vankxr/qo-100-tools/docs/combined_stencil.png

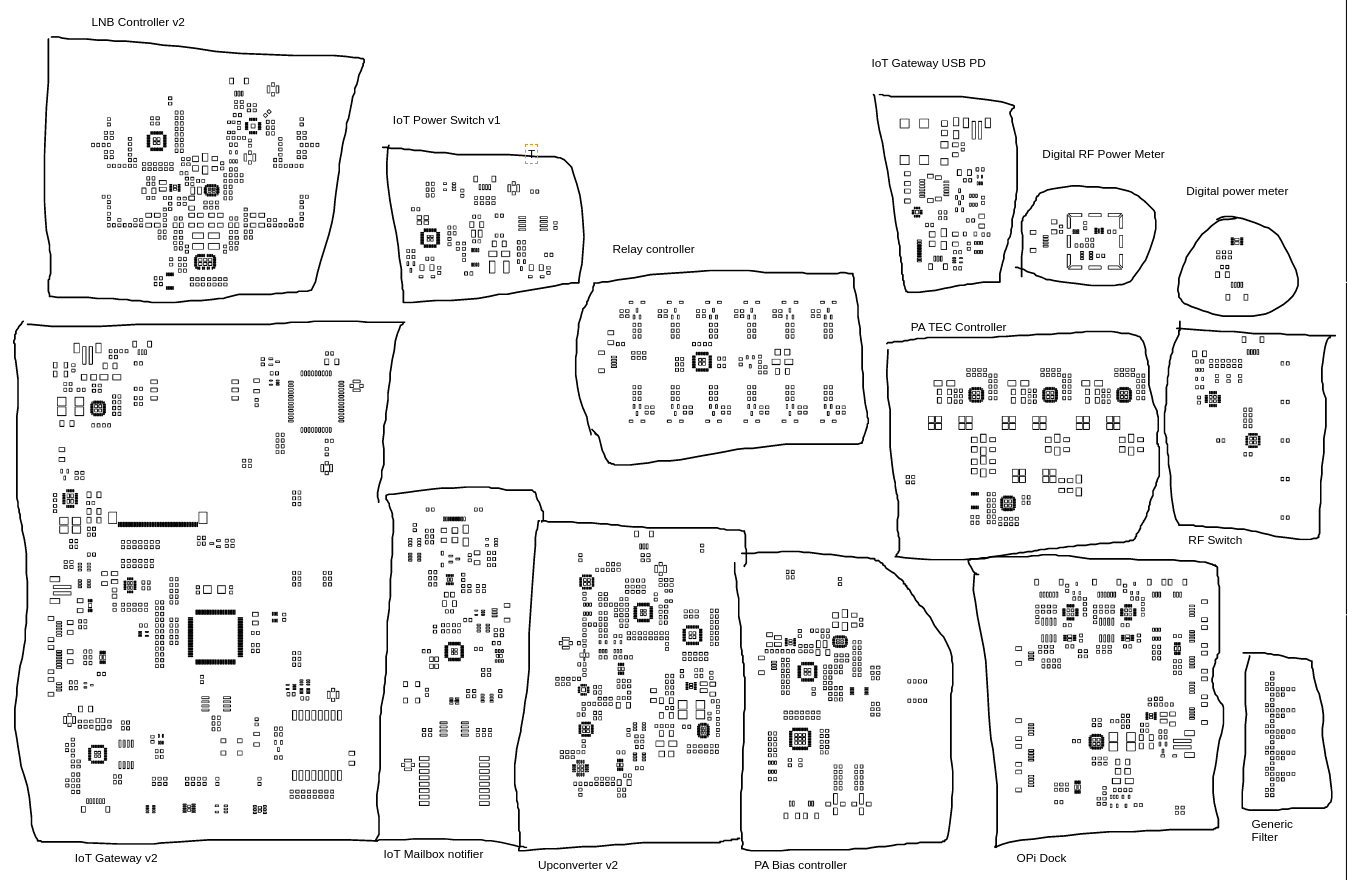
docs/combined_stencil.png
