vankxr/qo-100-tools/docs/directional-couplers/dir_cpl_2.4g_20dB_through.png

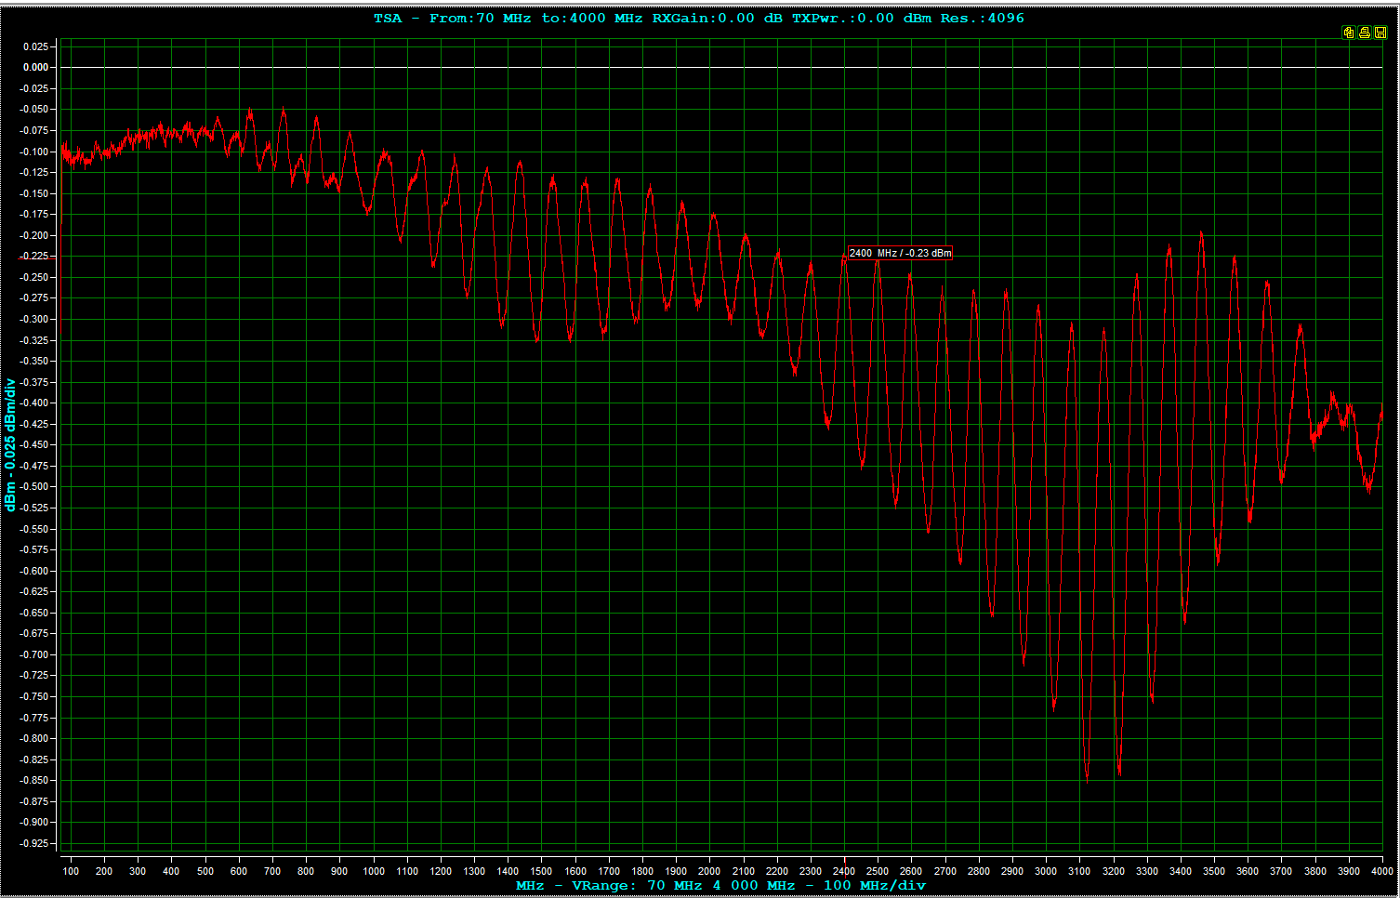
docs/directional-couplers/dir_cpl_2.4g_20dB_through.png
