vankxr/qo-100-tools/docs/directional-couplers/dir_cpl_525m_20dB_coupled.png

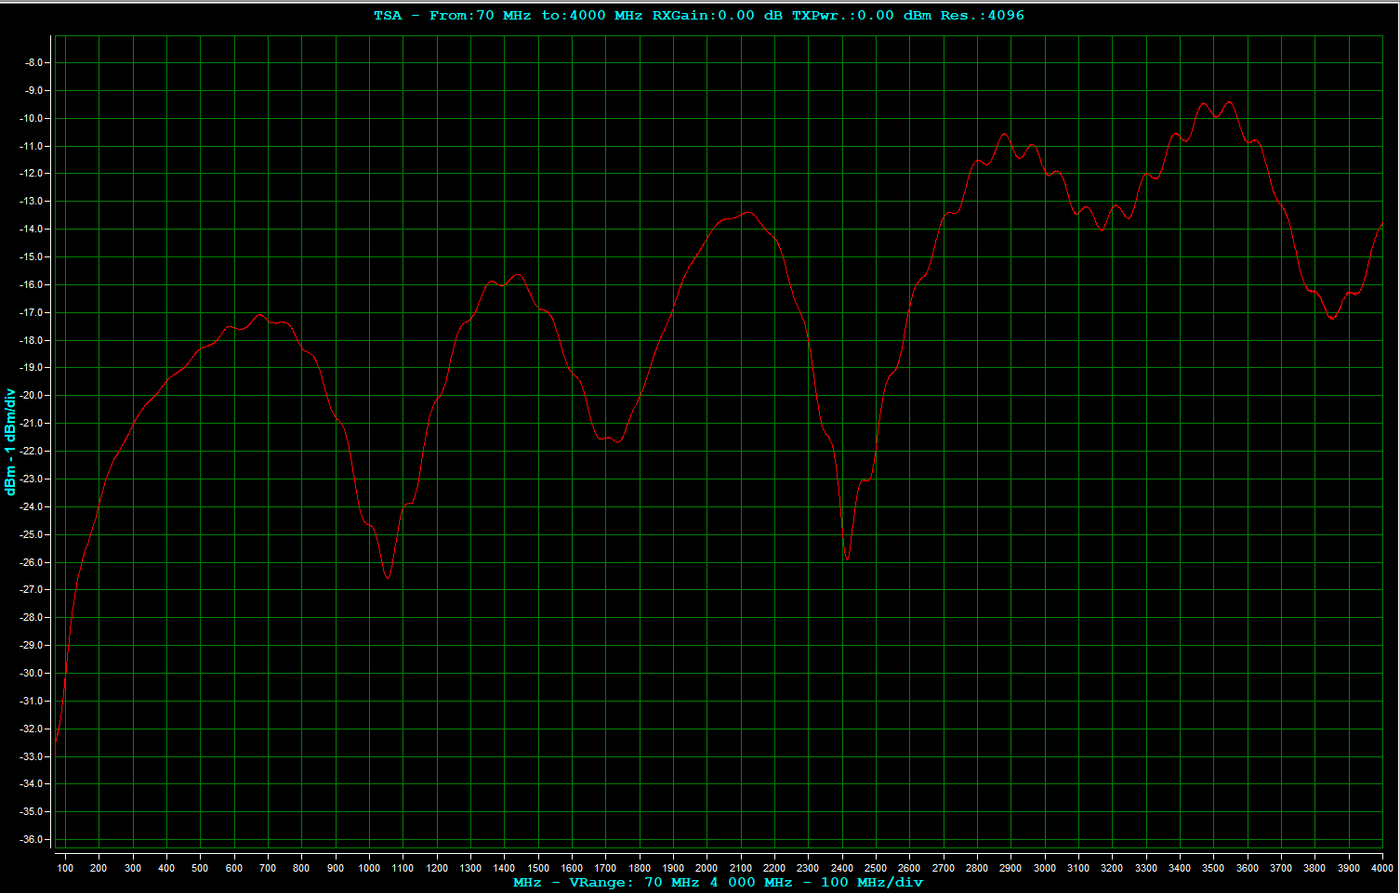
docs/directional-couplers/dir_cpl_525m_20dB_coupled.png
