vankxr/qo-100-tools/docs/f1490_devboard_deembedded.png

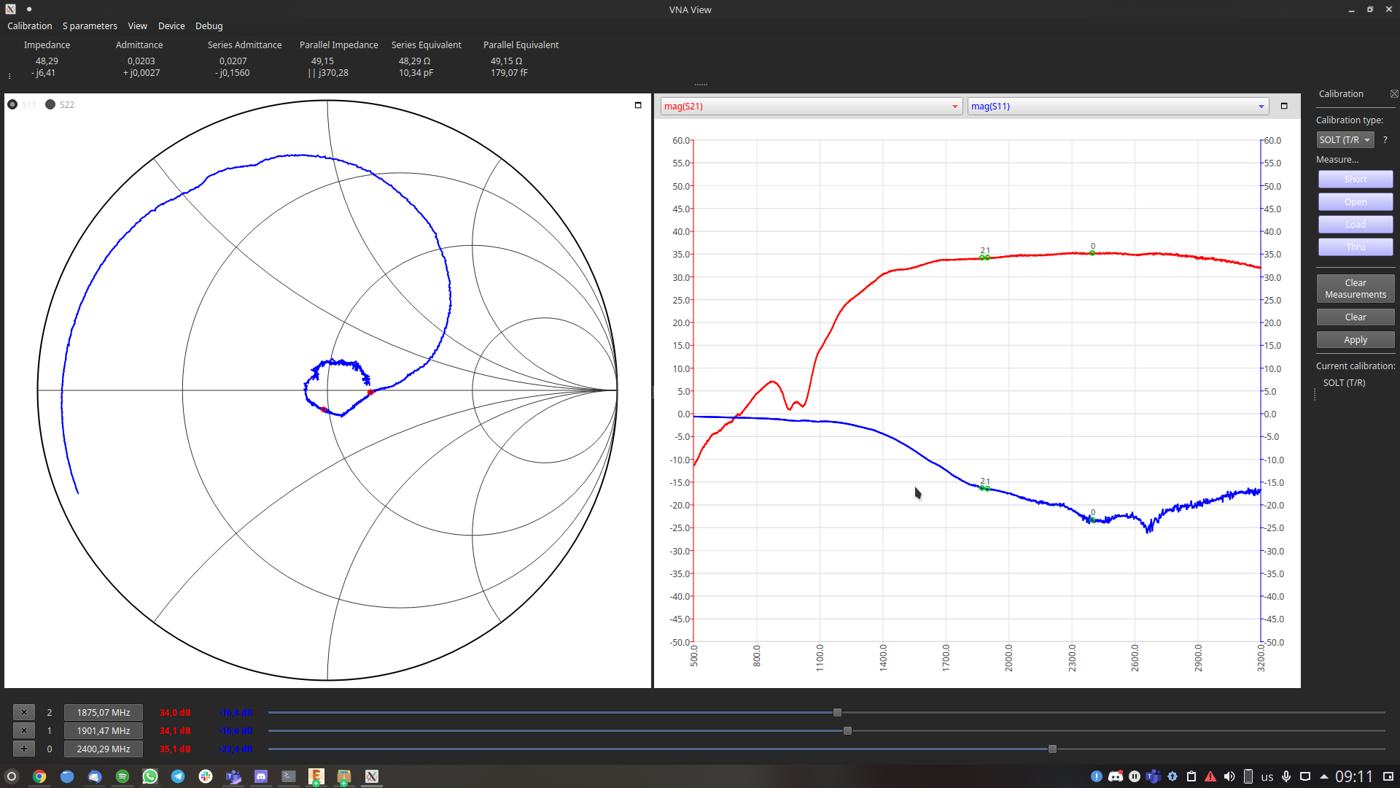
docs/f1490_devboard_deembedded.png
