vankxr/qo-100-tools/docs/ice-cone-antenna/ice_cone_no_cover.png

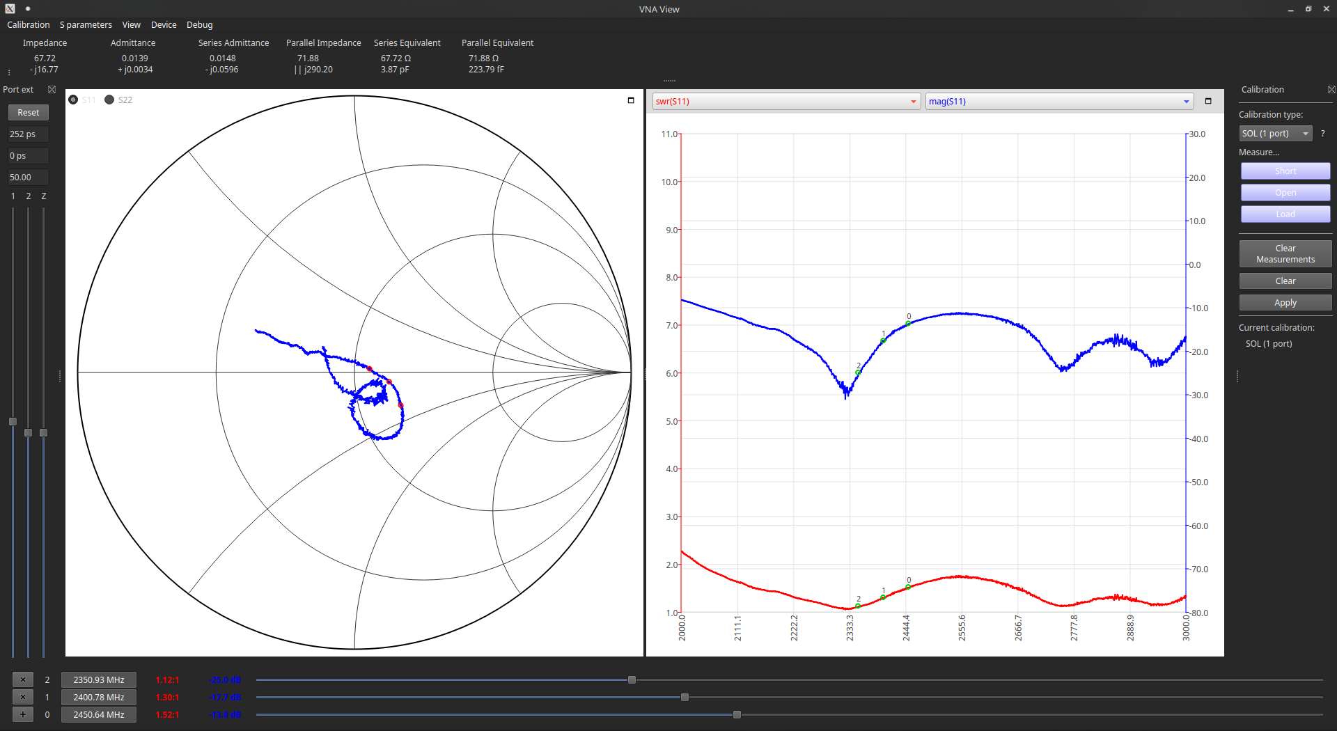
docs/ice-cone-antenna/ice_cone_no_cover.png
