vankxr/qo-100-tools/docs/lnb-controller/lnb-controller-v2-path2-IF-to-RF.png

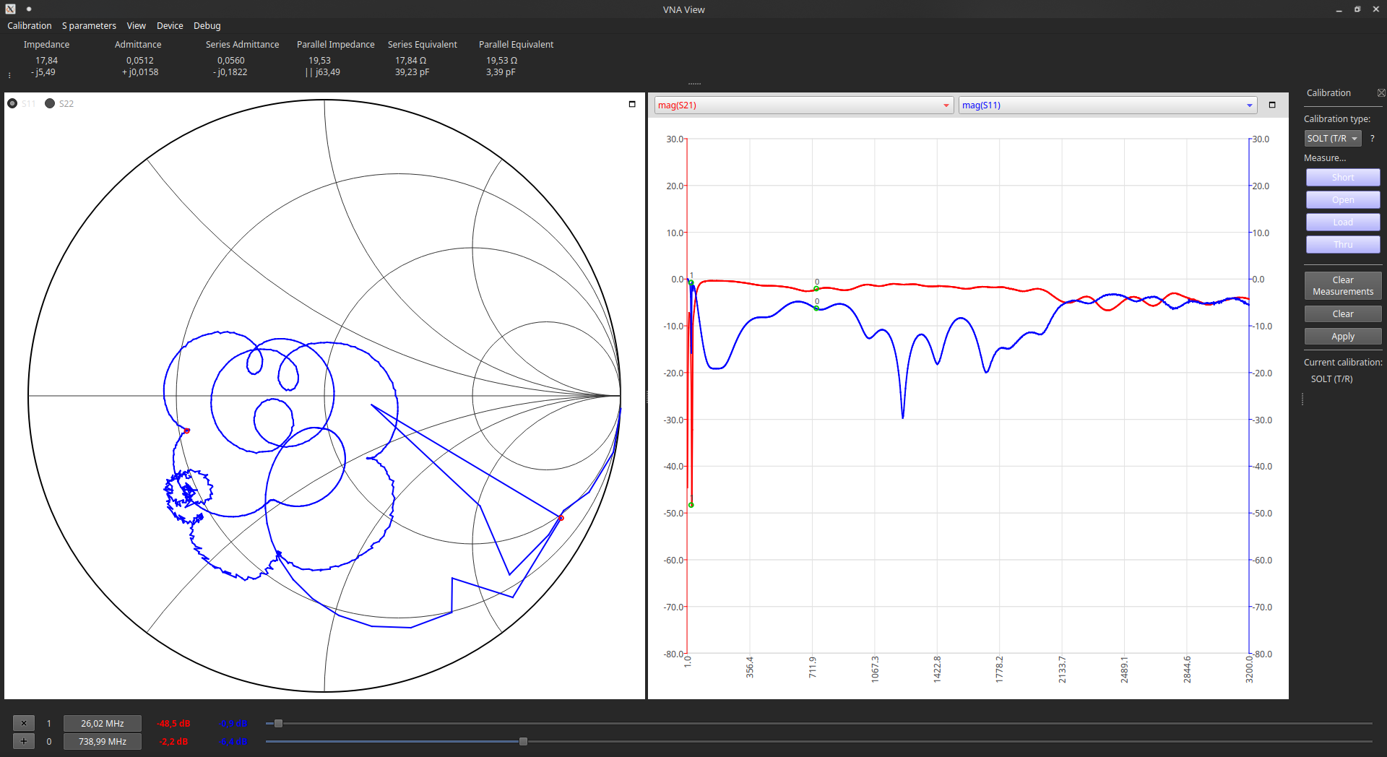
docs/lnb-controller/lnb-controller-v2-path2-IF-to-RF.png
