vankxr/qo-100-tools/docs/pa-driver/pa_20w_2_4g_gain_180mA.png

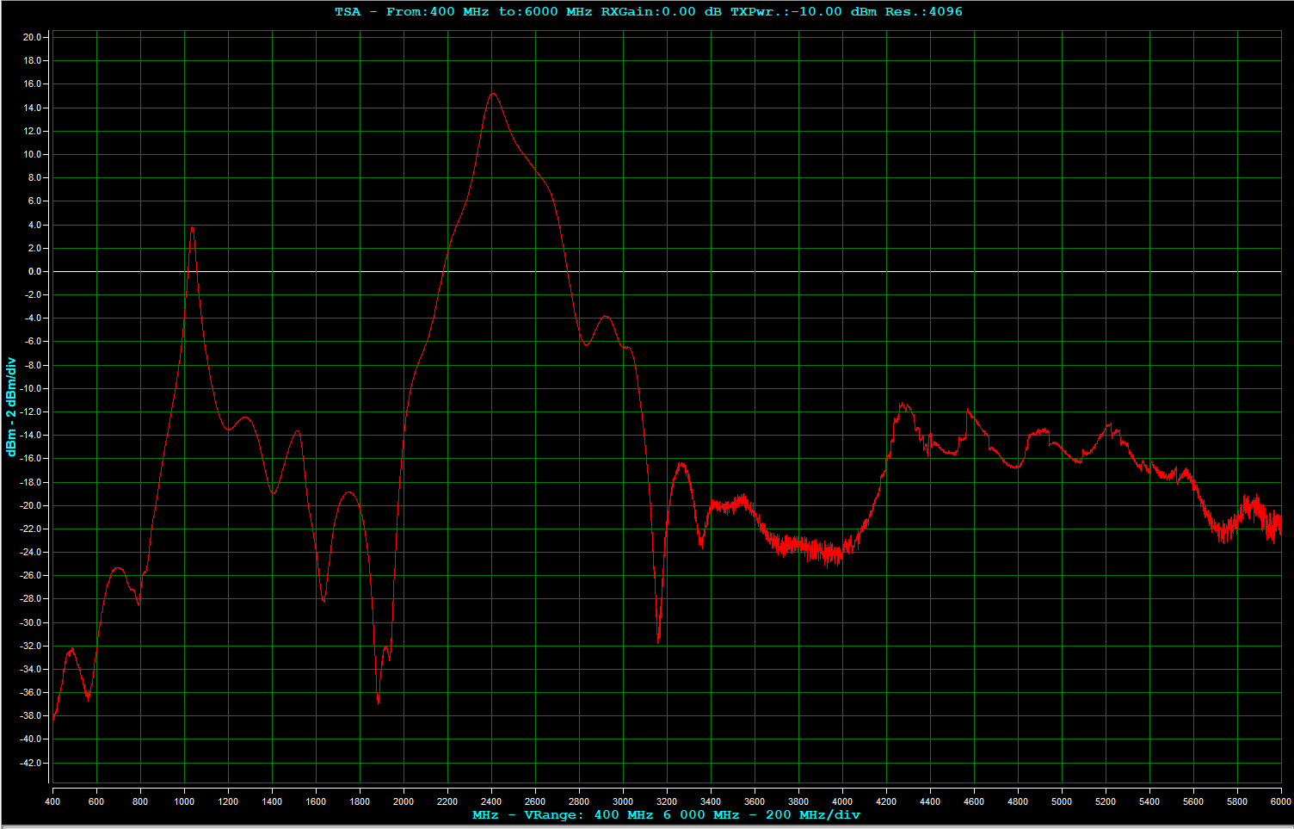
docs/pa-driver/pa_20w_2_4g_gain_180mA.png
