vankxr/qo-100-tools/docs/pa-driver/pa_20W_vdd_0V.png

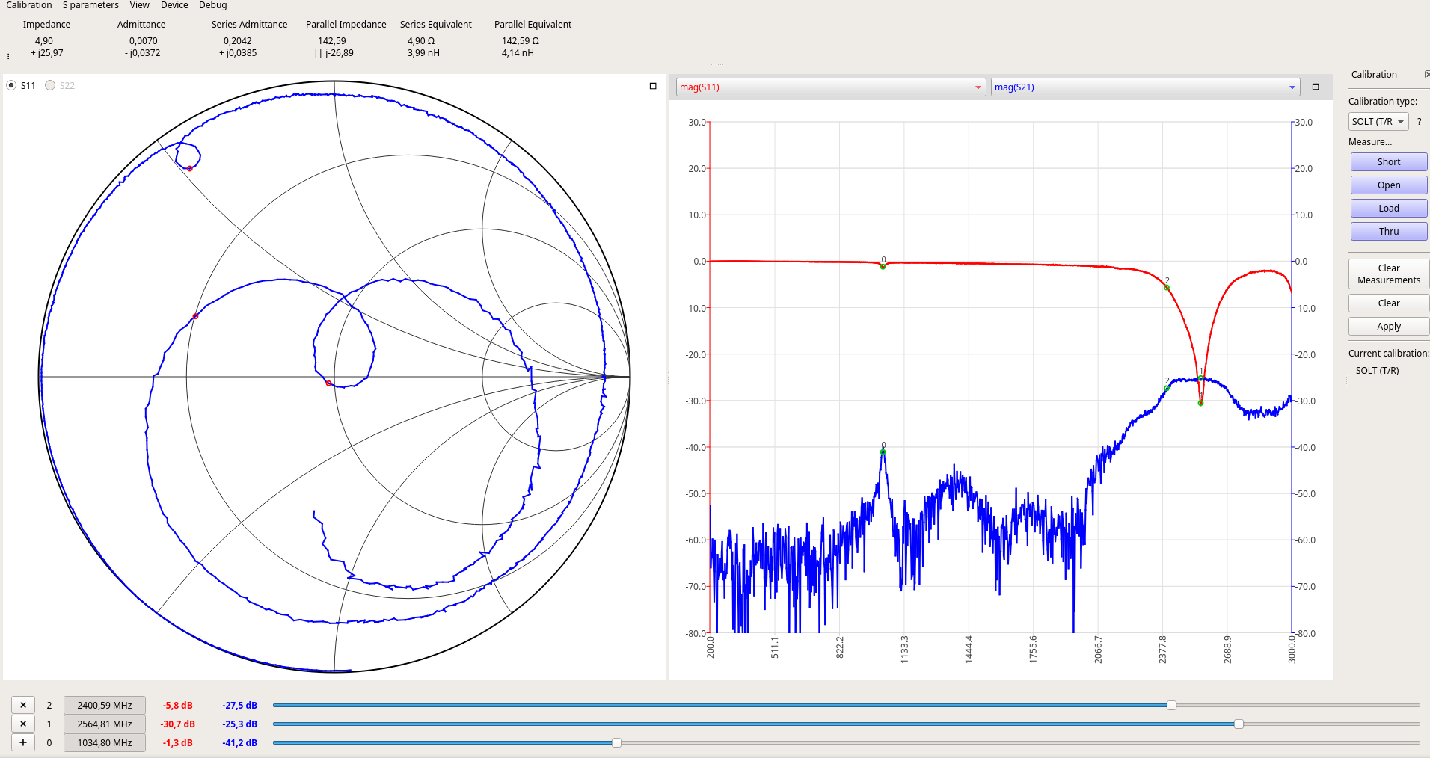
docs/pa-driver/pa_20W_vdd_0V.png
