vankxr/qo-100-tools/docs/pa-driver/pa_20W_vdd_0V_s22.png

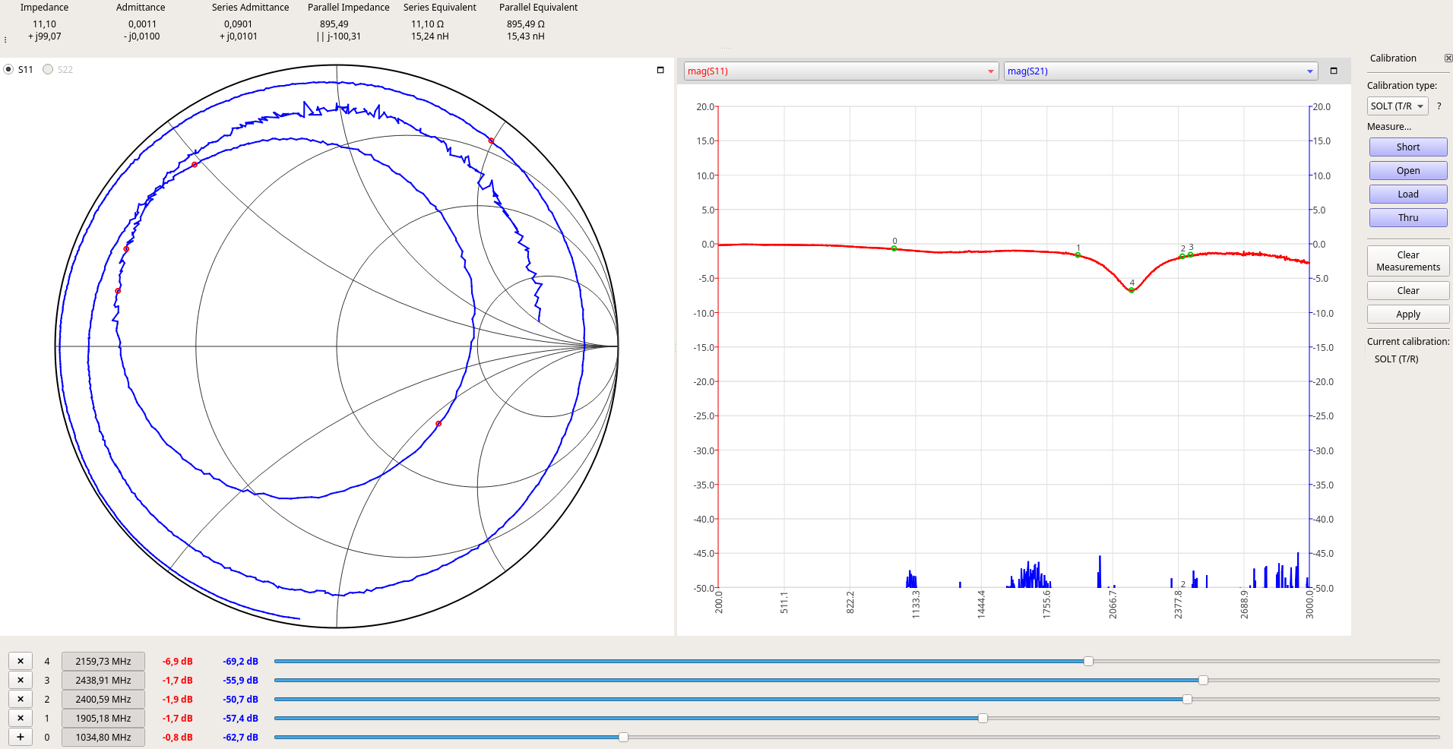
docs/pa-driver/pa_20W_vdd_0V_s22.png
