vankxr/qo-100-tools/docs/pa-driver/pa_20W_vdd_31V_idq_400mA.png

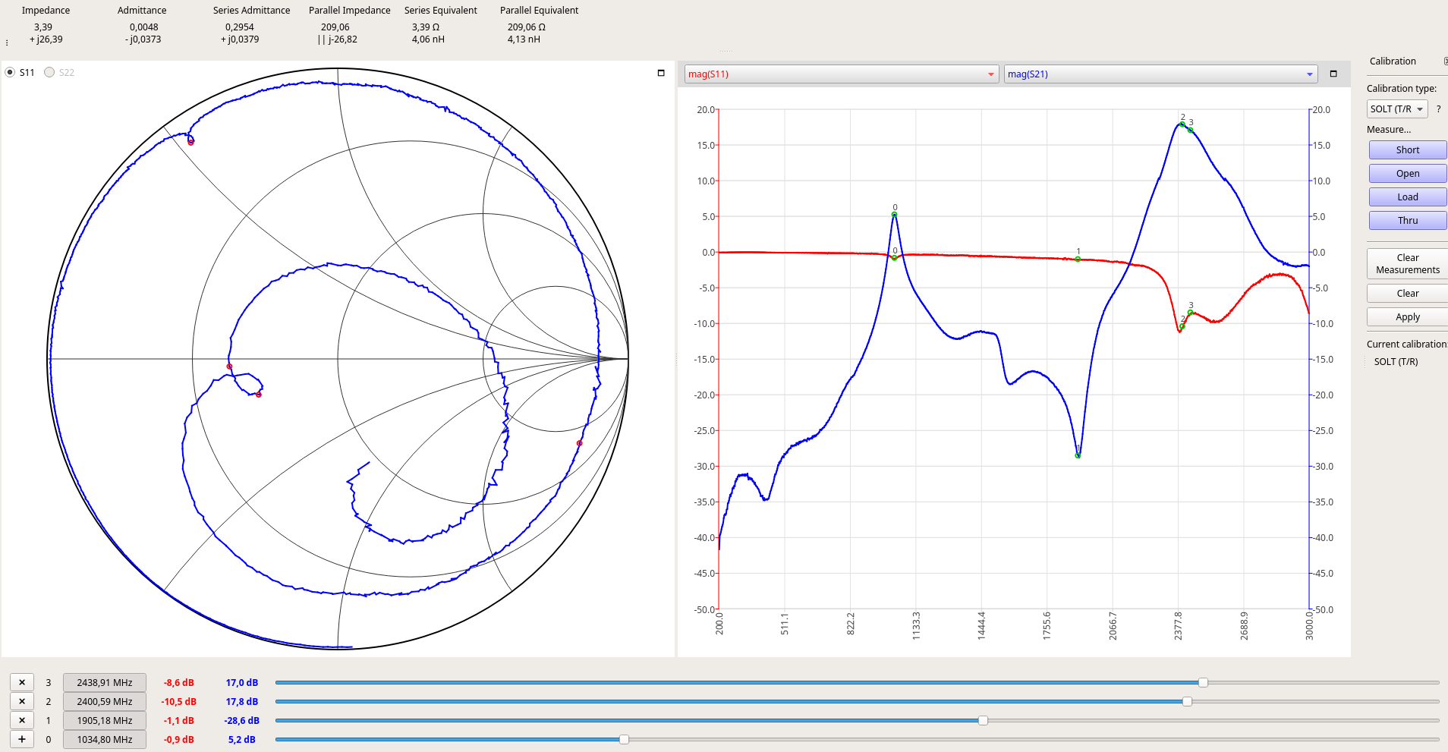
docs/pa-driver/pa_20W_vdd_31V_idq_400mA.png
