vankxr/qo-100-tools/docs/roof-cables/atten_1_3.png

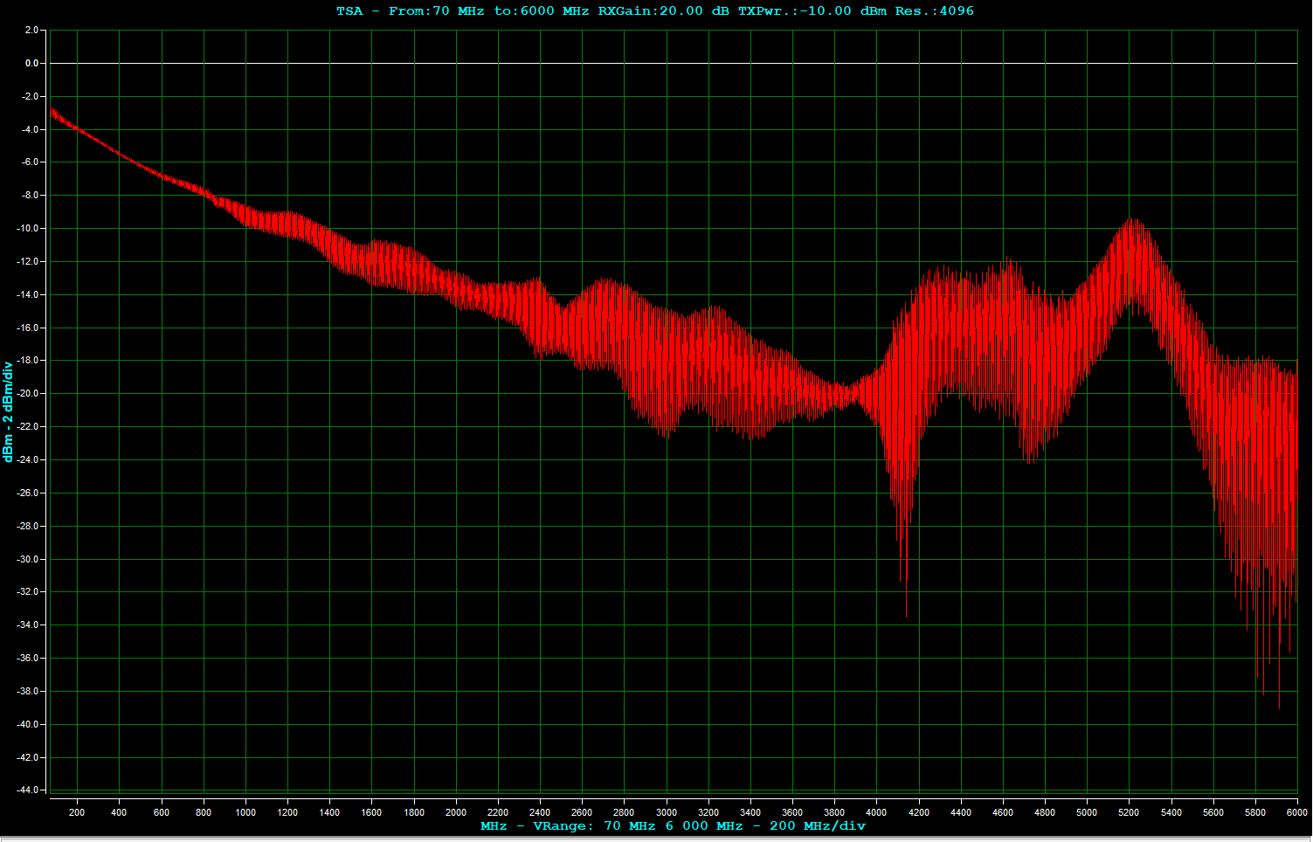
docs/roof-cables/atten_1_3.png
