vankxr/qo-100-tools/docs/roof-cables/atten_1_4.png

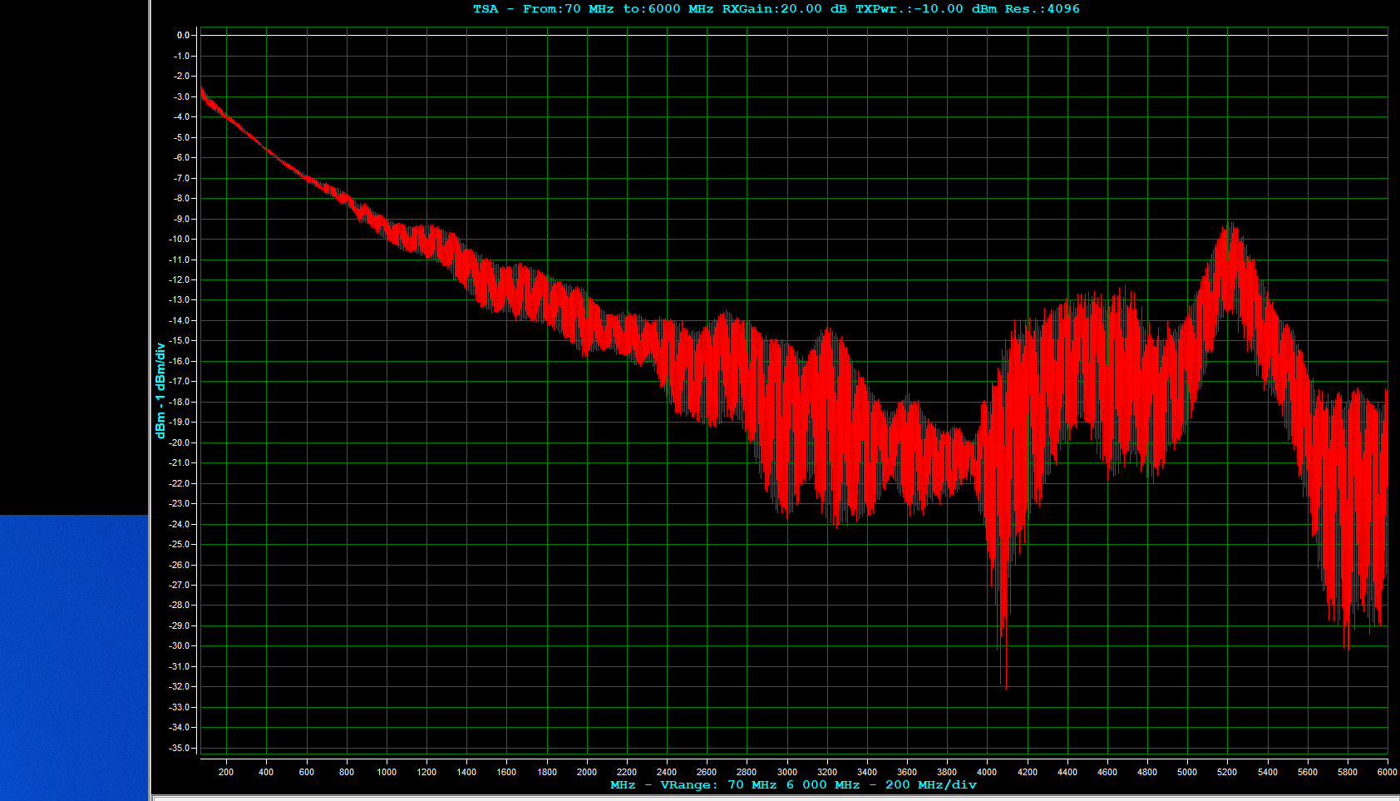
docs/roof-cables/atten_1_4.png
