vankxr/qo-100-tools/docs/upconverter/upconverter-lol-filter.png

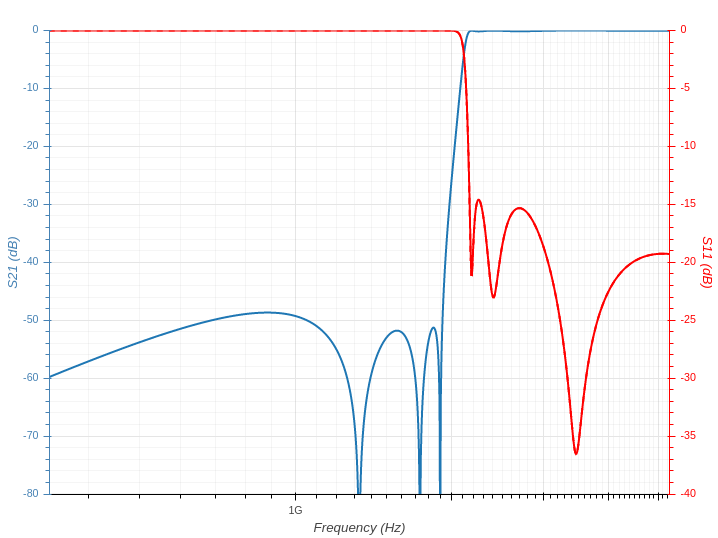
docs/upconverter/upconverter-lol-filter.png
