vankxr/qo-100-tools/docs/upconverter/upconverter_v2_amp.png

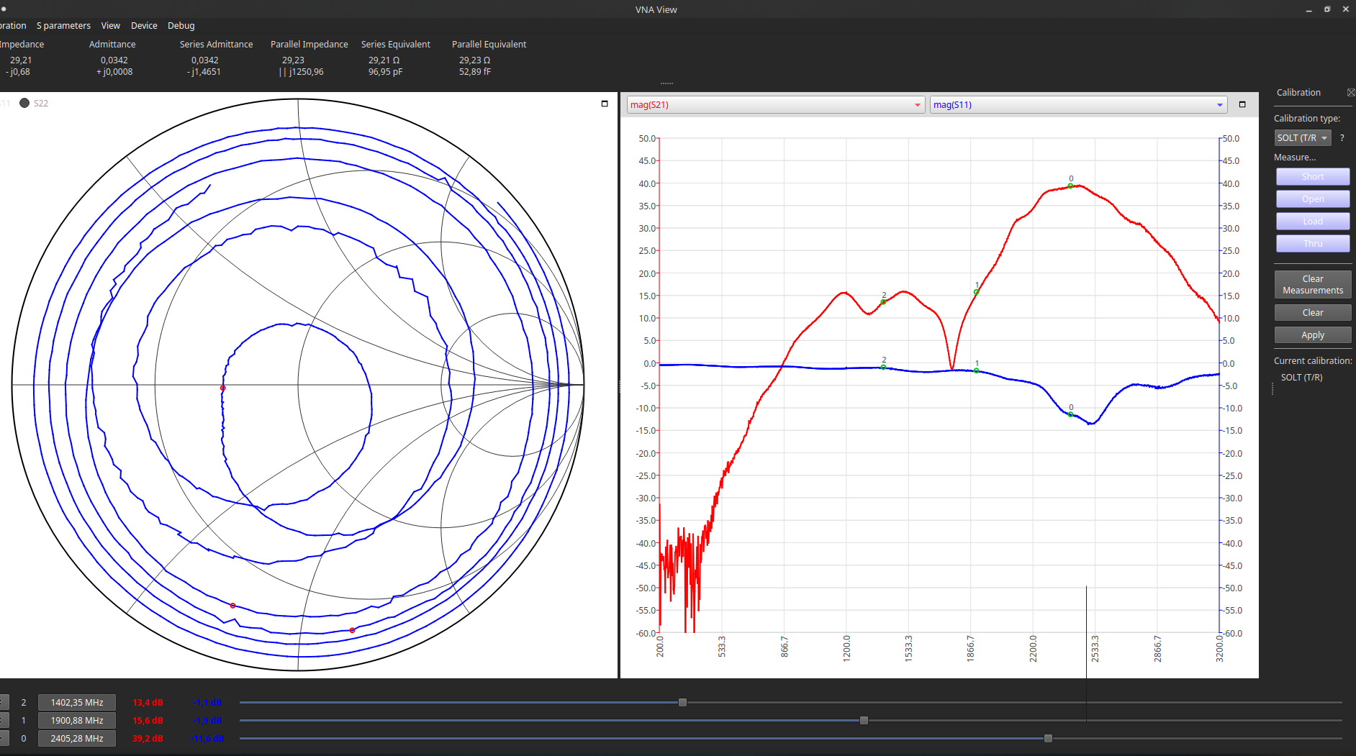
docs/upconverter/upconverter_v2_amp.png
