vankxr/qo-100-tools/docs/upconverter/upconverter_v2_input.png

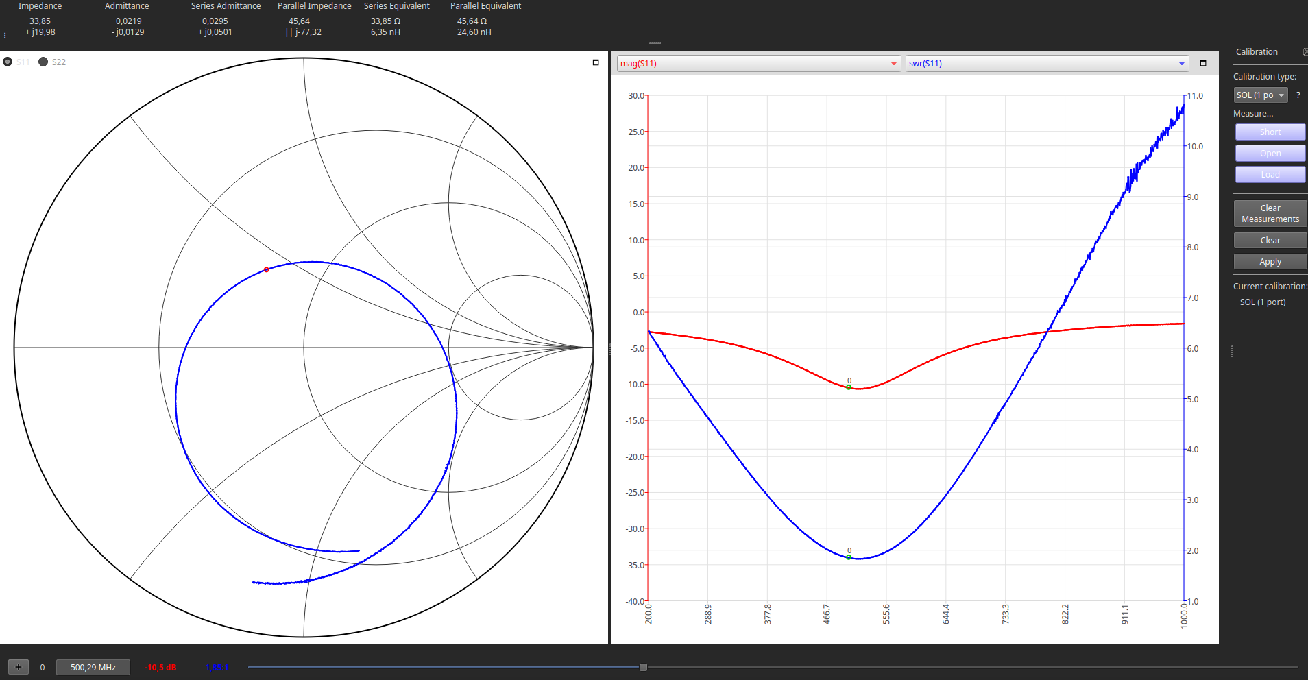
docs/upconverter/upconverter_v2_input.png
