vankxr/qo-100-tools/docs/upconverter/upconverter_v3_amp_stg2_3_32dB_att.png

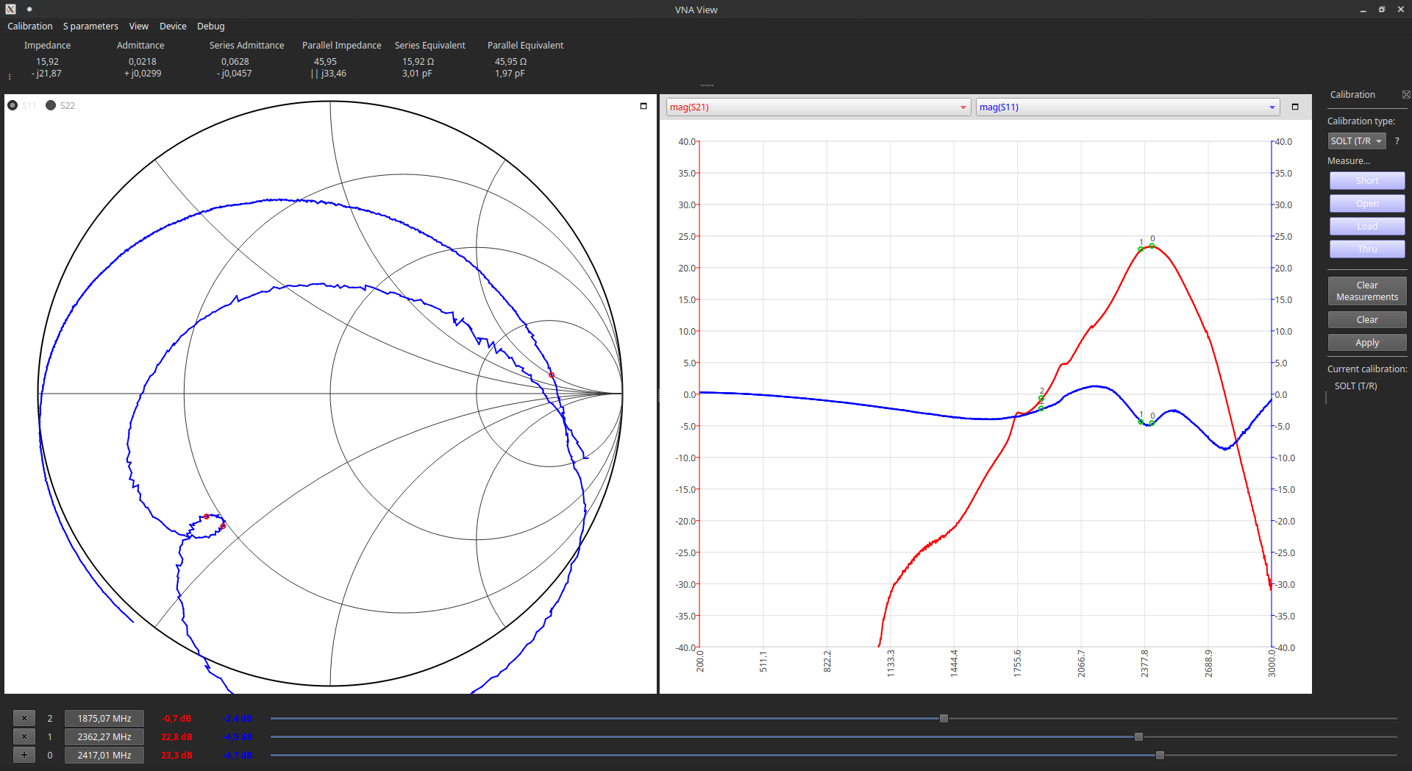
docs/upconverter/upconverter_v3_amp_stg2_3_32dB_att.png
