vankxr/qo-100-tools/docs/upconverter/upconverter_v3_if_attenuator.png

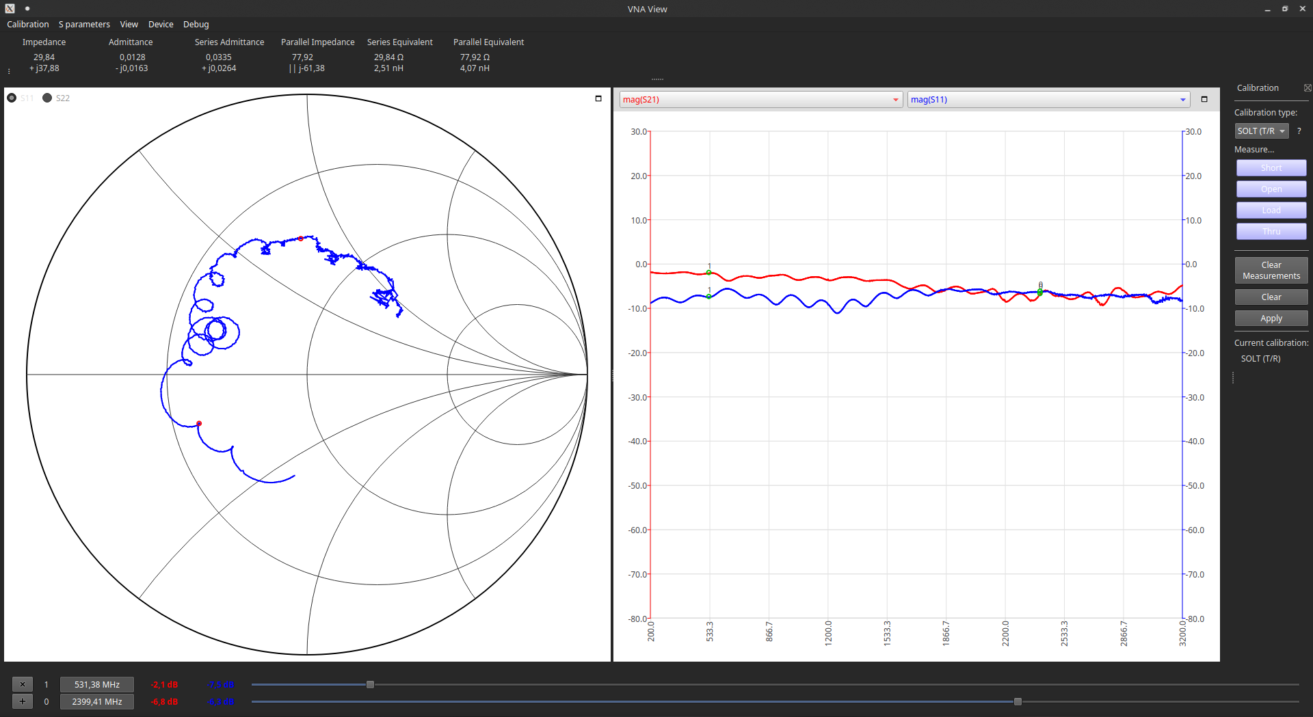
docs/upconverter/upconverter_v3_if_attenuator.png
