vankxr/qo-100-tools/docs/upconverter/upconverter_v3_input.png

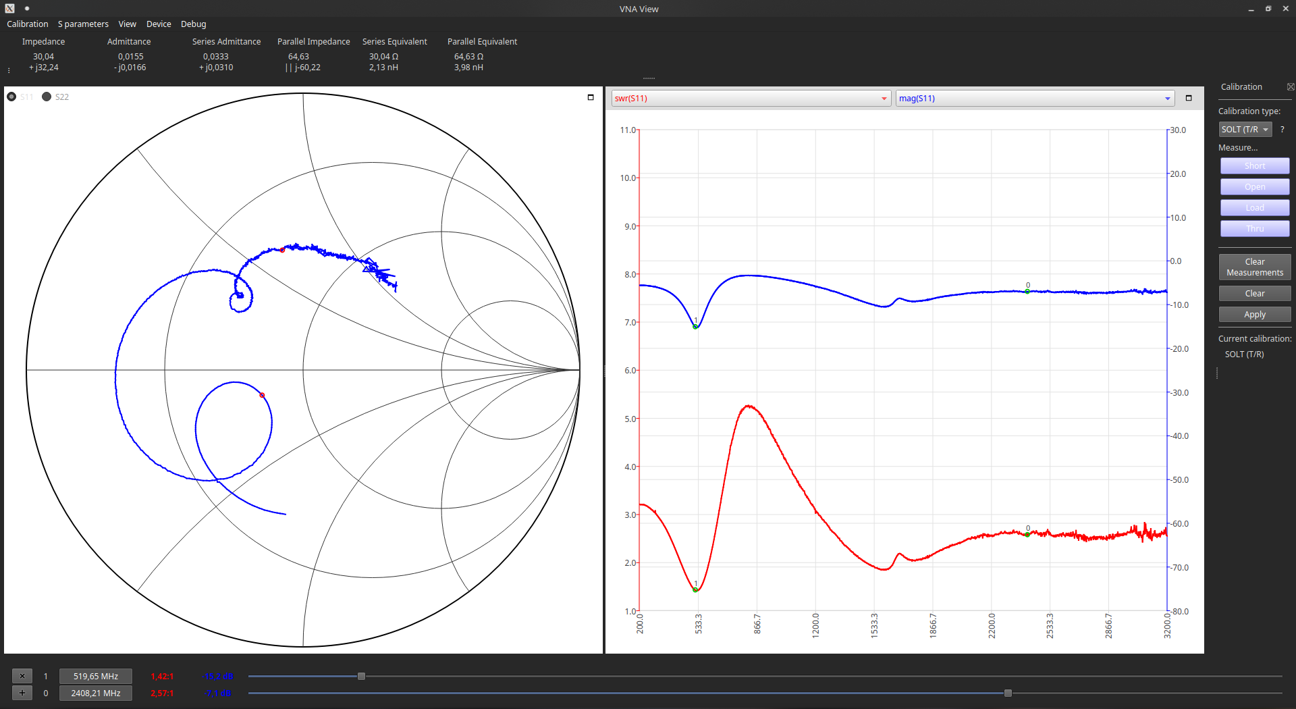
docs/upconverter/upconverter_v3_input.png
