vankxr/qo-100-tools/docs/upconverter/upconverter_v3_lol_filter_amp_stg1_2_3_42dB_att.png

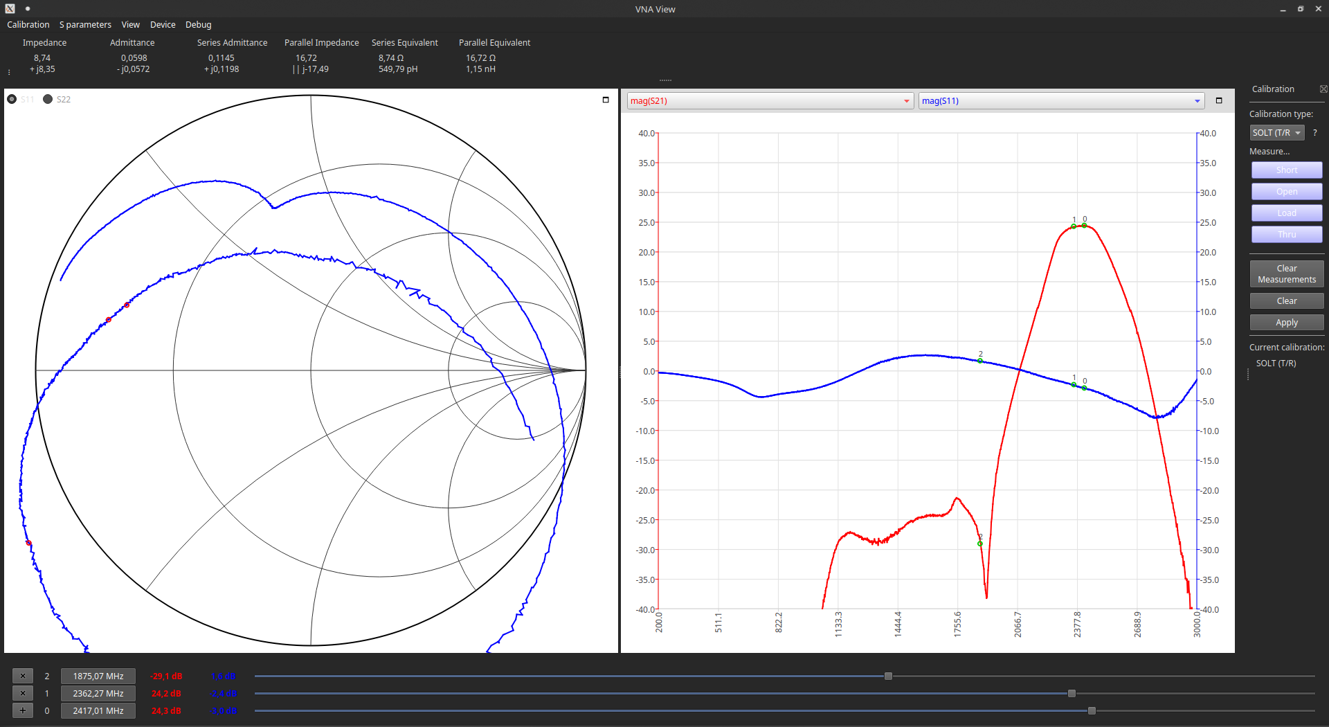
docs/upconverter/upconverter_v3_lol_filter_amp_stg1_2_3_42dB_att.png
