vankxr/qo-100-tools/models/gs/render1.png

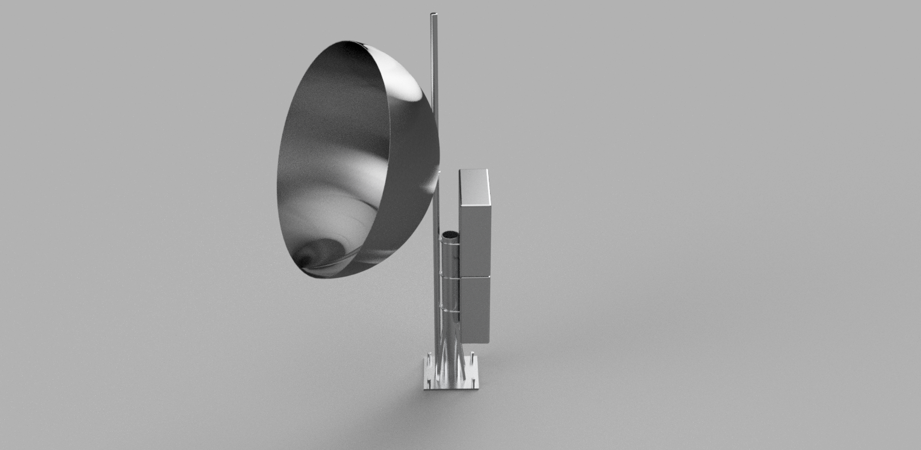
models/gs/render1.png
