vankxr/qo-100-tools/models/gs/render2.png

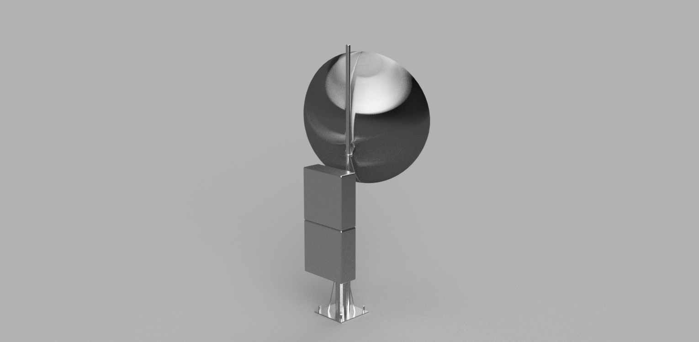
models/gs/render2.png
