vankxr/qo-100-tools/models/gs/render3.png

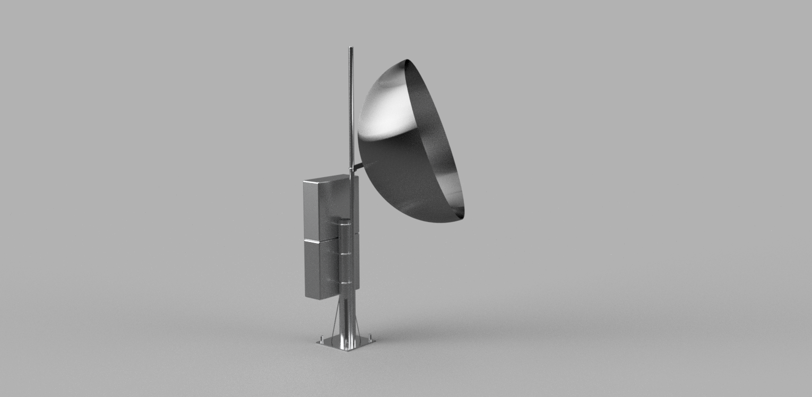
models/gs/render3.png
