vankxr/qo-100-tools/models/gs/render4.png

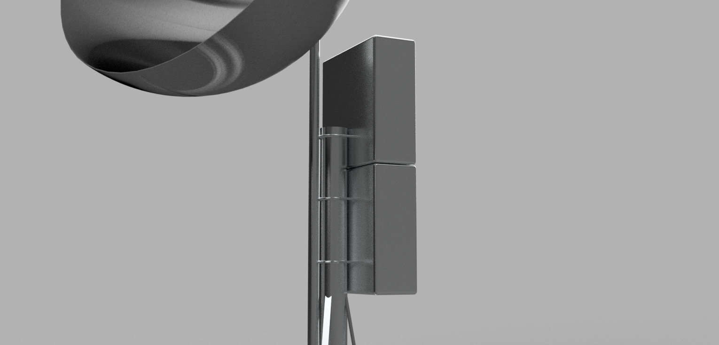
models/gs/render4.png
