vankxr/qo-100-tools/models/gs/render5.png

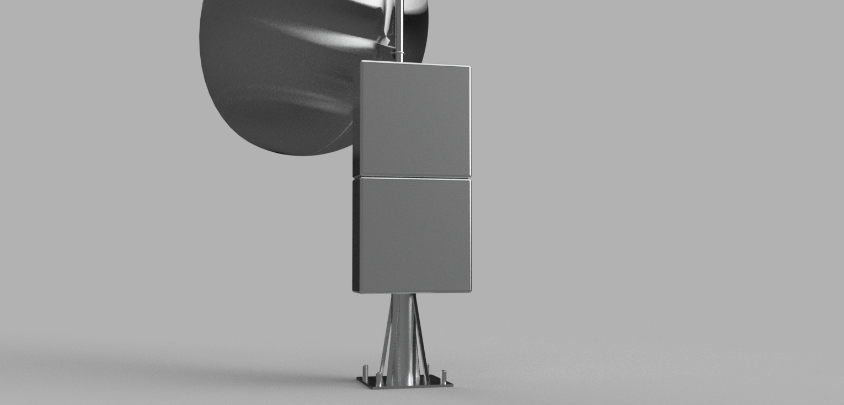
models/gs/render5.png
