vankxr/qo-100-tools/models/pa-case/render1.png

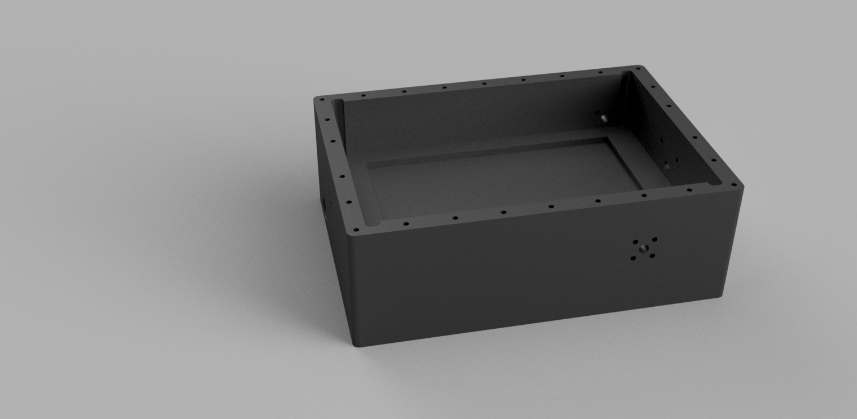
models/pa-case/render1.png
