vankxr/qo-100-tools/models/pa-case/render2.png

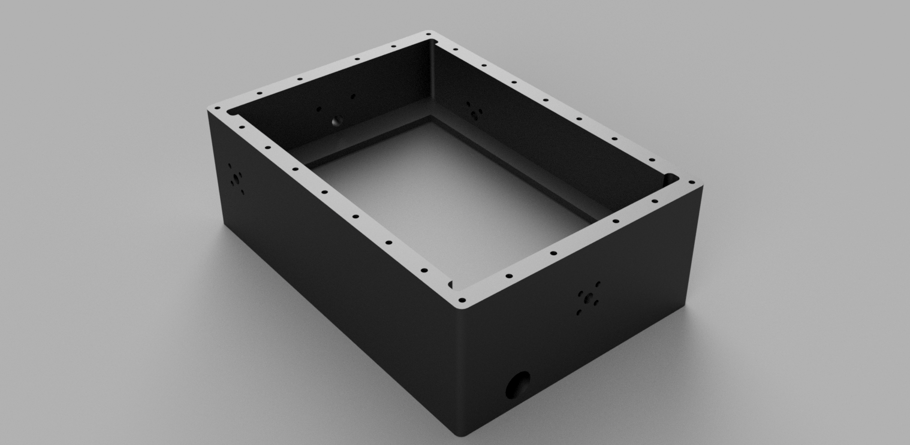
models/pa-case/render2.png
