vankxr/qo-100-tools/models/pa-case/render3.png

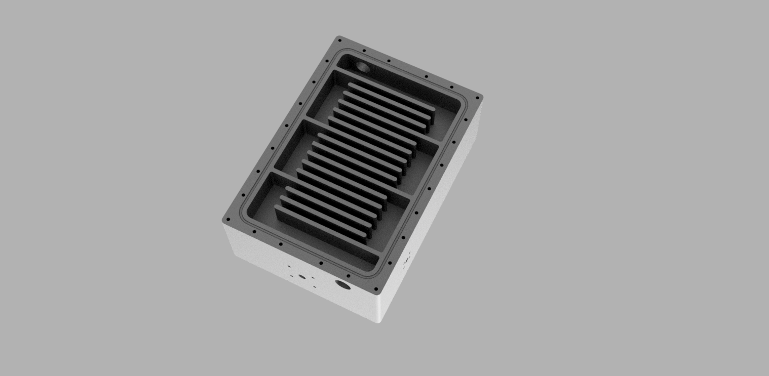
models/pa-case/render3.png
