vankxr/qo-100-tools/pcb/digital-power-meter/qo-100-digital-power-meter-top.png

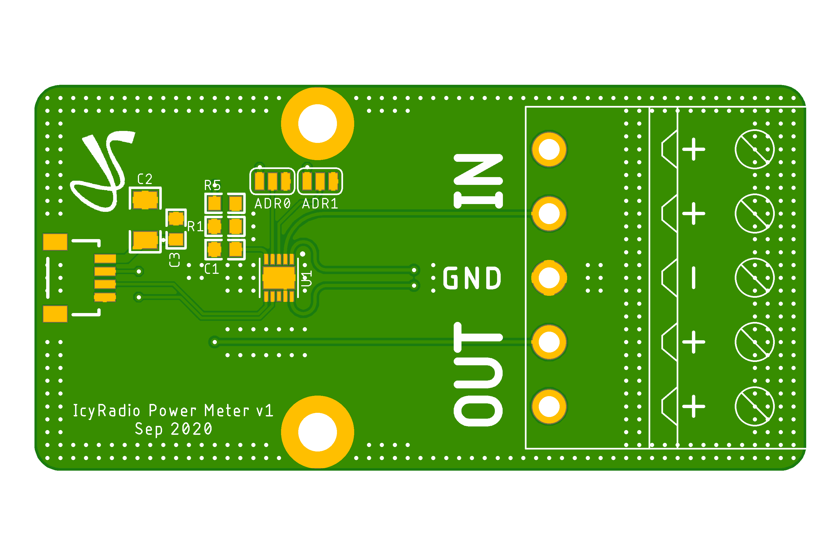
pcb/digital-power-meter/qo-100-digital-power-meter-top.png
