vankxr/qo-100-tools/pcb/env-sensors/qo-100-env-sensors-bot.png

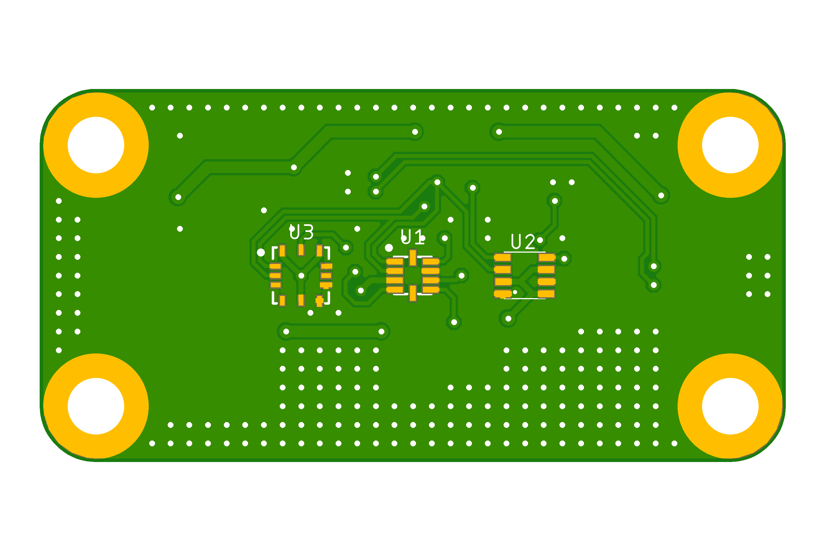
pcb/env-sensors/qo-100-env-sensors-bot.png
