vankxr/qo-100-tools/pcb/env-sensors/qo-100-env-sensors-top.png

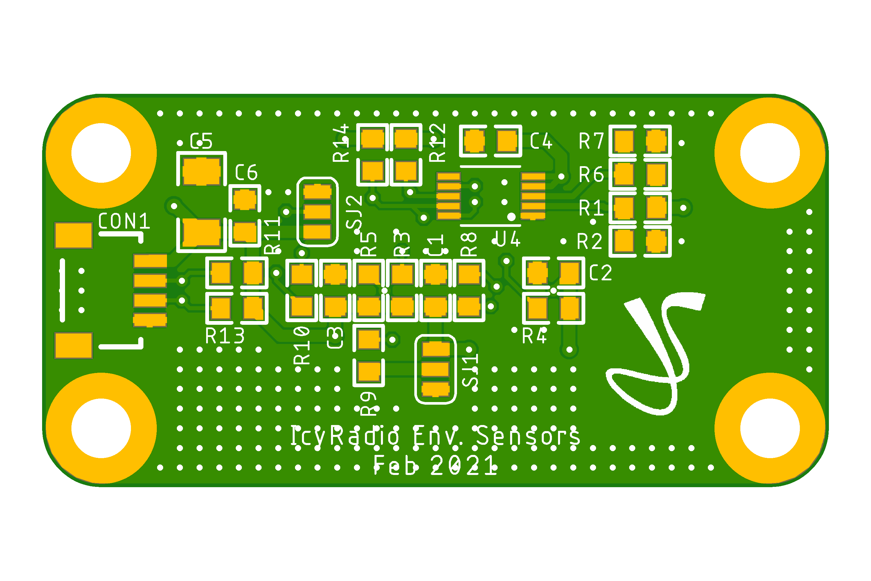
pcb/env-sensors/qo-100-env-sensors-top.png
