vankxr/qo-100-tools/pcb/generic-filter/qo-100-generic-filter-bot.png

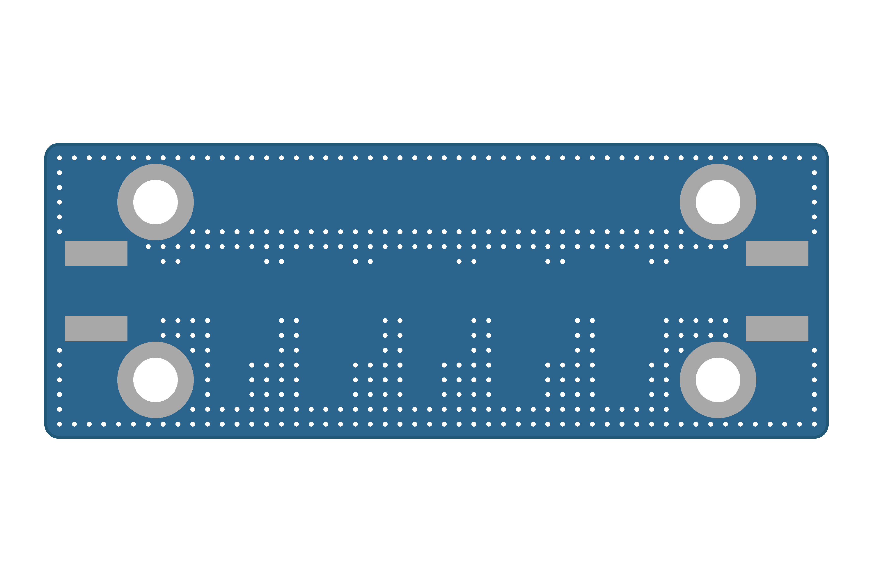
pcb/generic-filter/qo-100-generic-filter-bot.png
