vankxr/qo-100-tools/pcb/gpsdo/qo-100-gpsdo-bot.png

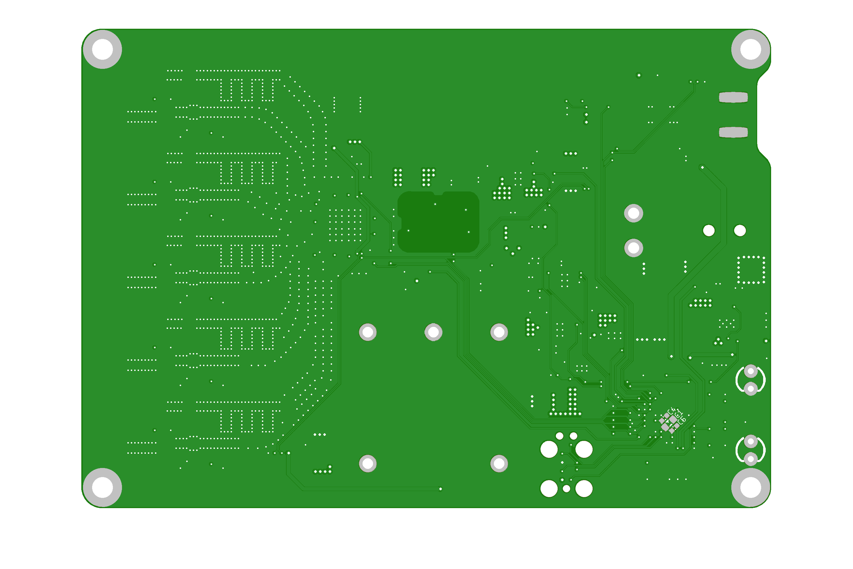
pcb/gpsdo/qo-100-gpsdo-bot.png
