vankxr/qo-100-tools/pcb/gpsdo/qo-100-gpsdo-top.png

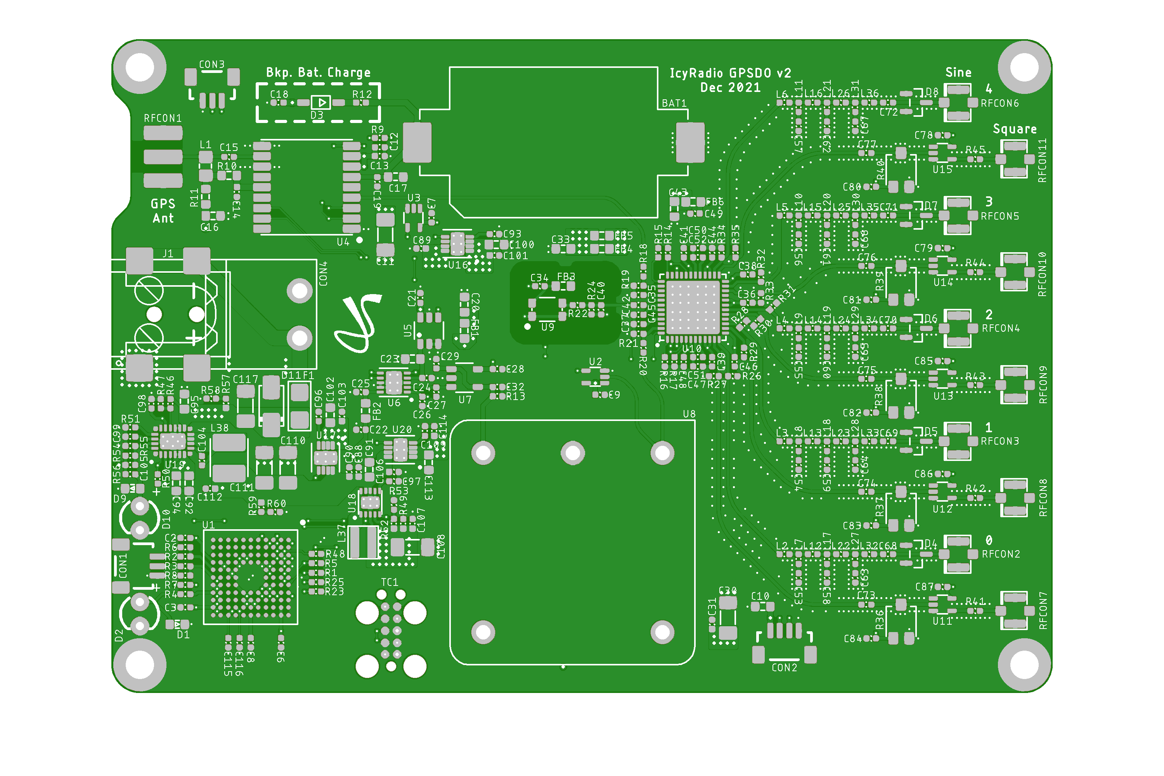
pcb/gpsdo/qo-100-gpsdo-top.png
