vankxr/qo-100-tools/pcb/i2c-buffer/qo-100-i2c-buffer-top.png

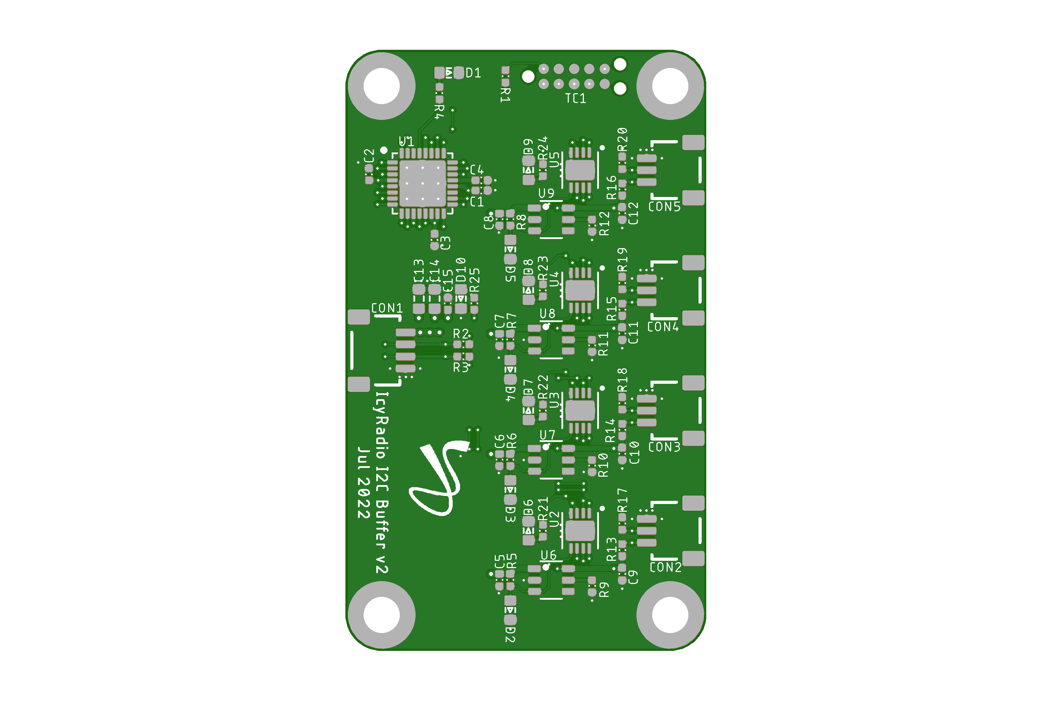
pcb/i2c-buffer/qo-100-i2c-buffer-top.png
