vankxr/qo-100-tools/pcb/lnb-controller/qo-100-lnb-controller-bot.png

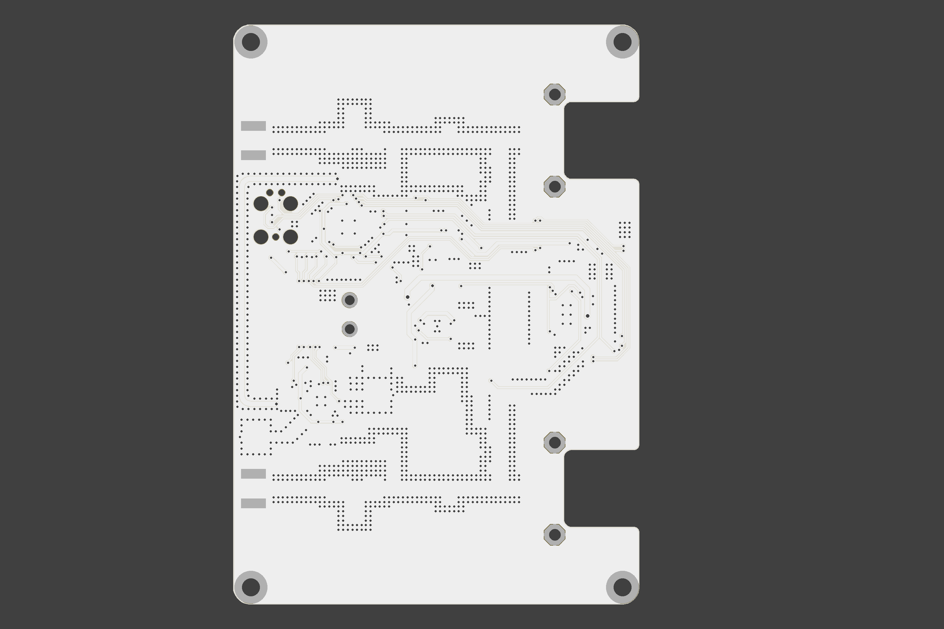
pcb/lnb-controller/qo-100-lnb-controller-bot.png
