vankxr/qo-100-tools/pcb/lora-transceiver/qo-100-lora-transceiver-bot.png

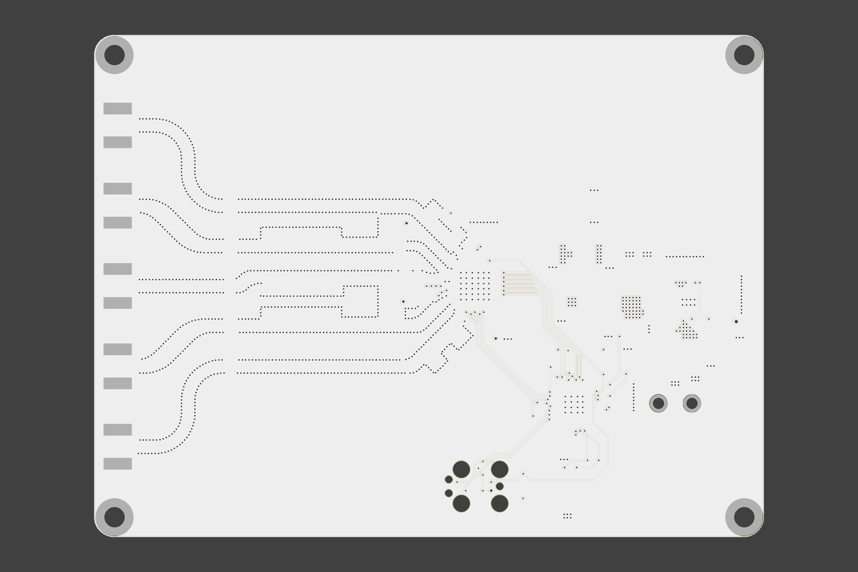
pcb/lora-transceiver/qo-100-lora-transceiver-bot.png
