vankxr/qo-100-tools/pcb/lora-transceiver/qo-100-lora-transceiver-top.png

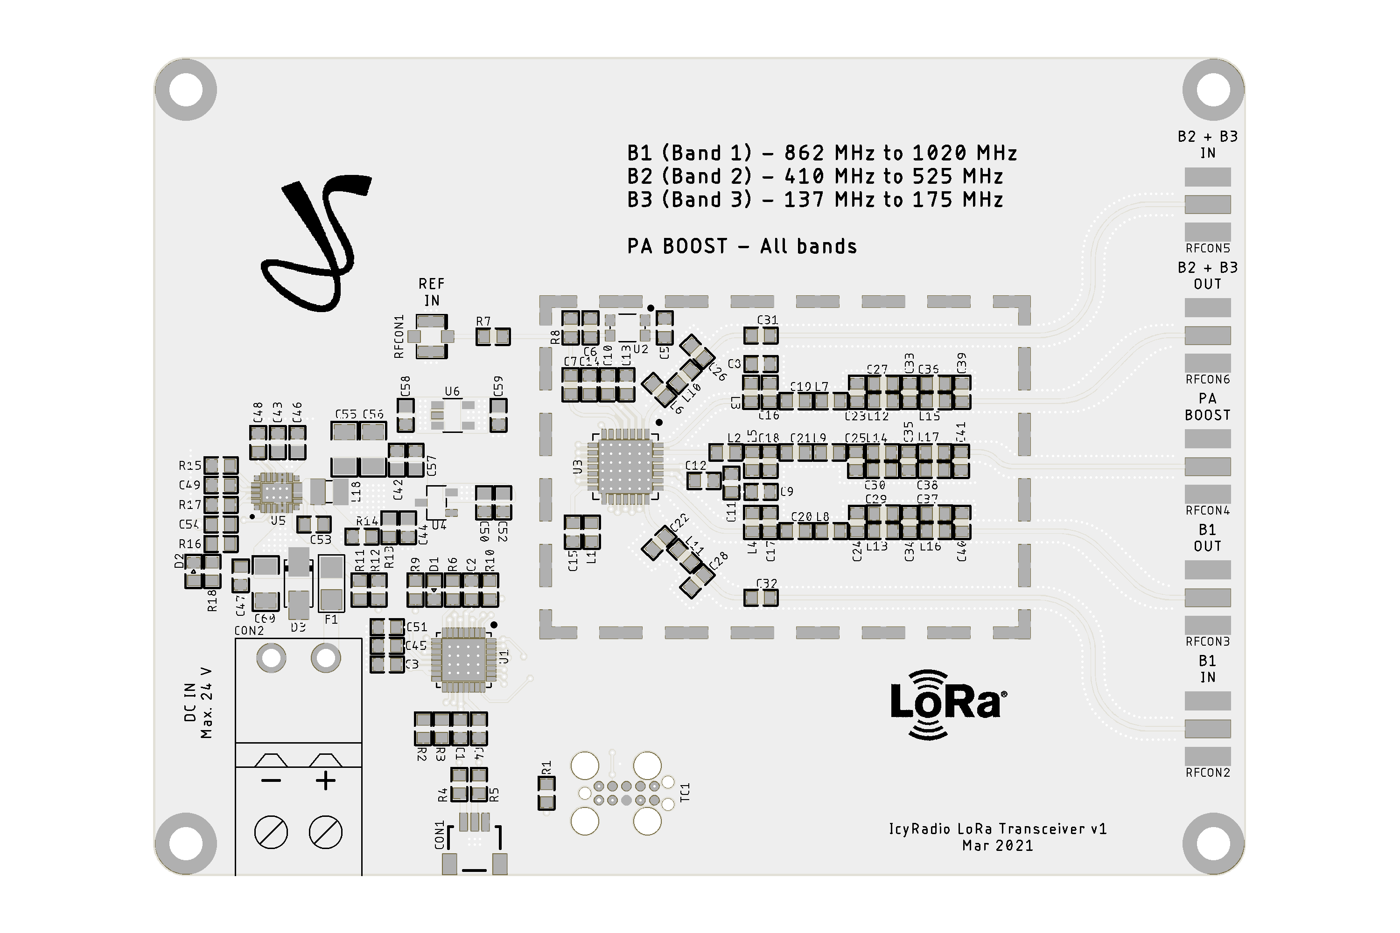
pcb/lora-transceiver/qo-100-lora-transceiver-top.png
