vankxr/qo-100-tools/pcb/opi-dock/qo-100-opi-dock-bot.png

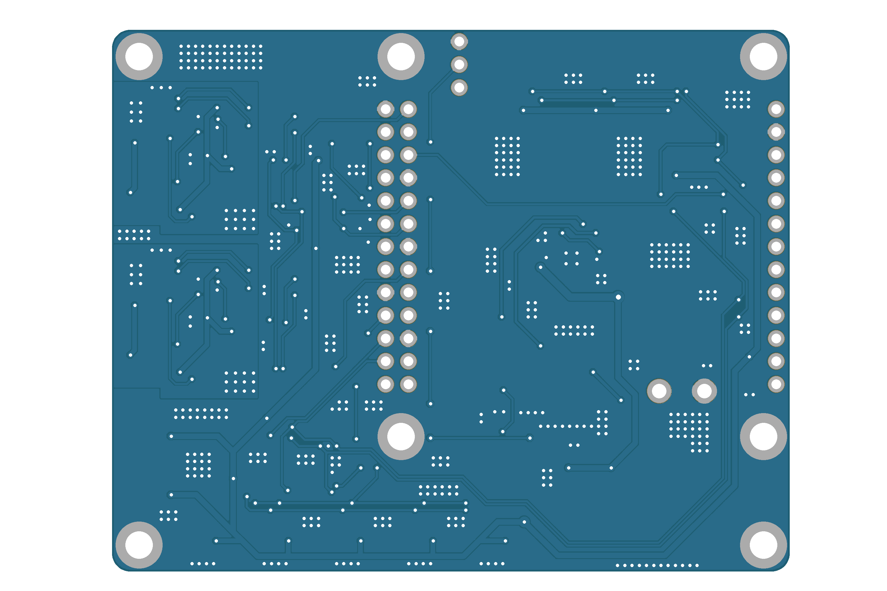
pcb/opi-dock/qo-100-opi-dock-bot.png
