vankxr/qo-100-tools/pcb/pa-bias-controller/qo-100-pa-bias-controller-bot.png

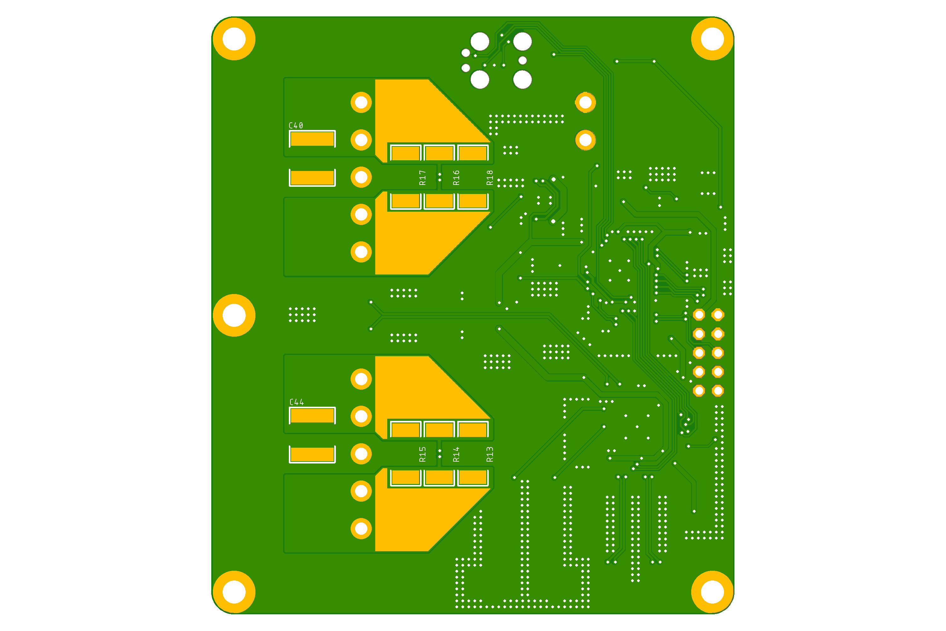
pcb/pa-bias-controller/qo-100-pa-bias-controller-bot.png
