vankxr/qo-100-tools/pcb/pa-driver/qo-100-pa-driver-bot.png

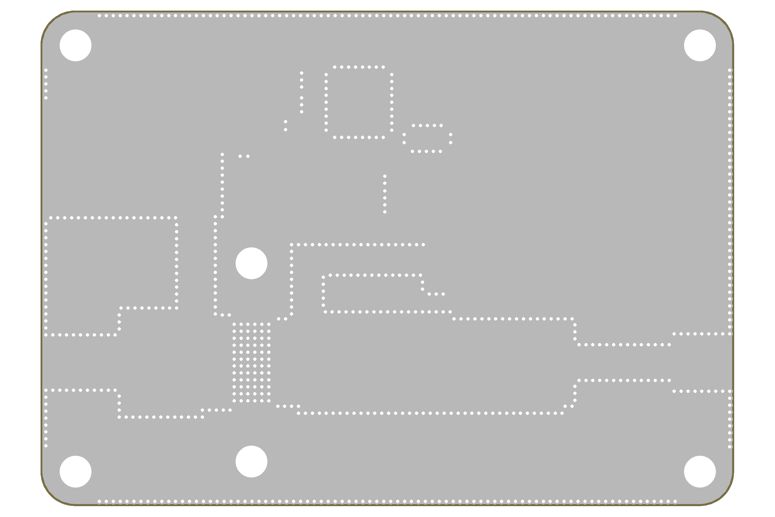
pcb/pa-driver/qo-100-pa-driver-bot.png
