vankxr/qo-100-tools/pcb/pa-driver/qo-100-pa-driver-top.png

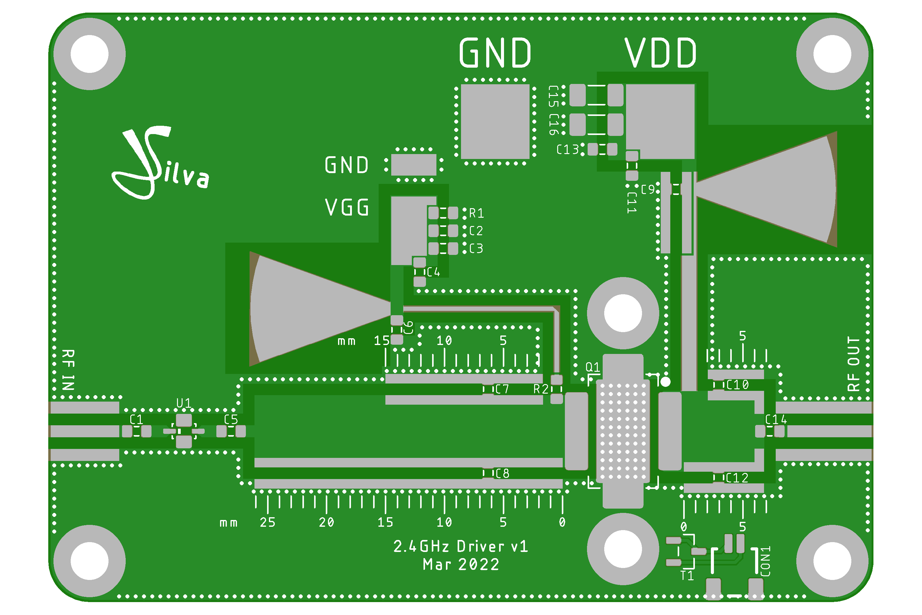
pcb/pa-driver/qo-100-pa-driver-top.png
