vankxr/qo-100-tools/pcb/pa-tec-controller/qo-100-pa-tec-controller-bot.png

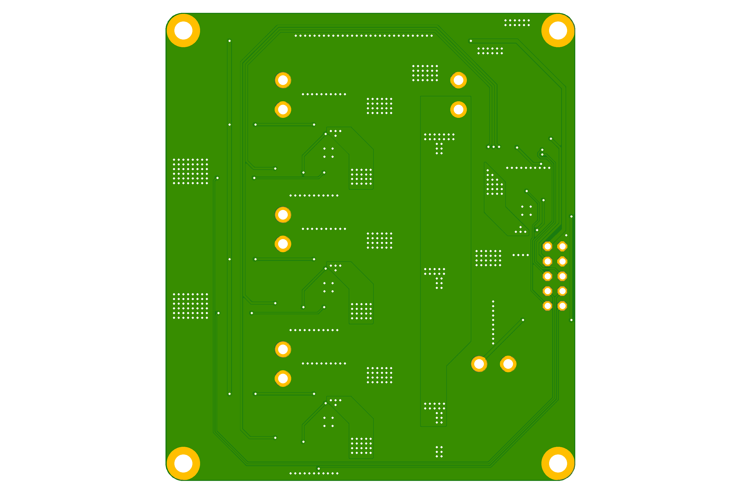
pcb/pa-tec-controller/qo-100-pa-tec-controller-bot.png
