vankxr/qo-100-tools/pcb/pa-tec-controller/qo-100-pa-tec-controller-top.png

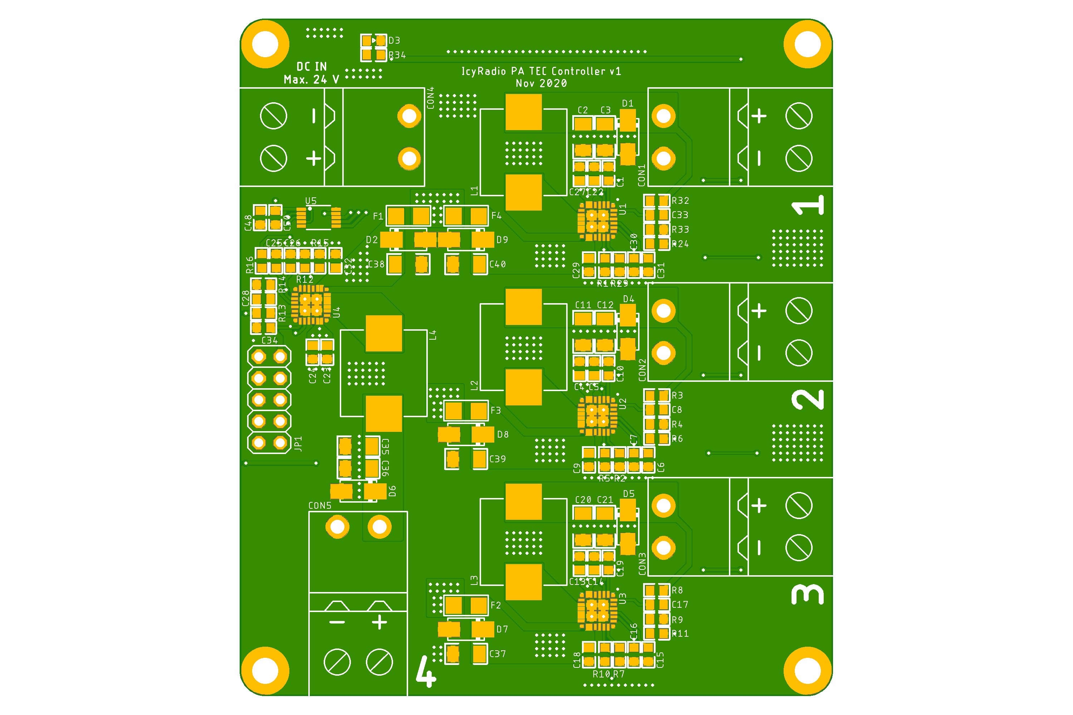
pcb/pa-tec-controller/qo-100-pa-tec-controller-top.png
