vankxr/qo-100-tools/pcb/psu-interface/qo-100-psu-interface-bot.png

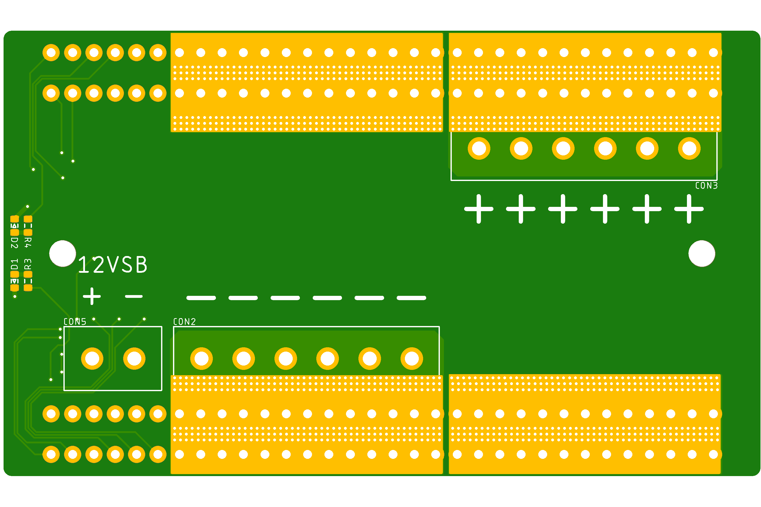
pcb/psu-interface/qo-100-psu-interface-bot.png
