vankxr/qo-100-tools/pcb/relay-controller/qo-100-relay-controller-bot.png

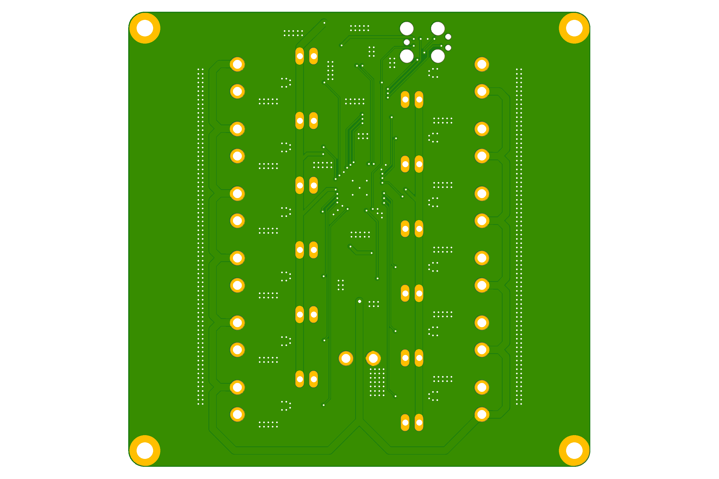
pcb/relay-controller/qo-100-relay-controller-bot.png
