vankxr/qo-100-tools/pcb/relay-controller/qo-100-relay-controller-top.png

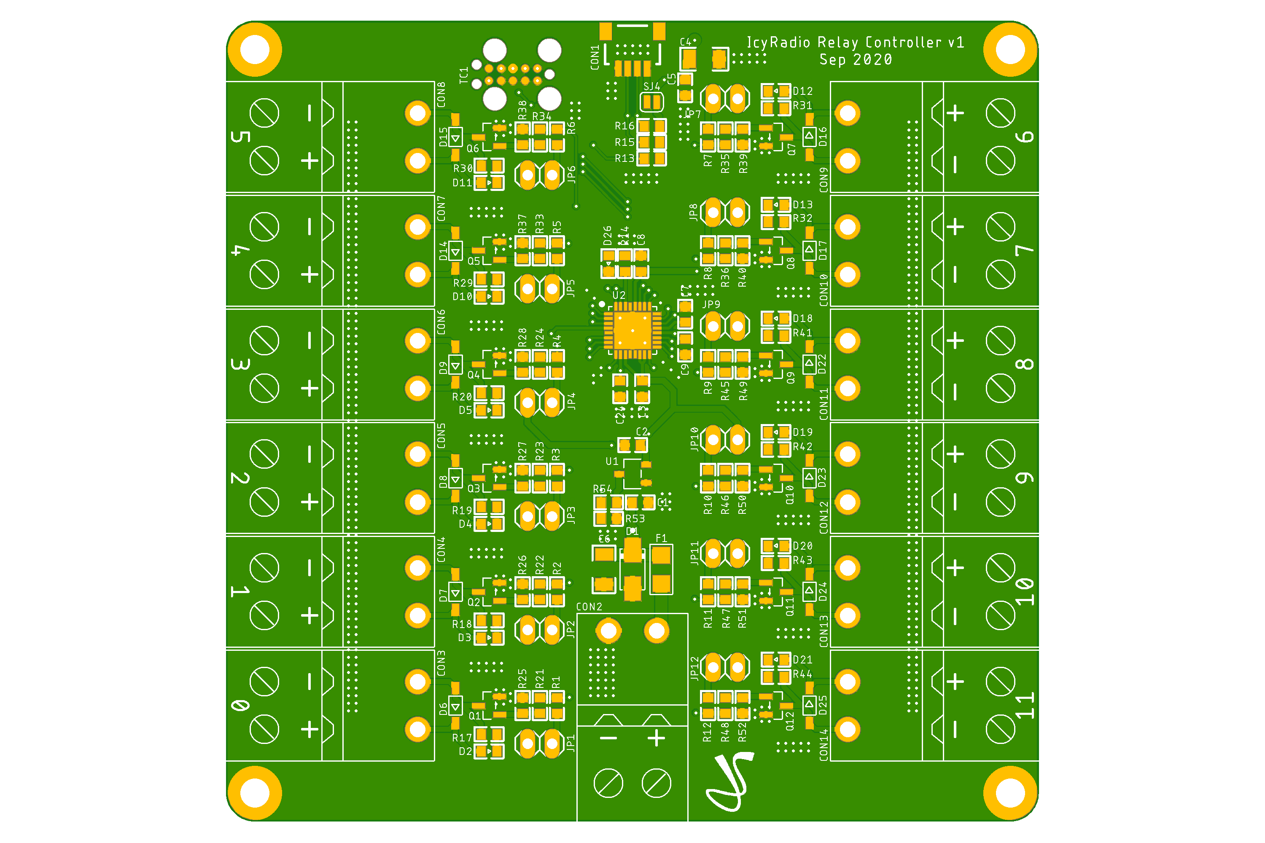
pcb/relay-controller/qo-100-relay-controller-top.png
