vankxr/qo-100-tools/pcb/rf-switch/qo-100-rf-switch-bot.png

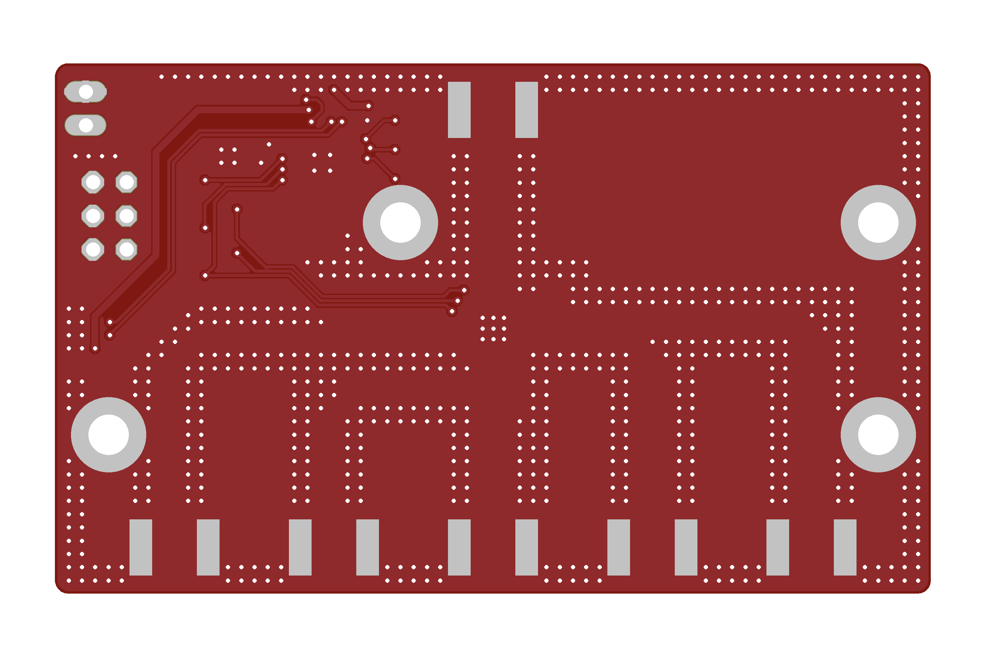
pcb/rf-switch/qo-100-rf-switch-bot.png
