vankxr/qo-100-tools/pcb/rf-switch/qo-100-rf-switch-top.png

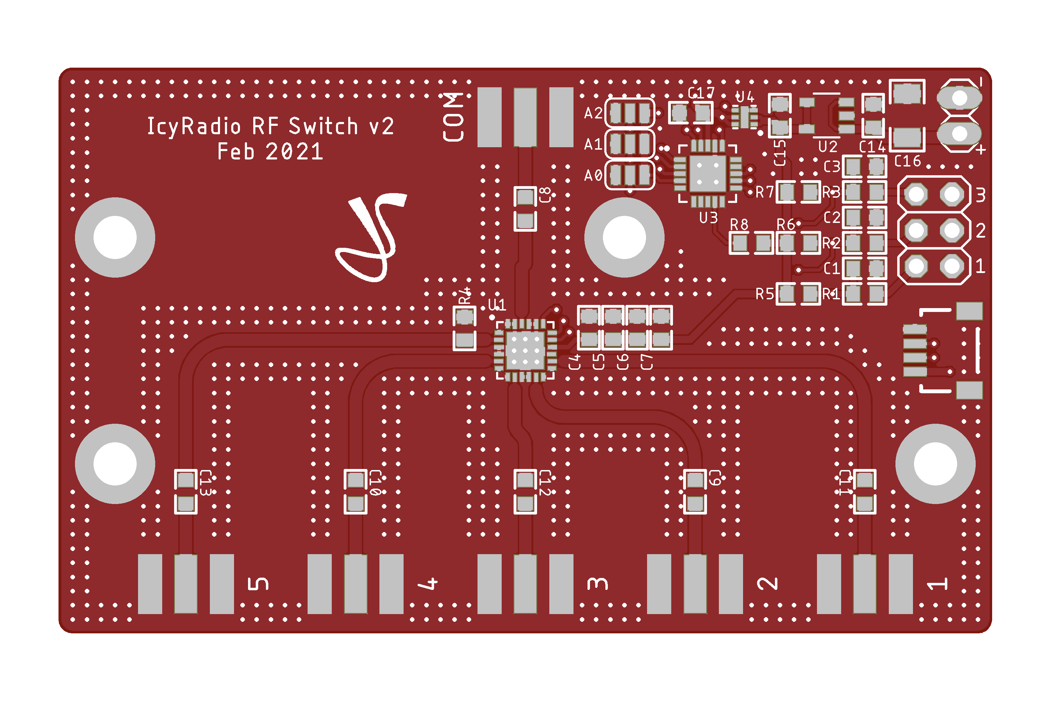
pcb/rf-switch/qo-100-rf-switch-top.png
