vankxr/qo-100-tools/pcb/upconverter/qo-100-upconverter-bot.png

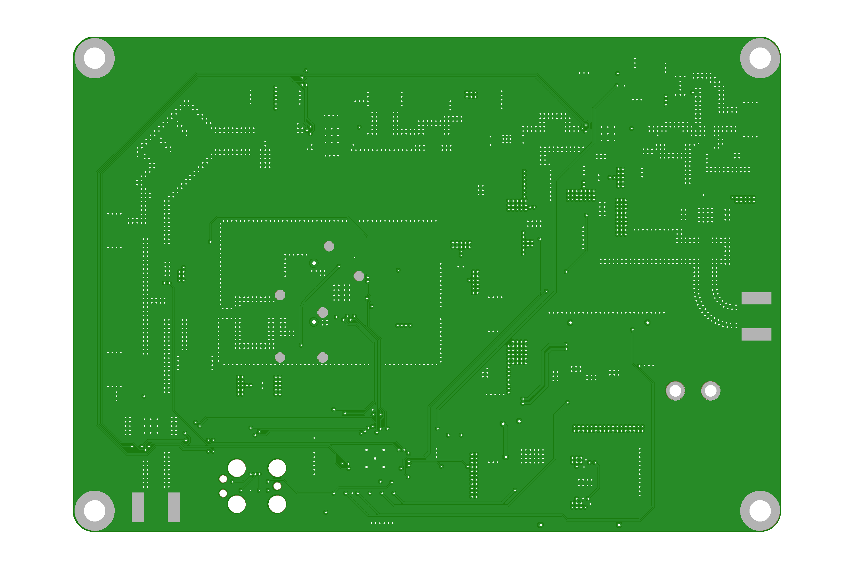
pcb/upconverter/qo-100-upconverter-bot.png
