vankxr/qo-100-tools/pcb/upconverter/qo-100-upconverter-top.png

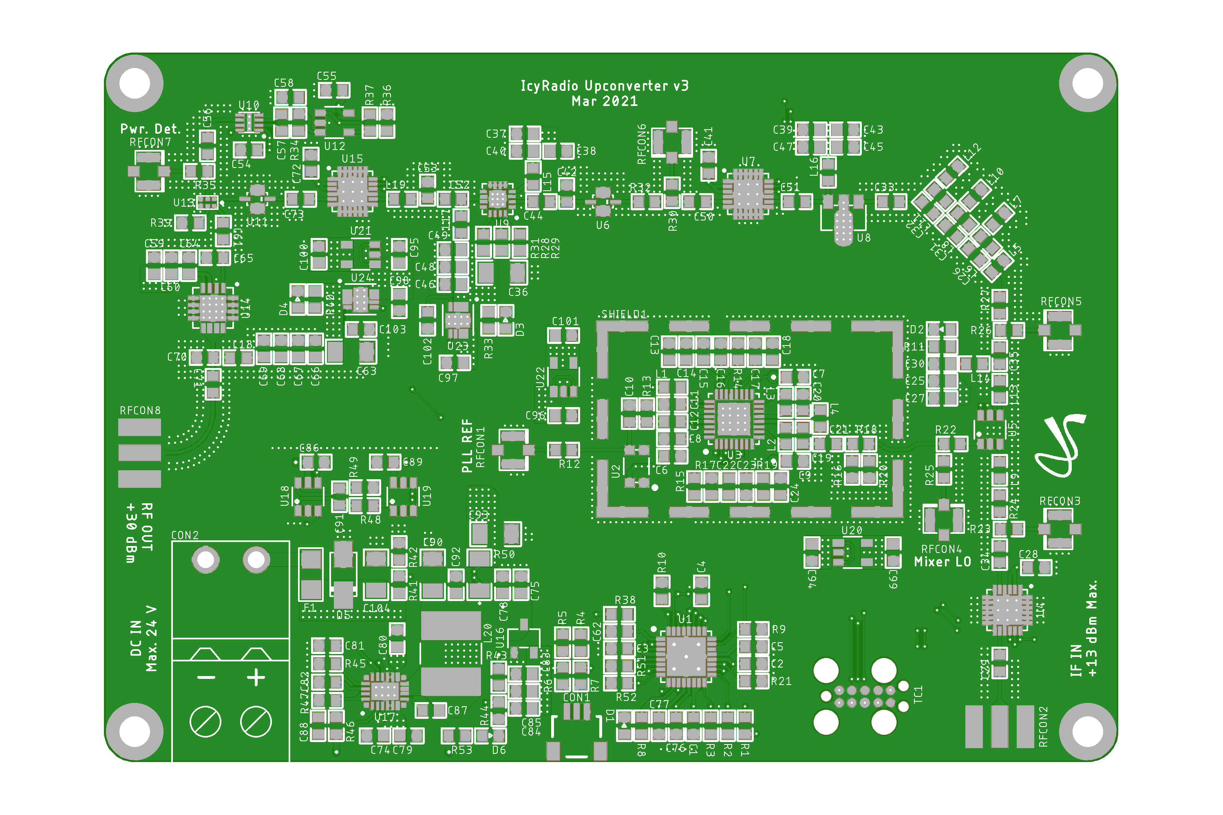
pcb/upconverter/qo-100-upconverter-top.png
