vankxr/qo-100-tools/util/gpsdo-ouput-filters/10M/bokeh_plot.png

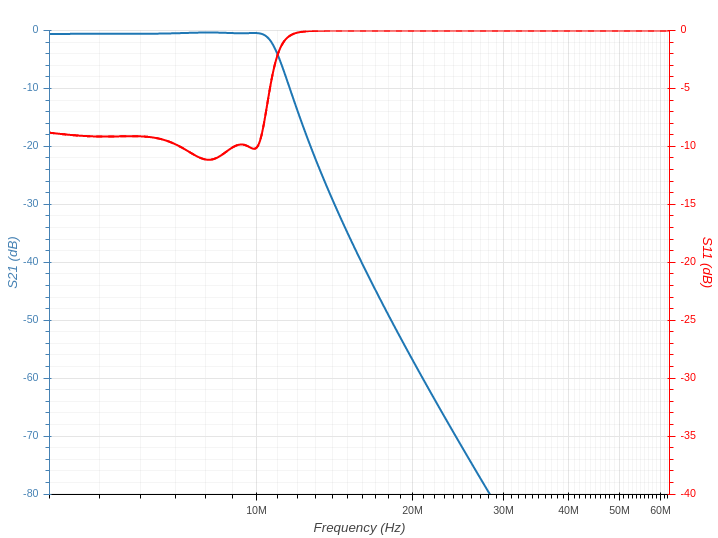
util/gpsdo-ouput-filters/10M/bokeh_plot.png
