vankxr/qo-100-tools/util/pa-bias-simulation/pa-bias-simulation.png

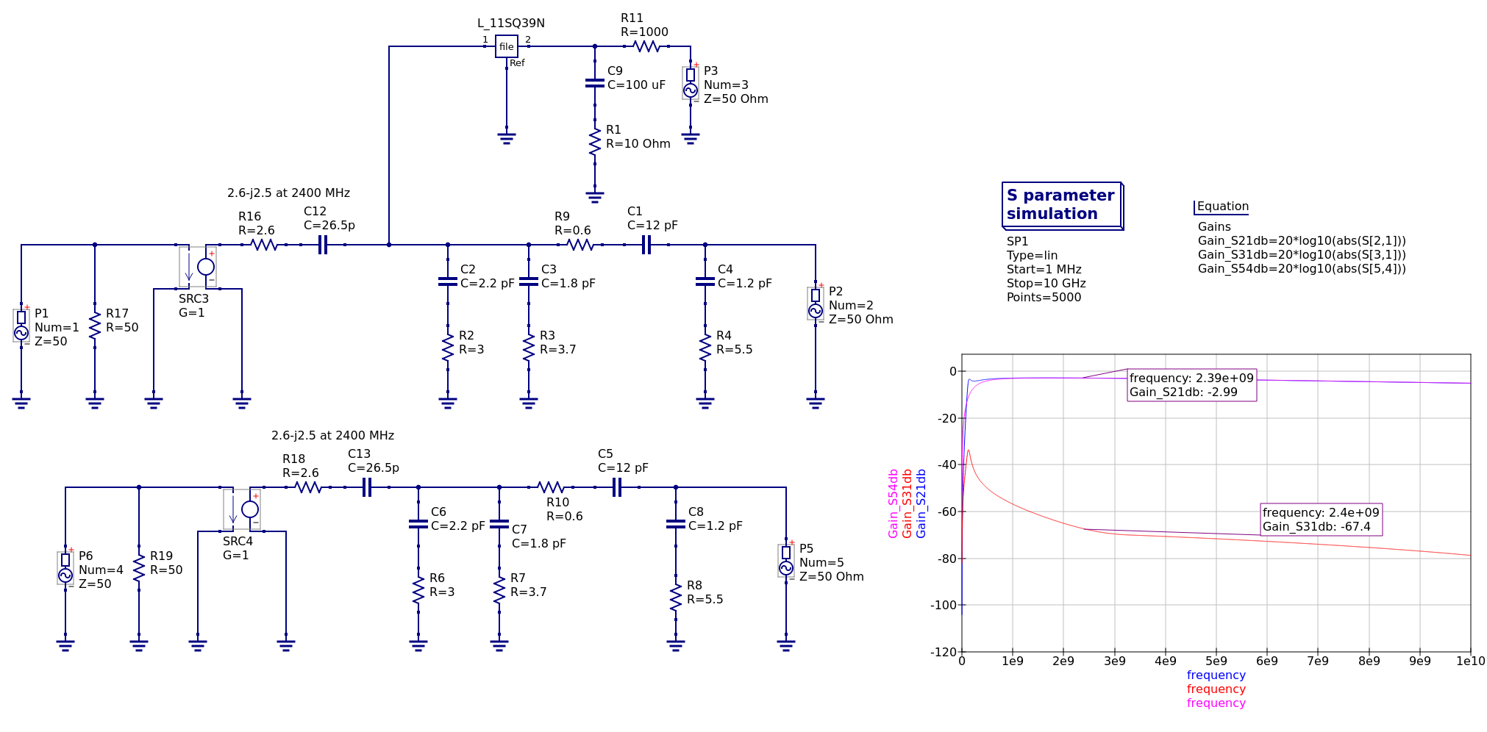
util/pa-bias-simulation/pa-bias-simulation.png
