vankxr/qo-100-tools/util/pa-lpf-simulation/s21.png

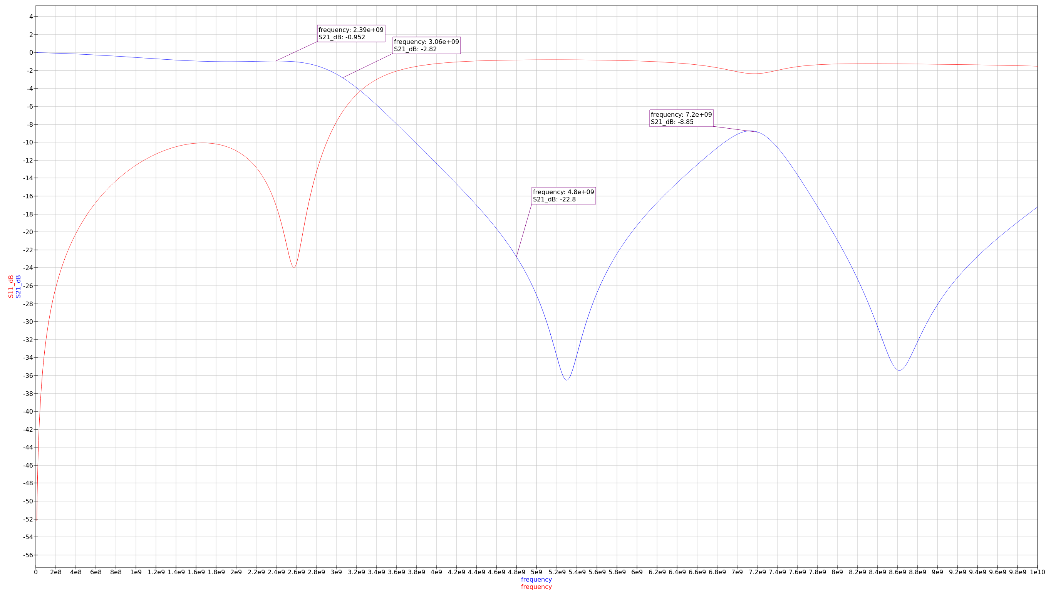
util/pa-lpf-simulation/s21.png
