vankxr/qo-100-tools/util/preamp-bias-simulation/preamp-bias-simulation.png

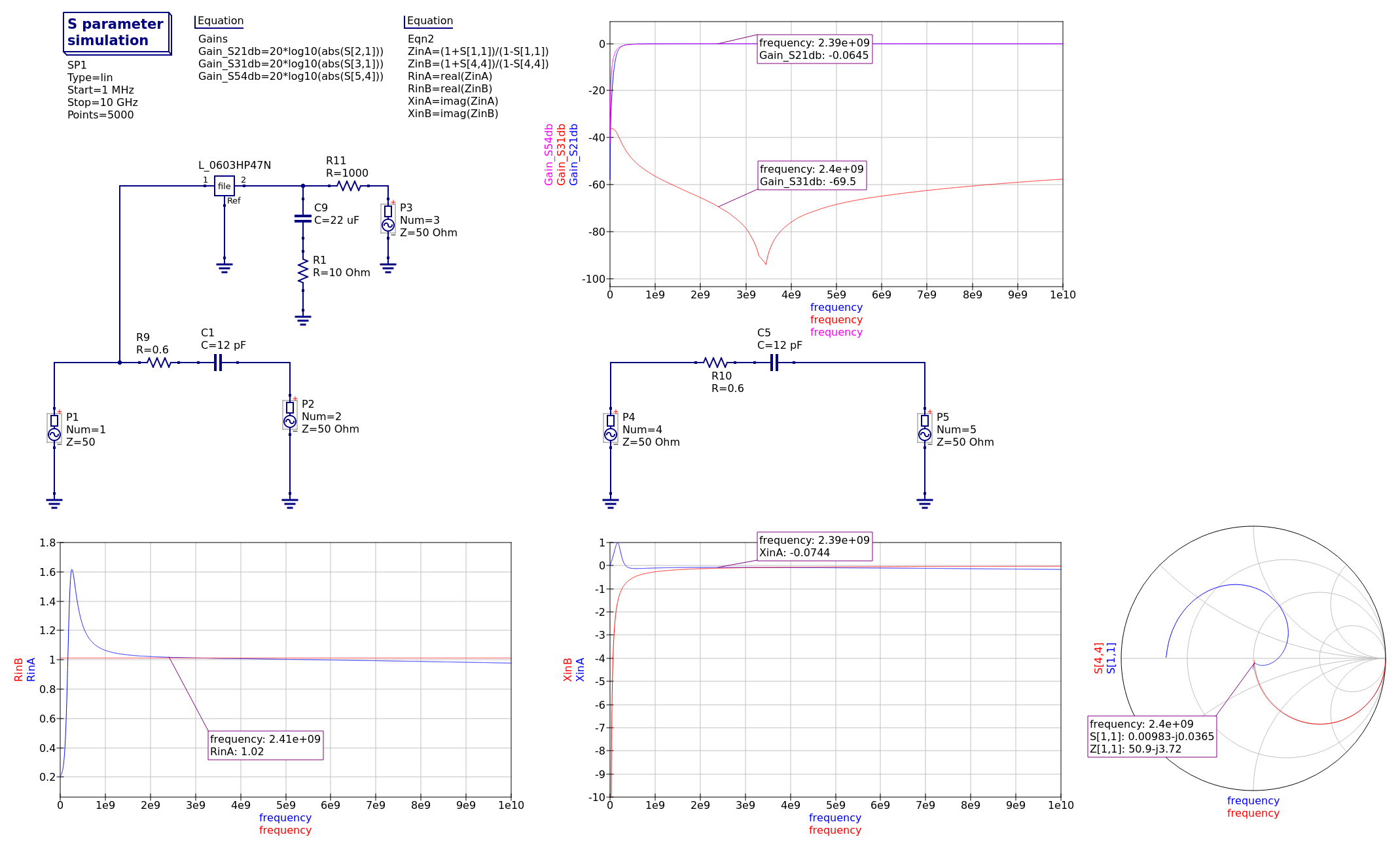
util/preamp-bias-simulation/preamp-bias-simulation.png
