vankxr/qo-100-tools/pcb/lnb-controller/qo-100-lnb-controller.pdf

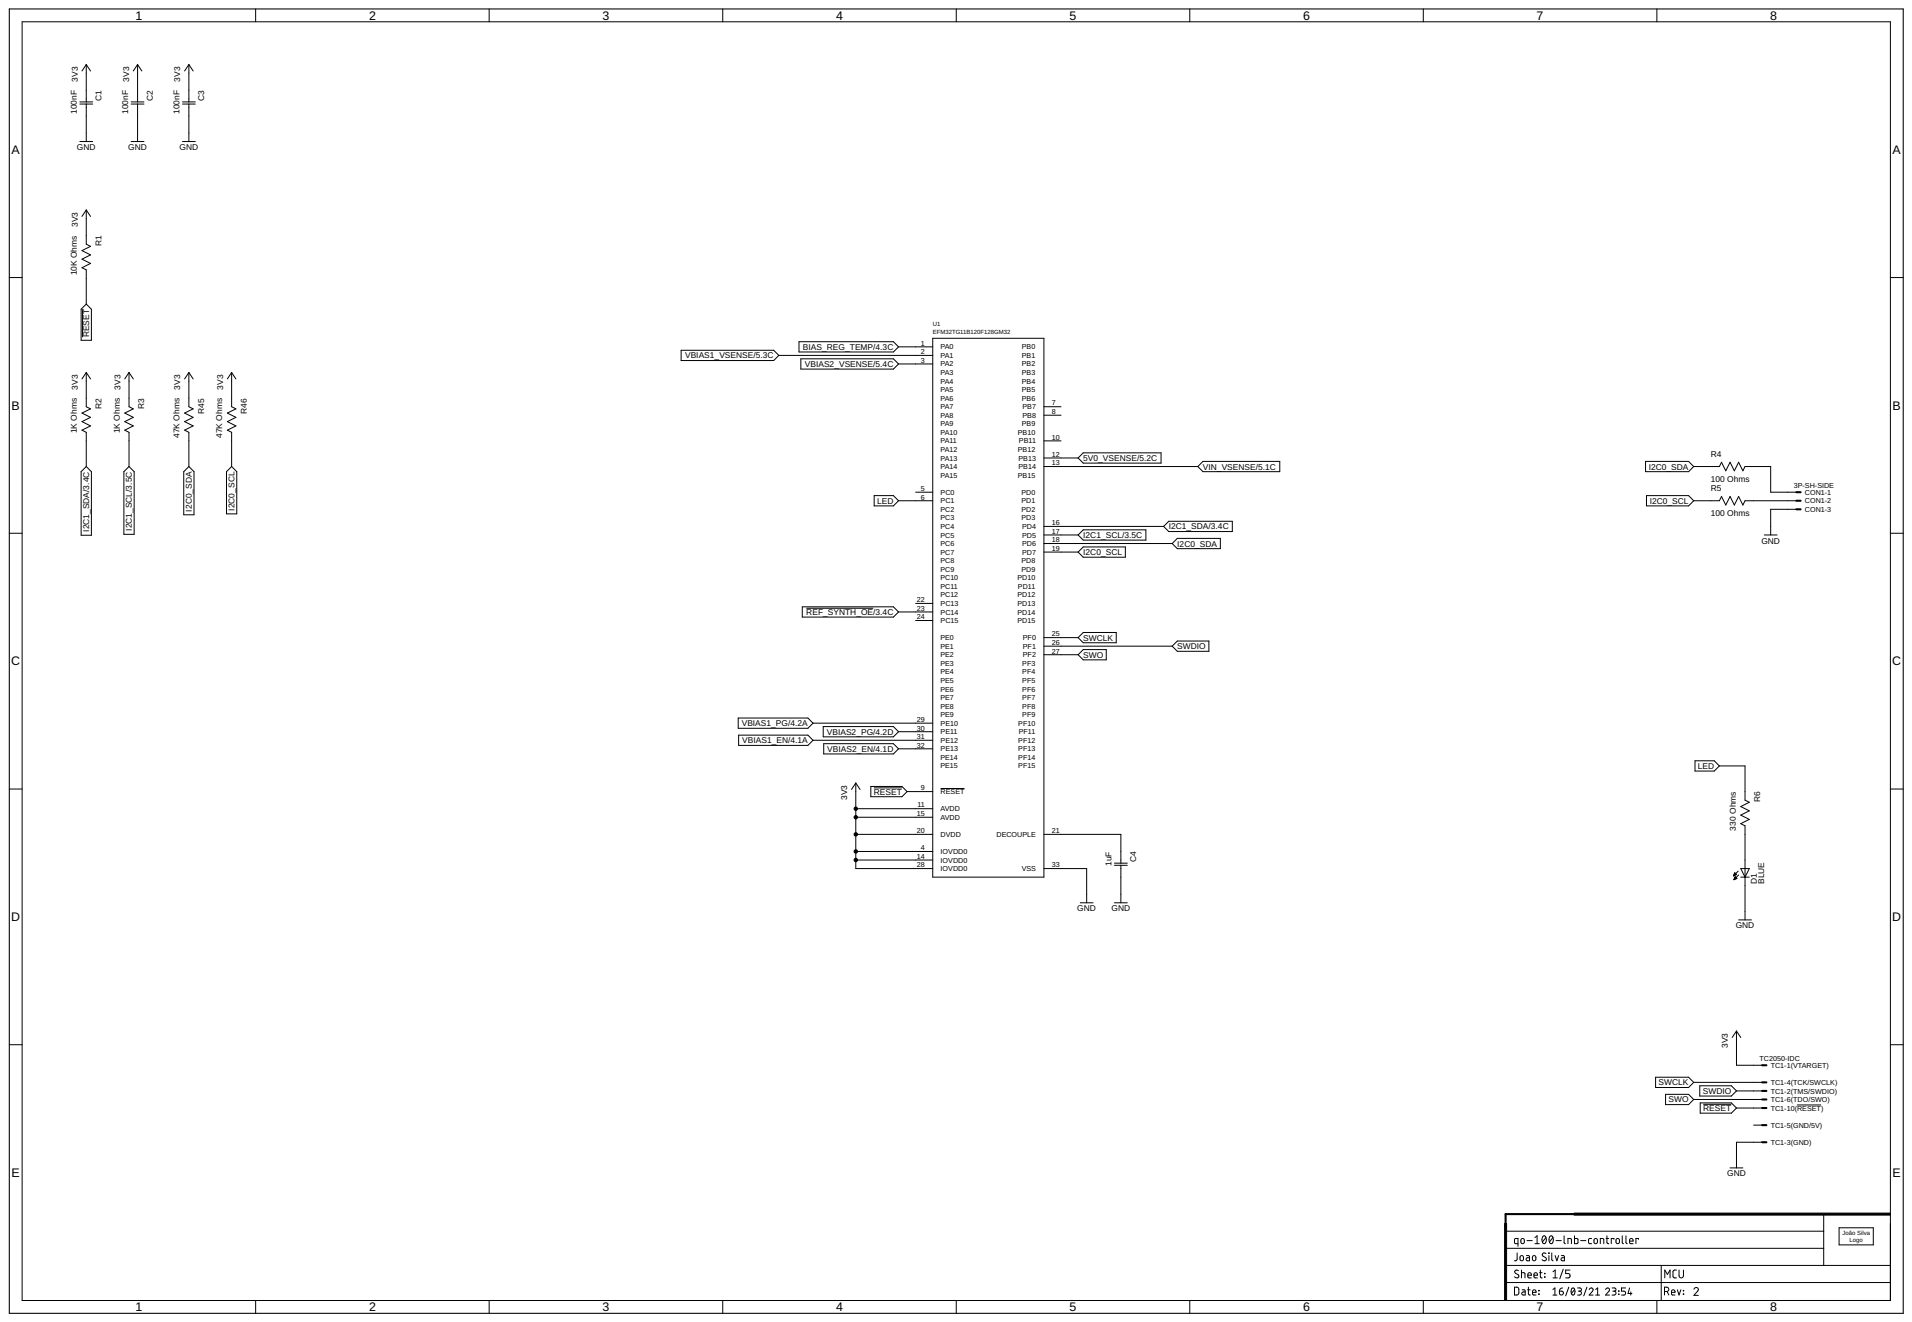
[picture p97: page 1]

10K Ohms TC2050-IDC GND 100nF GND 3V3 3V3 3V3 330 Ohms BLUE GND 100nF GND 3V3 1K Ohms 3V3 1K Ohms 3V3 3P-SH-SIDE GND 100 Ohms 100 Ohms 100nF GND 3V3 3V3 GND GND 1uF EFM32TG11B120F128GM32 47K Ohms 3V3 47K Ohms 3V3 R1 TC1-1(VTARGET) TC1-2(TMS/SWDIO) TC1-3(GND) TC1-4(TCK/SWCLK) TC1-5(GND/5V) TC1-6(TDO/SWO) TC1-10(RESET) C1 R6 D1 C2 R2 R3 CON1-1 CON1-2 CON1-3 R4 R5 C3 C4 PA0 1 PA1 2 PB11 10 PB13 12 PB14 13 PC14 23 PC15 24 PD4 16 PD5 17 PD6 18 PD7 19 PF0 25 PF1 26 PF2 27 RESET 9 IOVDD0 4 AVDD 11 DVDD 20 DECOUPLE 21 VSS 33 AVDD 15 PC0 5 PC1 6 PC13 22 PA2 3 PB7 7 PB8 8 PE12 31 PE13 32 PE11 30 PE10 29 IOVDD0 14 IOVDD0 28 U1 R45 R46 SWO SWO SWDIO SWDIO SWCLK SWCLK RESET RESET RESET LED LED I2C1_SCL/3.5C I2C1_SCL/3.5C I2C1_SDA/3.4C I2C1_SDA/3.4C VBIAS1_VSENSE/5.3C VBIAS2_VSENSE/5.4C BIAS_REG_TEMP/4.3C VBIAS1_EN/4.1A VBIAS2_EN/4.1D I2C0_SDA I2C0_SDA I2C0_SDA I2C0_SCL I2C0_SCL I2C0_SCL VBIAS2_PG/4.2D VBIAS1_PG/4.2AREF_SYNTH_OE/3.4C VIN_VSENSE/5.1C 5V0_VSENSE/5.2C João Silva Logo ABCDE 1 2 3 4 5 6 7 8 ABCDE 1 2 3 4 5 6 7 8 PC6 PC7 PC8 PC9 PC10 PE0 PA6 PA7 PA9 PA10 PA11 PA13 PA15 PC4 PC5 PC3 PC2 PC12 PC11 PE1 PE2 PE3 PF5 PF13 PF14 PF15 PB10 PB9 PB2 PB1 PB0 PF6 PF7 PF8 PF9 PF10 PF11 PF12 PE5 PE6 PE7 PE4 PE8 PE9 PE14 PE15 PD8 PD9 PD3 PD2 PD1 PD0 PB3 PB4 PB5 PB6 PA14 PA12 PA8 PA5 PA4 PA3 PB12 PB15 PD13 PD14 PD15 PD10 PD11 PD12 PF3 PF4

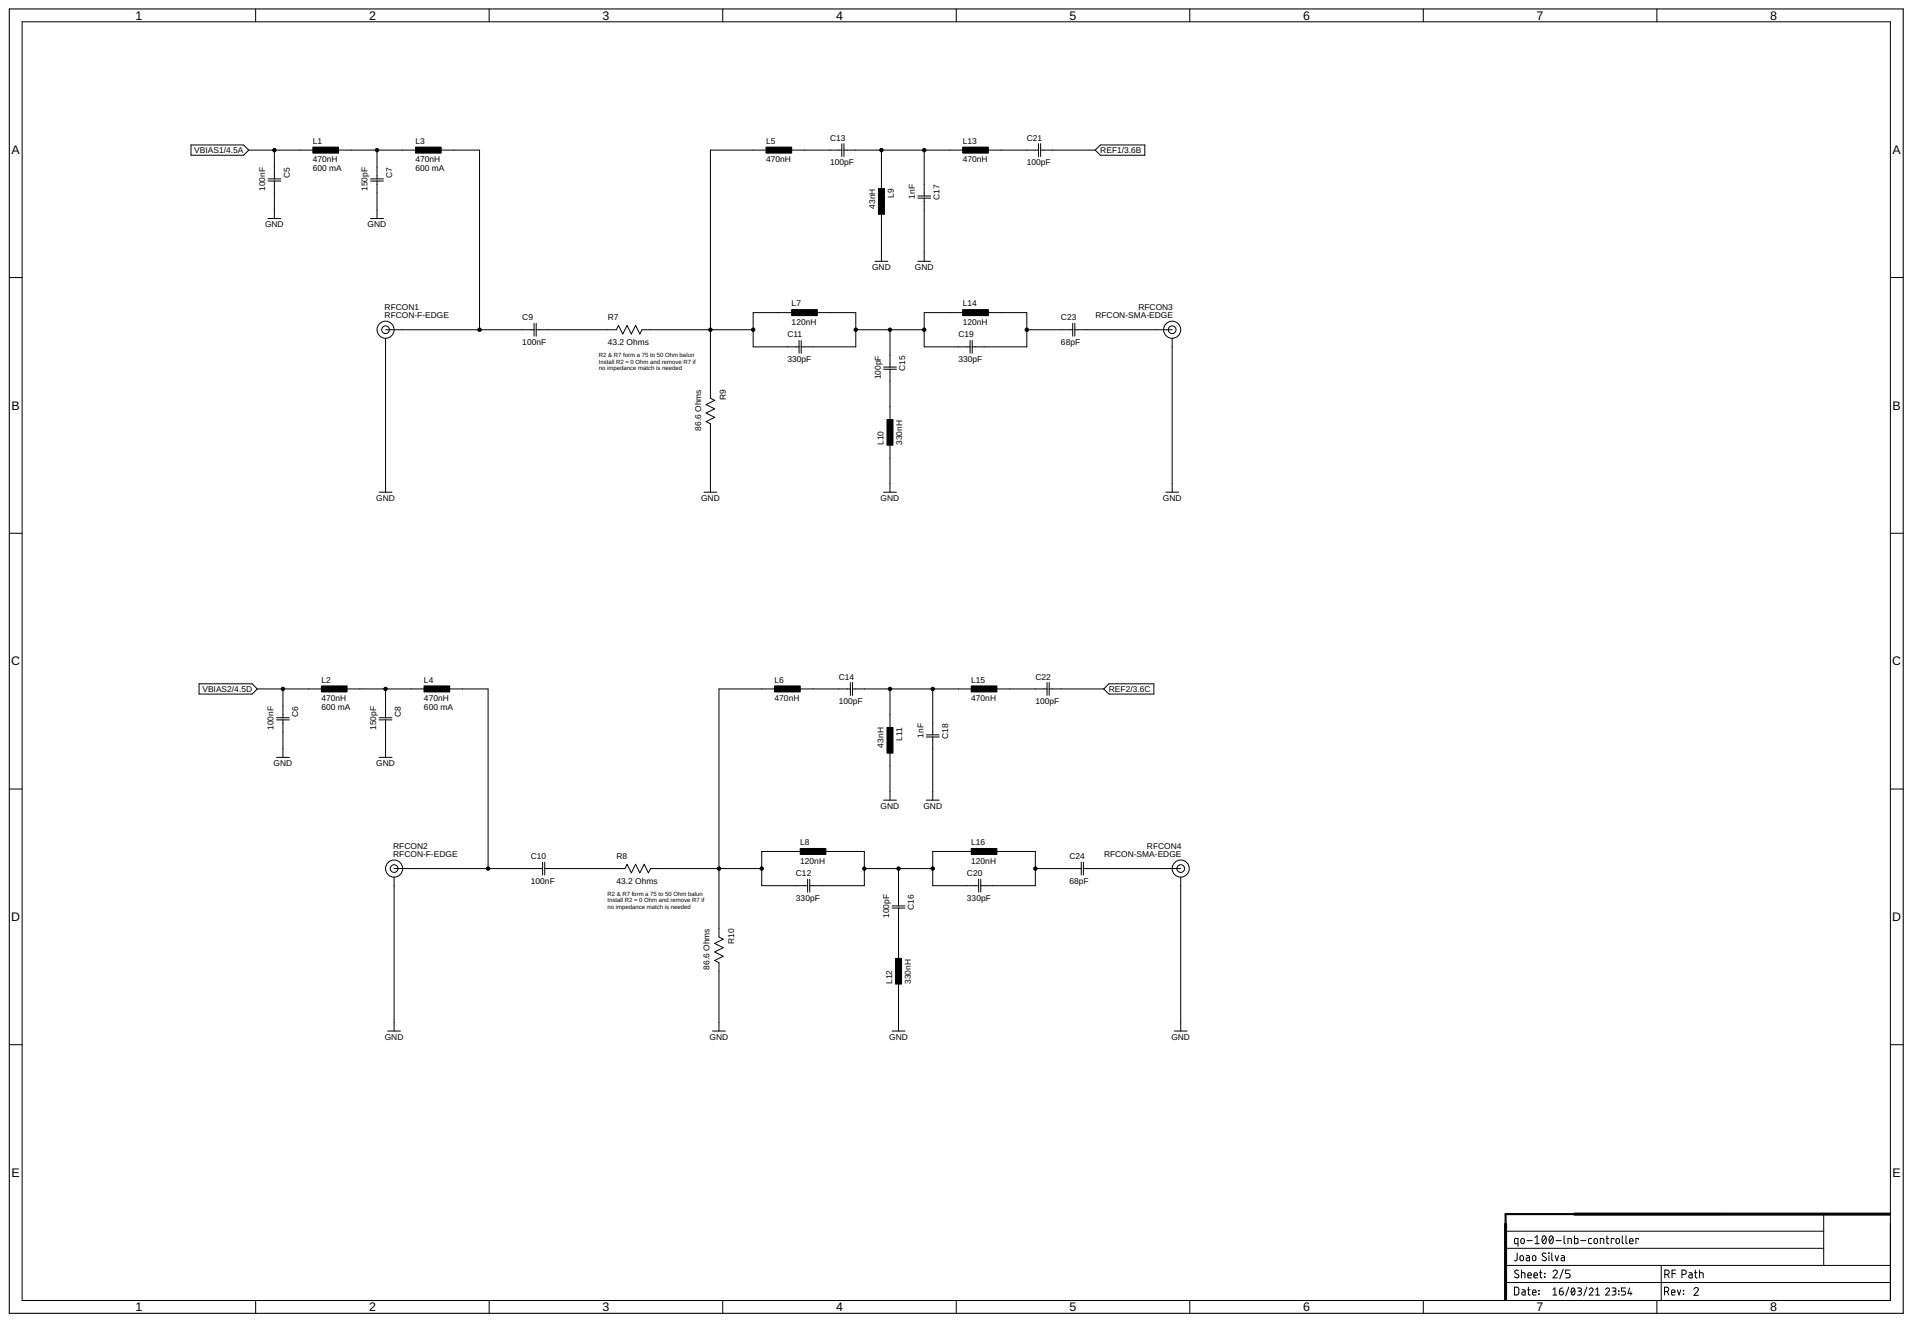
[picture p98: page 2]

R2 & R7 form a 75 to 50 Ohm balun
Install R2 = 0 Ohm and remove R7 if no impedance match is needed

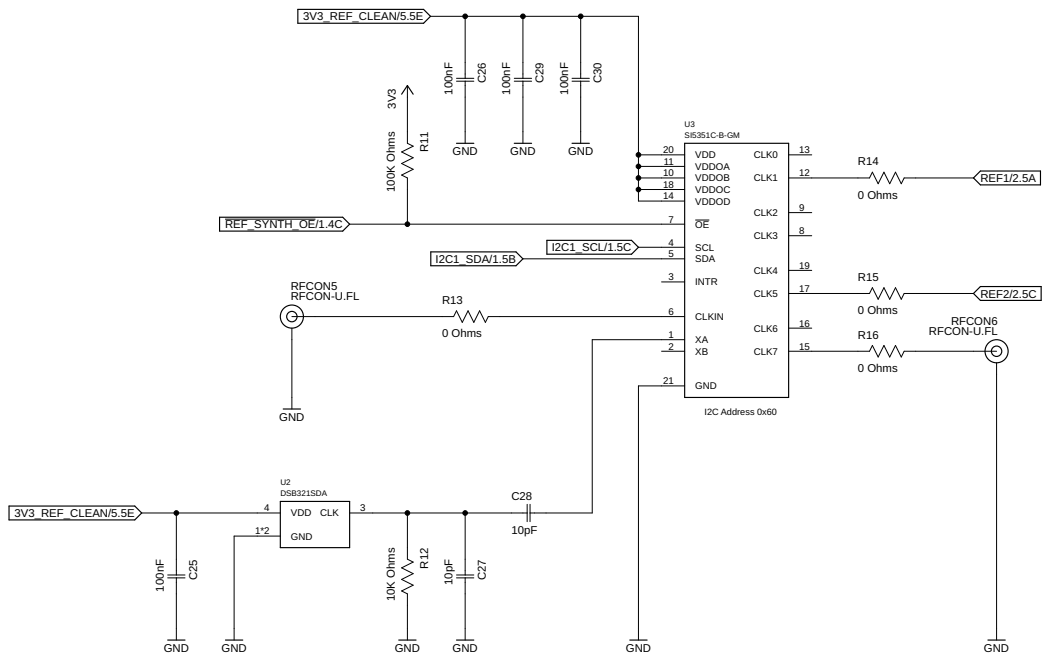
[picture p99: page 3]

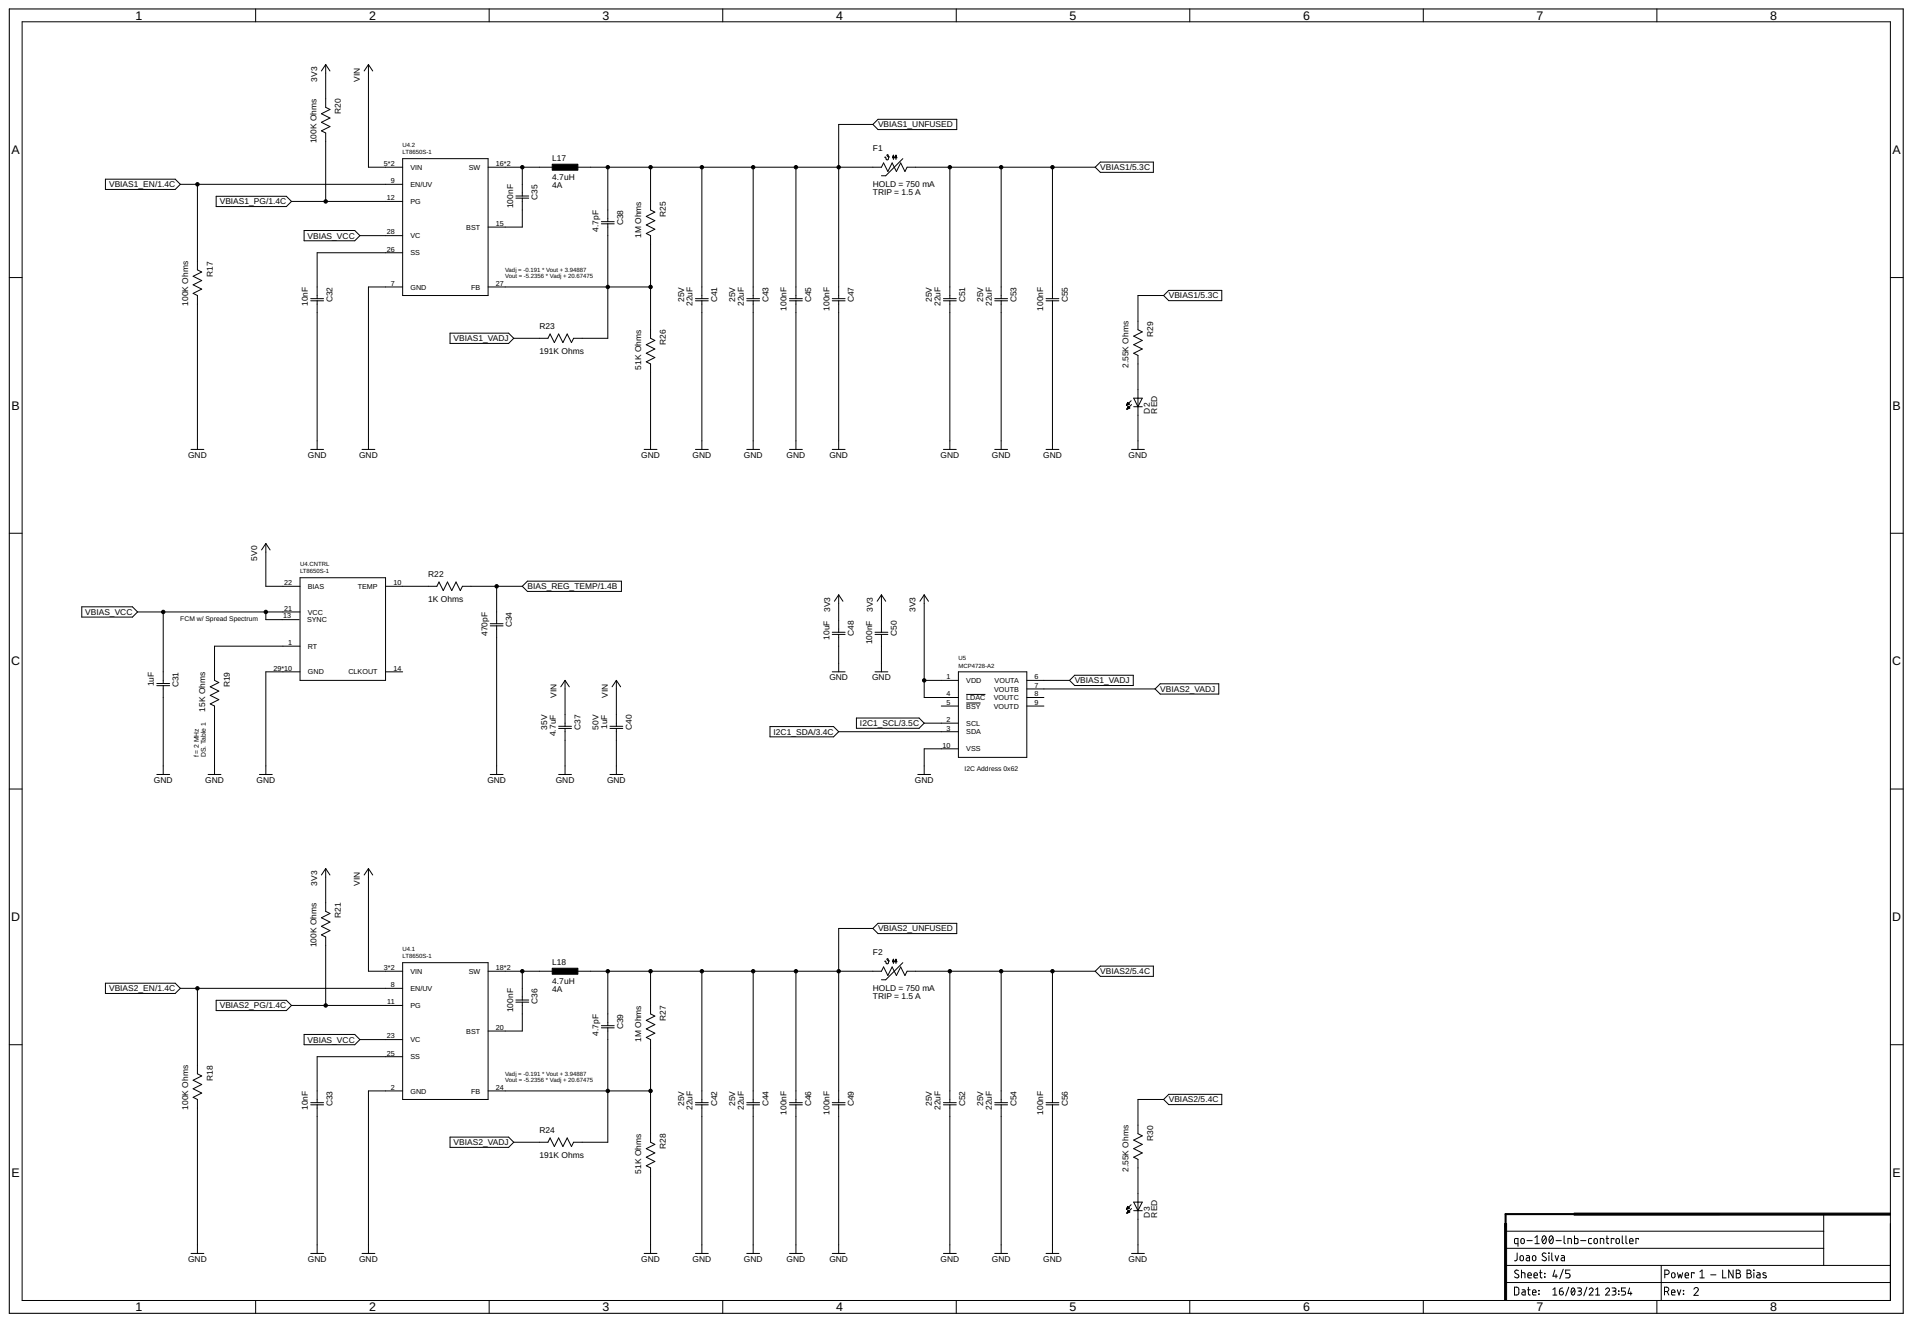
[picture p100: page 4]

f = 2 MHz DS. Table 1 Vadj = -0.191 * Vout + 3.94887 Vout = -5.2356 * Vadj + 20.67475 FCM w/ Spread Spectrum I2C Address 0x62 Vadj = -0.191 * Vout + 3.94887 Vout = -5.2356 * Vadj + 20.67475 25V 35V 4A 50V 25V 25V HOLD = 750 mA TRIP = 1.5 A 25V 25V 4A 25V 25V HOLD = 750 mA TRIP = 1.5 A 25V 22uF GND 100nF GND 4.7uF GND GND GND GND 10nF 15K Ohms 4.7uH GND 100nF 1M Ohms 51K Ohms GND 4.7pF 1uF GND VIN 100nF GND 22uF GND 22uF LT8650S-1 100K Ohms GND 100K Ohms 3V3 100nF GND GND 1uF GND GND 22uF 22uF GND 100nF GND GND GND 10nF 4.7uH GND 100nF 1M Ohms 51K Ohms GND 4.7pF VIN 100nF GND 22uF GND 22uF 100K Ohms GND 100K Ohms 3V3 100nF GND GND 22uF 1K Ohms 470pF GND 2.55K Ohms RED GND 2.55K Ohms RED GND LT8650S-1 LT8650S-1 VIN VIN 5V0 GND 100nF GND 10uF GND 3V3 3V3 MCP4728-A2 3V3 191K Ohms 191K Ohms C51 C55 C37 C32 R19 L17 C35 R25 R26 C38 C40 C45 C41 C43 F1 GND 29*10 RT 1 BIAS 22 SYNC 13 VCC 21 CLKOUT 14 TEMP 10 U4.CNTRL R17 R20 C47 C31 C53 C52 C56 C33 L18 C36 R27 R28 C39 C46 C42 C44 F2 R18 R21 C49 C54 R22 C34 R29 D2 R30 D3 EN/UV 9 VIN 5*2 PG 12 BST 15 SW 16*2 SS 26 FB 27 GND 7 VC 28 U4.2EN/UV 8 VIN 3*2 PG 11 BST 20 SW 18*2 SS 25 FB 24 GND 2 VC 23 U4.1 C50 C48 VDD 1 VSS 10 SCL 2 SDA 3 LDAC 4 VOUTA 6 VOUTB 7 VOUTC 8 VOUTD 9 BSY 5 U5 R23 R24 VBIAS1/5.3C VBIAS1/5.3C VBIAS1_EN/1.4C VBIAS1_PG/1.4C VBIAS_VCC VBIAS_VCC VBIAS_VCC VBIAS1_UNFUSED VBIAS2_EN/1.4C VBIAS2_PG/1.4C VBIAS2_UNFUSED VBIAS2/5.4C VBIAS2/5.4C BIAS_REG_TEMP/1.4B I2C1_SCL/3.5C I2C1_SDA/3.4C VBIAS1_VADJ VBIAS1_VADJ VBIAS2_VADJ VBIAS2_VADJ ABCDE 1 2 3 4 5 6 7 8 ABCDE 1 2 3 4 5 6 7 8

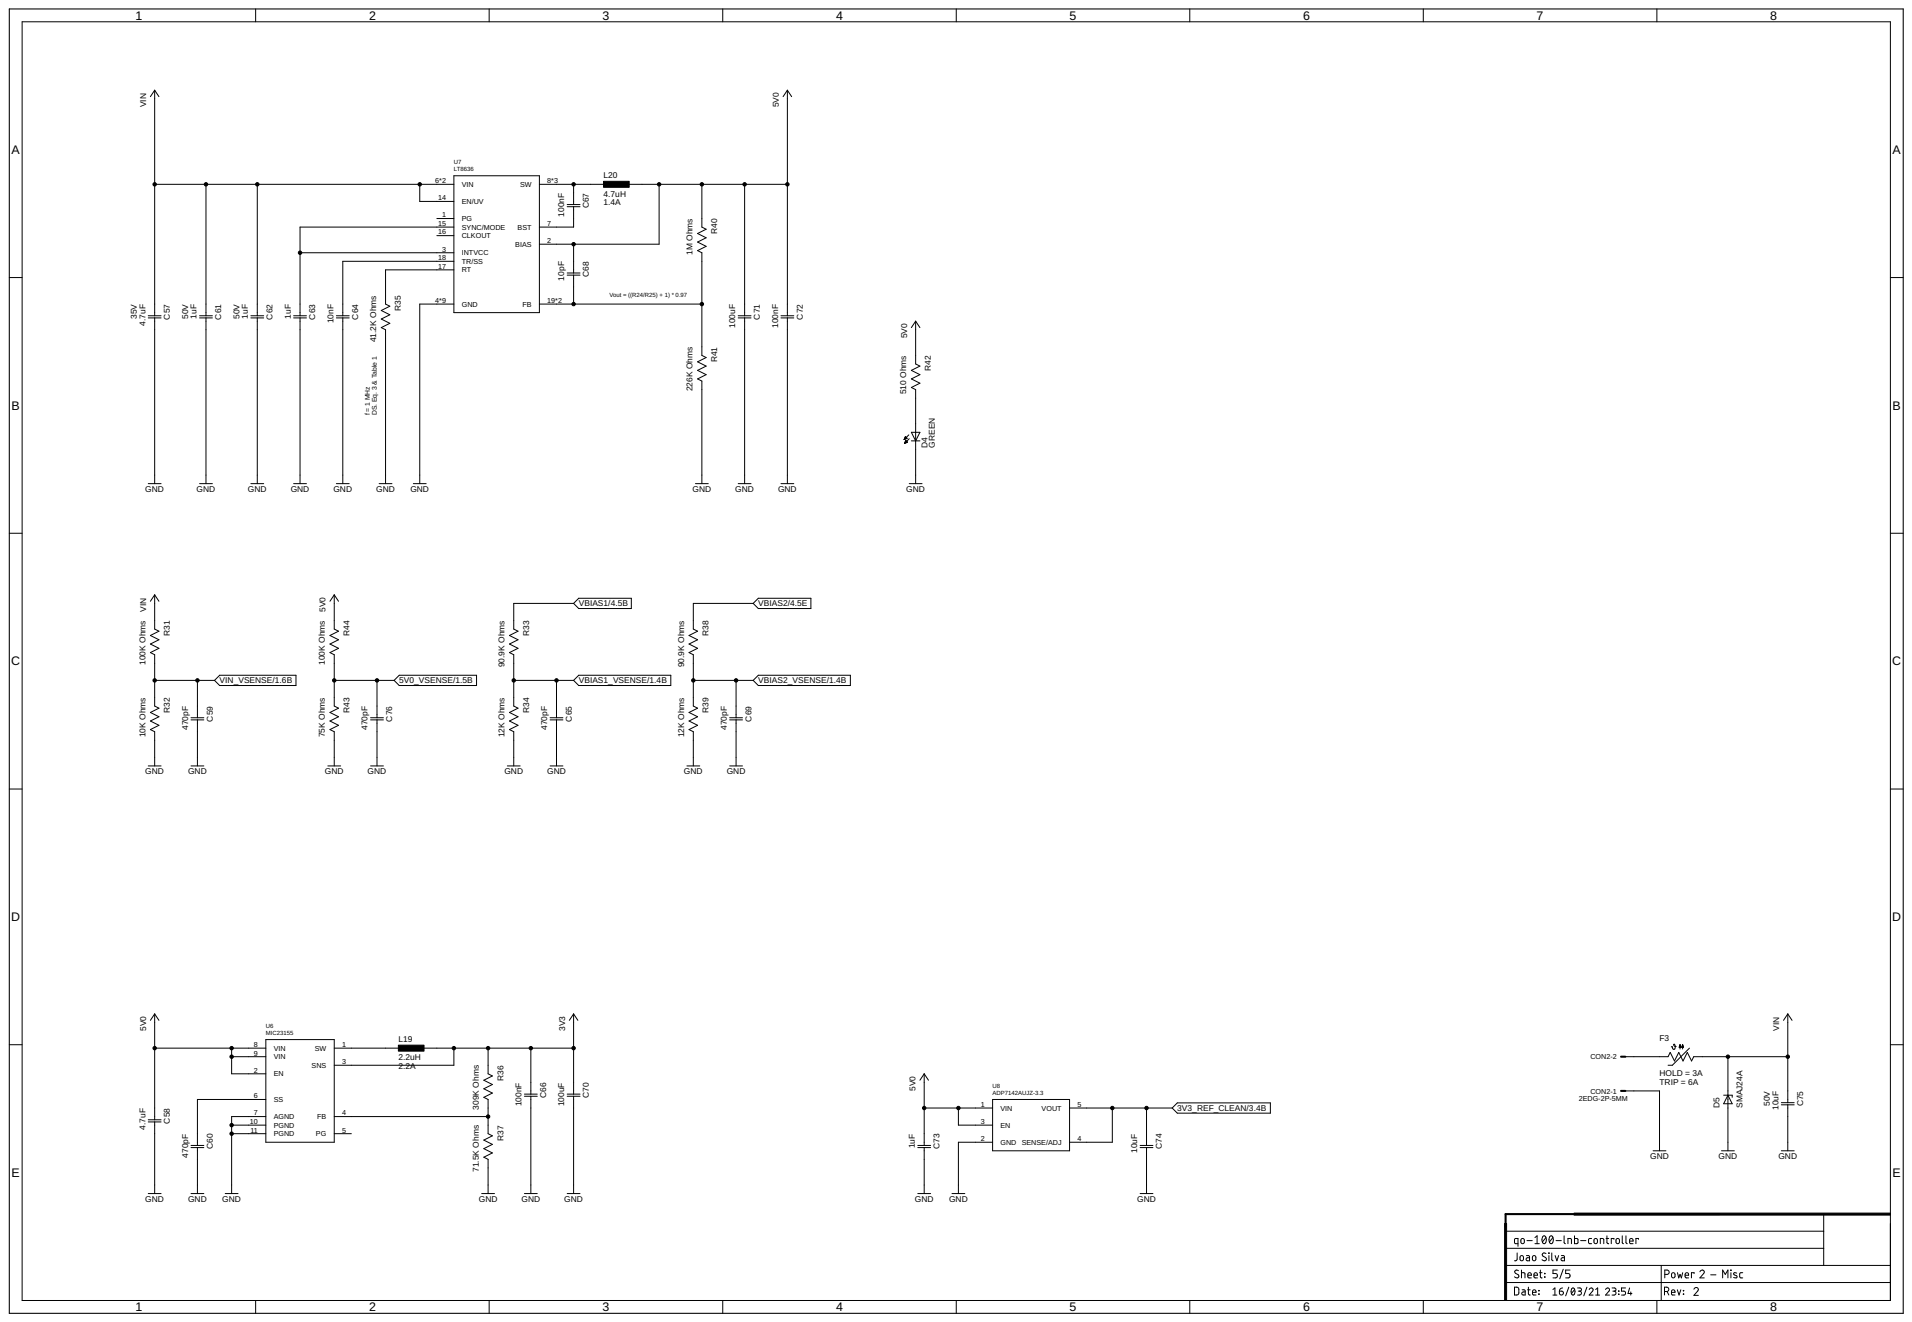
[picture p101: page 5]

4.7uF GND GND GND GND GND GND

f = 1 MHz DS. Eq. 3 & Table 1
