vankxr/qo-100-tools/pcb/pa-bias-controller/qo-100-pa-bias-controller.pdf

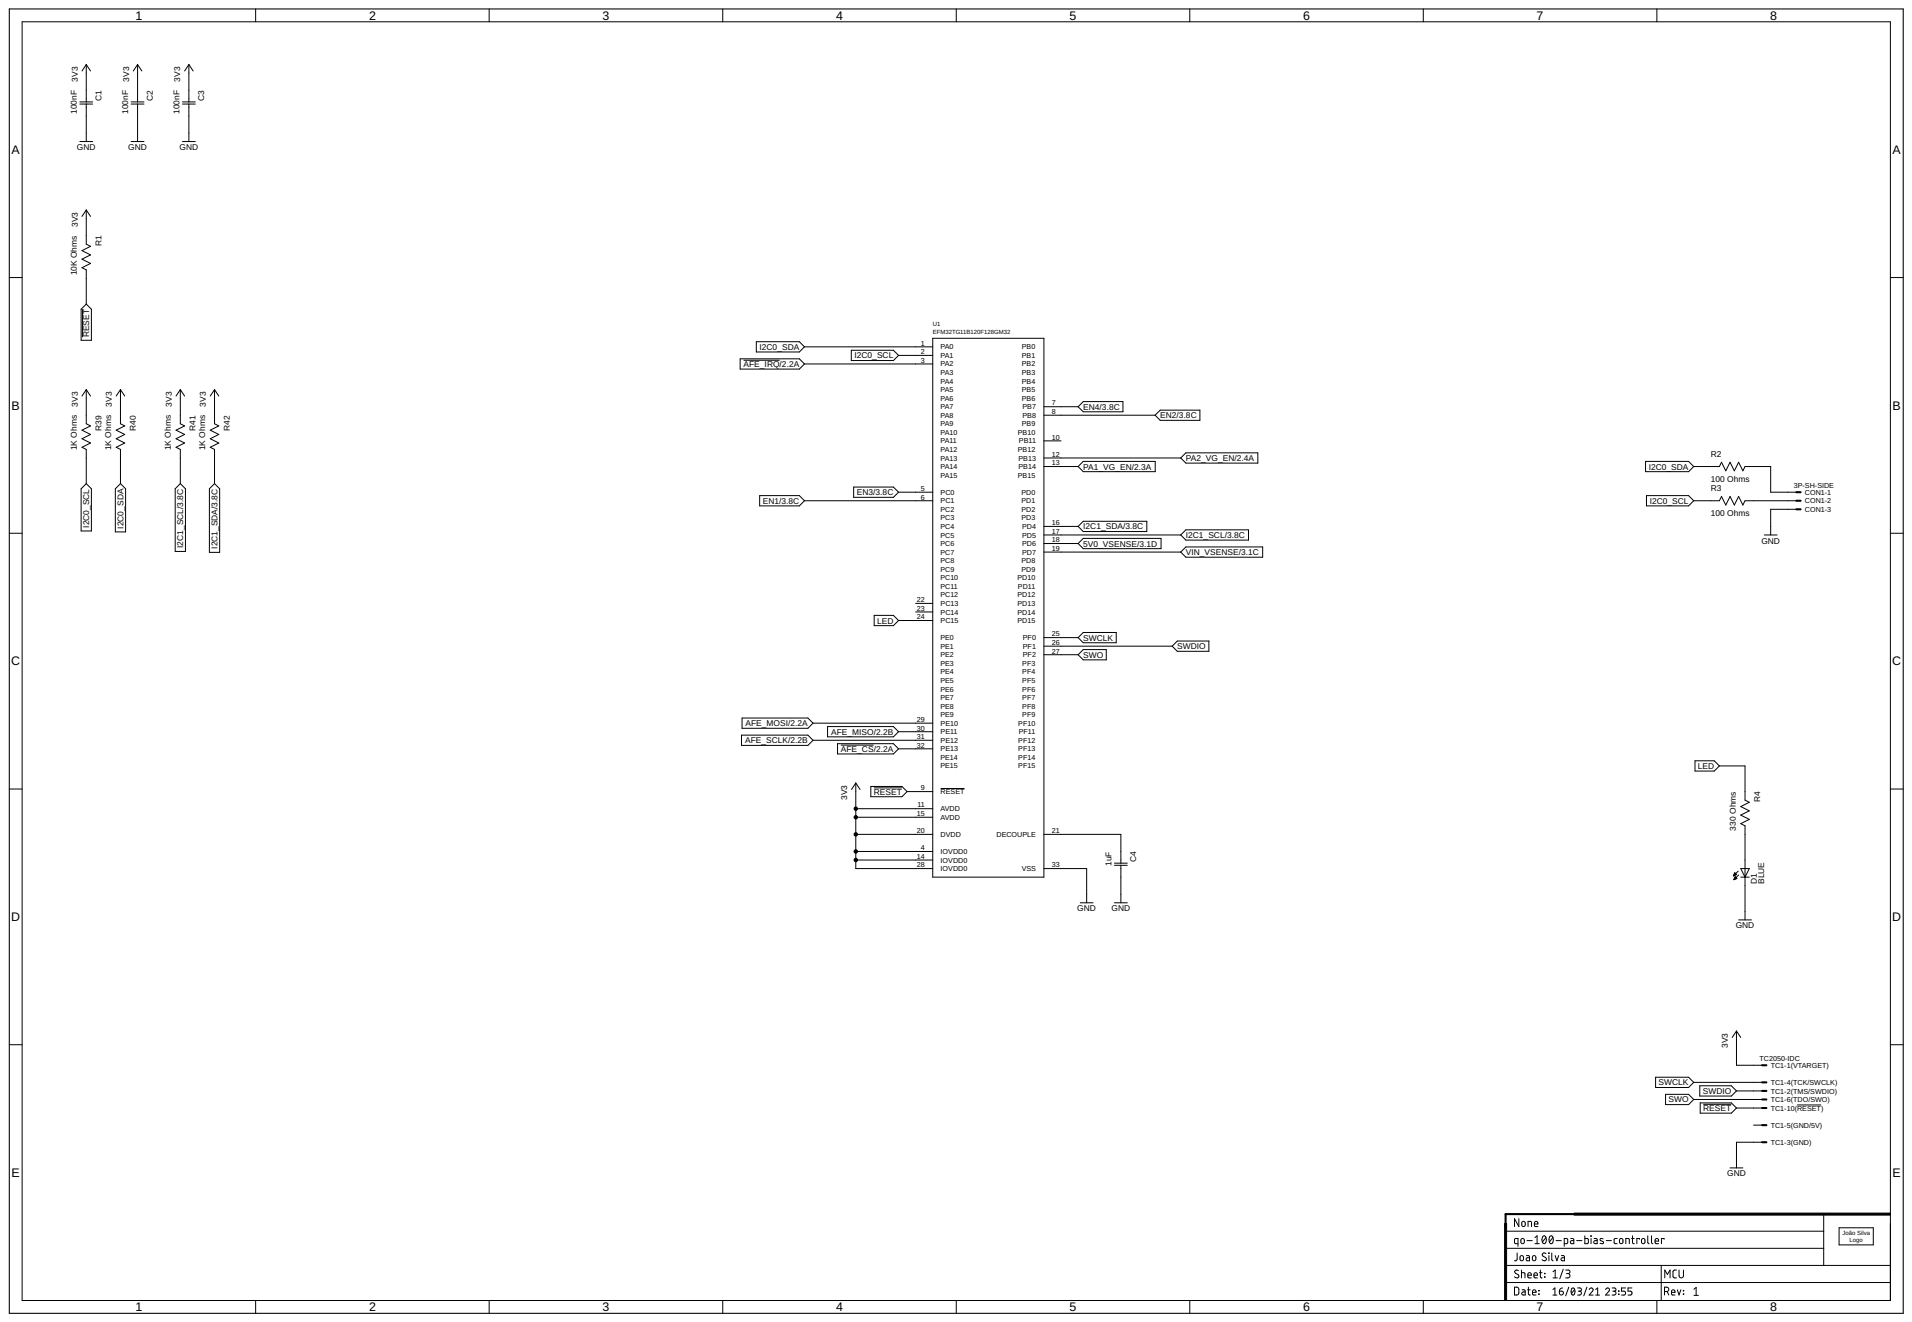
[picture p102: page 1]

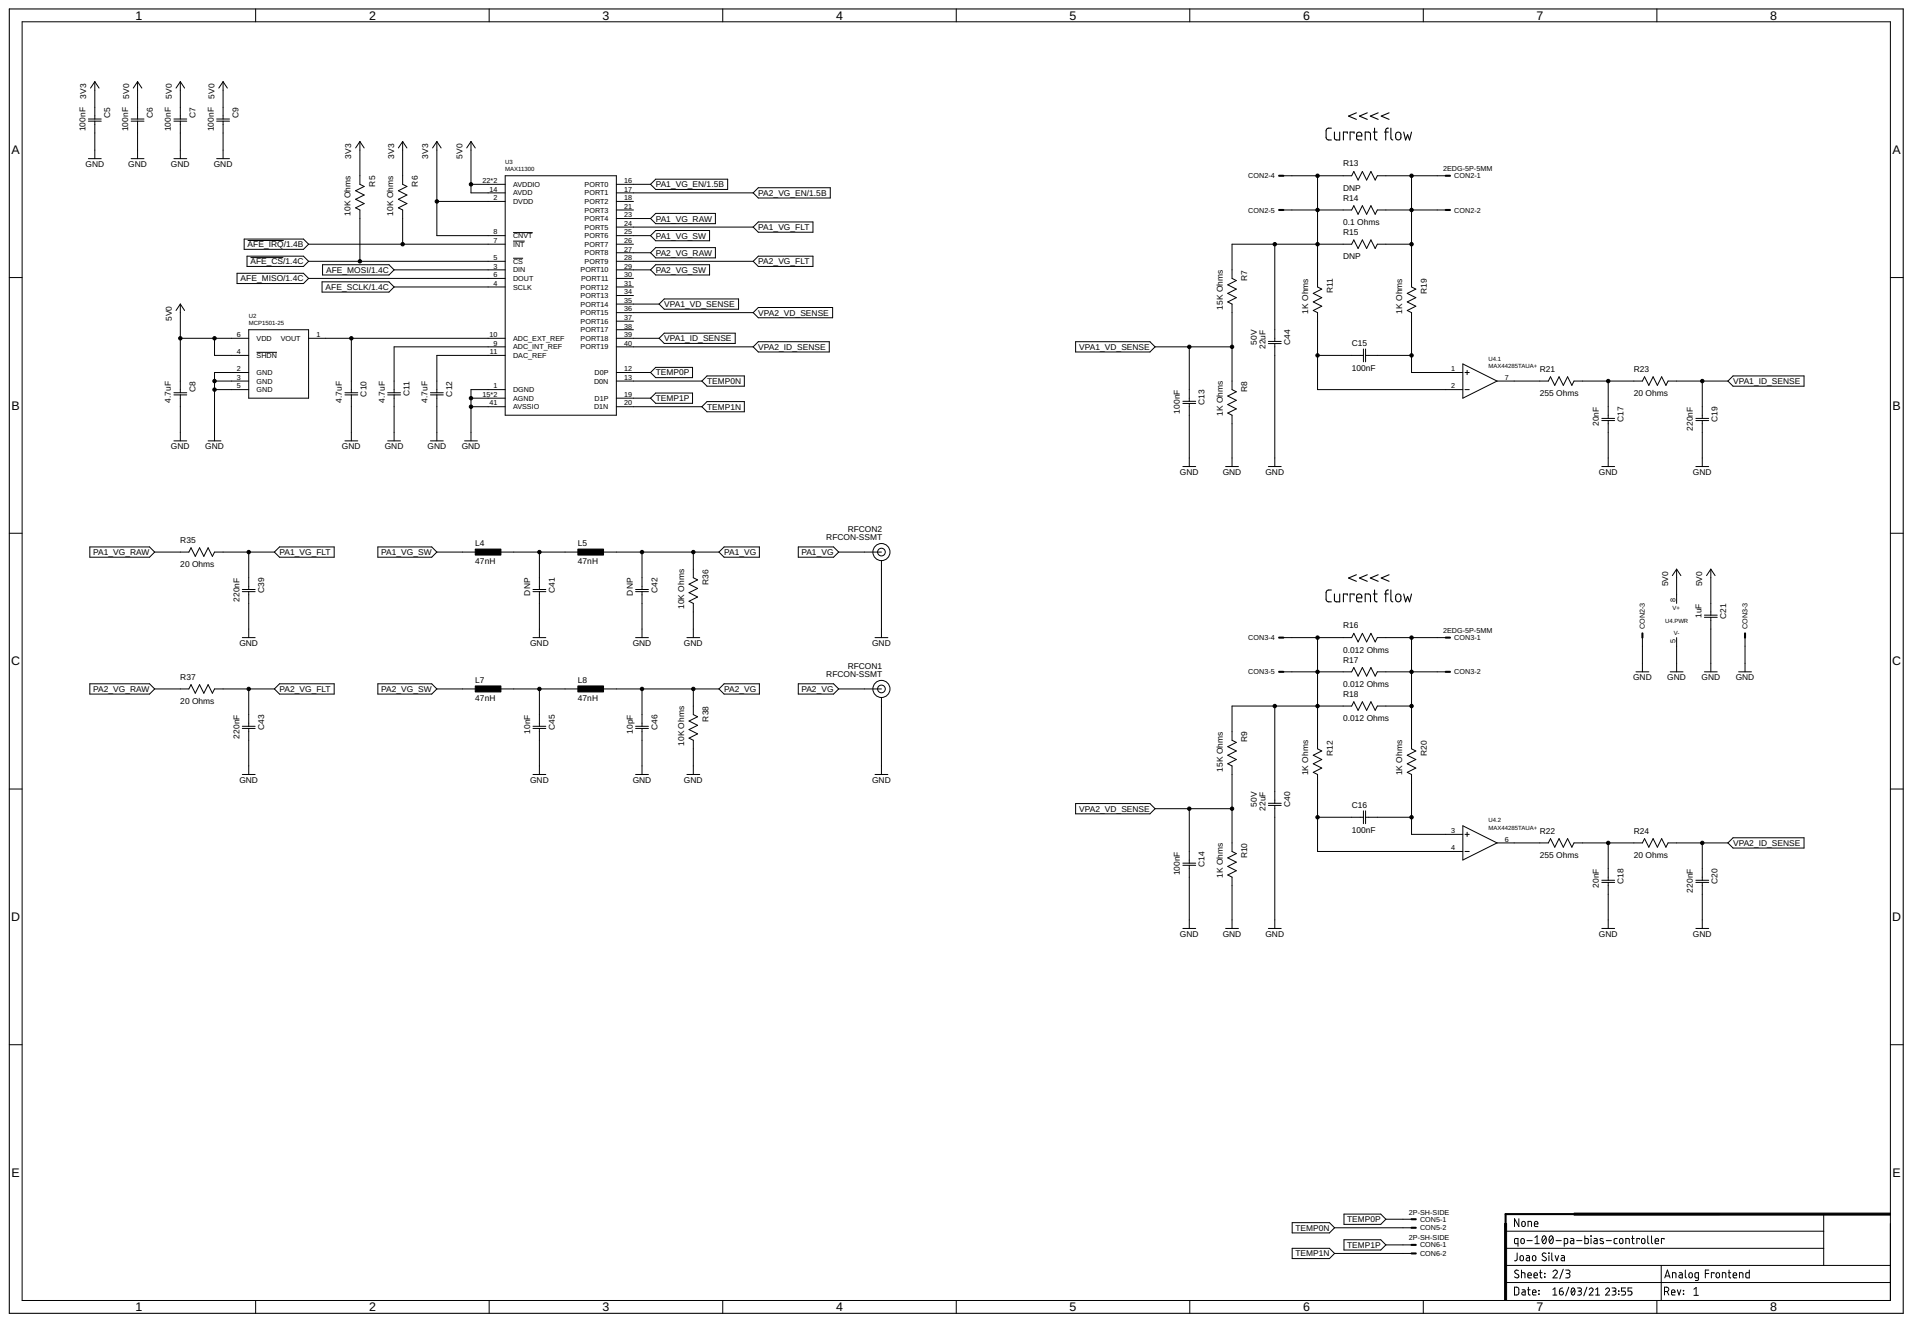
[picture p103: page 2]

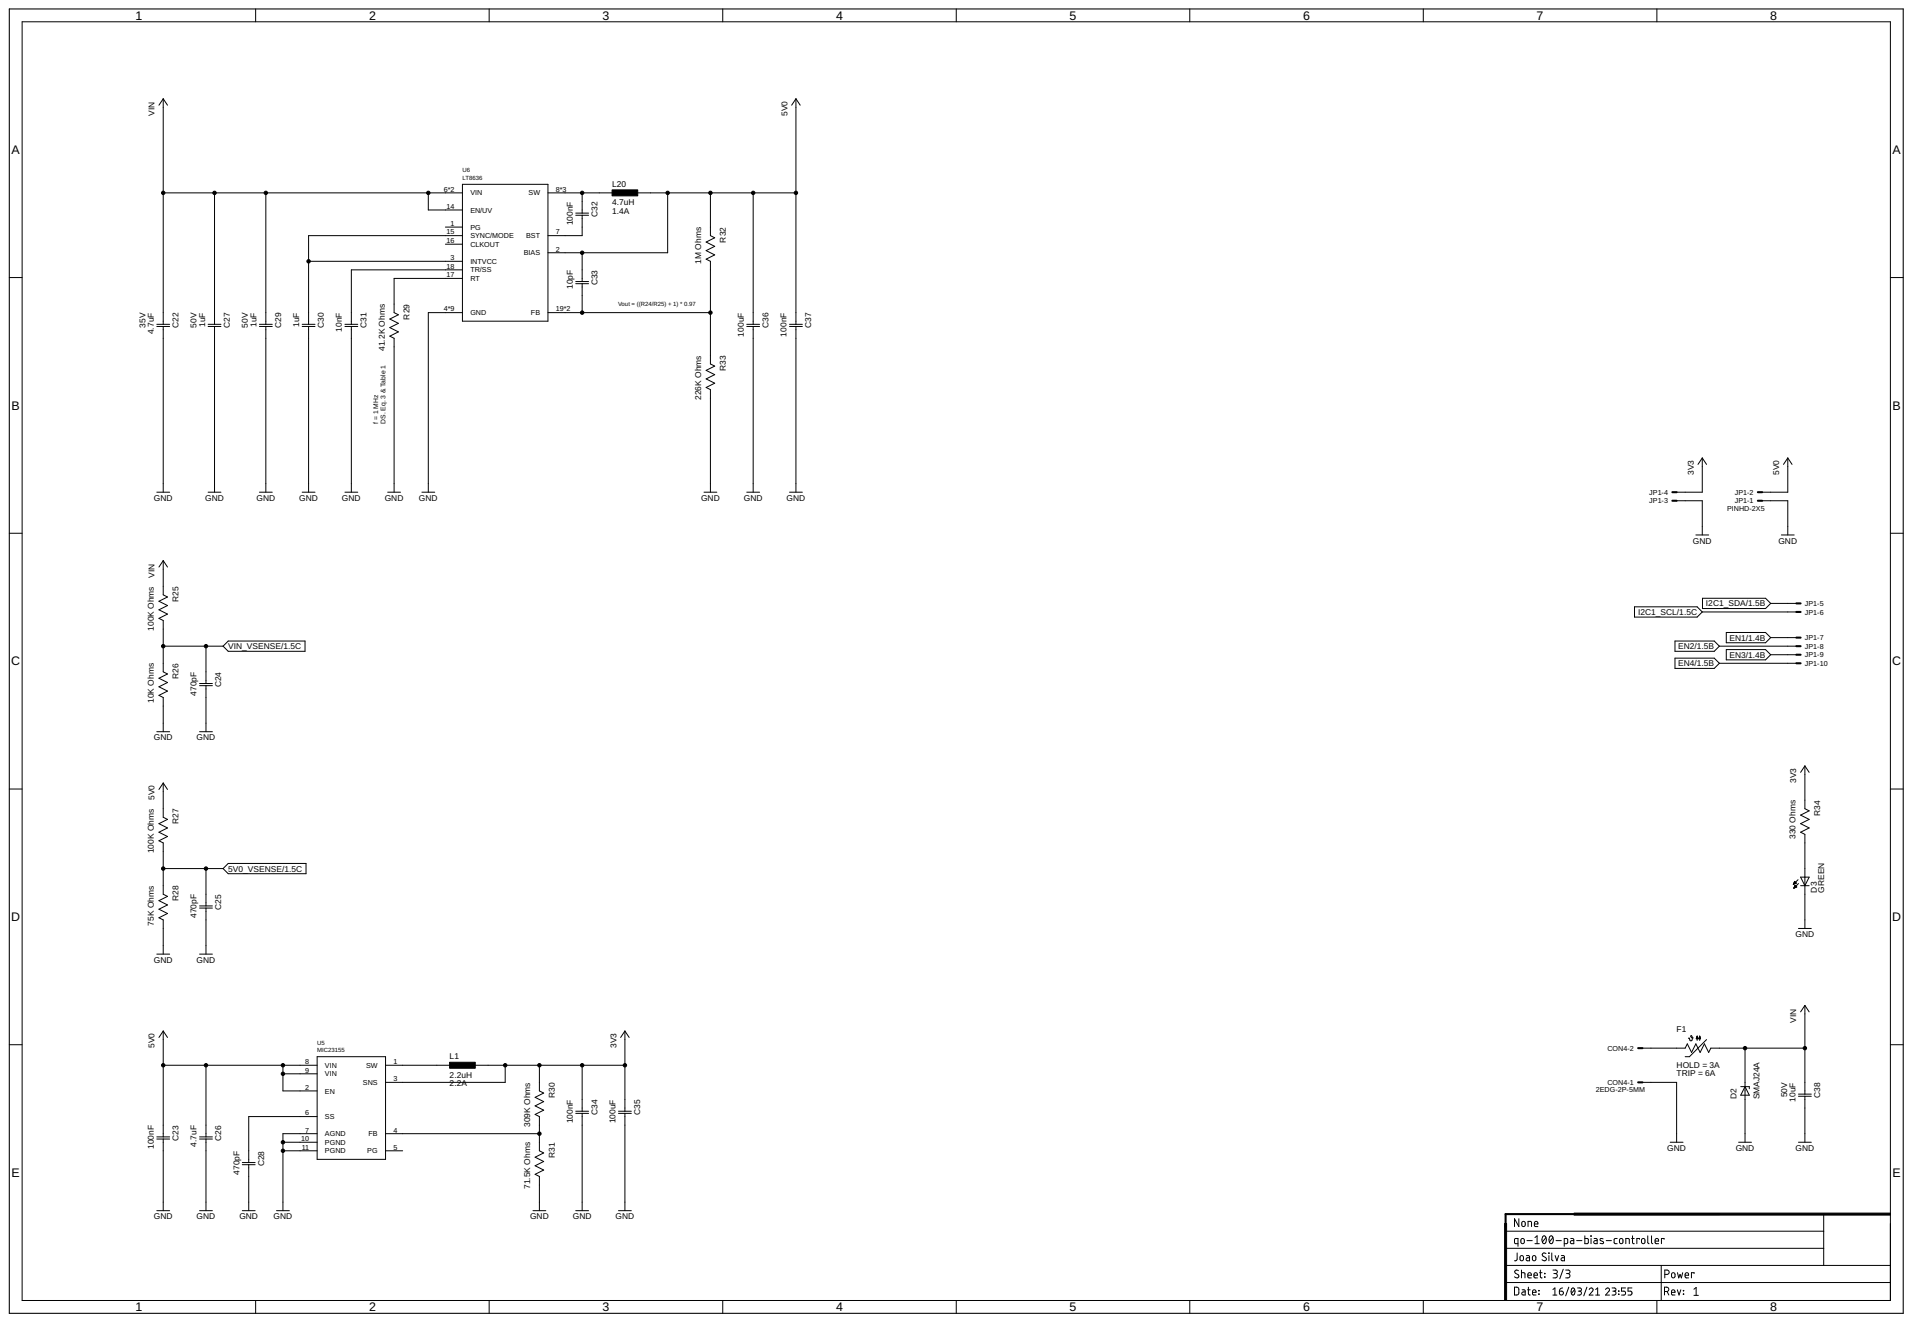
[picture p104: page 3]

f = 1 MHz DS. Eq. 3 & Table 1 Vout = ((R24/R25) + 1) * 0.97 50V 35V 50V HOLD = 3A TRIP = 6A 50 2.2A V 1.4A 1uF 4.7uF GND GND GND GND GND GND 10nF 1uF 41.2K Ohms 100uF GND 100nF 1M Ohms 226K Ohms GND 10pF LT8636 1uF GND VIN 5V0 100nF GND SMAJ24A GND GND VIN 10uF2EDG-2P-5MM GND MIC23155 470pF GND 309K Ohms 71.5K Ohms GND 2.2uH 100nF 100uF GND GND GND 4.7uF 100nF GND GND 5V0 3V3 10K Ohms 100K Ohms GND 470pF GND 75K Ohms 100K Ohms GND 470pF GND 5V0 VIN 330 Ohms GREEN GND 4.7uH PINHD-2X5 GND GND 5V0 3V3 3V3 C29 C22 C31 C30R29 C36 C32 R32 R33 C33 RT 17 EN/UV 14 VIN 6*2 PG 1 BST 7 BIAS 2 SW 8*3 SYNC/MODE 15 TR/SS 18 FB 19*2 GND 4*9 INTVCC 3 CLKOUT 16 U6 C27 C37 D2 F1 C38 CON4-2 CON4-1 AGND 7 PGND 10 PG 5 FB 4 SW 1 VIN 8 EN 2 VIN 9 PGND 11 SS 6 SNS 3 U5 C28 R30 R31 L1 C34 C35 C26 C23 R26 R25 C24 R28 R27 C25 R34 D3 L20 JP1-1 JP1-2 JP1-3 JP1-4 JP1-5 JP1-6 JP1-7 JP1-8 JP1-9 JP1-10 VIN_VSENSE/1.5C 5V0_VSENSE/1.5C EN1/1.4B EN2/1.5B EN3/1.4B EN4/1.5BI2C1_SDA/1.5B I2C1_SCL/1.5C ABCDE 1 2 3 4 5 6 7 8 ABCDE 1 2 3 4 5 6 7 8
