vankxr/qo-100-tools/pcb/pa-tec-controller/qo-100-pa-tec-controller.pdf

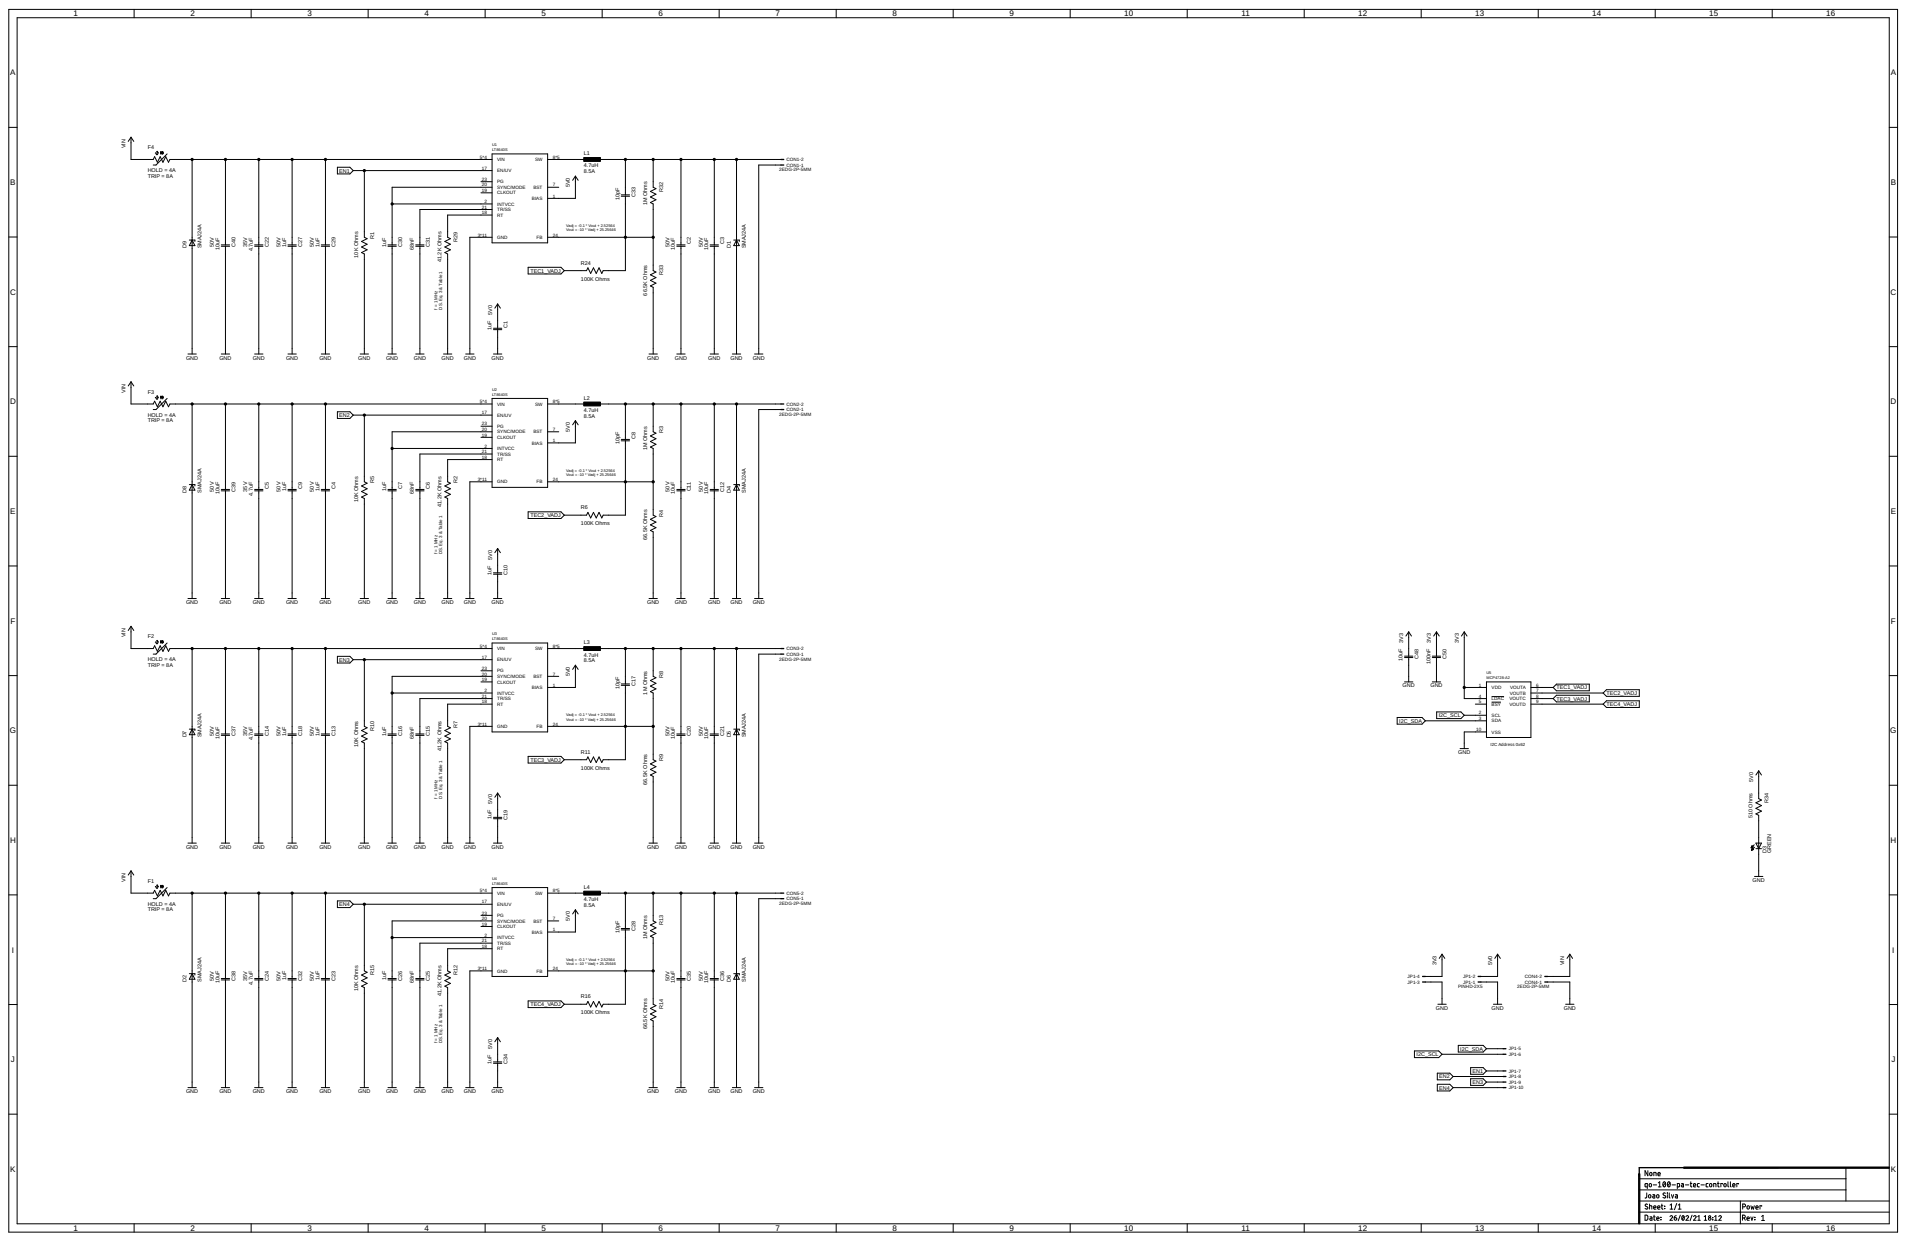
[picture p105: page 1]

f = 1 MHz DS. Eq. 3 & Table 1 Vadj = -0.1 * Vout + 2.52564 Vout = -10 * Vadj + 25.25646 f = 1 MHz DS. Eq. 3 & Table 1 Vadj = -0.1 * Vout + 2.52564 Vout = -10 * Vadj + 25.25646 f = 1 MHz DS. Eq. 3 & Table 1 Vadj = -0.1 * Vout + 2.52564 Vout = -10 * Vadj + 25.25646 I2C Address 0x62 f = 1 MHz DS. Eq. 3 & Table 1 Vadj = -0.1 * Vout + 2.52564 Vout = -10 * Vadj + 25.25646 50V 35V 50V 8.5A 50V 50V 50V 35V 50V 8.5A 50V 50V 50V 35V 50V 8.5A 50V 50V HOLD = 4A TRIP = 8A 50V HOLD = 4A TRIP = 8A 50V HOLD = 4A TRIP = 8A 50V 50V 35V 50V 8.5A 50V 50V HOLD = 4A TRIP = 8A 50V VIN 2EDG-2P-5MM GND 510 Ohms GREEN GND 5V0 PINHD-2X5 GND GND 5V0 3V3 1uF 4.7uF GND GND GND GND GND GND 68nF 1uF 41.2K Ohms GND 1M Ohms 66.5K Ohms GND 10pF 1uF GND 5V0 GND 4.7uH 1uF LT8640S GND 5V0 10K Ohms GND 100K Ohms 10uF 10uF 2EDG-2P-5MM GND SMAJ24A GND 1uF 4.7uF GND GND GND GND GND GND 68nF 1uF 41.2K Ohms GND 1M Ohms 66.5K Ohms GND 10pF 1uF GND 5V0 GND 4.7uH 1uF LT8640S GND 5V0 10K Ohms GND 100K Ohms 10uF 10uF 2EDG-2P-5MM GND SMAJ24A GND 1uF 4.7uF GND GND GND GND GND GND 68nF 1uF 41.2K Ohms GND 1M Ohms 66.5K Ohms GND 10pF 1uF GND VIN 5V0 GND 4.7uH 1uF LT8640S GND 5V0 10K Ohms GND 100K Ohms 10uF 10uF 2EDG-2P-5MM GND SMAJ24A GND GND 100nF GND 10uF GND 3V3 3V3 MCP4728-A2 3V3 10uF SMAJ24A GND GND VIN 10uF SMAJ24A GND GND VIN 10uF SMAJ24A GND GND 1uF 4.7uF GND GND GND GND GND GND 68nF 1uF 41.2K Ohms GND 1M Ohms 66.5K Ohms GND 10pF 1uF GND 5V0 GND 4.7uH 1uF LT8640S GND 5V0 10K Ohms GND 100K Ohms 10uF 10uF 2EDG-2P-5MM GND SMAJ24A GND VIN 10uF SMAJ24A GND GND CON4-2 CON4-1 R34 D3 JP1-1 JP1-2 JP1-3 JP1-4 JP1-5 JP1-6 JP1-7 JP1-8 JP1-9 JP1-10 C4 C5 C6 C7R2 R3 R4 C8 C9 L2 C10 RT 18 EN/UV 17 VIN 5*4 PG 23 BST 7 BIAS 1 SW 8*5 SYNC/MODE 20 TR/SS 21 FB 24 GND 3*11 INTVCC 2 CLKOUT 19 U2 R5 R6 C11 C12 CON2-2 CON2-1 D4 C13 C14 C15 C16R7 R8 R9 C17 C18 L3 C19 RT 18 EN/UV 17 VIN 5*4 PG 23 BST 7 BIAS 1 SW 8*5 SYNC/MODE 20 TR/SS 21 FB 24 GND 3*11 INTVCC 2 CLKOUT 19 U3 R10 R11 C20 C21 CON3-2 CON3-1 D5 C23 C24 C25 C26R12 R13 R14 C28 C32 L4 C34 RT 18 EN/UV 17 VIN 5*4 PG 23 BST 7 BIAS 1 SW 8*5 SYNC/MODE 20 TR/SS 21 FB 24 GND 3*11 INTVCC 2 CLKOUT 19 U4 R15 R16 C35 C36 CON5-2 CON5-1 D6 C50 C48 VDD 1 VSS 10 SCL 2 SDA 3 LDAC 4 VOUTA 6 VOUTB 7 VOUTC 8 VOUTD 9 BSY 5 U5 F1 C38 D2 F2 C37 D7 F3 C39 D8 C29 C22 C31 C30R29 R32 R33 C33 C27 L1 C1 RT 18 EN/UV 17 VIN 5*4 PG 23 BST 7 BIAS 1 SW 8*5 SYNC/MODE 20 TR/SS 21 FB 24 GND 3*11 INTVCC 2 CLKOUT 19 U1 R1 R24 C2 C3 CON1-2 CON1-1 D1 F4 C40 D9 I2C_SDA I2C_SDAI2C_SCLI2C_SCL EN1 EN1 EN2 EN2 EN3 EN3 EN4 EN4 TEC1_VADJ TEC1_VADJ TEC2_VADJ TEC2_VADJ TEC3_VADJ TEC3_VADJ TEC4_VADJ TEC4_VADJ ABCDEFGHIJK 1 2 3 4 5 6 7 8 9 10 11 12 13 14 15 16 ABCDEFGHIJK 1 2 3 4 5 6 7 8 9 10 11 12 13 14 15 16
