vankxr/qo-100-tools/pcb/opi-dock/qo-100-opi-dock.pdf

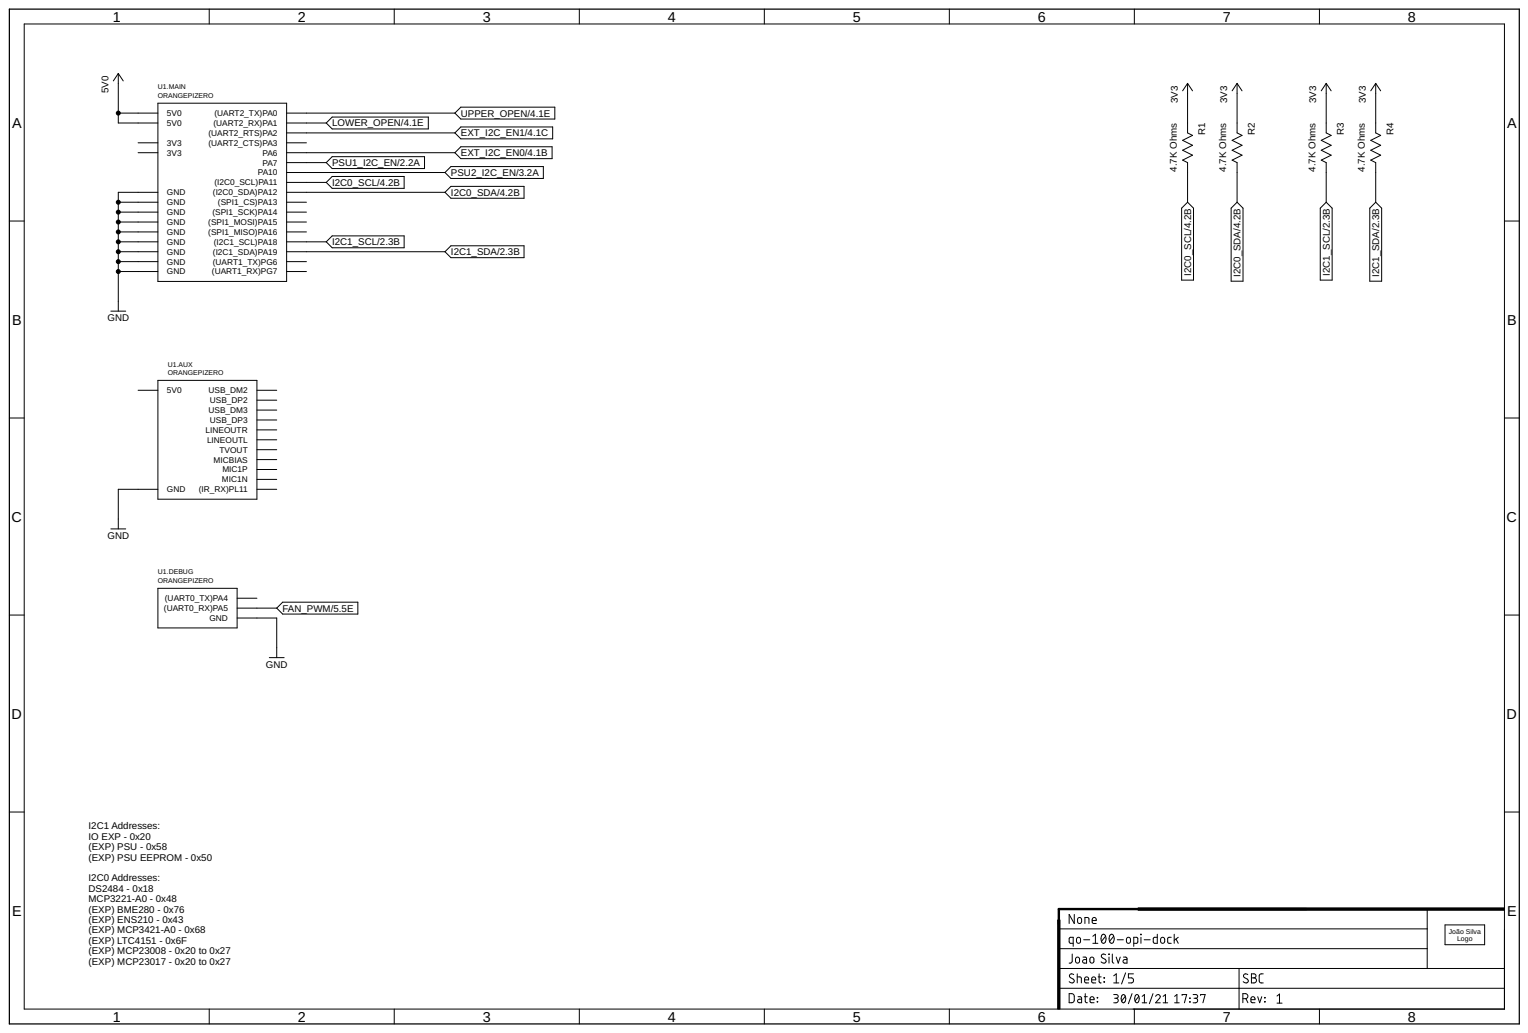
[picture p106: page 1]

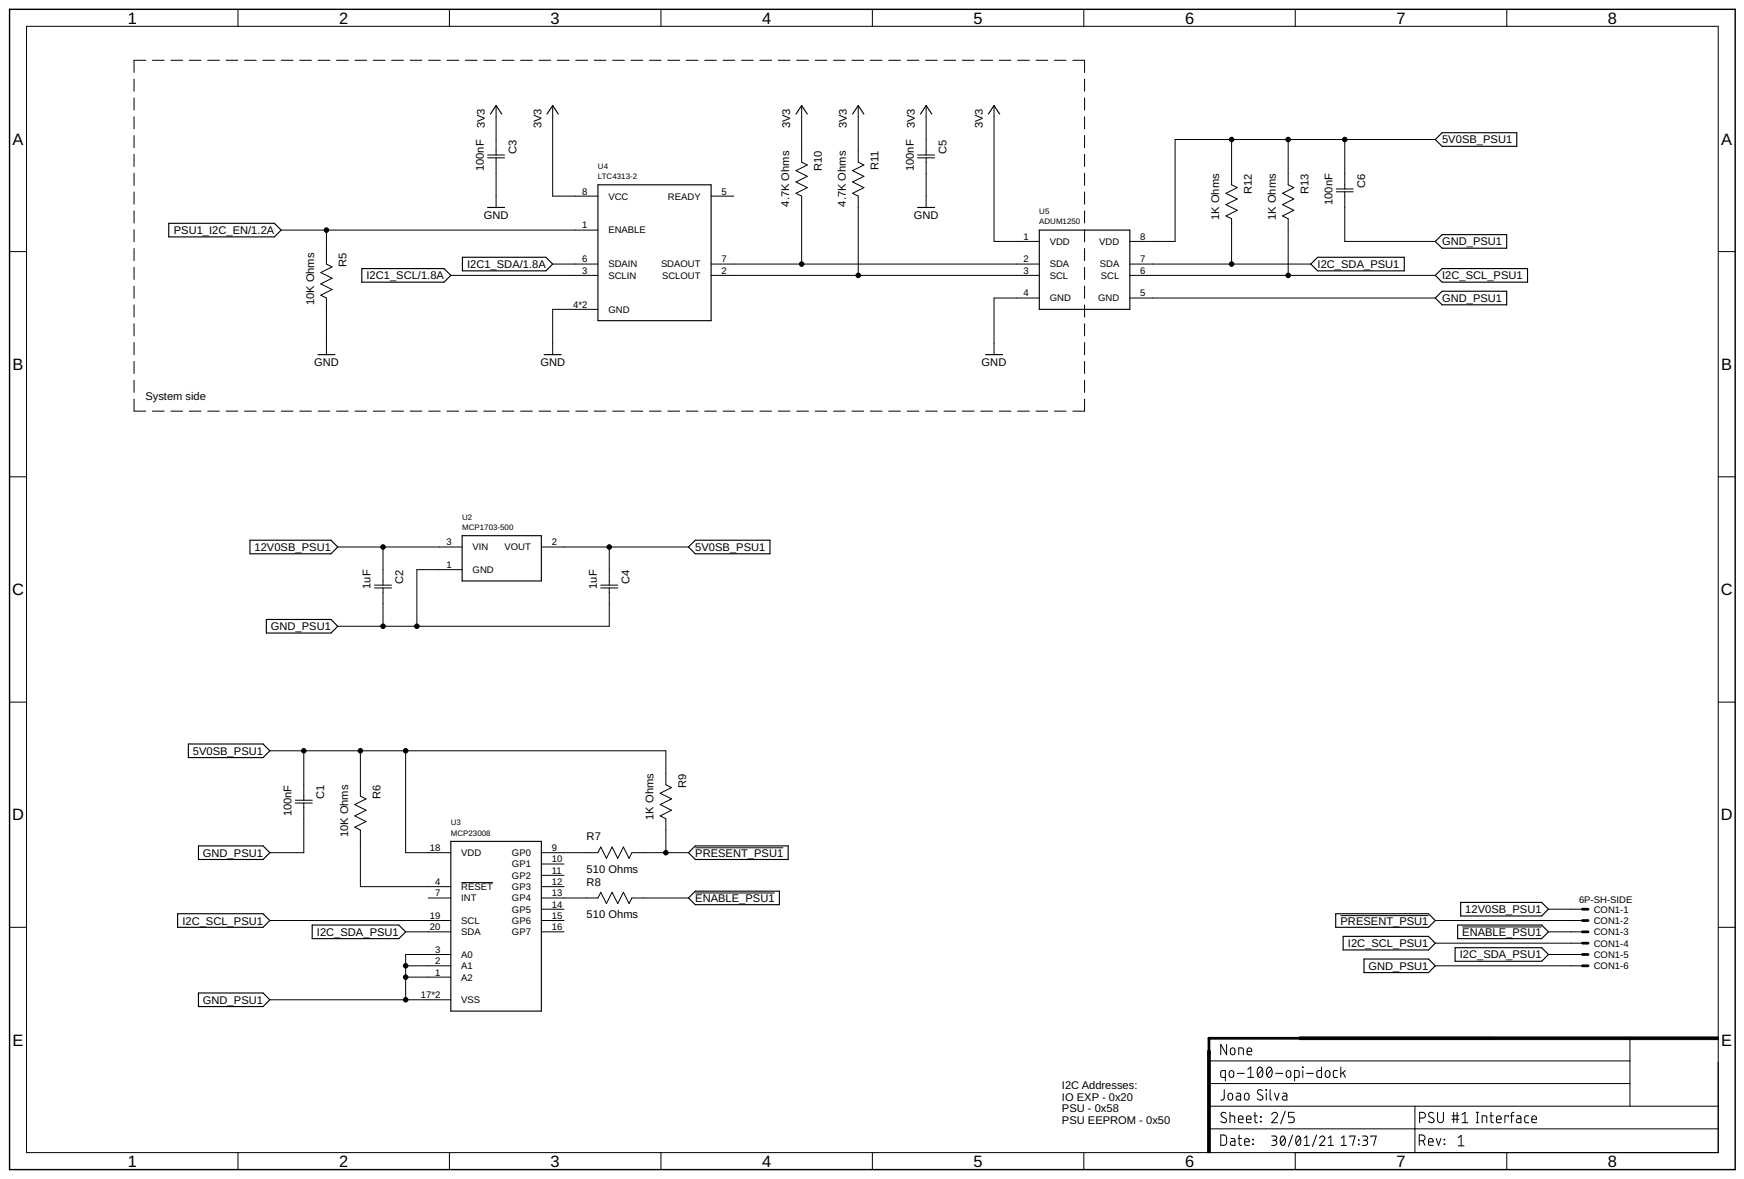
[picture p107: page 2]

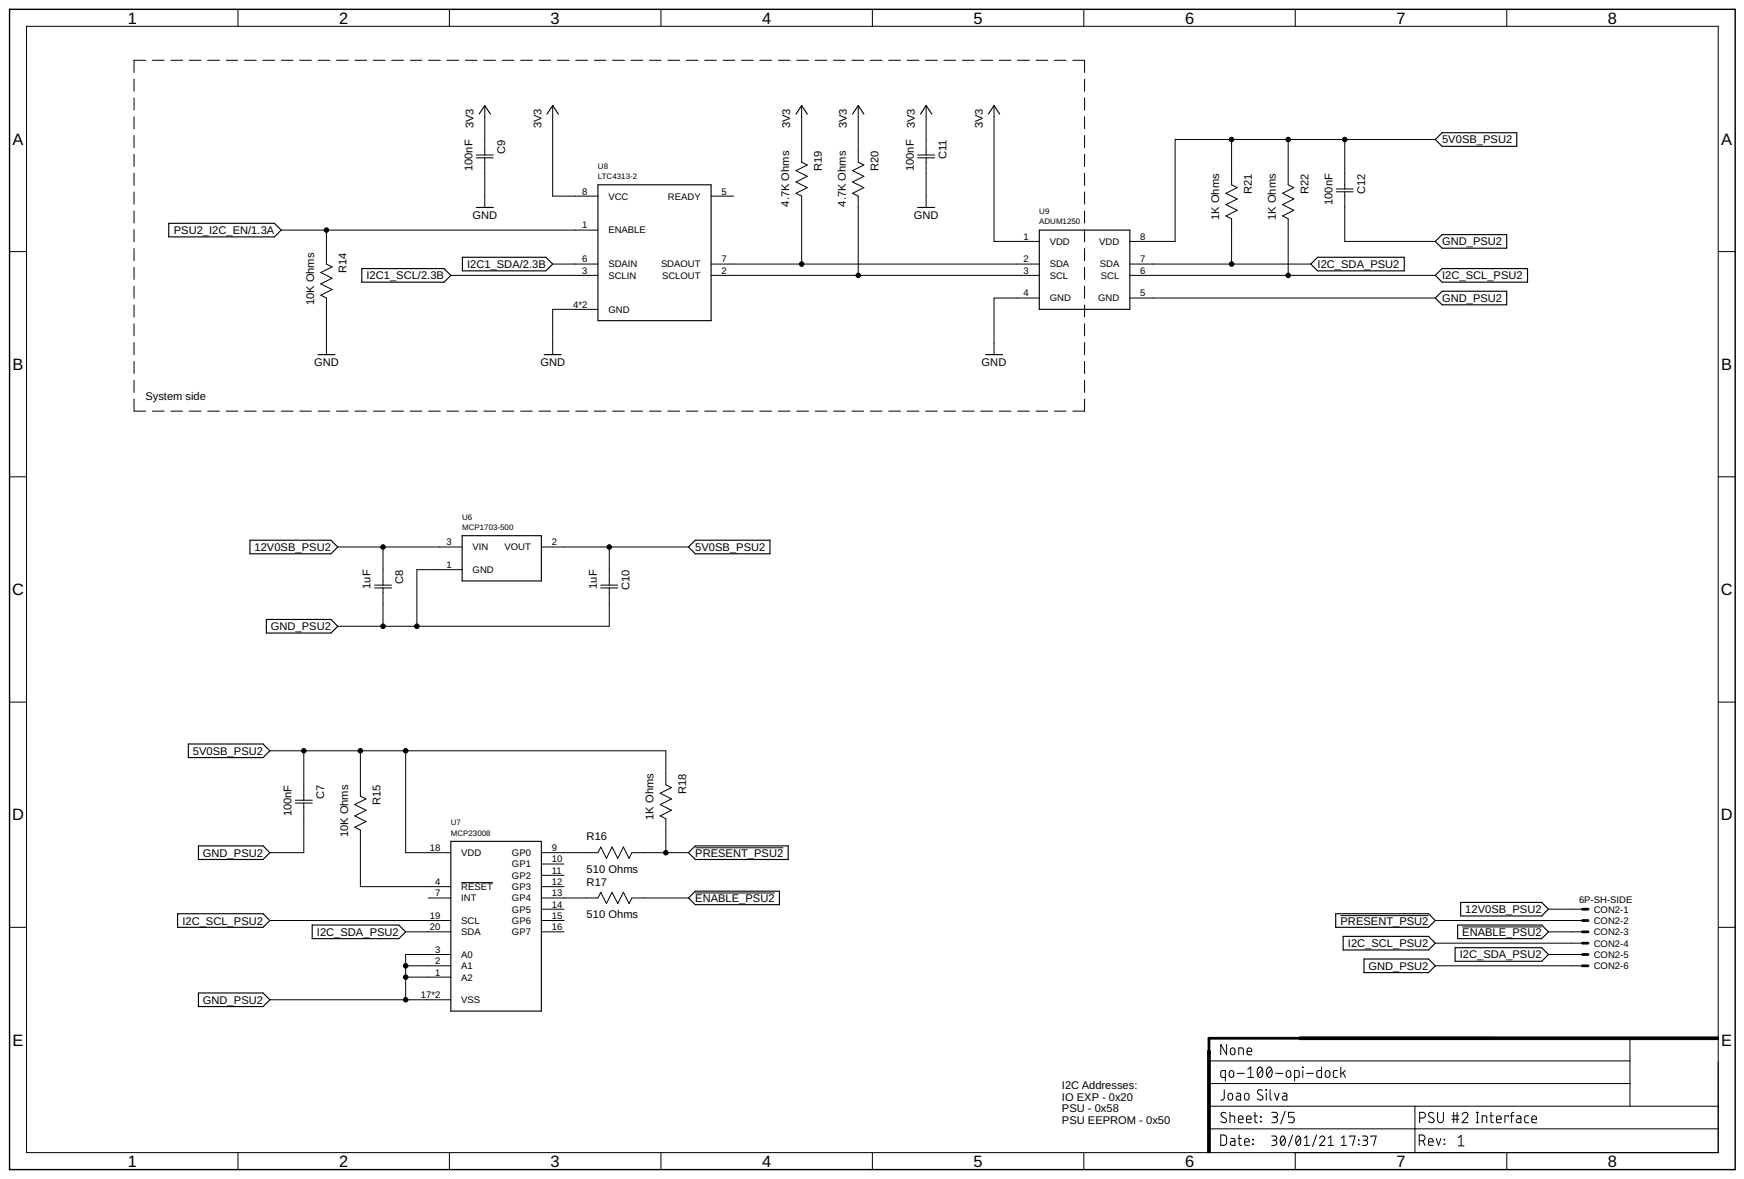
[picture p108: page 3]

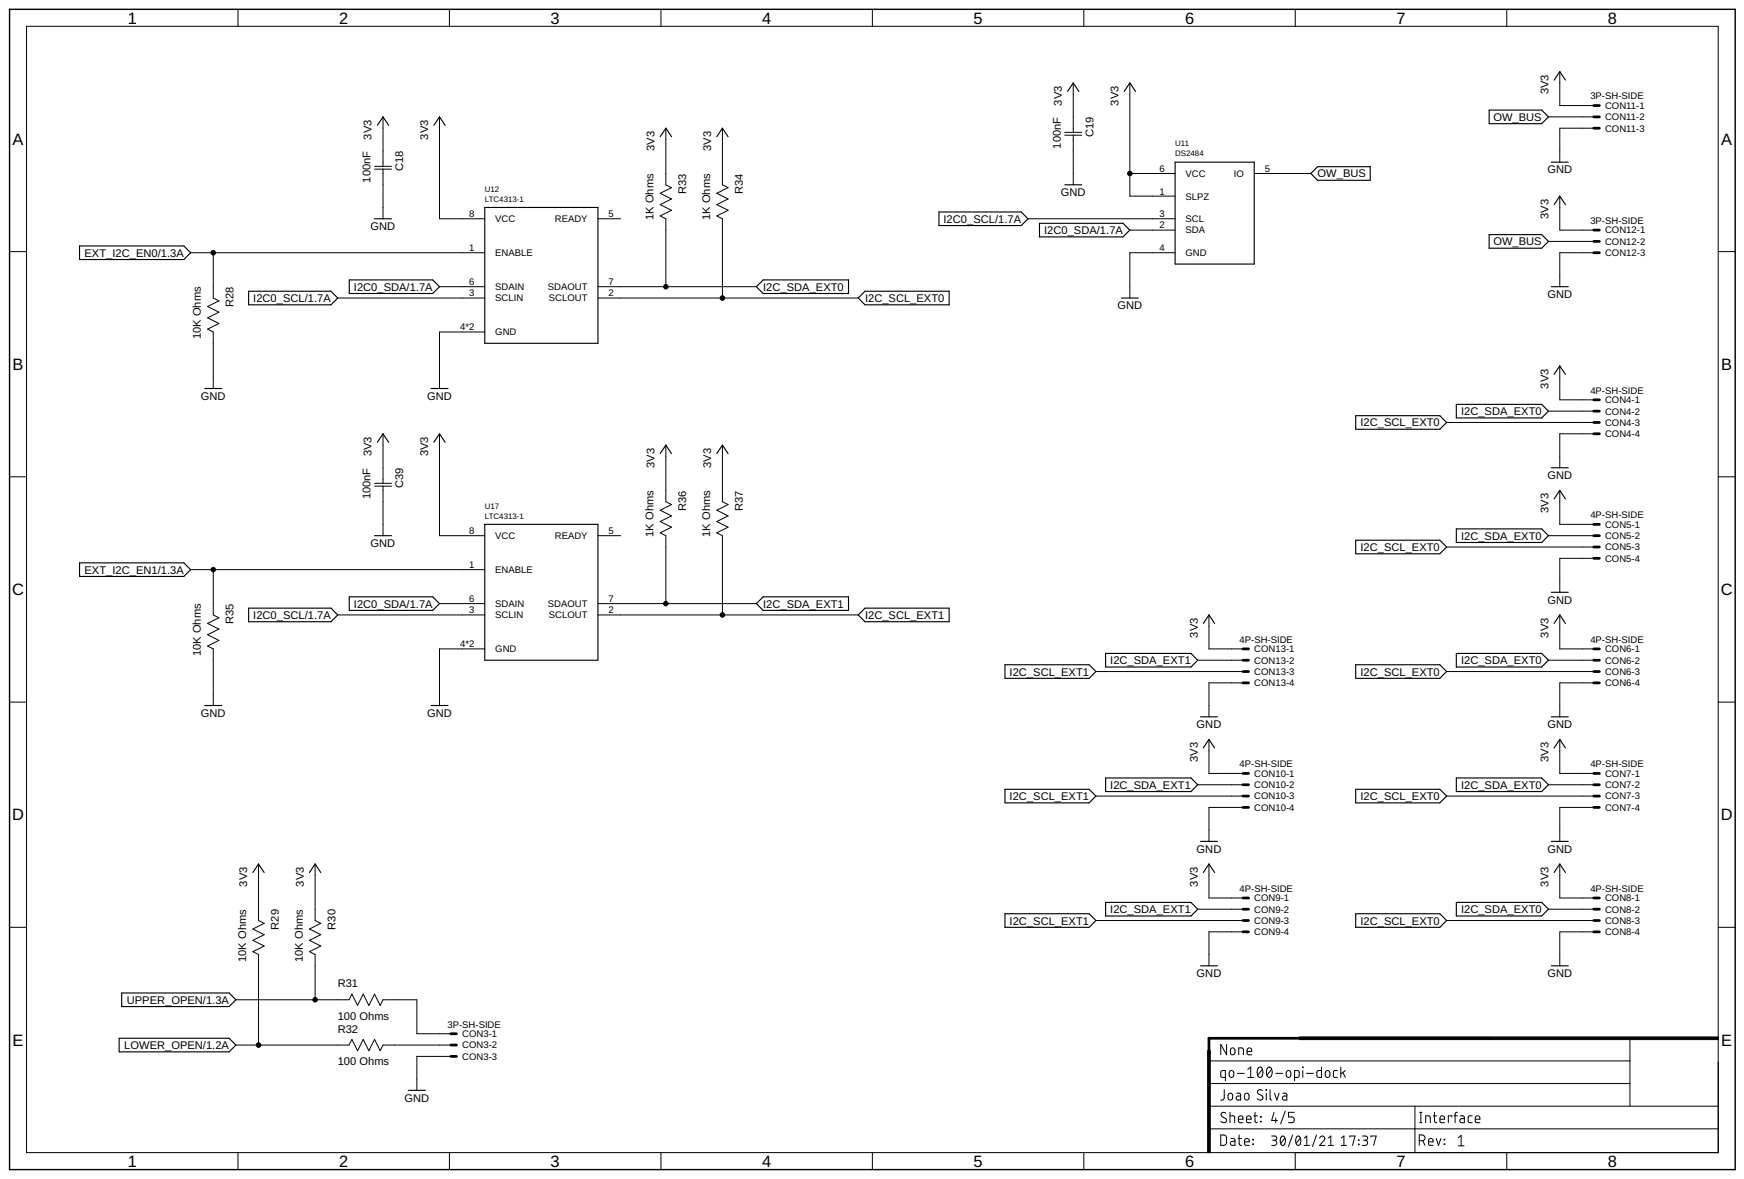
[picture p109: page 4]

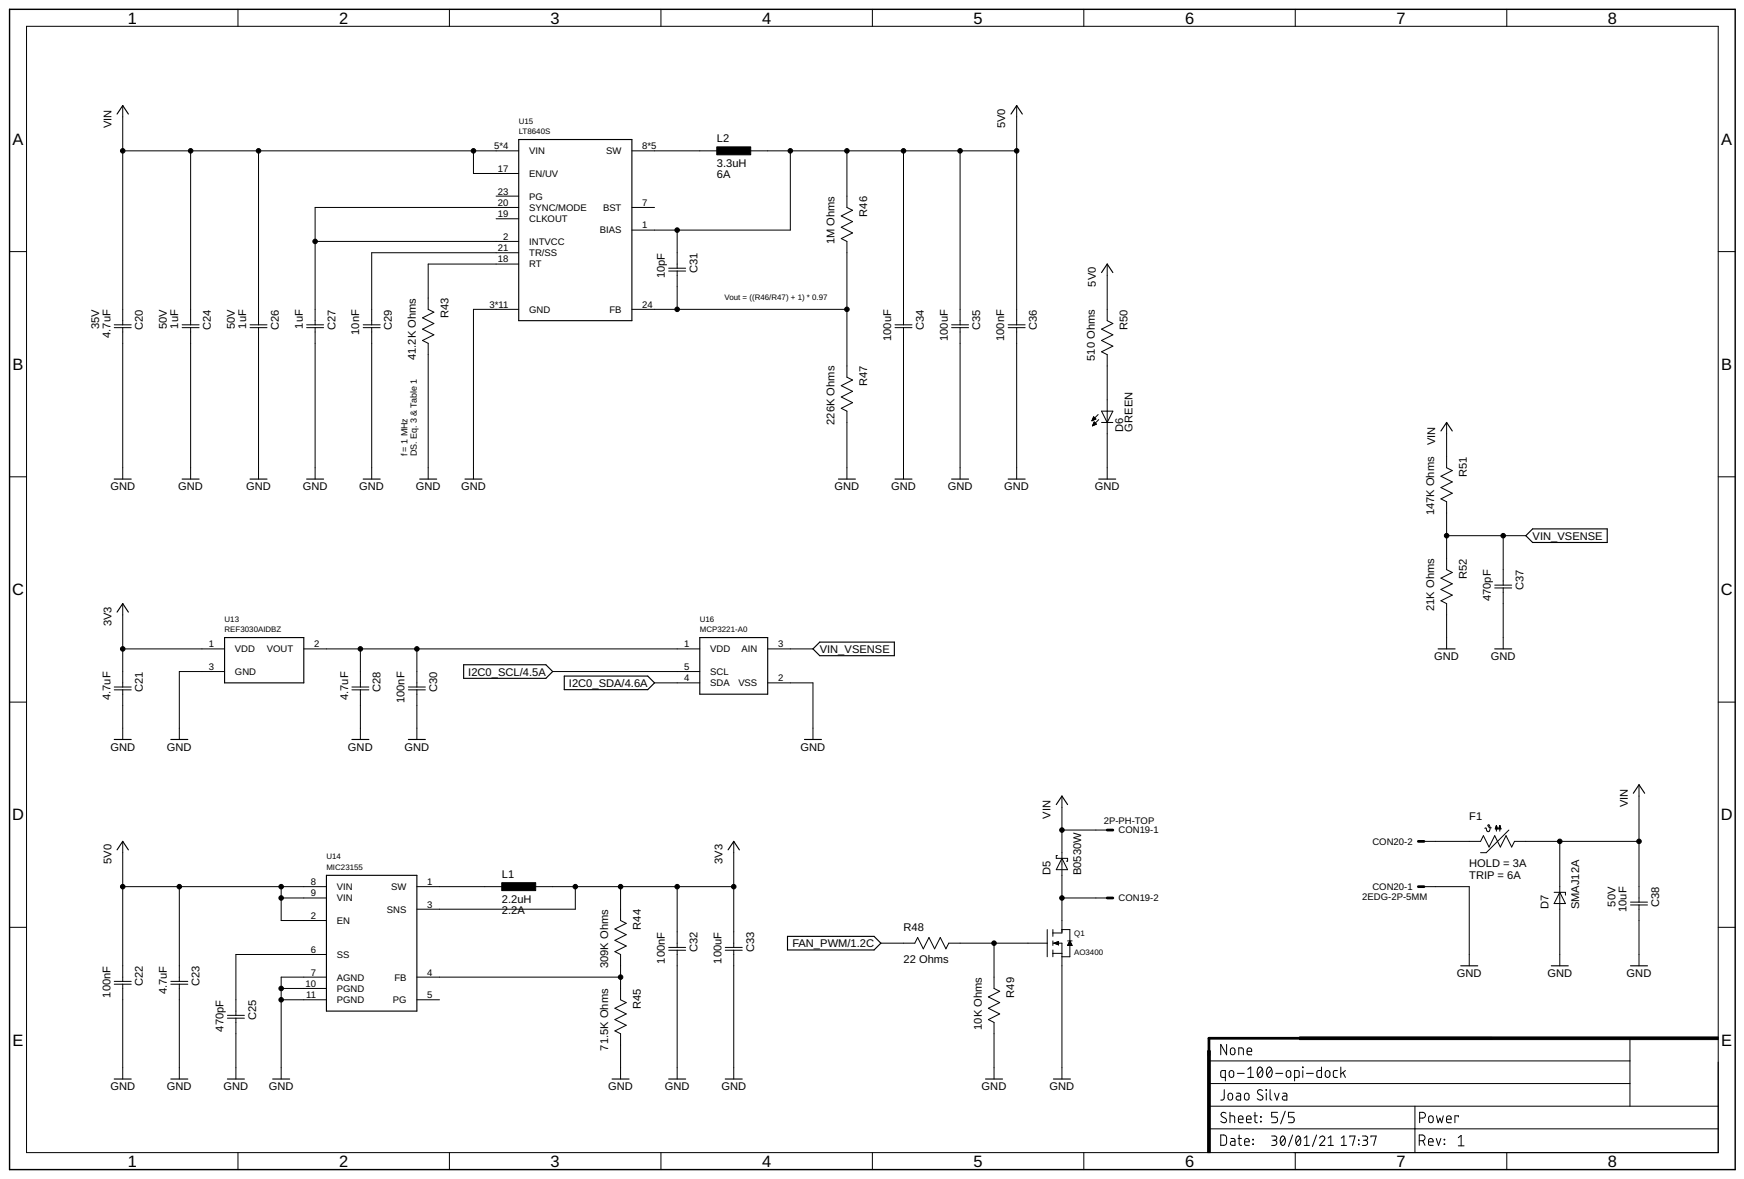
[picture p110: page 5]

4.7uF GND GND GND GND GND GND

f = 1 MHz DS. Eq. 3 & Table 1
