vankxr/qo-100-tools/pcb/relay-controller/qo-100-relay-controller.pdf

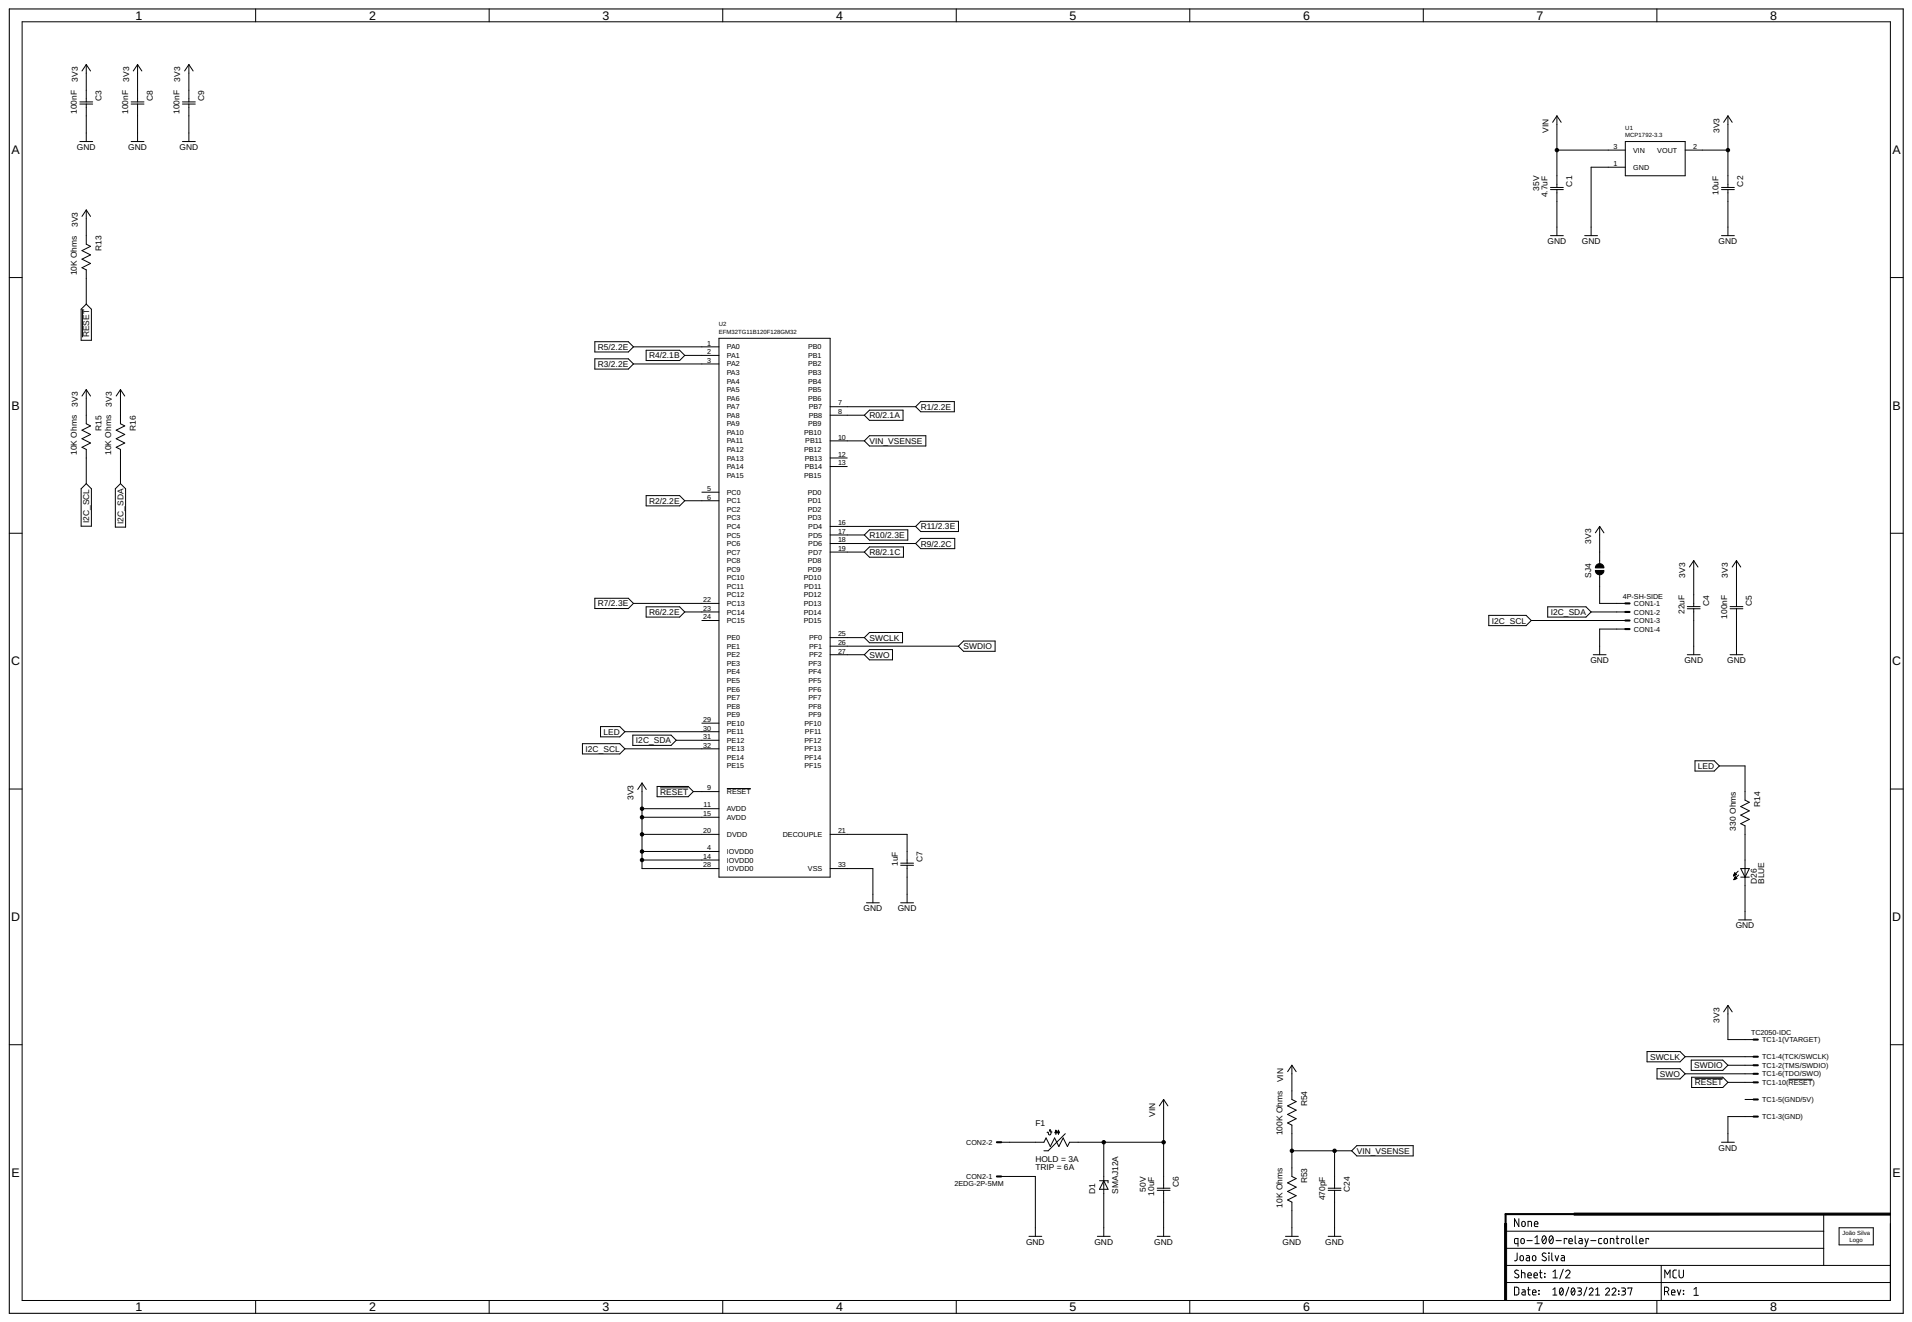
[picture p117: page 1]

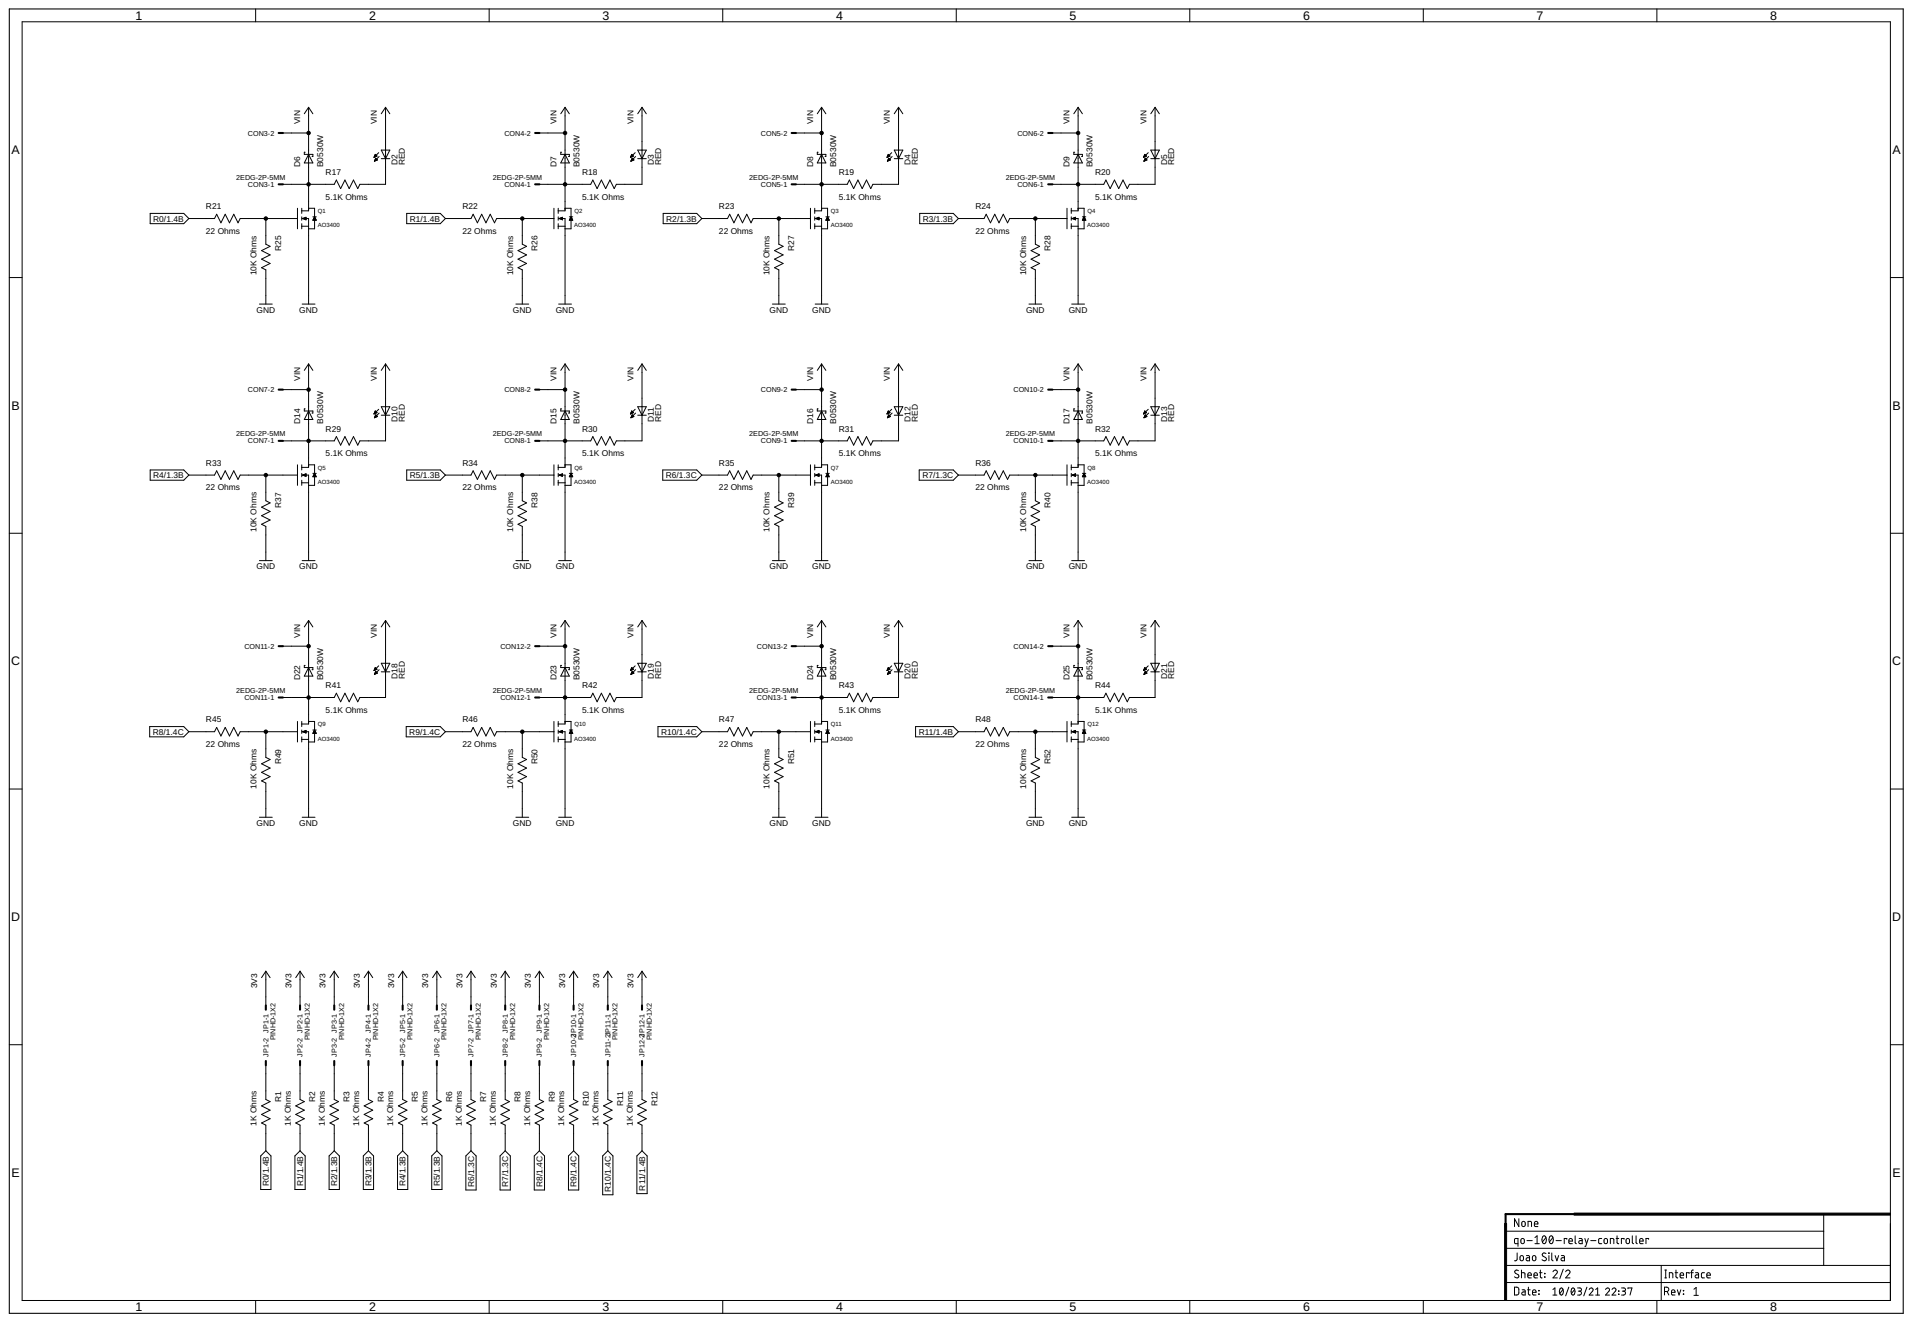
[picture p118: page 2]

PINHD-1X2 3V3 1K Ohms PINHD-1X2 3V3 1K Ohms PINHD-1X2 3V3 1K Ohms PINHD-1X2 3V3 1K Ohms PINHD-1X2 3V3 1K Ohms PINHD-1X2 3V3 1K Ohms PINHD-1X2 3V3 1K Ohms PINHD-1X2 3V3 1K Ohms PINHD-1X2 3V3 1K Ohms PINHD-1X2 3V3 1K Ohms PINHD-1X2 3V3 1K Ohms PINHD-1X2 3V3 1K Ohms
