vankxr/qo-100-tools/pcb/env-sensors/qo-100-env-sensors.pdf

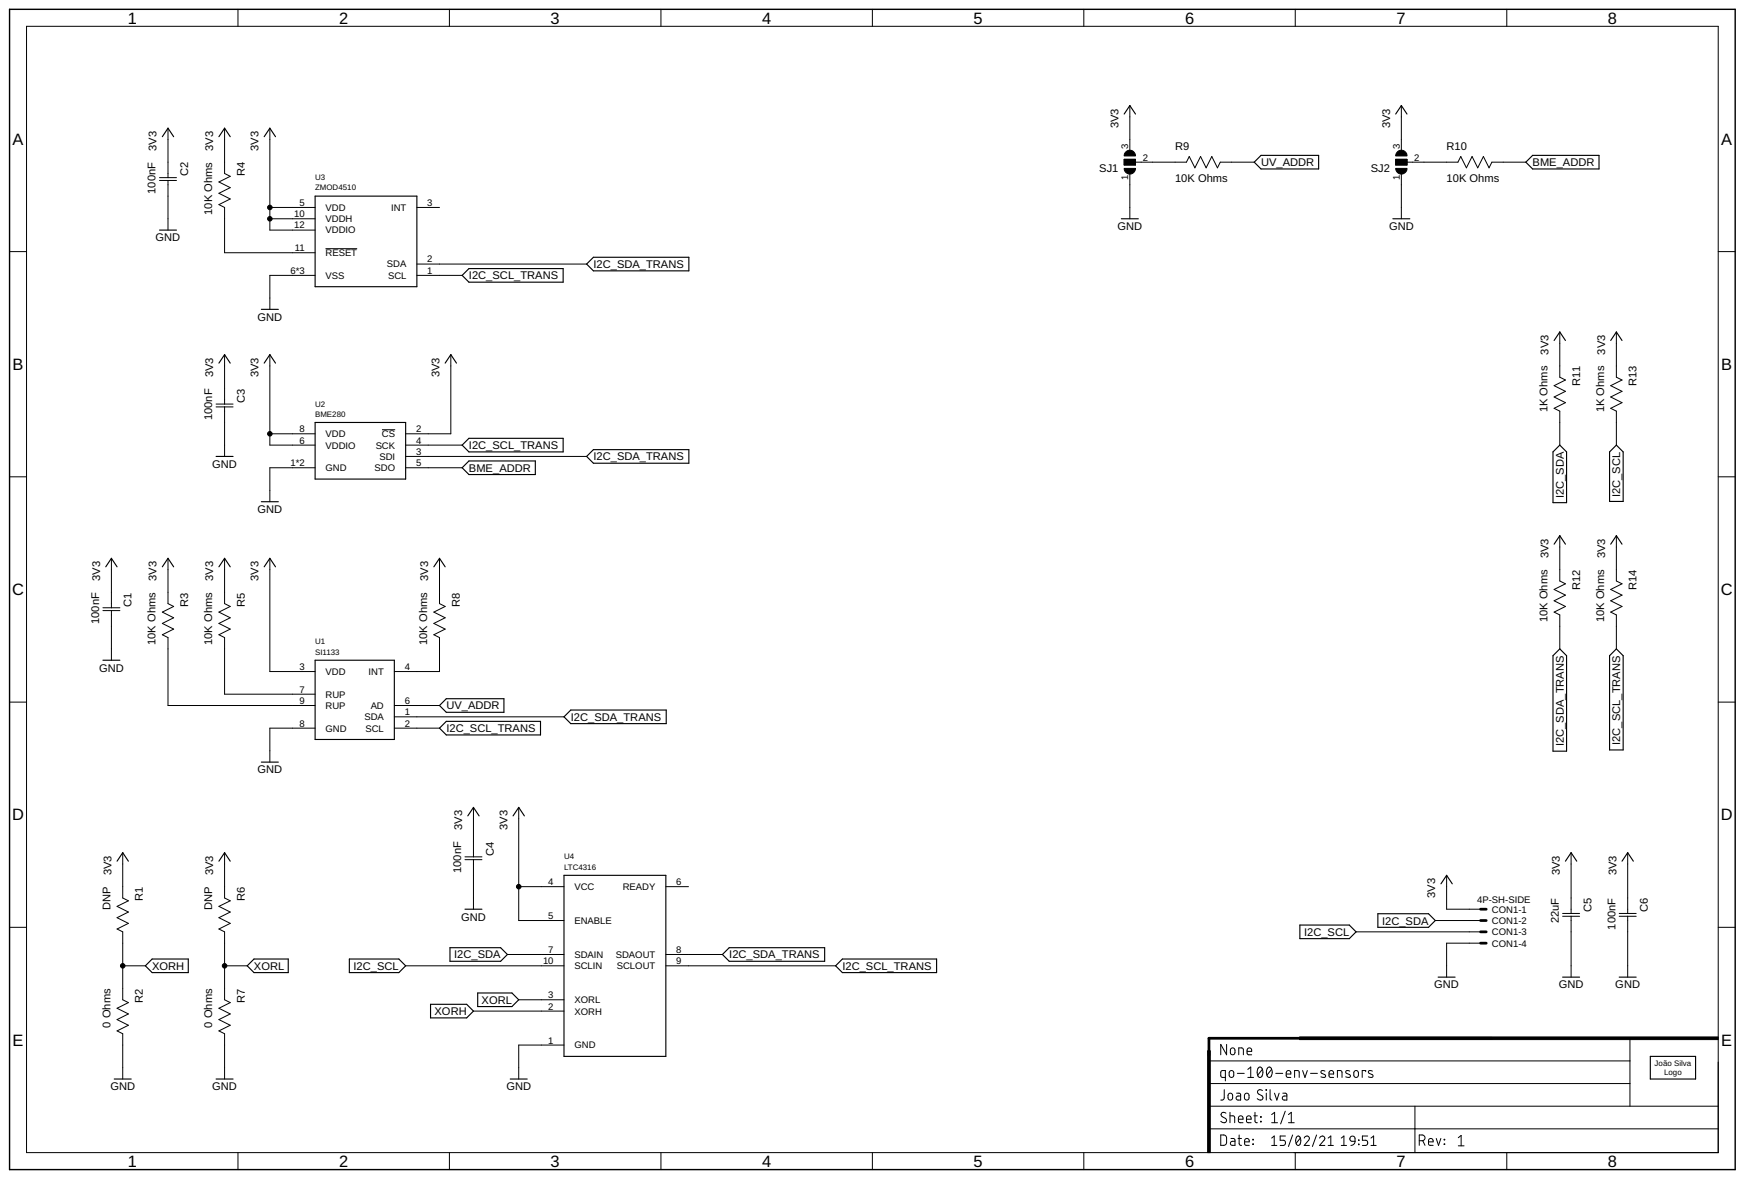
[picture p119: page 1]
