vankxr/qo-100-tools/pcb/digital-rf-power-meter/qo-100-digital-rf-power-meter.pdf

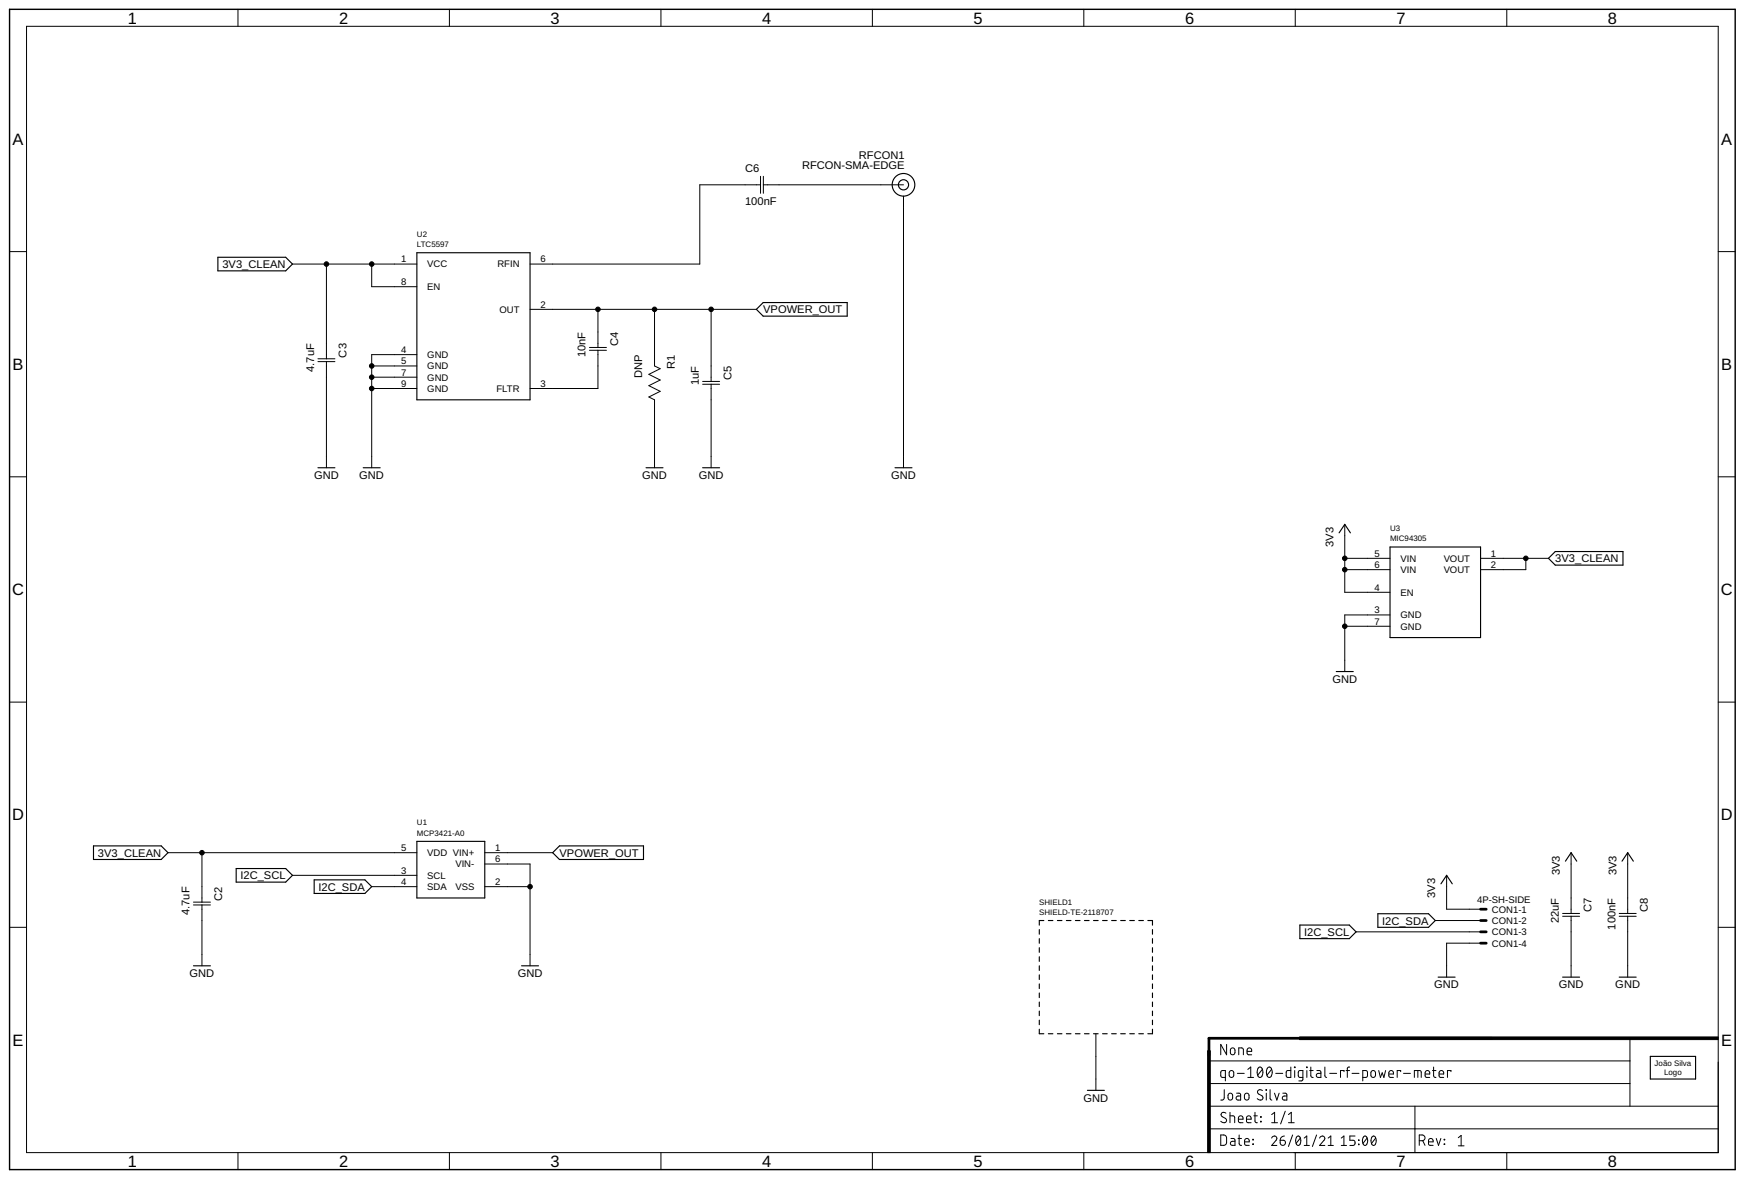
[picture p120: page 1]
