vankxr/qo-100-tools/pcb/digital-power-meter/qo-100-digital-power-meter.pdf

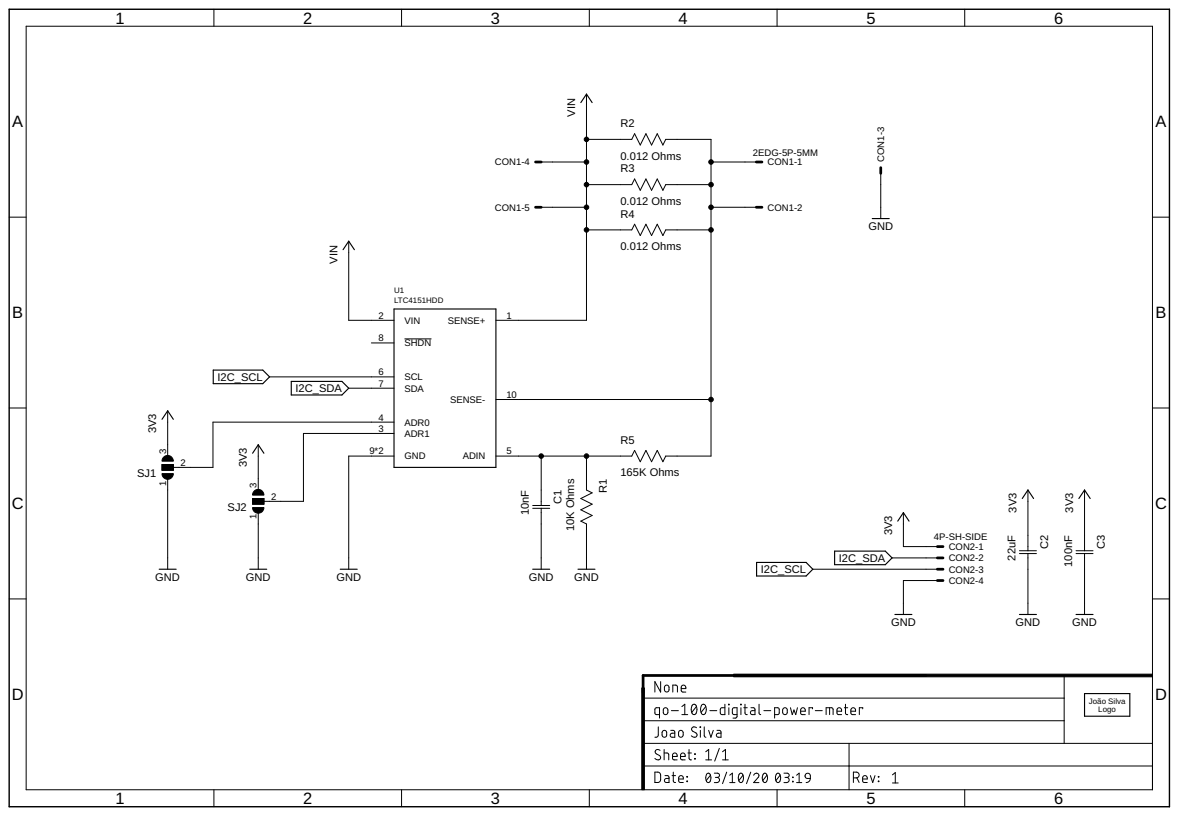
[picture p121: page 1]
