vankxr/qo-100-tools/pcb/directional-couplers/qo-100-directional-coupler-2G4-20dB.pdf

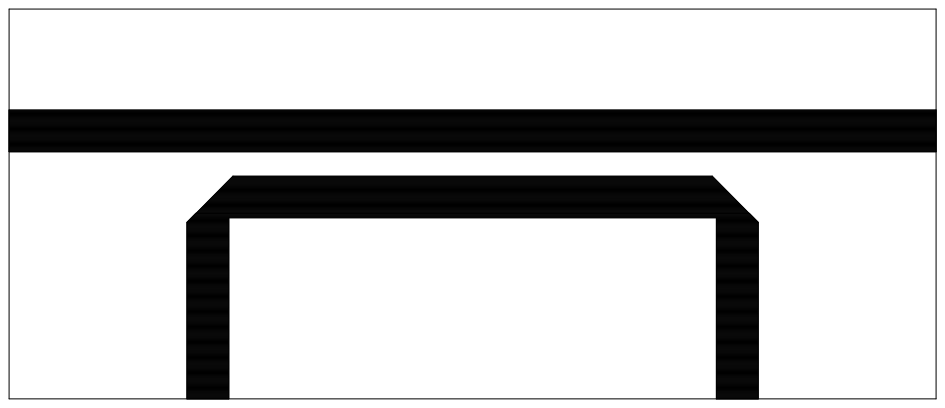
[picture p122: page 1]
