vankxr/qo-100-tools/pcb/directional-couplers/qo-100-directional-coupler-2G4-35dB.pdf

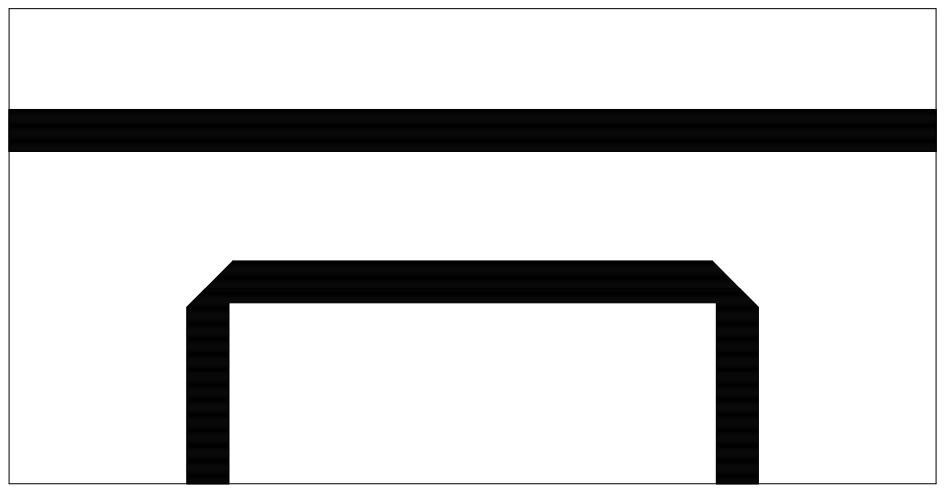
[picture p123: page 1]
