vankxr/qo-100-tools/docs/pa/BLC2425M9LS250_ref_pcb_scale.pdf

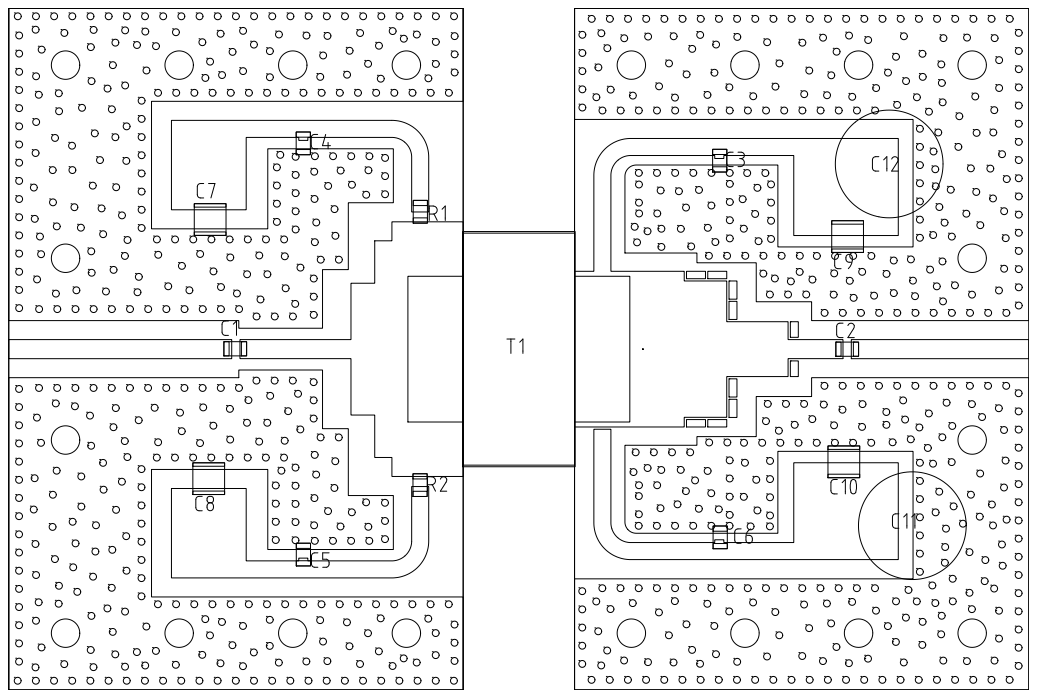
[picture p124: page 1]
