vankxr/qo-100-tools/pcb/generic-filter/qo-100-generic-filter.pdf

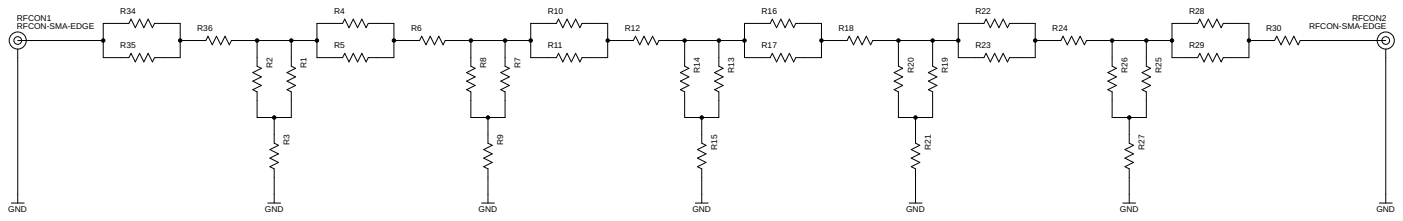
[picture p125: page 1]
