vankxr/qo-100-tools/pcb/env-sensors/qo-100-env-sensors.brd

## EAGLE design pcb/env-sensors/qo-100-env-sensors.brd (2021-02-22)

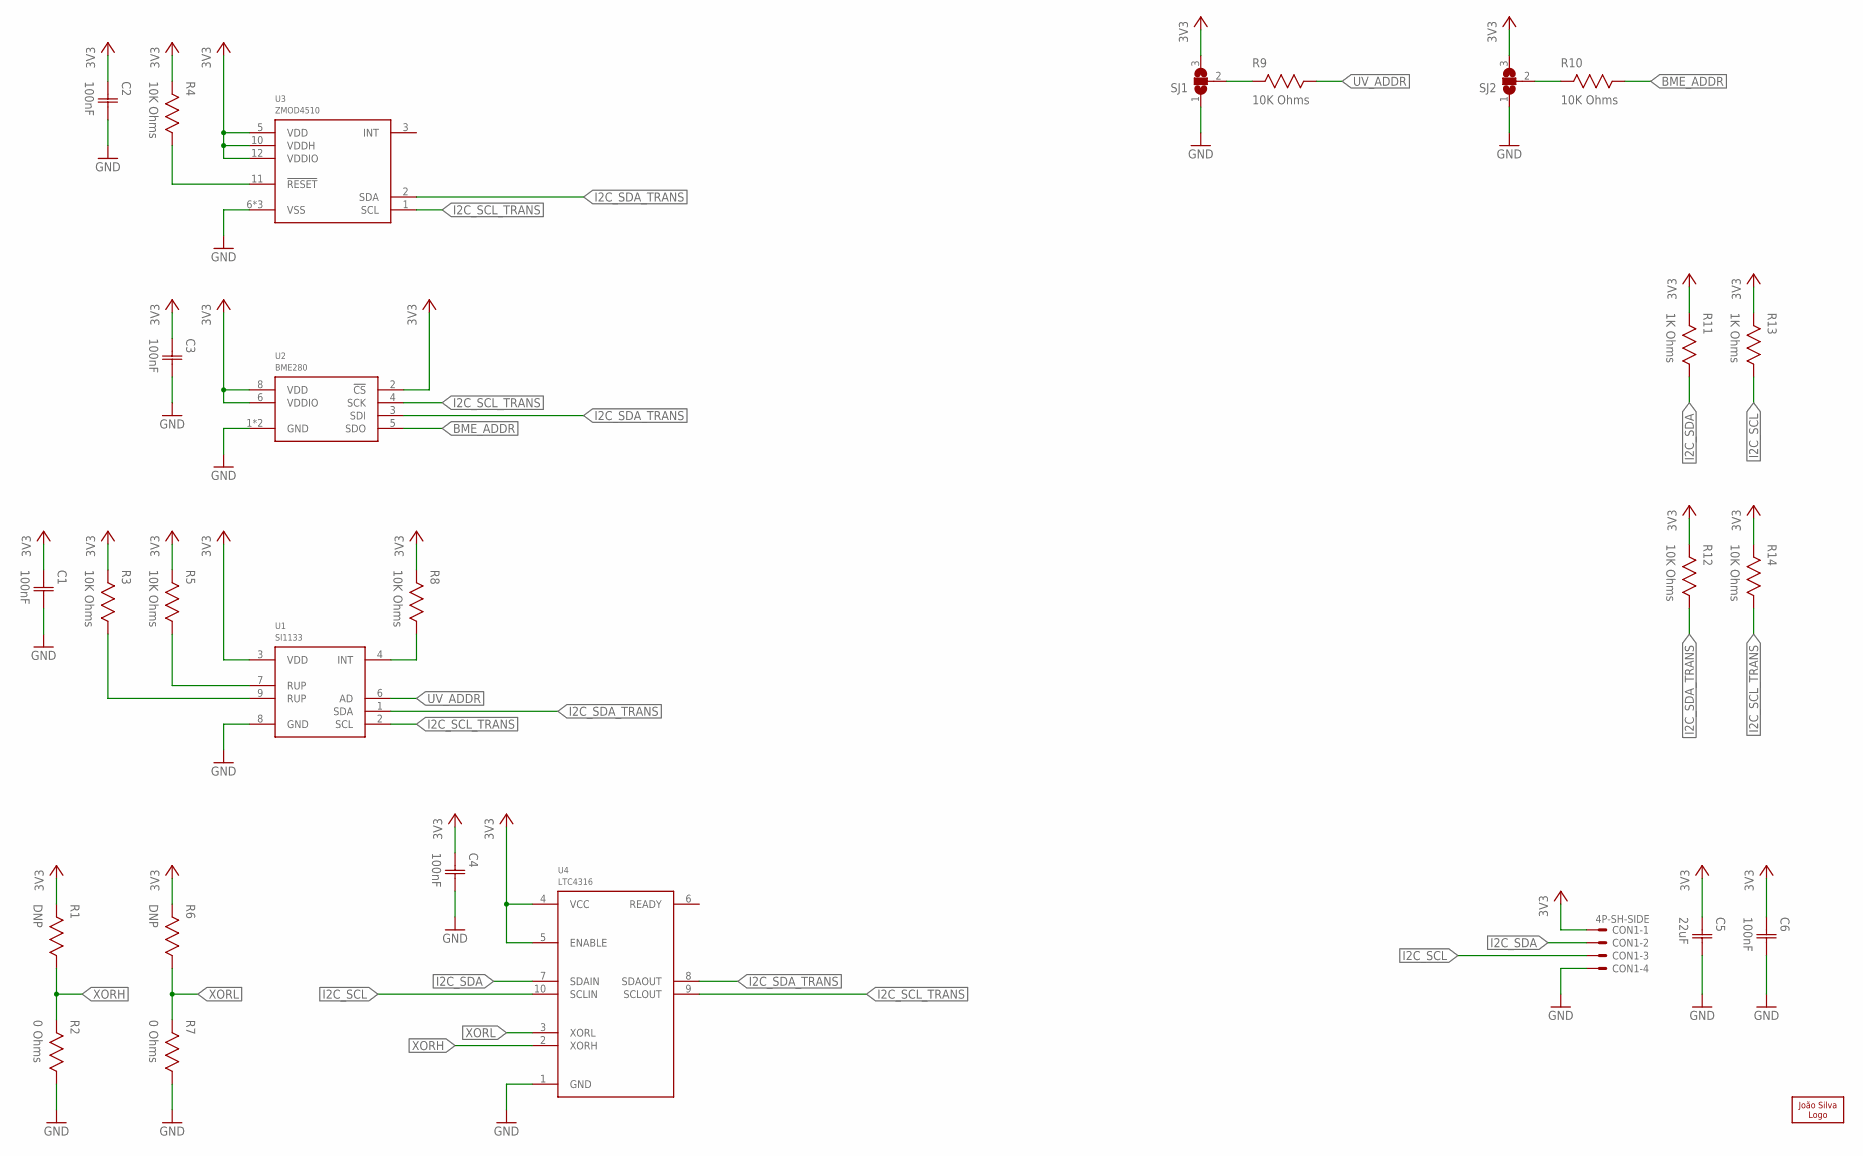
[picture p178: schematic qo-100-env-sensors.sch]

Parts:
C1, C2, C3, C4, C6: 100nF; CAP0603
C5: 22uF; CAP1206
CON1: 4P-SH-SIDE; SH-04-SIDE
LOGO1: JS-5MM; JS_5MM
R1, R6: DNP; RES0603
R2, R7: 0 Ohms; RES0603
R3, R4, R5, R8, R9, R10, R12, R14: 10K Ohms; RES0603
R11, R13: 1K Ohms; RES0603
SJ1, SJ2: SJ2S; SJ2_S
U1: SI1133; DFN10
U2: BME280
U3: ZMOD4510; LGA12
U4: LTC4316; MSOP10

Connections:
3V3: C1.1 (C1), C2.1 (C1), C3.1 (C1), C4.1 (C1), C5.1 (C1), C6.1 (C1), CON1.1, R1.2, R3.2, R4.2, R5.2, R6.2, R8.2, R11.2, R12.2, R13.2, R14.2, SJ1.3, SJ2.3, U1.3 (VDD), U2.2 (!CS), U2.6 (VDDIO), U2.8 (VDD), U3.5 (VDD), U3.10 (VDDH), U3.12 (VDDIO), U4.4 (VCC), U4.5 (ENABLE)
BME_ADDR: R10.1, U2.5 (SDO)
GND: C1.2 (C2), C2.2 (C2), C3.2 (C2), C4.2 (C2), C5.2 (C2), C6.2 (C2), CON1.4, R2.1, R7.1, SJ1.1, SJ2.1, U1.8 (GND), U2.1 (GND), U2.7 (GND), U3.6 (VSS), U3.7 (VSS), U3.9 (VSS), U4.1 (GND)
I2C_SCL: CON1.3, R13.1, U4.10 (SCLIN)
I2C_SCL_TRANS: R14.1, U1.2 (SCL), U2.4 (SCK), U3.1 (SCL), U4.9 (SCLOUT)
I2C_SDA: CON1.2, R11.1, U4.7 (SDAIN)
I2C_SDA_TRANS: R12.1, U1.1 (SDA), U2.3 (SDI), U3.2 (SDA), U4.8 (SDAOUT)
unnamed: R4.1, U3.11 (!RESET)
unnamed: R3.1, U1.9 (RUP)
unnamed: R8.1, U1.4 (INT)
unnamed: R10.2, SJ2.2
unnamed: R9.2, SJ1.2
unnamed: R5.1, U1.7 (RUP)
UV_ADDR: R9.1, U1.6 (AD)
XORH: R1.1, R2.2, U4.2 (XORH)
XORL: R6.1, R7.2, U4.3 (XORL)

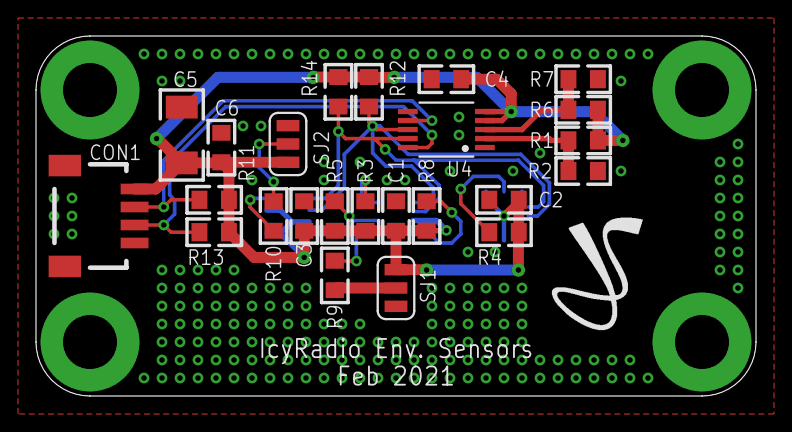
[picture p179: board qo-100-env-sensors.brd from above]

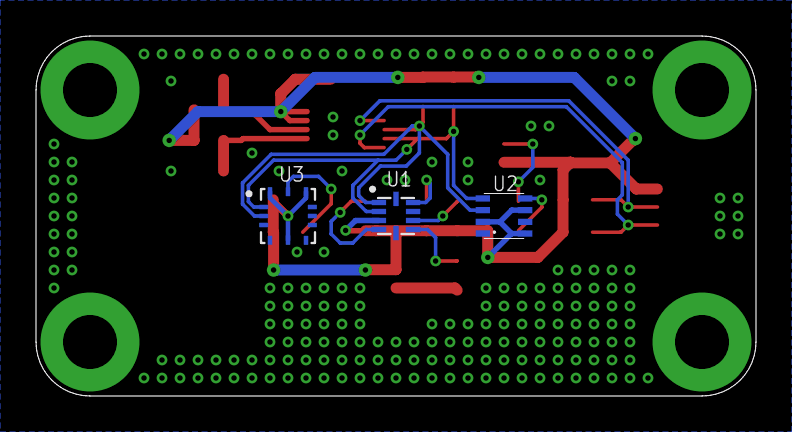
[picture p180: board qo-100-env-sensors.brd from below]

Board: 2 copper layers, 40.0 x 20.0 mm, 28 parts (3 on the bottom side), 16 nets.
