vankxr/qo-100-tools/pcb/opi-dock/qo-100-opi-dock.brd

## EAGLE design pcb/opi-dock/qo-100-opi-dock.brd (2021-02-02)

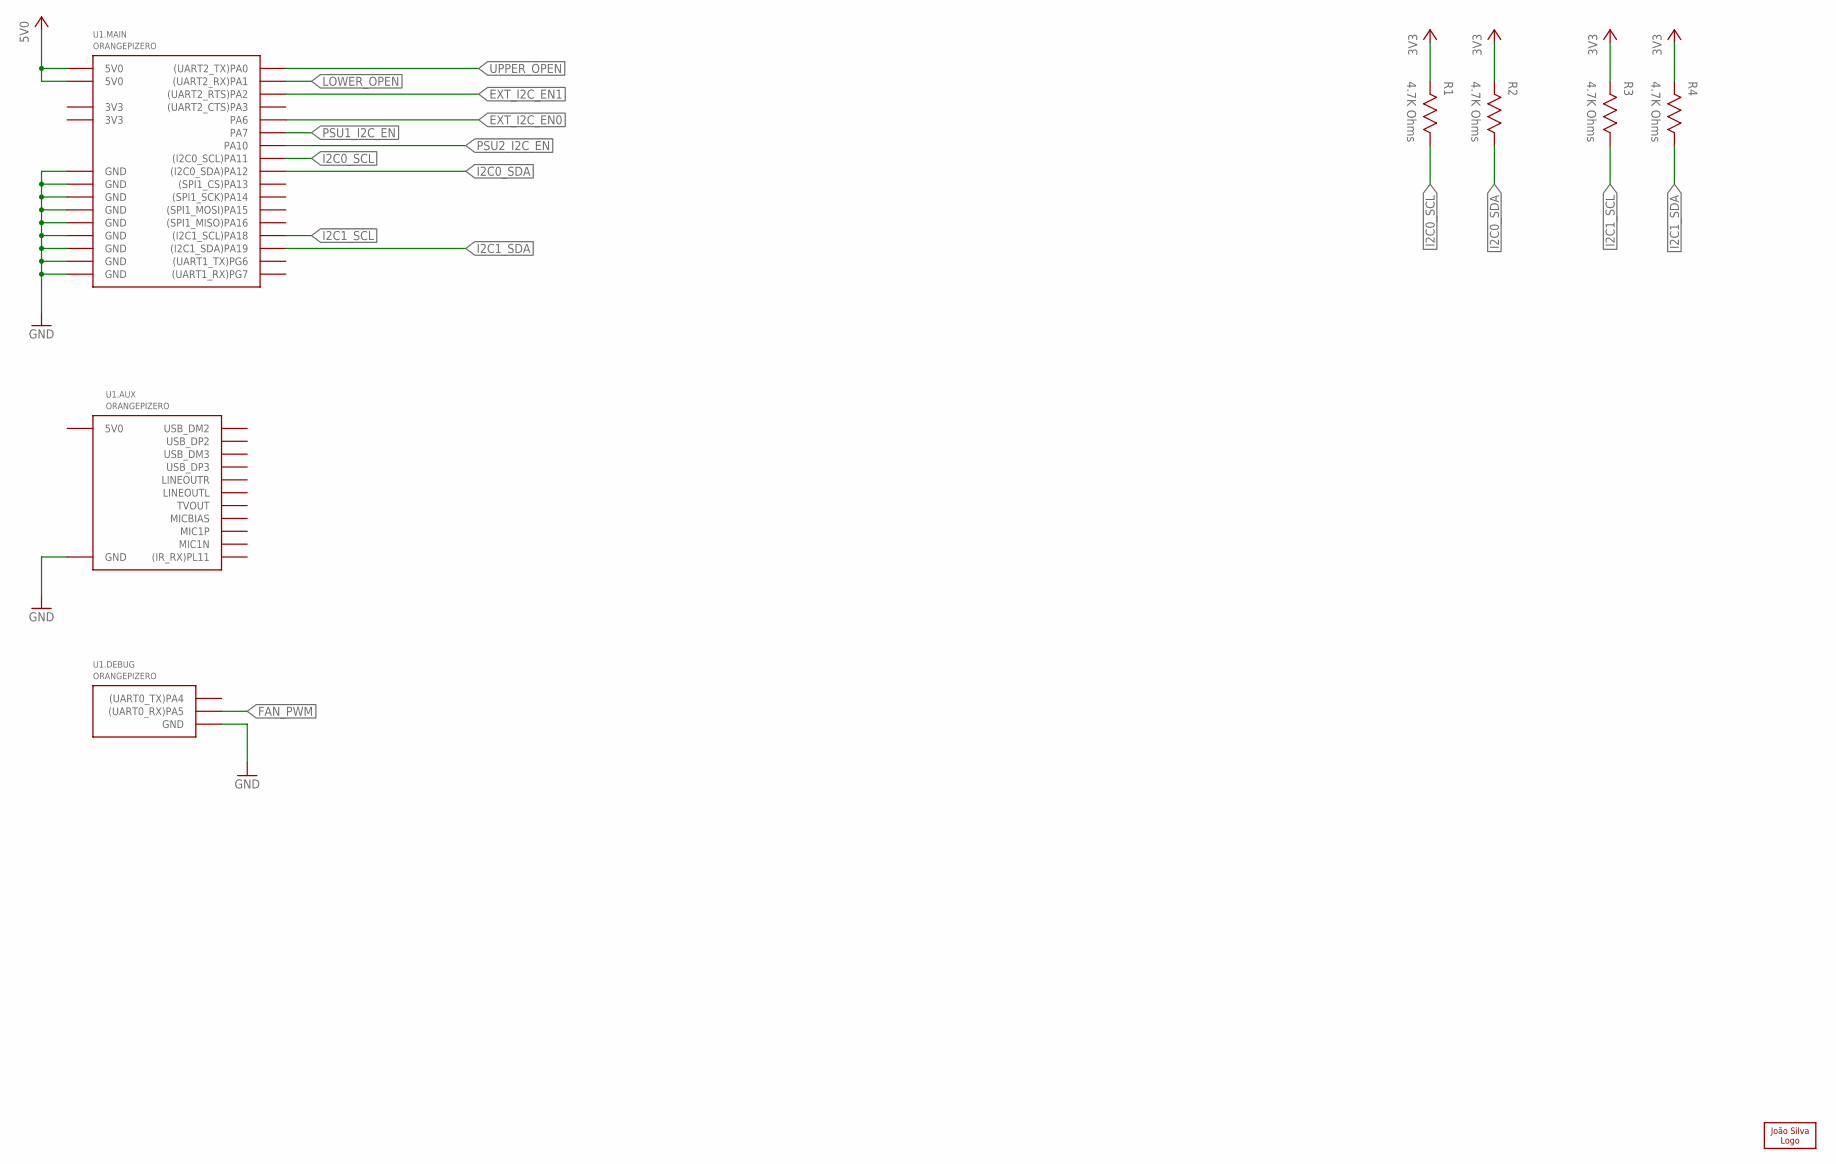
[picture p181: schematic qo-100-opi-dock.sch, sheet 1, SBC]

Parts:
LOGO1: JS-5MM; JS_5MM
R1, R2, R3, R4: 4.7K Ohms; RES0603
U1: ORANGEPIZERO

Connections:
3V3: R1.2, R2.2, R3.2, R4.2; also elsewhere on the board
5V0: U1.MH$2 (5V0), U1.MH$4 (5V0); also elsewhere on the board
EXT_I2C_EN0: U1.MH$7 (PA6); also elsewhere on the board
EXT_I2C_EN1: U1.MH$22 ((UART2_RTS)PA2); also elsewhere on the board
FAN_PWM: U1.DBG$2 ((UART0_RX)PA5); also elsewhere on the board
GND: U1.DBG$1 (GND), U1.GND@0 (GND), U1.GND@1 (GND), U1.GND@2 (GND), U1.GND@3 (GND), U1.MH$6 (GND), U1.MH$9 (GND), U1.MH$14 (GND), U1.MH$20 (GND), U1.MH$25 (GND), U1.SH$2 (GND); also elsewhere on the board
I2C0_SCL: R1.1, U1.MH$5 ((I2C0_SCL)PA11); also elsewhere on the board
I2C0_SDA: R2.1, U1.MH$3 ((I2C0_SDA)PA12); also elsewhere on the board
I2C1_SCL: R3.1, U1.MH$18 ((I2C1_SCL)PA18); also elsewhere on the board
I2C1_SDA: R4.1, U1.MH$16 ((I2C1_SDA)PA19); also elsewhere on the board
LOWER_OPEN: U1.MH$11 ((UART2_RX)PA1); also elsewhere on the board
PSU1_I2C_EN: U1.MH$12 (PA7); also elsewhere on the board
PSU2_I2C_EN: U1.MH$26 (PA10); also elsewhere on the board
UPPER_OPEN: U1.MH$13 ((UART2_TX)PA0); also elsewhere on the board

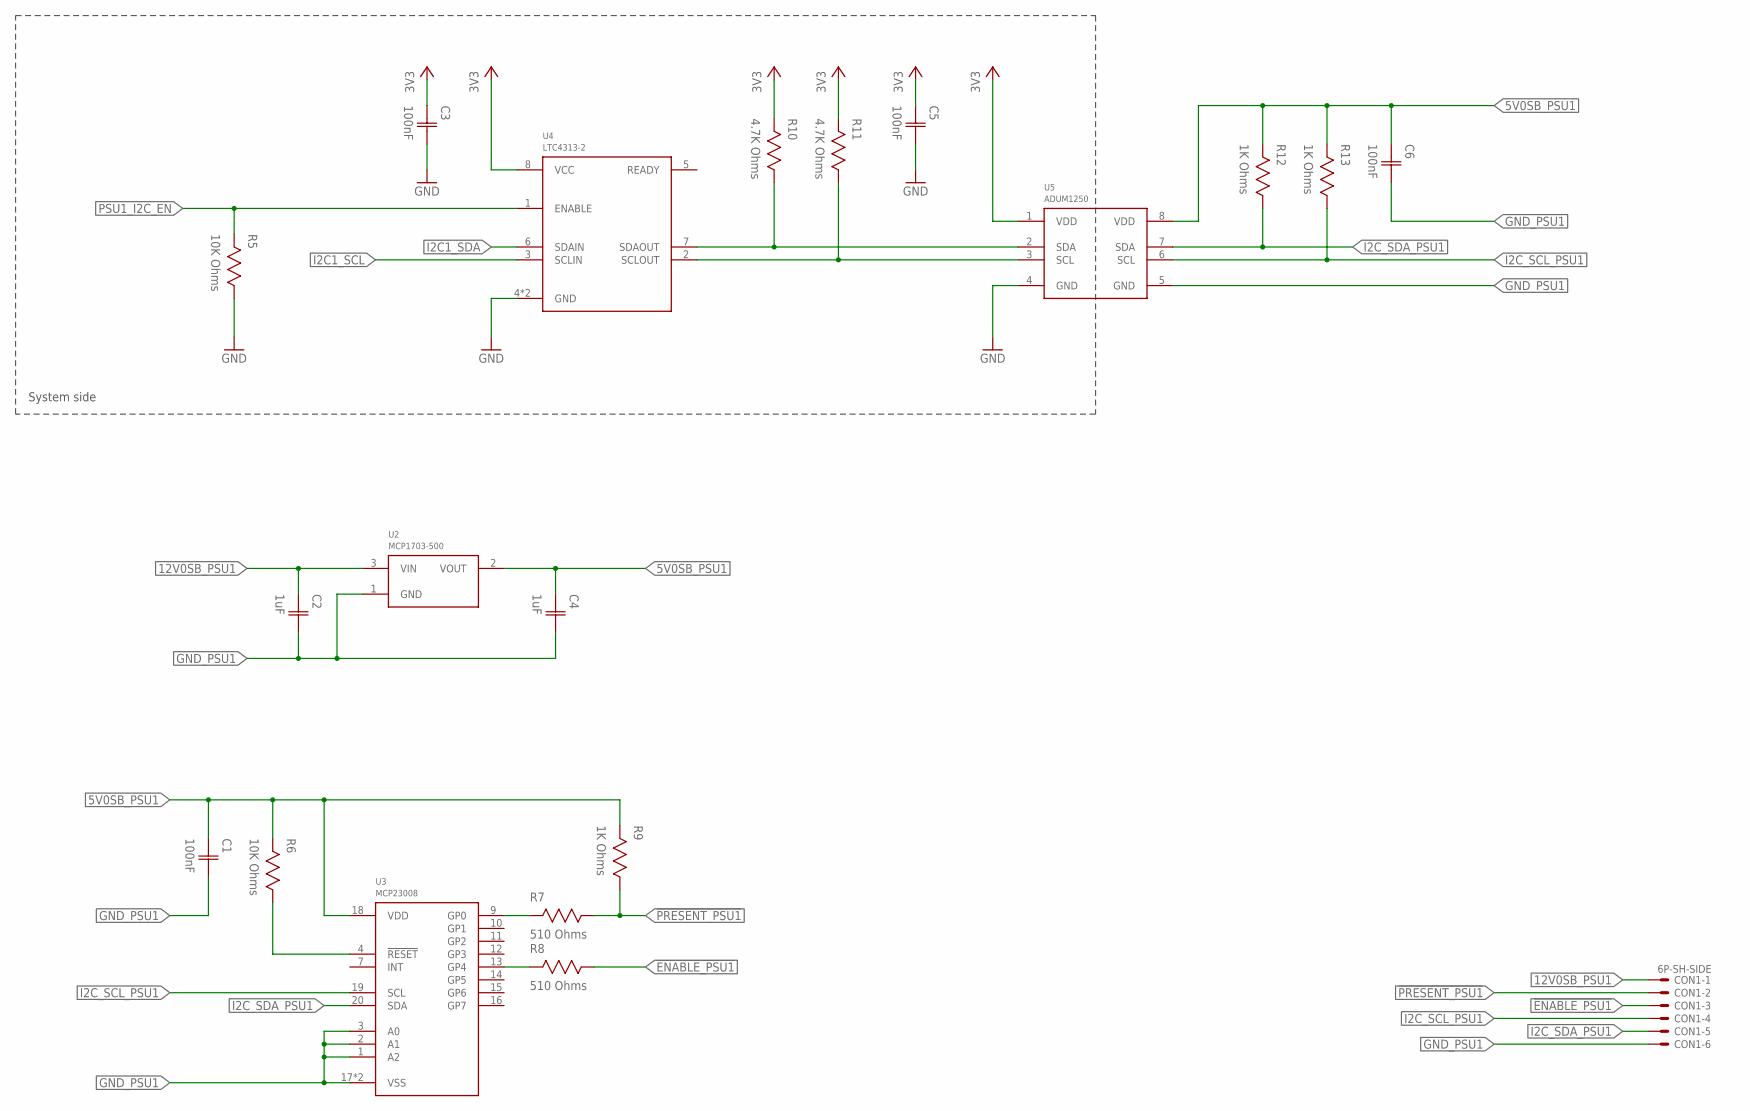
[picture p182: schematic qo-100-opi-dock.sch, sheet 2, PSU #1 Interface]

Parts:
C1, C3, C5, C6: 100nF; CAP0603
C2, C4: 1uF; CAP0603
CON1: 6P-SH-SIDE; SH-06-SIDE
R5, R6: 10K Ohms; RES0603
R7, R8: 510 Ohms; RES0603
R9, R12, R13: 1K Ohms; RES0603
R10, R11: 4.7K Ohms; RES0603
U2: MCP1703-500; SOT23
U3: MCP23008; QFN20
U4: LTC4313-2; DFN8
U5: ADUM1250; SOIC8

Connections:
3V3: C3.1 (C1), C5.1 (C1), R10.2, R11.2, U4.8 (VCC), U5.1 (VDD); also elsewhere on the board
5V0SB_PSU1: C1.1 (C1), C4.1 (C1), C6.1 (C1), R6.2, R9.2, R12.2, R13.2, U2.2 (VOUT), U3.18 (VDD), U5.8 (VDD)
12V0SB_PSU1: C2.1 (C1), CON1.1, U2.3 (VIN)
!ENABLE_PSU1: CON1.3, R8.1
!PRESENT_PSU1: CON1.2, R7.1, R9.1
GND: C3.2 (C2), C5.2 (C2), R5.1, U4.4 (GND), U4.9 (GND), U5.4 (GND); also elsewhere on the board
GND_PSU1: C1.2 (C2), C2.2 (C2), C4.2 (C2), C6.2 (C2), CON1.6, U2.1 (GND), U3.1 (A2), U3.2 (A1), U3.3 (A0), U3.17 (VSS), U3.PAD (VSS), U5.5 (GND)
I2C1_SCL: U4.3 (SCLIN); also elsewhere on the board
I2C1_SDA: U4.6 (SDAIN); also elsewhere on the board
I2C_SCL_PSU1: CON1.4, R13.1, U3.19 (SCL), U5.6 (SCL)
I2C_SDA_PSU1: CON1.5, R12.1, U3.20 (SDA), U5.7 (SDA)
unnamed: R11.1, U4.2 (SCLOUT), U5.3 (SCL)
unnamed: R10.1, U4.7 (SDAOUT), U5.2 (SDA)
unnamed: R6.1, U3.4 (!RESET)
unnamed: R8.2, U3.13 (GP4)
unnamed: R7.2, U3.9 (GP0)
PSU1_I2C_EN: R5.2, U4.1 (ENABLE); also elsewhere on the board

Notes on the sheet:
System side

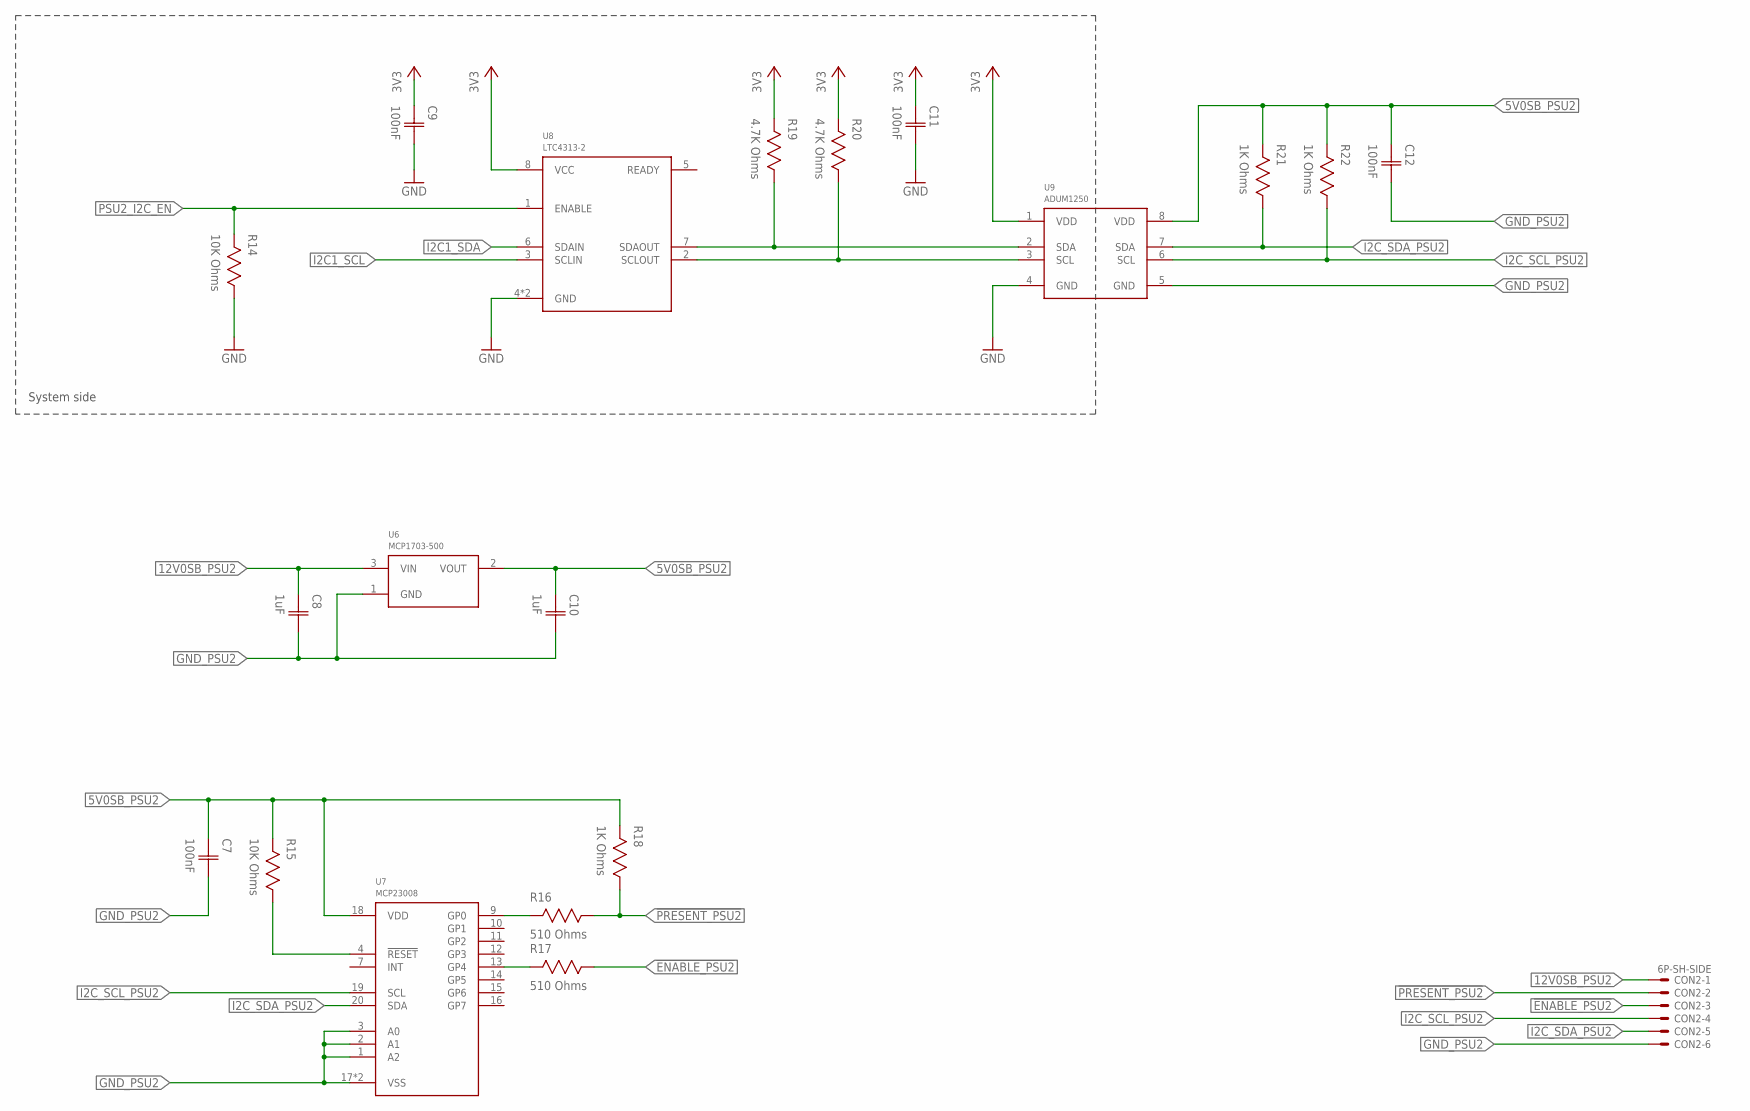
[picture p183: schematic qo-100-opi-dock.sch, sheet 3, PSU #2 Interface]

Parts:
C7, C9, C11, C12: 100nF; CAP0603
C8, C10: 1uF; CAP0603
CON2: 6P-SH-SIDE; SH-06-SIDE
R14, R15: 10K Ohms; RES0603
R16, R17: 510 Ohms; RES0603
R18, R21, R22: 1K Ohms; RES0603
R19, R20: 4.7K Ohms; RES0603
U6: MCP1703-500; SOT23
U7: MCP23008; QFN20
U8: LTC4313-2; DFN8
U9: ADUM1250; SOIC8

Connections:
3V3: C9.1 (C1), C11.1 (C1), R19.2, R20.2, U8.8 (VCC), U9.1 (VDD); also elsewhere on the board
5V0SB_PSU2: C7.1 (C1), C10.1 (C1), C12.1 (C1), R15.2, R18.2, R21.2, R22.2, U6.2 (VOUT), U7.18 (VDD), U9.8 (VDD)
12V0SB_PSU2: C8.1 (C1), CON2.1, U6.3 (VIN)
!ENABLE_PSU2: CON2.3, R17.1
!PRESENT_PSU2: CON2.2, R16.1, R18.1
GND: C9.2 (C2), C11.2 (C2), R14.1, U8.4 (GND), U8.9 (GND), U9.4 (GND); also elsewhere on the board
GND_PSU2: C7.2 (C2), C8.2 (C2), C10.2 (C2), C12.2 (C2), CON2.6, U6.1 (GND), U7.1 (A2), U7.2 (A1), U7.3 (A0), U7.17 (VSS), U7.PAD (VSS), U9.5 (GND)
I2C1_SCL: U8.3 (SCLIN); also elsewhere on the board
I2C1_SDA: U8.6 (SDAIN); also elsewhere on the board
I2C_SCL_PSU2: CON2.4, R22.1, U7.19 (SCL), U9.6 (SCL)
I2C_SDA_PSU2: CON2.5, R21.1, U7.20 (SDA), U9.7 (SDA)
unnamed: R20.1, U8.2 (SCLOUT), U9.3 (SCL)
unnamed: R19.1, U8.7 (SDAOUT), U9.2 (SDA)
unnamed: R15.1, U7.4 (!RESET)
unnamed: R17.2, U7.13 (GP4)
unnamed: R16.2, U7.9 (GP0)
PSU2_I2C_EN: R14.2, U8.1 (ENABLE); also elsewhere on the board

Notes on the sheet:
System side
