vankxr/qo-100-tools/pcb/opi-dock/qo-100-opi-dock.brd

## EAGLE design pcb/opi-dock/qo-100-opi-dock.brd (continued)

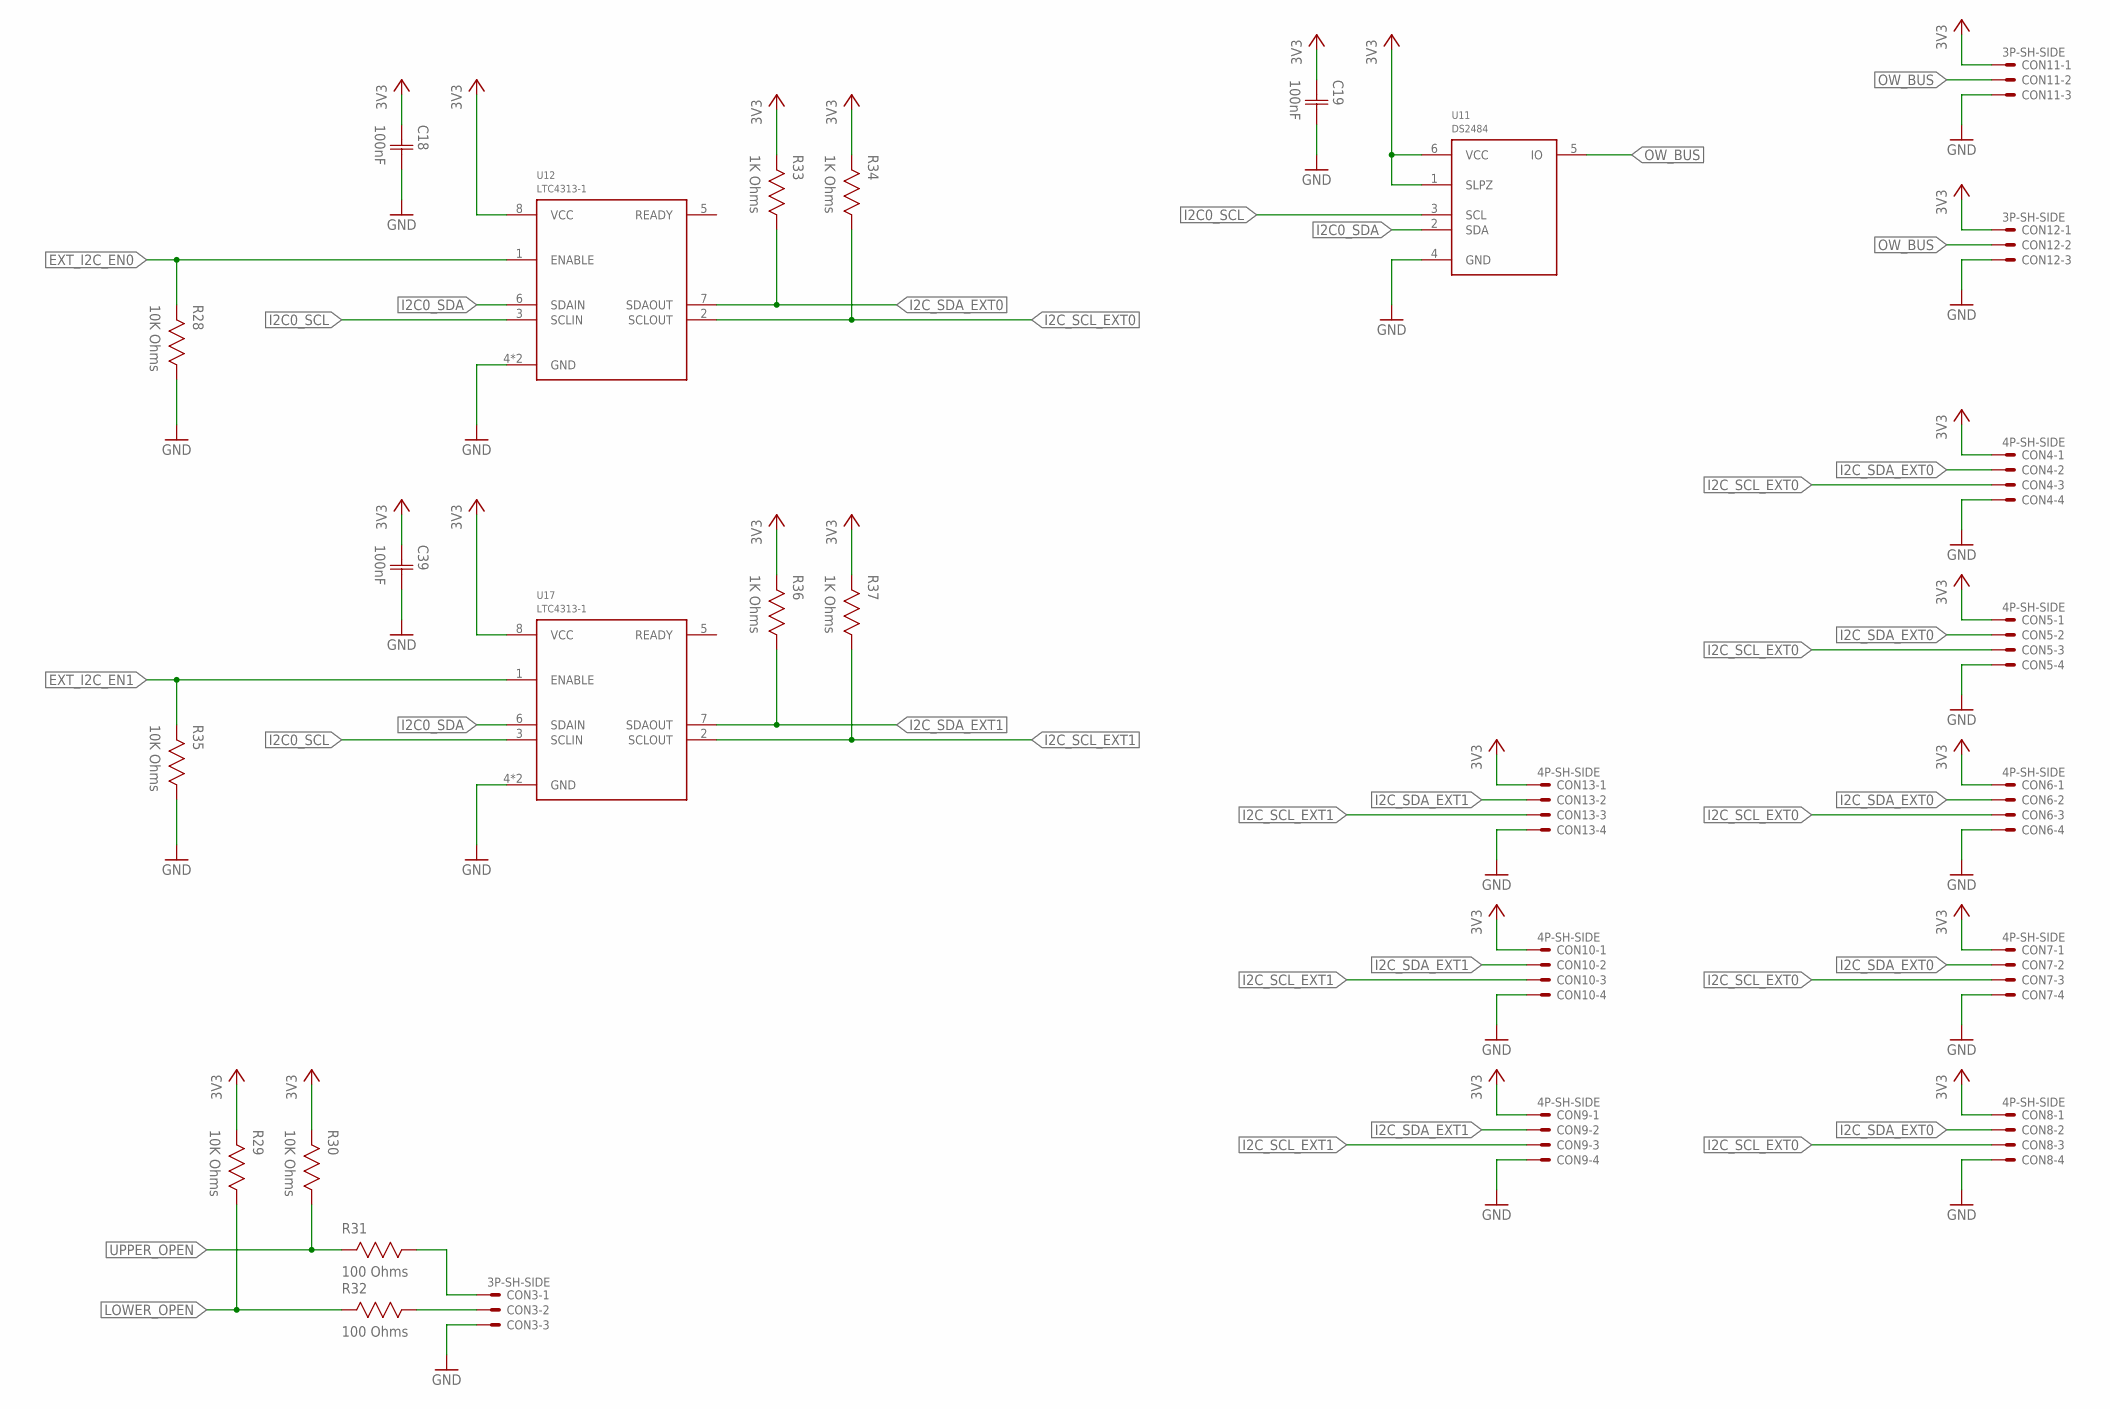
[picture p184: schematic qo-100-opi-dock.sch, sheet 4, Interface]

Parts:
C18, C19, C39: 100nF; CAP0603
CON3, CON11, CON12: 3P-SH-SIDE; SH-03-SIDE
CON4, CON5, CON6, CON7, CON8, CON9, CON10, CON13: 4P-SH-SIDE; SH-04-SIDE
R28, R29, R30, R35: 10K Ohms; RES0603
R31, R32: 100 Ohms; RES0603
R33, R34, R36, R37: 1K Ohms; RES0603
U11: DS2484; SOT23-6
U12, U17: LTC4313-1; DFN8

Connections:
3V3: C18.1 (C1), C19.1 (C1), C39.1 (C1), CON4.1, CON5.1, CON6.1, CON7.1, CON8.1, CON9.1, CON10.1, CON11.1, CON12.1, CON13.1, R29.2, R30.2, R33.2, R34.2, R36.2, R37.2, U11.1 (SLPZ), U11.6 (VCC), U12.8 (VCC), U17.8 (VCC); also elsewhere on the board
EXT_I2C_EN0: R28.2, U12.1 (ENABLE); also elsewhere on the board
EXT_I2C_EN1: R35.2, U17.1 (ENABLE); also elsewhere on the board
GND: C18.2 (C2), C19.2 (C2), C39.2 (C2), CON3.3, CON4.4, CON5.4, CON6.4, CON7.4, CON8.4, CON9.4, CON10.4, CON11.3, CON12.3, CON13.4, R28.1, R35.1, U11.4 (GND), U12.4 (GND), U12.9 (GND), U17.4 (GND), U17.9 (GND); also elsewhere on the board
I2C0_SCL: U11.3 (SCL), U12.3 (SCLIN), U17.3 (SCLIN); also elsewhere on the board
I2C0_SDA: U11.2 (SDA), U12.6 (SDAIN), U17.6 (SDAIN); also elsewhere on the board
I2C_SCL_EXT0: CON4.3, CON5.3, CON6.3, CON7.3, CON8.3, R34.1, U12.2 (SCLOUT)
I2C_SCL_EXT1: CON9.3, CON10.3, CON13.3, R37.1, U17.2 (SCLOUT)
I2C_SDA_EXT0: CON4.2, CON5.2, CON6.2, CON7.2, CON8.2, R33.1, U12.7 (SDAOUT)
I2C_SDA_EXT1: CON9.2, CON10.2, CON13.2, R36.1, U17.7 (SDAOUT)
LOWER_OPEN: R29.1, R32.2; also elsewhere on the board
unnamed: CON3.2, R32.1
unnamed: CON3.1, R31.1
OW_BUS: CON11.2, CON12.2, U11.5 (IO)
UPPER_OPEN: R30.1, R31.2; also elsewhere on the board

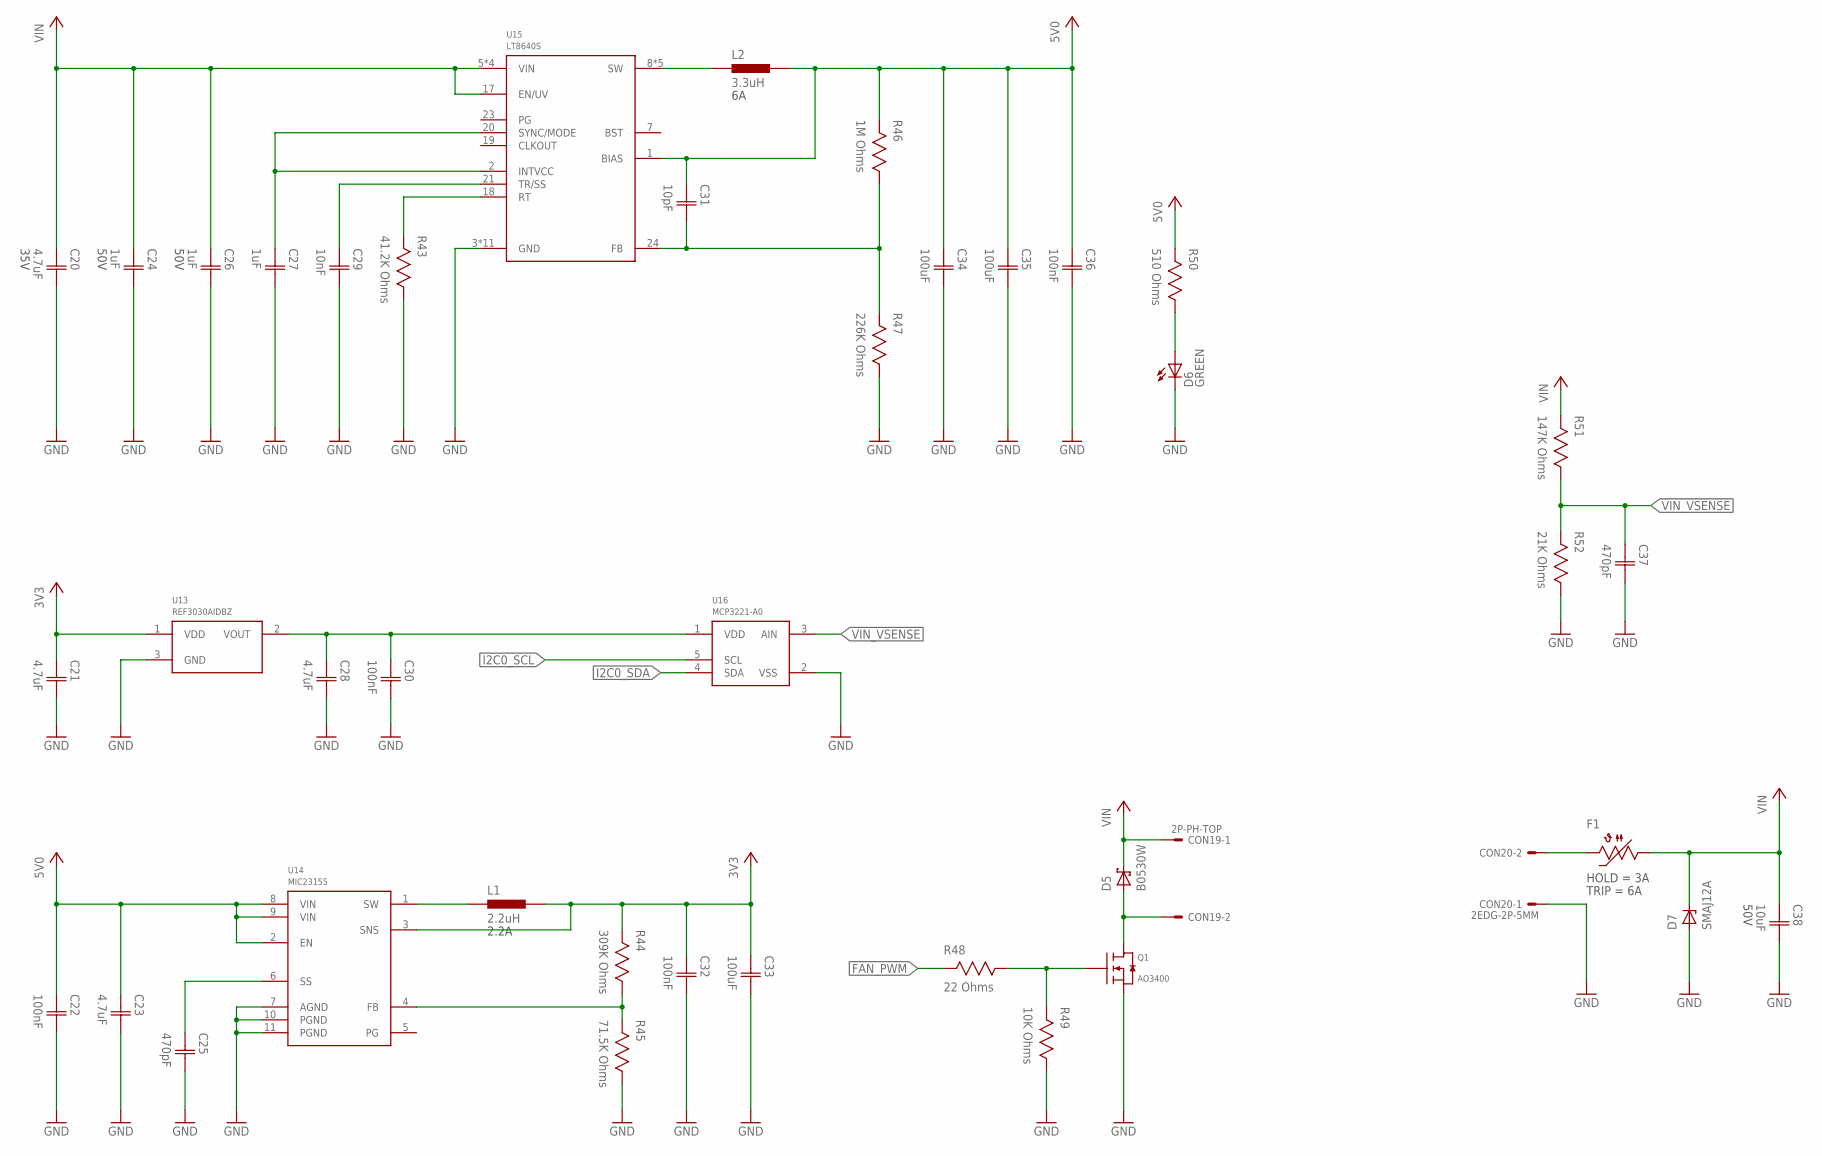
[picture p185: schematic qo-100-opi-dock.sch, sheet 5, Power]

Parts:
C20: 4.7uF; CAP0603; VOLTAGE 35V
C21, C23, C28: 4.7uF; CAP0603
C22, C30, C32, C36: 100nF; CAP0603
C24, C26: 1uF; CAP0603; VOLTAGE 50V
C25, C37: 470pF; CAP0603
C27: 1uF; CAP0603
C29: 10nF; CAP0603
C31: 10pF; CAP0603
C33, C34, C35: 100uF; CAP1206
C38: 10uF; CAP1206; VOLTAGE 50V
CON19: 2P-PH-TOP; PH-02-TOP
CON20: 2EDG-2P-5MM
D5: B0530W; SOD-123
D6: LED0603; 0603
D7: SMAJ12A; DO214AC
F1: 2.6A Hold; 1206
L1: 2.2uH; IND2520
L2: 3.3uH; IND0606
Q1: AO3400; SOT23
R43: 41.2K Ohms; RES0603
R44: 309K Ohms; RES0603
R45: 71.5K Ohms; RES0603
R46: 1M Ohms; RES0603
R47: 226K Ohms; RES0603
R48: 22 Ohms; RES0603
R49: 10K Ohms; RES0603
R50: 510 Ohms; RES0603
R51: 147K Ohms; RES0603
R52: 21K Ohms; RES0603
U13: REF3030AIDBZ; SOT23
U14: MIC23155; DFN10
U15: LT8640S; QFN24_CORNER
U16: MCP3221-A0; SOT23-5

Connections:
3V0_ADC_CLEAN: C28.1 (C1), C30.1 (C1), U13.2 (VOUT), U16.1 (VDD)
3V3: C21.1 (C1), C32.1 (C1), C33.1 (C1), L1.2, R44.2, U13.1 (VDD), U14.3 (SNS); also elsewhere on the board
3V3_FB: R44.1, R45.2, U14.4 (FB)
3V3_SOFTSTART: C25.1 (C1), U14.6 (SS)
3V3_SW: L1.1, U14.1 (SW)
5V0: C22.1 (C1), C23.1 (C1), C31.1 (C1), C34.1 (C1), C35.1 (C1), C36.1 (C1), L2.2, R46.2, R50.2, U14.2 (EN), U14.8 (VIN), U14.9 (VIN), U15.1 (BIAS); also elsewhere on the board
5V0_FB: C31.2 (C2), R46.1, R47.2, U15.24 (FB)
5V0_INTVCC: C27.1 (C1), U15.2 (INTVCC), U15.20 (SYNC/MODE)
5V0_RT: R43.2, U15.18 (RT)
5V0_SS: C29.1 (C1), U15.21 (TR/SS)
5V0_SW: L2.1, U15.8 (SW), U15.9 (SW), U15.10 (SW), U15.11 (SW), U15.12 (SW)
FAN_PWM: R48.2; also elsewhere on the board
GND: C20.2 (C2), C21.2 (C2), C22.2 (C2), C23.2 (C2), C24.2 (C2), C25.2 (C2), C26.2 (C2), C27.2 (C2), C28.2 (C2), C29.2 (C2), C30.2 (C2), C32.2 (C2), C33.2 (C2), C34.2 (C2), C35.2 (C2), C36.2 (C2), C37.2 (C2), C38.2 (C2), CON20.P$1, D6.C, D7.A, Q1.2 (S), R43.1, R45.1, R47.1, R49.1, R52.1, U13.3 (GND), U14.7 (AGND), U14.10 (PGND), U14.11 (PGND), U15.3 (GND), U15.16 (GND), U15.22 (GND), U15.25 (GND), U15.26 (GND), U15.27 (GND), U15.28 (GND), U15.29 (GND), U15.30 (GND), U15.31 (GND), U15.32 (GND), U16.2 (VSS); also elsewhere on the board
I2C0_SCL: U16.5 (SCL); also elsewhere on the board
I2C0_SDA: U16.4 (SDA); also elsewhere on the board
unnamed: CON20.P$2, F1.2
unnamed: CON19.2, D5.A, Q1.3 (D)
unnamed: Q1.1 (G), R48.1, R49.2
unnamed: D6.A, R50.1
VIN: C20.1 (C1), C24.1 (C1), C26.1 (C1), C38.1 (C1), CON19.1, D5.C, D7.C, F1.1, R51.2, U15.5 (VIN), U15.6 (VIN), U15.13 (VIN), U15.14 (VIN), U15.17 (EN/UV)
VIN_VSENSE: C37.1 (C1), R51.1, R52.2, U16.3 (AIN)

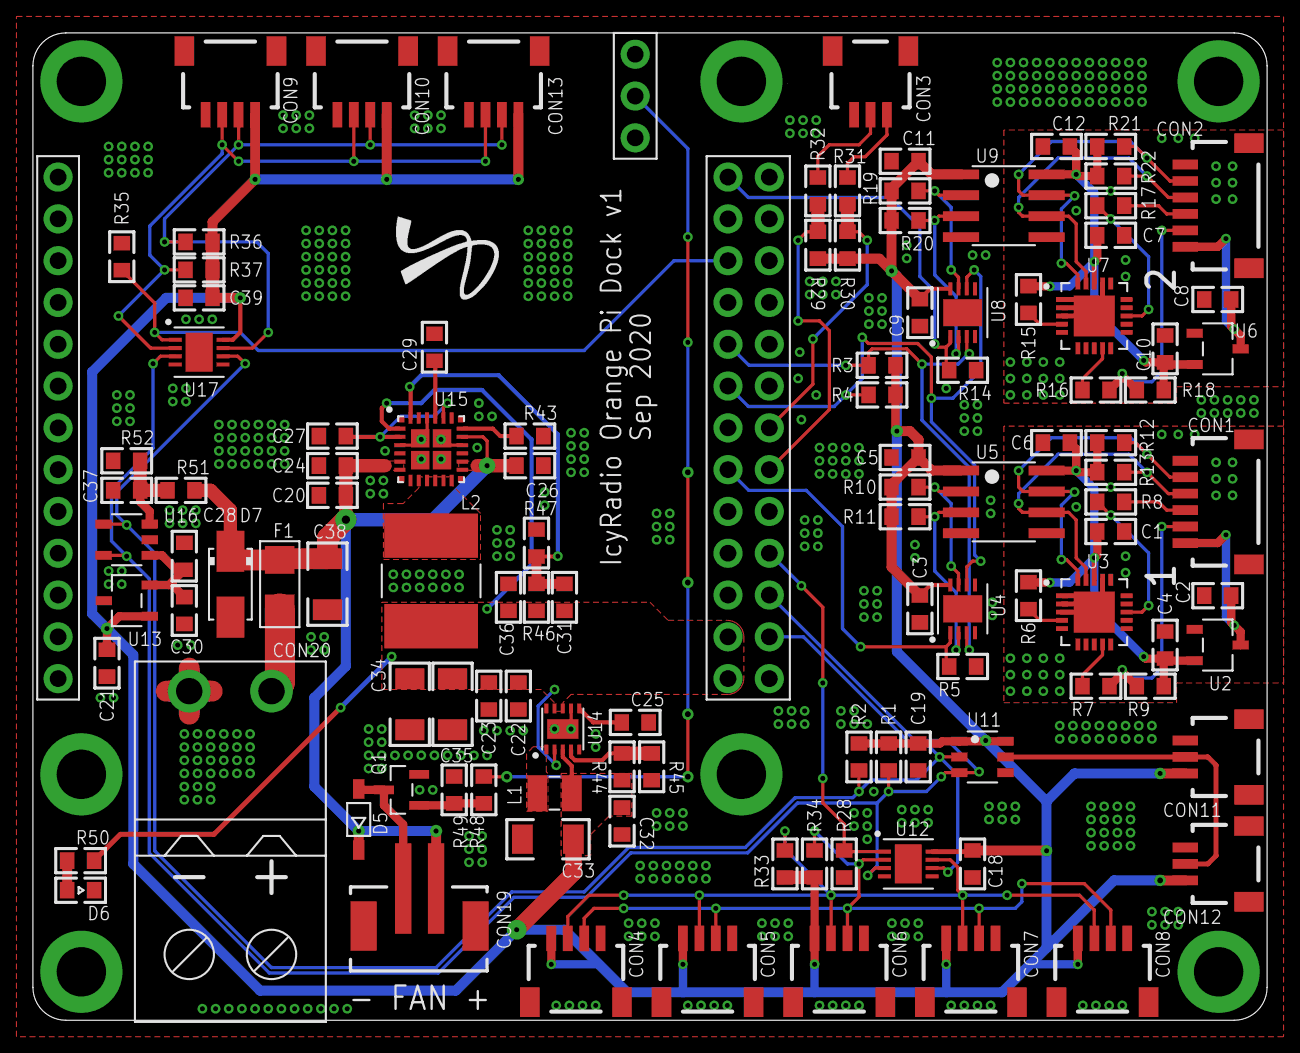
[picture p186: board qo-100-opi-dock.brd from above]

Board: 2 copper layers, 75.0 x 60.0 mm, 115 parts (0 on the bottom side), 60 nets.
