vankxr/qo-100-tools/pcb/digital-rf-power-meter/qo-100-digital-rf-power-meter.brd

## EAGLE design pcb/digital-rf-power-meter/qo-100-digital-rf-power-meter.brd (2021-02-02)

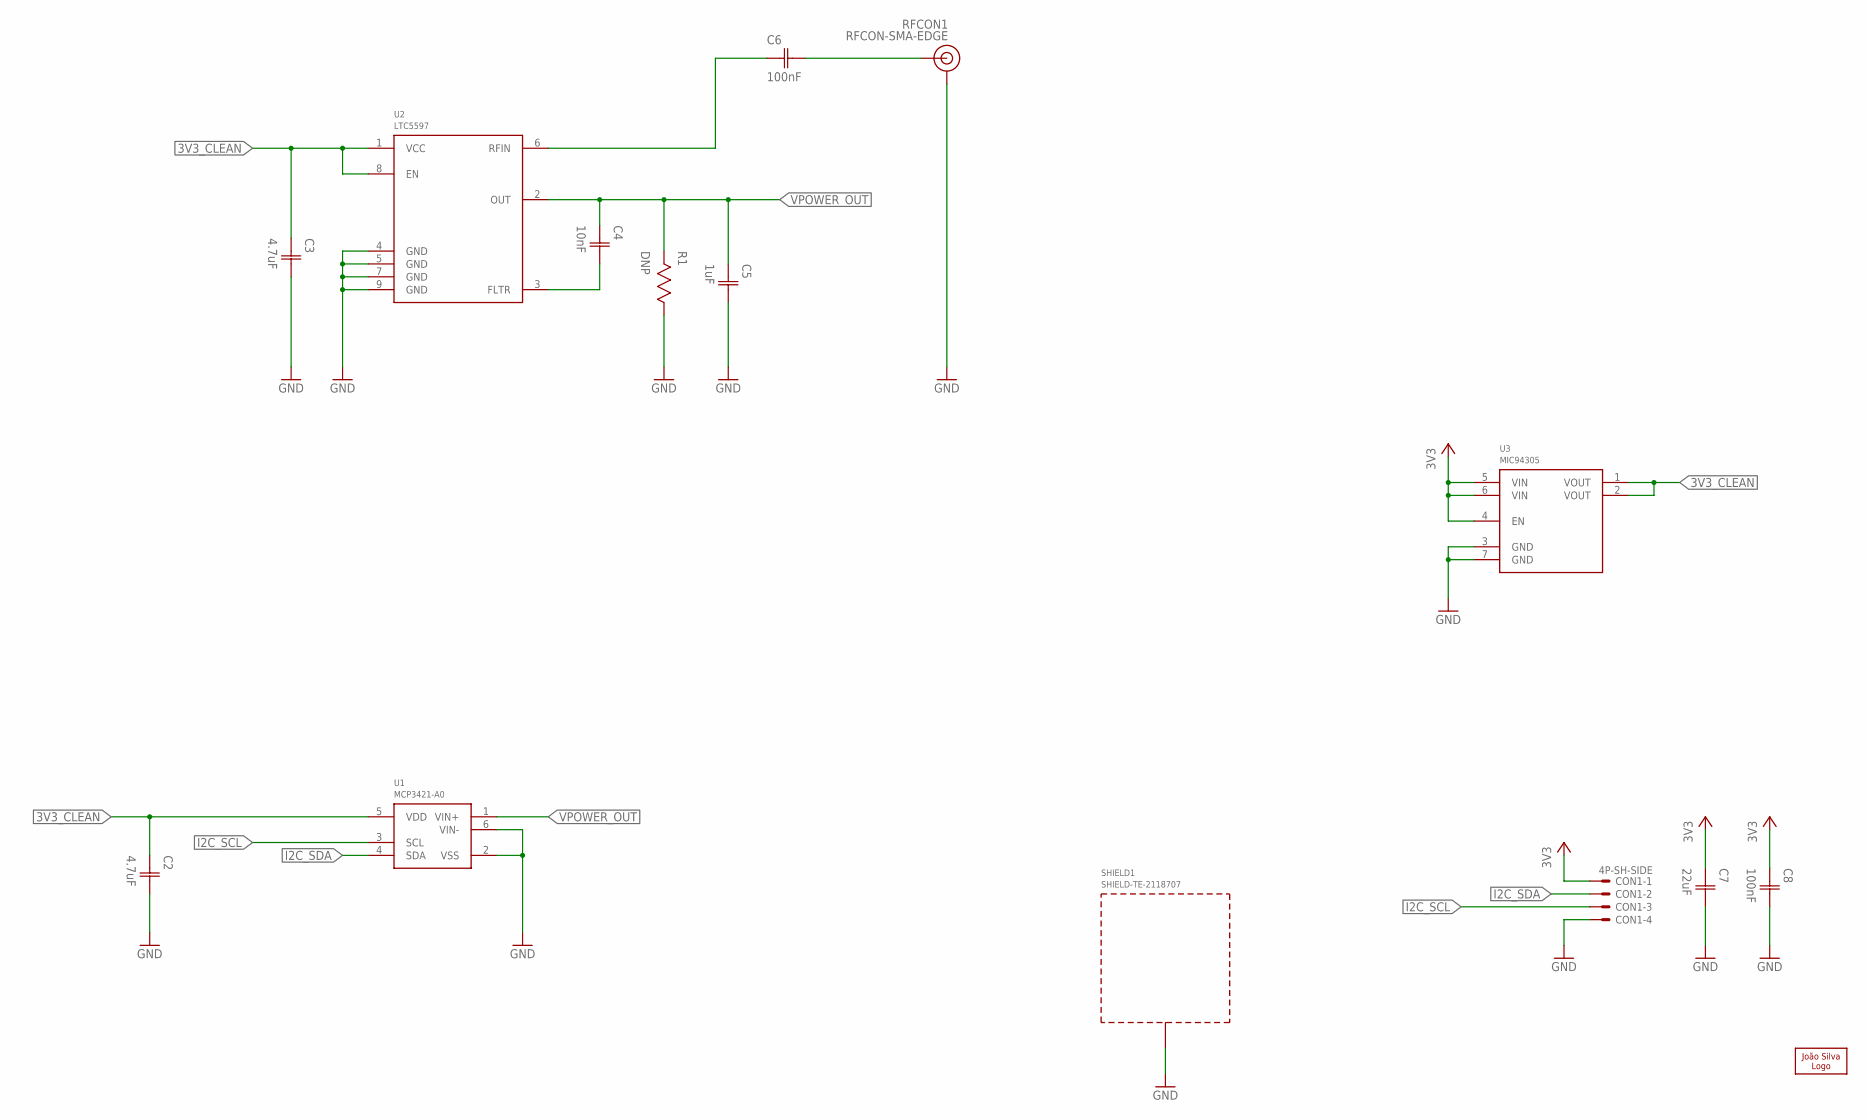
[picture p187: schematic qo-100-digital-rf-power-meter.sch]

Parts:
C2, C3: 4.7uF; CAP0603
C4: 10nF; CAP0603
C5: 1uF; CAP0603
C6, C8: 100nF; CAP0603
C7: 22uF; CAP1206
CON1: 4P-SH-SIDE; SH-04-SIDE
LOGO1: JS-5MM; JS_5MM
R1: DNP; RES0603
RFCON1: RFCON-SMA-EDGE; SMA-EDGE
SHIELD1: SHIELD-TE-2118707; 2118707
U1: MCP3421-A0; SOT23-6
U2: LTC5597; DFN8_2X2
U3: MIC94305; DFN6

Connections:
3V3: C7.1 (C1), C8.1 (C1), CON1.1, U3.4 (EN), U3.5 (VIN), U3.6 (VIN)
3V3_CLEAN: C2.1 (C1), C3.1 (C1), U1.5 (VDD), U2.1 (VCC), U2.8 (EN), U3.1 (VOUT), U3.2 (VOUT)
GND: C2.2 (C2), C3.2 (C2), C5.2 (C2), C7.2 (C2), C8.2 (C2), CON1.4, R1.1, RFCON1.GND@0 (GND), RFCON1.GND@1 (GND), RFCON1.GND@2 (GND), RFCON1.GND@3 (GND), SHIELD1.1, SHIELD1.2, SHIELD1.3, SHIELD1.4, SHIELD1.5, SHIELD1.6, SHIELD1.7, SHIELD1.8, SHIELD1.9, SHIELD1.10, SHIELD1.11, SHIELD1.12, U1.2 (VSS), U1.6 (VIN-), U2.4 (GND), U2.5 (GND), U2.7 (GND), U2.9 (GND), U3.3 (GND), U3.7 (GND)
I2C_SCL: CON1.3, U1.3 (SCL)
I2C_SDA: CON1.2, U1.4 (SDA)
unnamed: C6.1 (C1), U2.6 (RFIN)
unnamed: C6.2 (C2), RFCON1.SIG (SIGNAL)
unnamed: C4.2 (C2), U2.3 (FLTR)
VPOWER_OUT: C4.1 (C1), C5.1 (C1), R1.2, U1.1 (VIN+), U2.2 (OUT)

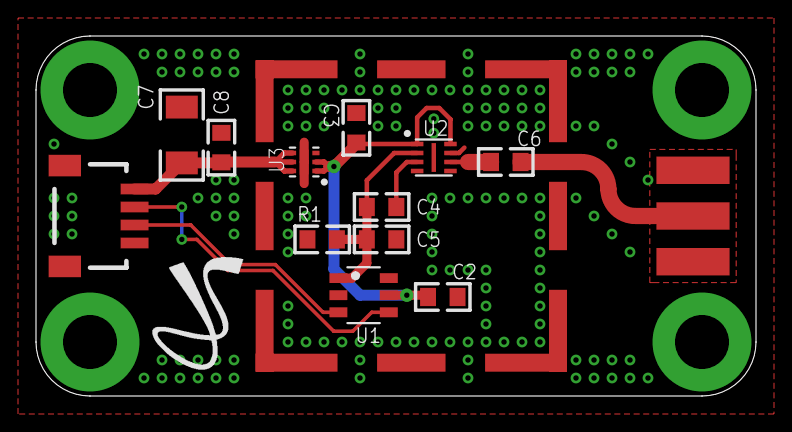
[picture p188: board qo-100-digital-rf-power-meter.brd from above]

Board: 2 copper layers, 40.0 x 20.0 mm, 15 parts (0 on the bottom side), 9 nets.
