vankxr/qo-100-tools/pcb/digital-power-meter/qo-100-digital-power-meter.brd

## EAGLE design pcb/digital-power-meter/qo-100-digital-power-meter.brd (2020-10-03)

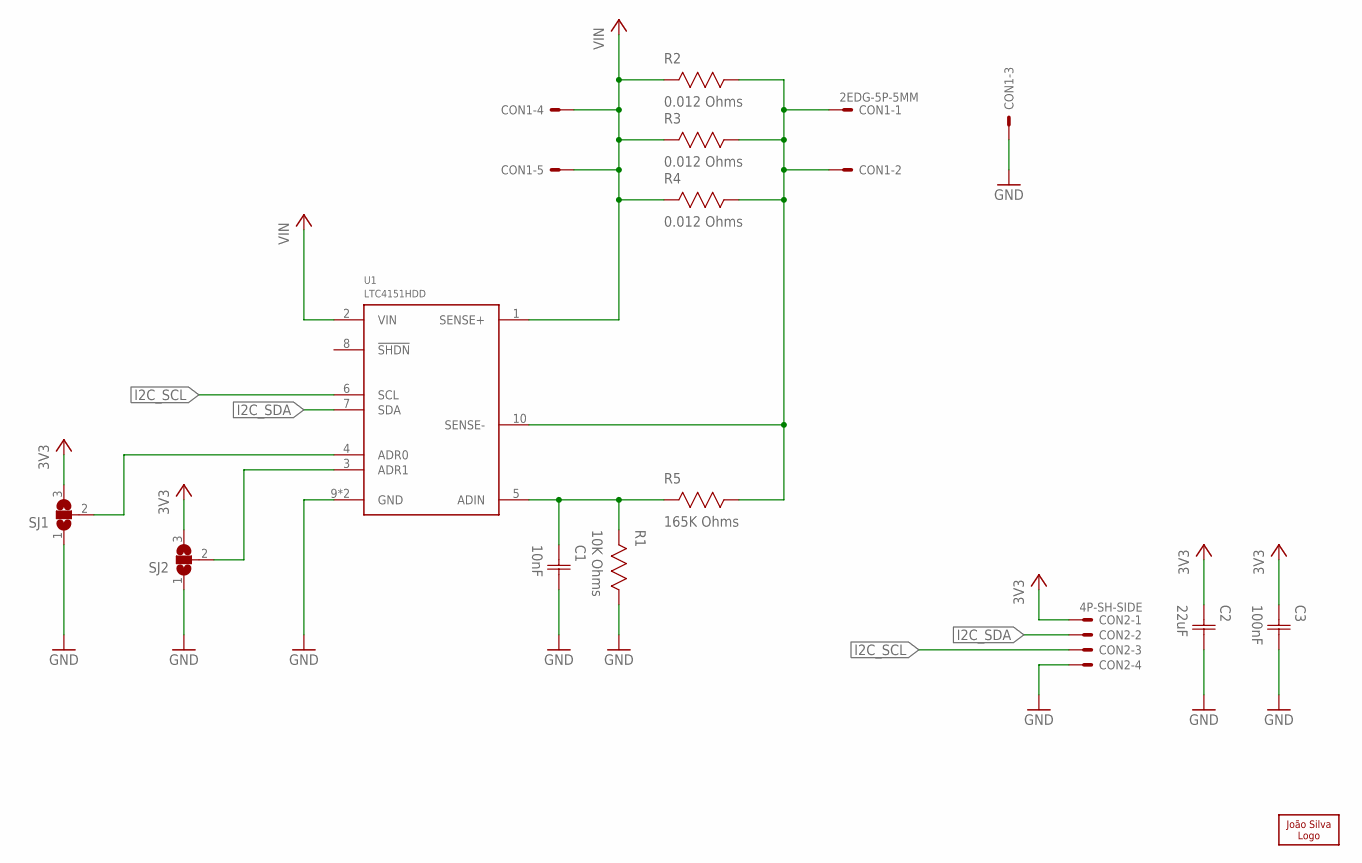
[picture p189: schematic qo-100-digital-power-meter.sch]

Parts:
C1: 10nF; CAP0603
C2: 22uF; CAP1206
C3: 100nF; CAP0603
CON1: 2EDG-5P-5MM
CON2: 4P-SH-SIDE; SH-04-SIDE
LOGO1: JS-5MM; JS_5MM
R1: 10K Ohms; RES0603
R2, R3, R4: 0.012 Ohms; RES2512
R5: 165K Ohms; RES0603
SJ1, SJ2: SJ2S; SJ2_S
U1: LTC4151HDD; DFN10

Connections:
3V3: C2.1 (C1), C3.1 (C1), CON2.1, SJ1.3, SJ2.3
GND: C1.2 (C2), C2.2 (C2), C3.2 (C2), CON1.P$3, CON2.4, R1.1, SJ1.1, SJ2.1, U1.9 (GND), U1.11 (GND)
I2C_SCL: CON2.3, U1.6 (SCL)
I2C_SDA: CON2.2, U1.7 (SDA)
unnamed: C1.1 (C1), R1.2, R5.2, U1.5 (ADIN)
unnamed: CON1.P$1, CON1.P$2, R2.1, R3.1, R4.1, R5.1, U1.10 (SENSE-)
unnamed: SJ1.2, U1.4 (ADR0)
unnamed: SJ2.2, U1.3 (ADR1)
VIN: CON1.P$4, CON1.P$5, R2.2, R3.2, R4.2, U1.1 (SENSE+), U1.2 (VIN)

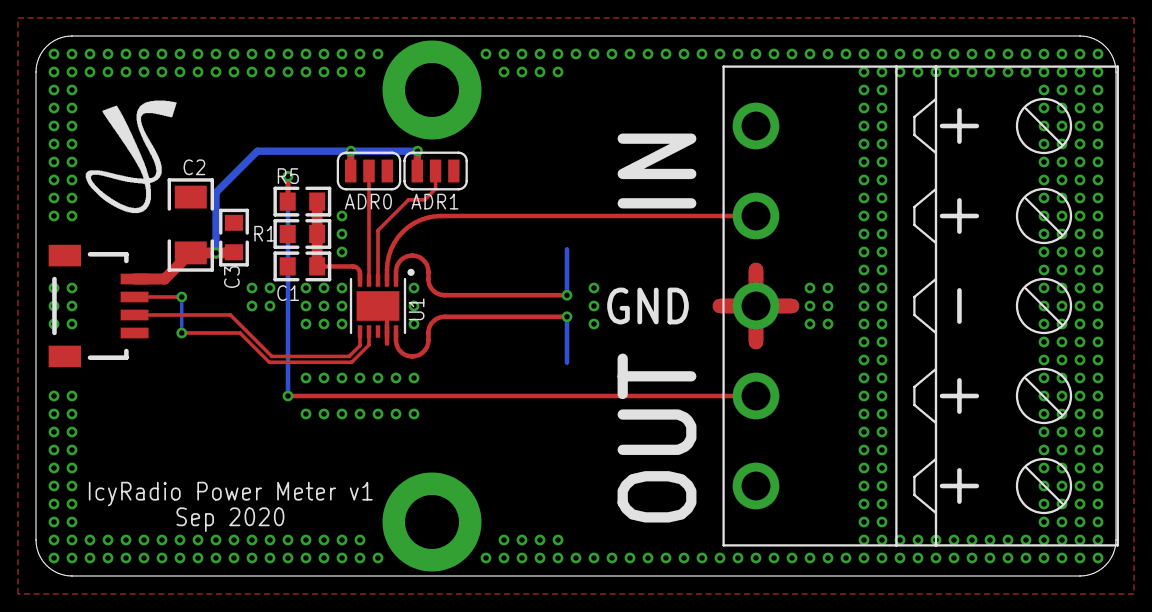
[picture p190: board qo-100-digital-power-meter.brd from above]

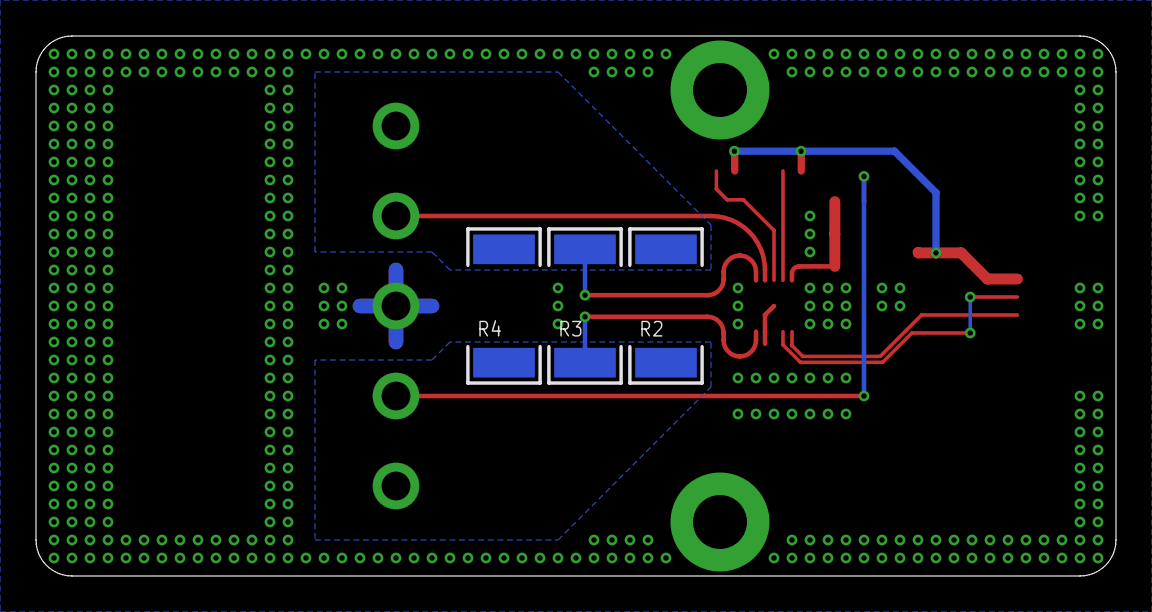
[picture p191: board qo-100-digital-power-meter.brd from below]

Board: 2 copper layers, 60.0 x 30.0 mm, 14 parts (3 on the bottom side), 9 nets.
