vankxr/qo-100-tools/pcb/opi-control-hat/qo-100-opi-control-hat.brd

## EAGLE design pcb/opi-control-hat/qo-100-opi-control-hat.brd (2020-09-16)

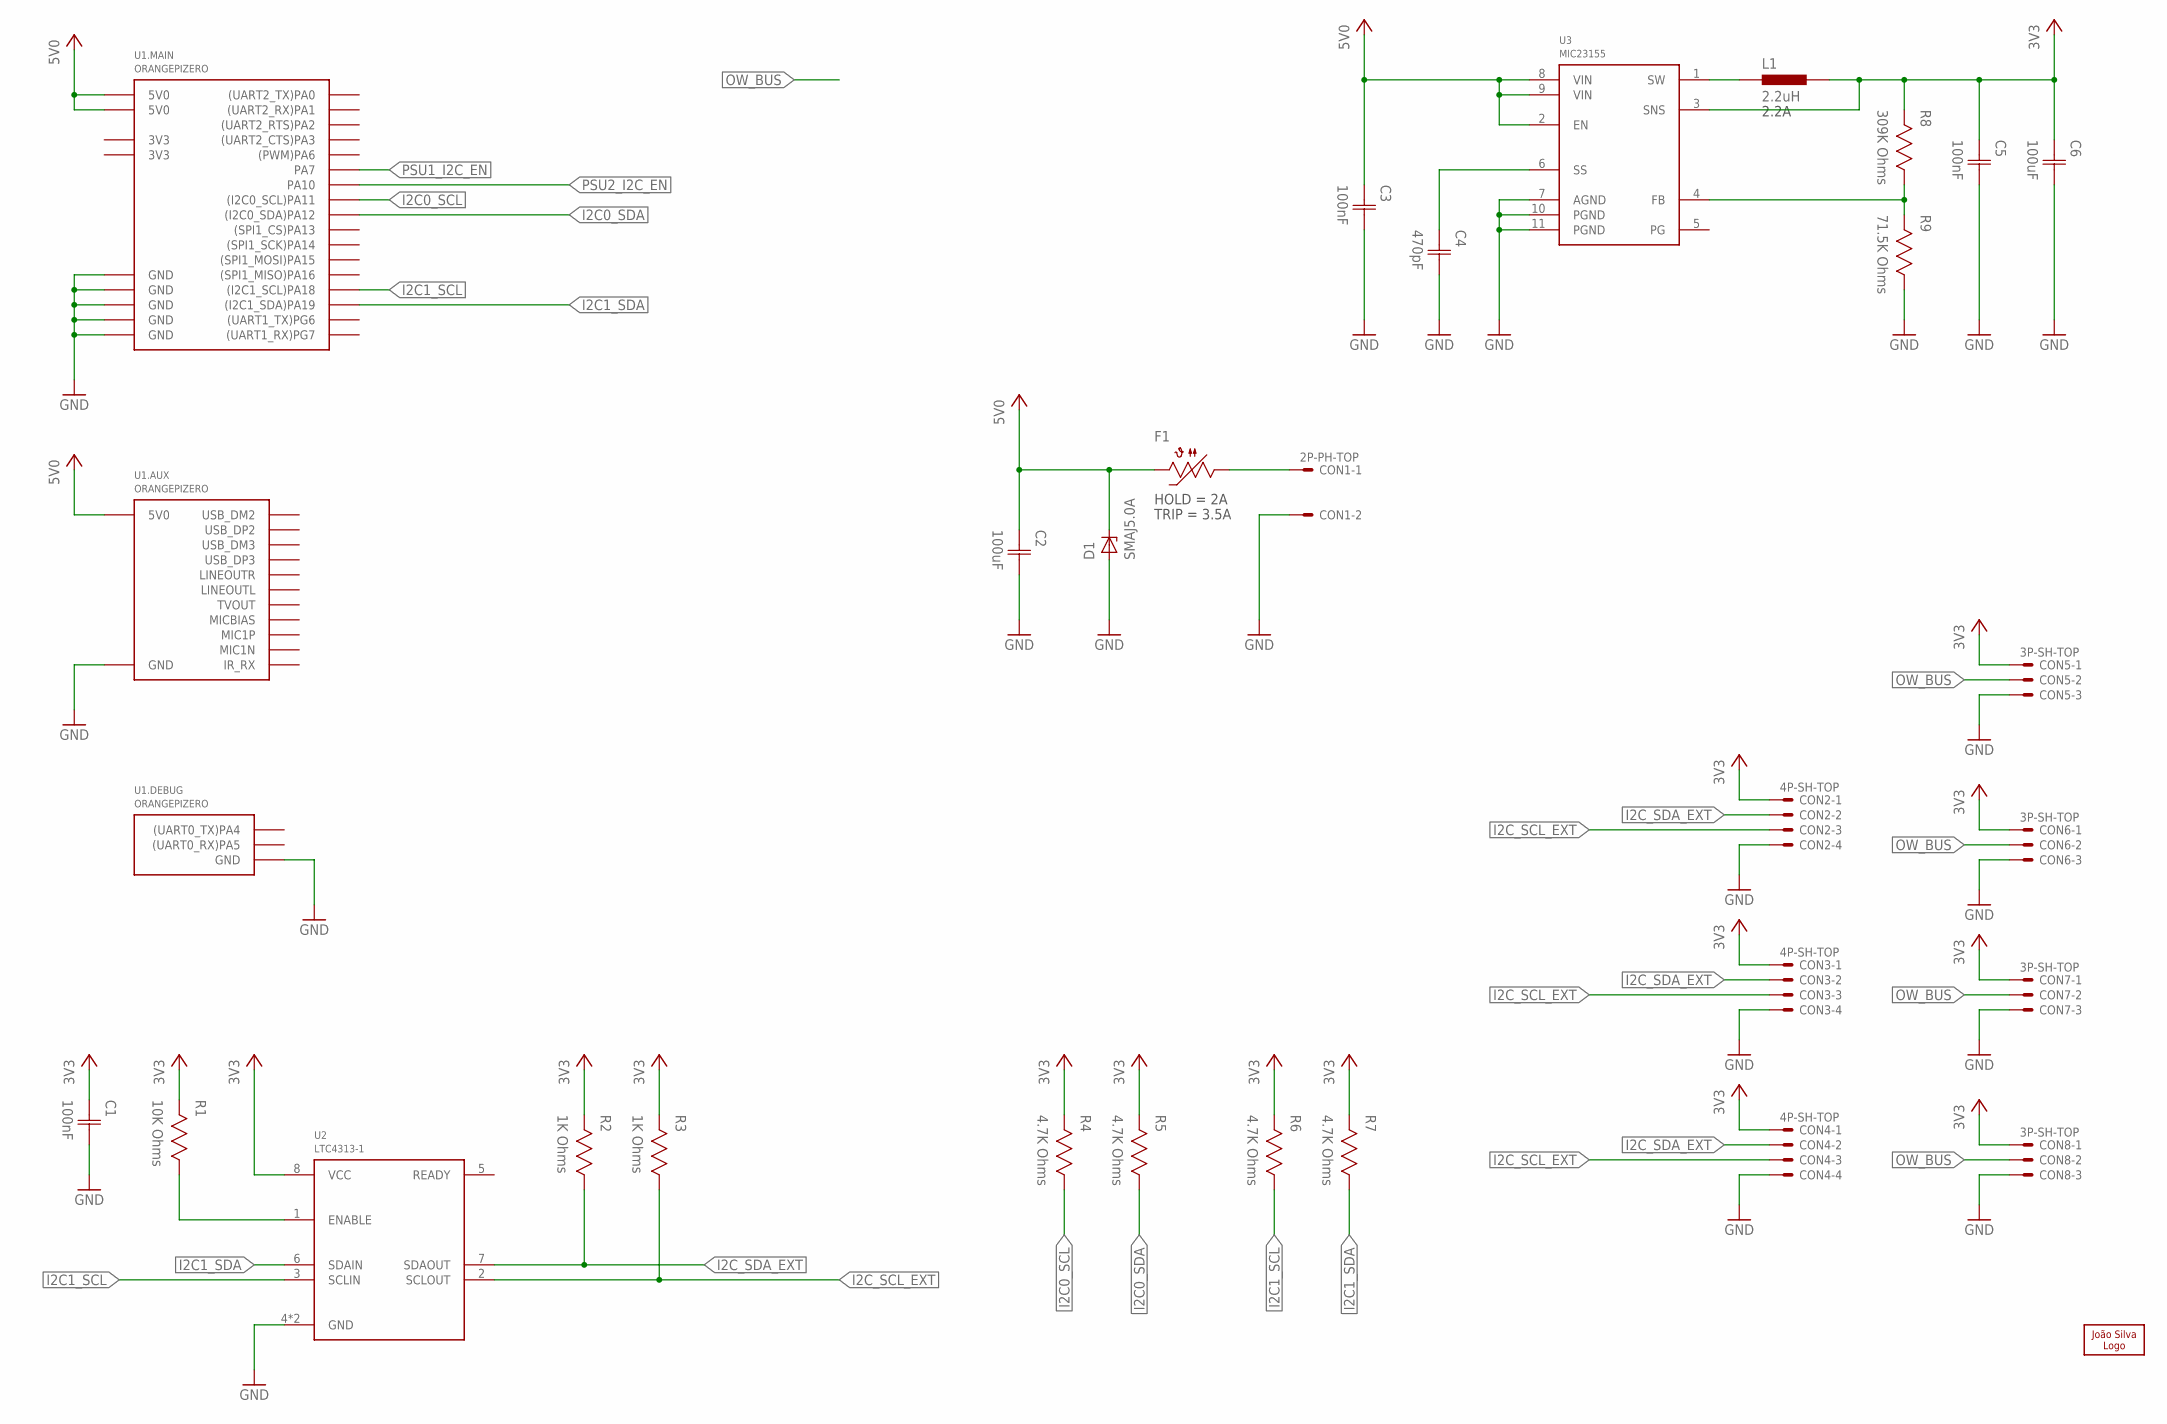
[picture p192: schematic qo-100-opi-control-hat.sch, sheet 1, SBC]

Parts:
C1, C3, C5: 100nF; CAP0603
C2, C6: 100uF; CAP1206
C4: 470pF; CAP0603
CON1: 2P-PH-TOP; PH-02-TOP
CON2, CON3, CON4: 4P-SH-TOP; SH-04-TOP
CON5, CON6, CON7, CON8: 3P-SH-TOP; SH-03-TOP
D1: SMAJ5.0A; DO214AC
F1: PTC1206; 1206
L1: 2.2uH; IND2520
LOGO1: JS-5MM; JS_5MM
R1: 10K Ohms; RES0603
R2, R3: 1K Ohms; RES0603
R4, R5, R6, R7: 4.7K Ohms; RES0603
R8: 309K Ohms; RES0603
R9: 71.5K Ohms; RES0603
U1: ORANGEPIZERO
U2: LTC4313-1; DFN8
U3: MIC23155; DFN10

Connections:
3V3: C1.1 (C1), C5.1 (C1), C6.1 (C1), CON2.1, CON3.1, CON4.1, CON5.1, CON6.1, CON7.1, CON8.1, L1.2, R1.2, R2.2, R3.2, R4.2, R5.2, R6.2, R7.2, R8.2, U2.8 (VCC), U3.3 (SNS); also elsewhere on the board
3V3_FB: R8.1, R9.2, U3.4 (FB)
3V3_SOFTSTART: C4.1 (C1), U3.6 (SS)
3V3_SW: L1.1, U3.1 (SW)
5V0: C2.1 (C1), C3.1 (C1), D1.C, F1.2, U1.MH$2 (5V0), U1.MH$4 (5V0), U1.SH$1 (5V0), U3.2 (EN), U3.8 (VIN), U3.9 (VIN)
GND: C1.2 (C2), C2.2 (C2), C3.2 (C2), C4.2 (C2), C5.2 (C2), C6.2 (C2), CON1.2, CON2.4, CON3.4, CON4.4, CON5.3, CON6.3, CON7.3, CON8.3, D1.A, R9.1, U1.DBG$1 (GND), U1.MH$6 (GND), U1.MH$9 (GND), U1.MH$14 (GND), U1.MH$20 (GND), U1.MH$25 (GND), U1.SH$2 (GND), U2.4 (GND), U2.9 (GND), U3.7 (AGND), U3.10 (PGND), U3.11 (PGND); also elsewhere on the board
I2C0_SCL: R4.1, U1.MH$5 ((I2C0_SCL)PA11); also elsewhere on the board
I2C0_SDA: R5.1, U1.MH$3 ((I2C0_SDA)PA12); also elsewhere on the board
I2C1_SCL: R6.1, U1.MH$18 ((I2C1_SCL)PA18), U2.3 (SCLIN)
I2C1_SDA: R7.1, U1.MH$16 ((I2C1_SDA)PA19), U2.6 (SDAIN)
I2C_SCL_EXT: CON2.3, CON3.3, CON4.3, R3.1, U2.2 (SCLOUT)
I2C_SDA_EXT: CON2.2, CON3.2, CON4.2, R2.1, U2.7 (SDAOUT)
unnamed: CON1.1, F1.1
unnamed: R1.1, U2.1 (ENABLE)
OW_BUS: CON5.2, CON6.2, CON7.2, CON8.2
PSU1_I2C_EN: U1.MH$12 (PA7); also elsewhere on the board
PSU2_I2C_EN: U1.MH$26 (PA10); also elsewhere on the board

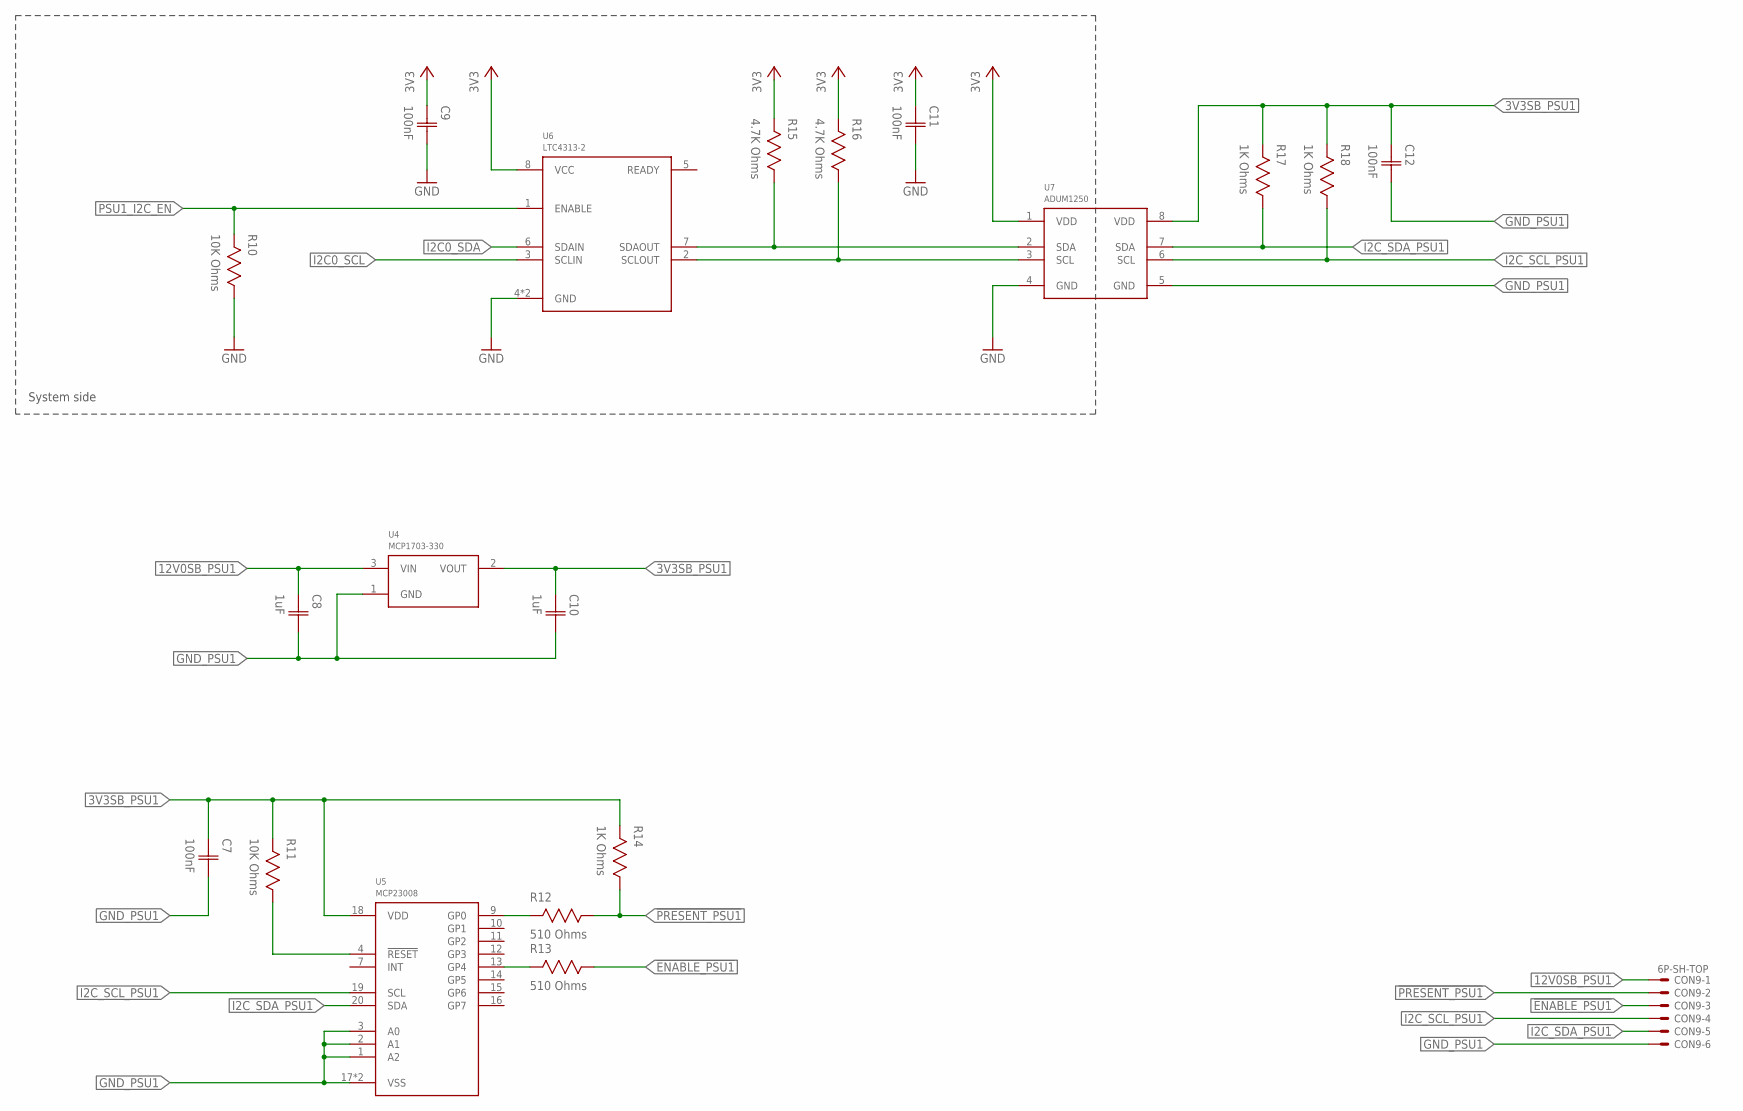
[picture p193: schematic qo-100-opi-control-hat.sch, sheet 2, PSU #1 Interface]

Parts:
C7, C9, C11, C12: 100nF; CAP0603
C8, C10: 1uF; CAP0603
CON9: 6P-SH-TOP; SH-06-TOP
R10, R11: 10K Ohms; RES0603
R12, R13: 510 Ohms; RES0603
R14, R17, R18: 1K Ohms; RES0603
R15, R16: 4.7K Ohms; RES0603
U4: MCP1703-330; SOT23
U5: MCP23008; QFN20
U6: LTC4313-2; DFN8
U7: ADUM1250; SOIC8

Connections:
3V3: C9.1 (C1), C11.1 (C1), R15.2, R16.2, U6.8 (VCC), U7.1 (VDD); also elsewhere on the board
3V3SB_PSU1: C7.1 (C1), C10.1 (C1), C12.1 (C1), R11.2, R14.2, R17.2, R18.2, U4.2 (VOUT), U5.18 (VDD), U7.8 (VDD)
12V0SB_PSU1: C8.1 (C1), CON9.1, U4.3 (VIN)
!ENABLE_PSU1: CON9.3, R13.1
!PRESENT_PSU1: CON9.2, R12.1, R14.1
GND: C9.2 (C2), C11.2 (C2), R10.1, U6.4 (GND), U6.9 (GND), U7.4 (GND); also elsewhere on the board
GND_PSU1: C7.2 (C2), C8.2 (C2), C10.2 (C2), C12.2 (C2), CON9.6, U4.1 (GND), U5.1 (A2), U5.2 (A1), U5.3 (A0), U5.17 (VSS), U5.PAD (VSS), U7.5 (GND)
I2C0_SCL: U6.3 (SCLIN); also elsewhere on the board
I2C0_SDA: U6.6 (SDAIN); also elsewhere on the board
I2C_SCL_PSU1: CON9.4, R18.1, U5.19 (SCL), U7.6 (SCL)
I2C_SDA_PSU1: CON9.5, R17.1, U5.20 (SDA), U7.7 (SDA)
unnamed: R16.1, U6.2 (SCLOUT), U7.3 (SCL)
unnamed: R15.1, U6.7 (SDAOUT), U7.2 (SDA)
unnamed: R11.1, U5.4 (!RESET)
unnamed: R13.2, U5.13 (GP4)
unnamed: R12.2, U5.9 (GP0)
PSU1_I2C_EN: R10.2, U6.1 (ENABLE); also elsewhere on the board

Notes on the sheet:
System side
