vankxr/qo-100-tools/pcb/opi-control-hat/qo-100-opi-control-hat.brd

## EAGLE design pcb/opi-control-hat/qo-100-opi-control-hat.brd (continued)

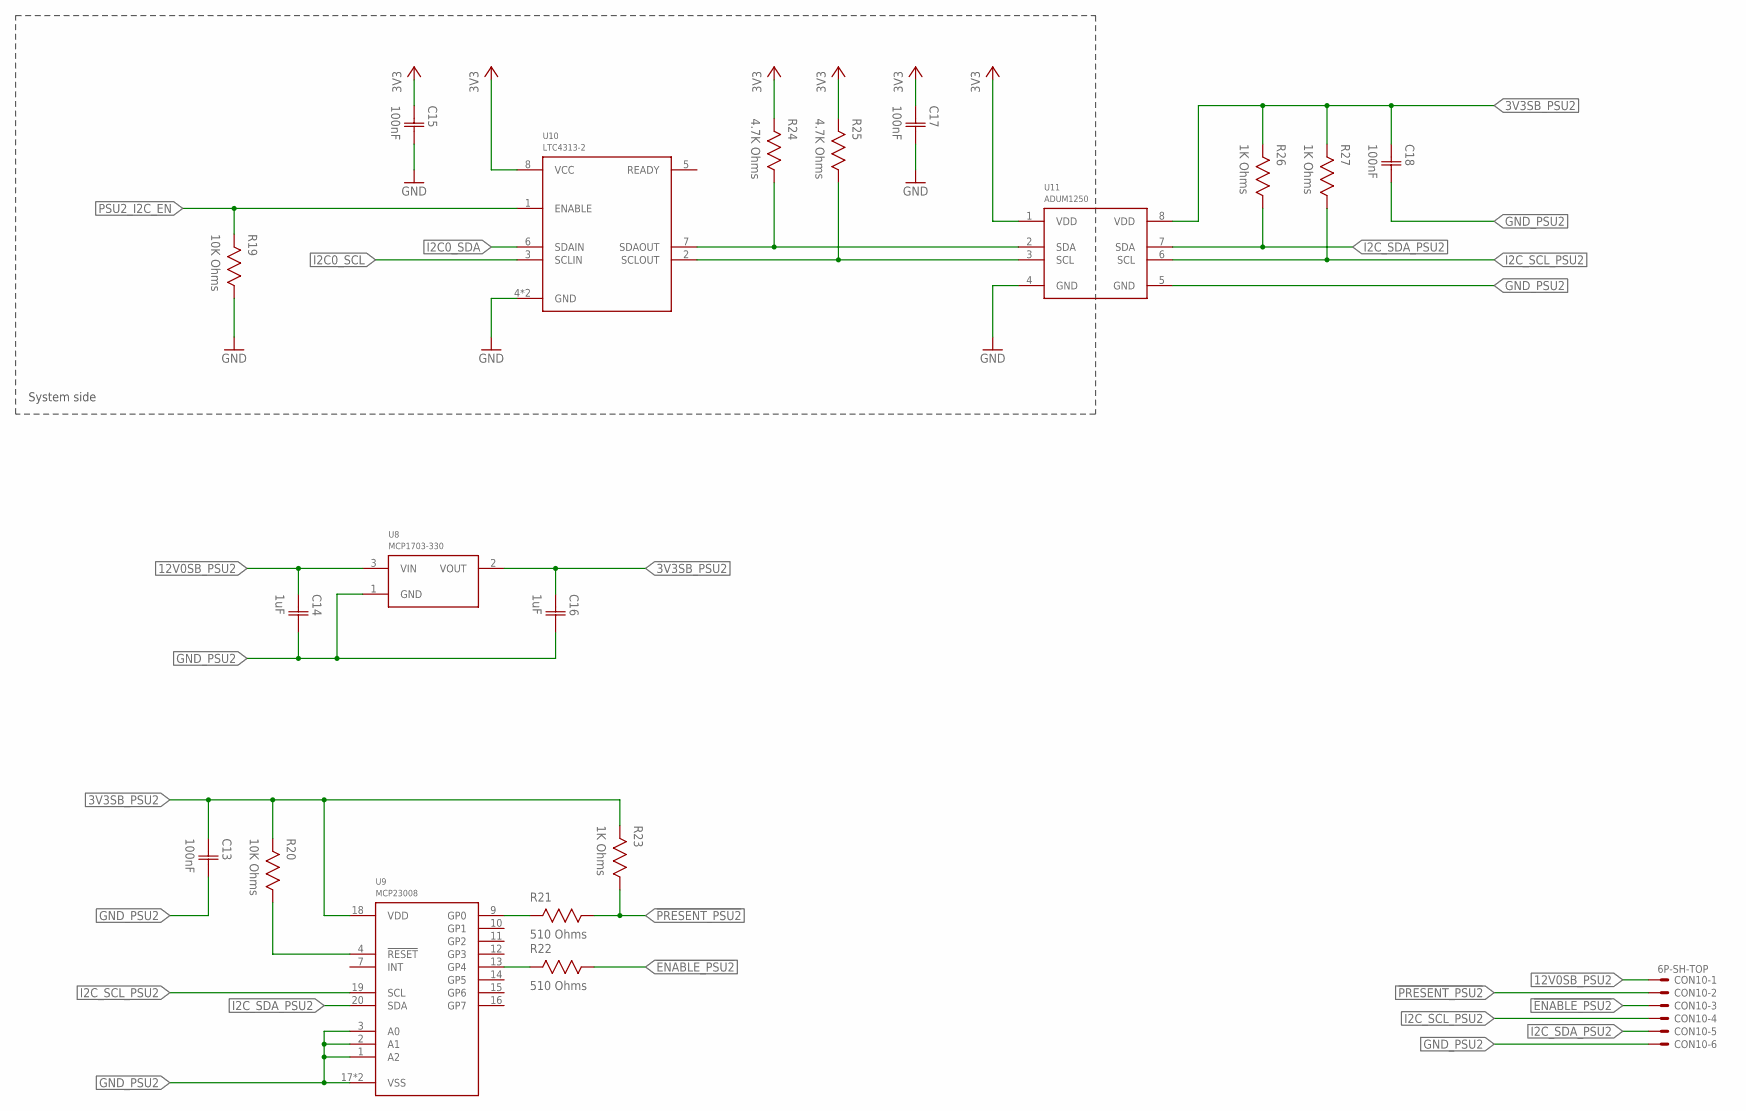
[picture p194: schematic qo-100-opi-control-hat.sch, sheet 3, PSU #2 Interface]

Parts:
C13, C15, C17, C18: 100nF; CAP0603
C14, C16: 1uF; CAP0603
CON10: 6P-SH-TOP; SH-06-TOP
R19, R20: 10K Ohms; RES0603
R21, R22: 510 Ohms; RES0603
R23, R26, R27: 1K Ohms; RES0603
R24, R25: 4.7K Ohms; RES0603
U8: MCP1703-330; SOT23
U9: MCP23008; QFN20
U10: LTC4313-2; DFN8
U11: ADUM1250; SOIC8

Connections:
3V3: C15.1 (C1), C17.1 (C1), R24.2, R25.2, U10.8 (VCC), U11.1 (VDD); also elsewhere on the board
3V3SB_PSU2: C13.1 (C1), C16.1 (C1), C18.1 (C1), R20.2, R23.2, R26.2, R27.2, U8.2 (VOUT), U9.18 (VDD), U11.8 (VDD)
12V0SB_PSU2: C14.1 (C1), CON10.1, U8.3 (VIN)
!ENABLE_PSU2: CON10.3, R22.1
!PRESENT_PSU2: CON10.2, R21.1, R23.1
GND: C15.2 (C2), C17.2 (C2), R19.1, U10.4 (GND), U10.9 (GND), U11.4 (GND); also elsewhere on the board
GND_PSU2: C13.2 (C2), C14.2 (C2), C16.2 (C2), C18.2 (C2), CON10.6, U8.1 (GND), U9.1 (A2), U9.2 (A1), U9.3 (A0), U9.17 (VSS), U9.PAD (VSS), U11.5 (GND)
I2C0_SCL: U10.3 (SCLIN); also elsewhere on the board
I2C0_SDA: U10.6 (SDAIN); also elsewhere on the board
I2C_SCL_PSU2: CON10.4, R27.1, U9.19 (SCL), U11.6 (SCL)
I2C_SDA_PSU2: CON10.5, R26.1, U9.20 (SDA), U11.7 (SDA)
unnamed: R25.1, U10.2 (SCLOUT), U11.3 (SCL)
unnamed: R24.1, U10.7 (SDAOUT), U11.2 (SDA)
unnamed: R20.1, U9.4 (!RESET)
unnamed: R22.2, U9.13 (GP4)
unnamed: R21.2, U9.9 (GP0)
PSU2_I2C_EN: R19.2, U10.1 (ENABLE); also elsewhere on the board

Notes on the sheet:
System side

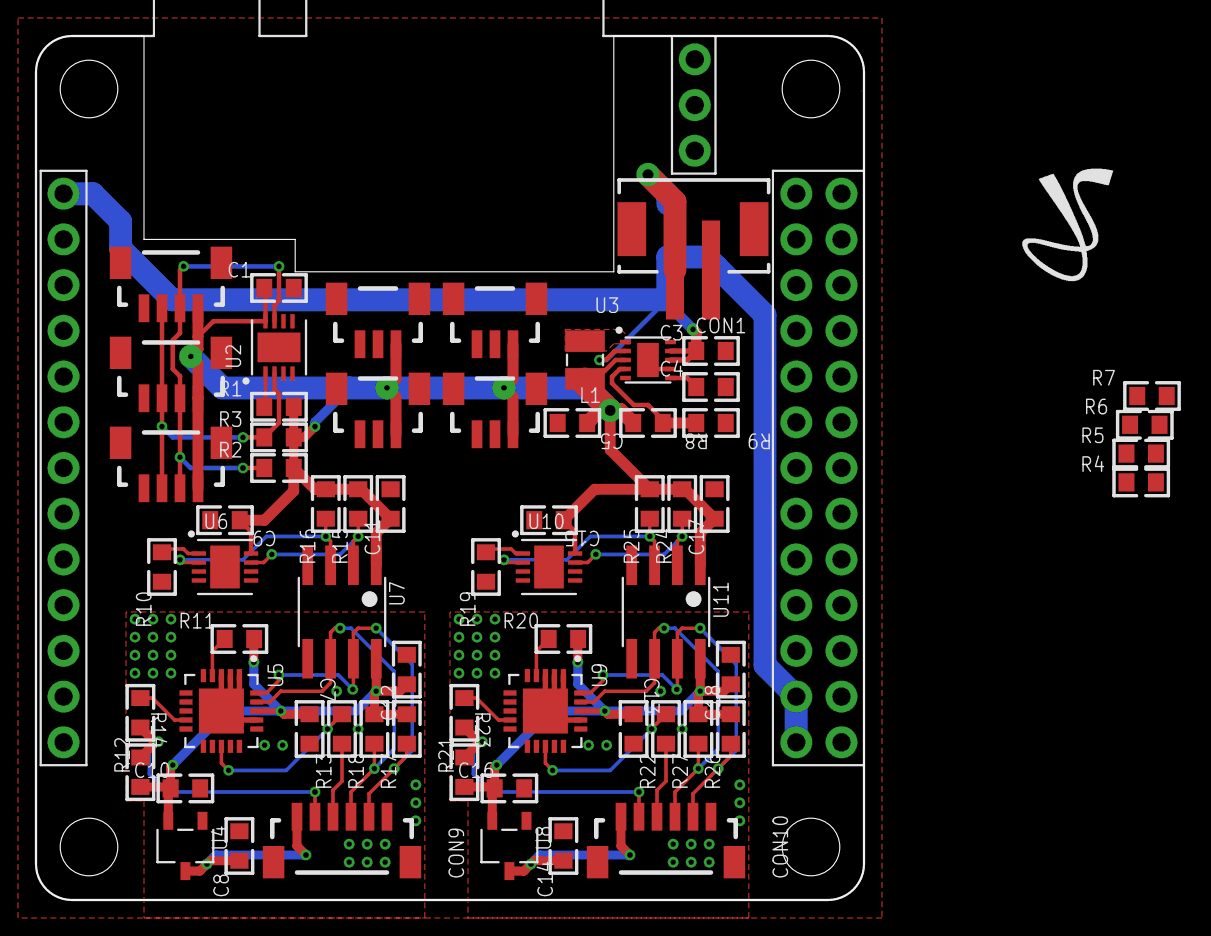
[picture p195: board qo-100-opi-control-hat.brd from above]

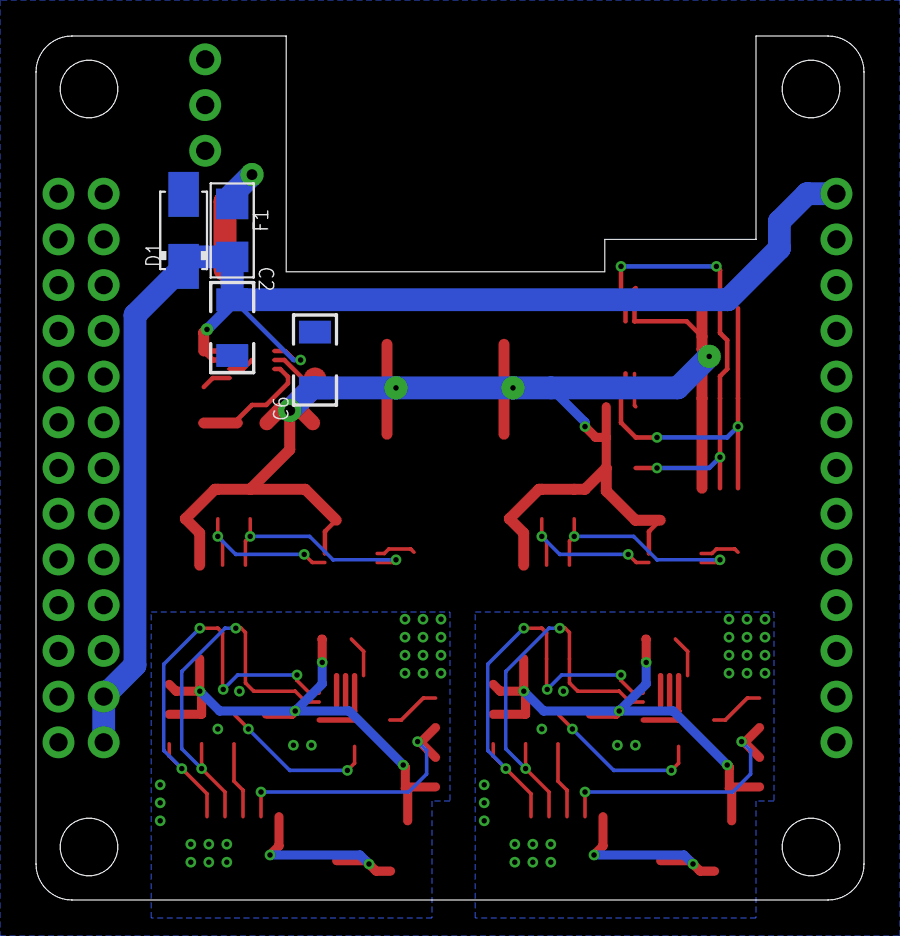
[picture p196: board qo-100-opi-control-hat.brd from below]

Board: 2 copper layers, 46.0 x 48.0 mm, 70 parts (4 on the bottom side), 41 nets.
