vankxr/qo-100-tools/pcb/generic-filter/qo-100-generic-filter.brd

## EAGLE design pcb/generic-filter/qo-100-generic-filter.brd (2020-09-07)

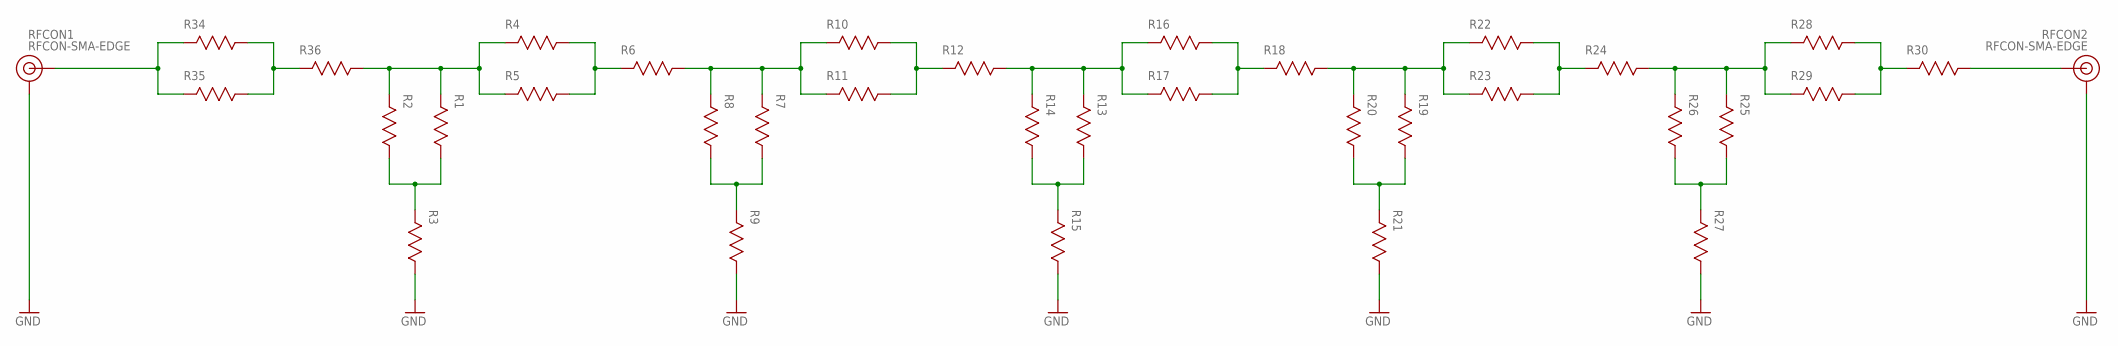
[picture p197: schematic qo-100-generic-filter.sch]

Parts:
R1, R2, R3, R4, R5, R6, R7, R8, R9, R10, R11, R12, R13, R14, R15, R16, R17, R18, R19, R20, R21, R22, R23, R24, R25, R26, R27, R28, R29, R30, R34, R35, R36: RESISTOR-0603; RES0603
RFCON1, RFCON2: RFCON-SMA-EDGE; SMA-EDGE

Connections:
GND: R3.1, R9.1, R15.1, R21.1, R27.1, RFCON1.GND@0 (GND), RFCON1.GND@1 (GND), RFCON1.GND@2 (GND), RFCON1.GND@3 (GND), RFCON2.GND@0 (GND), RFCON2.GND@1 (GND), RFCON2.GND@2 (GND), RFCON2.GND@3 (GND)
unnamed: R1.2, R2.2, R4.2, R5.2, R36.1
unnamed: R1.1, R2.1, R3.2
unnamed: R6.1, R7.2, R8.2, R10.2, R11.2
unnamed: R4.1, R5.1, R6.2
unnamed: R7.1, R8.1, R9.2
unnamed: R10.1, R11.1, R12.2
unnamed: R12.1, R13.2, R14.2, R16.2, R17.2
unnamed: R13.1, R14.1, R15.2
unnamed: R16.1, R17.1, R18.2
unnamed: R18.1, R19.2, R20.2, R22.2, R23.2
unnamed: R19.1, R20.1, R21.2
unnamed: R22.1, R23.1, R24.2
unnamed: R24.1, R25.2, R26.2, R28.2, R29.2
unnamed: R25.1, R26.1, R27.2
unnamed: R28.1, R29.1, R30.2
unnamed: R30.1, RFCON2.SIG (SIGNAL)
unnamed: R34.2, R35.2, RFCON1.SIG (SIGNAL)
unnamed: R34.1, R35.1, R36.2

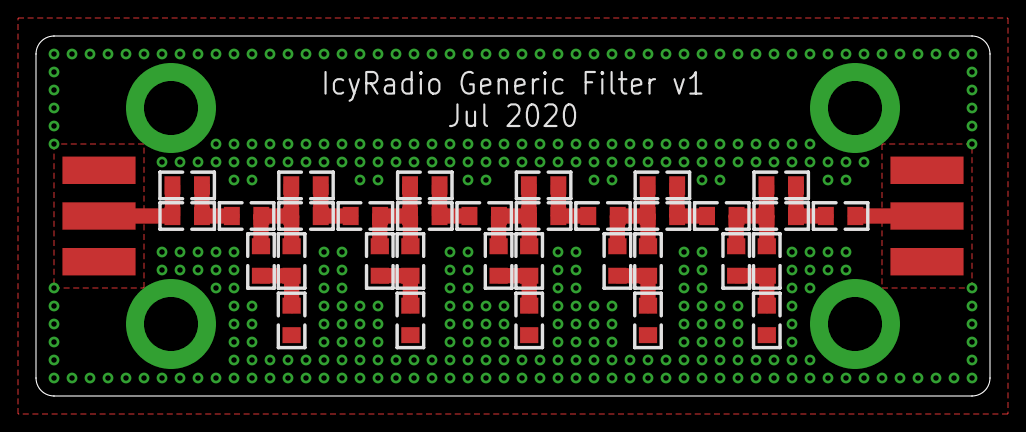
[picture p198: board qo-100-generic-filter.brd from above]

Board: 2 copper layers, 53.0 x 20.0 mm, 35 parts (0 on the bottom side), 19 nets.
