vankxr/qo-100-tools/software/pa-bias-controller/src/main.c

#include <em_device.h>
#include <stdlib.h>
#include <math.h>
#include "debug_macros.h"
#include "utils.h"
#include "nvic.h"
#include "atomic.h"
#include "systick.h"
#include "rmu.h"
#include "emu.h"
#include "cmu.h"
#include "gpio.h"
#include "msc.h"
#include "rtcc.h"
#include "adc.h"
#include "crc.h"
#include "usart.h"
#include "i2c.h"
#include "max11300.h"
#include "mcp4728.h"
#include "wdog.h"

// Structs

// Helper macros
#define I2C_SLAVE_ADDRESS                       0x3B
#define I2C_SLAVE_REGISTER_COUNT                256
#define I2C_SLAVE_REGISTER(t, a)                (*(t *)&ubI2CRegister[(a)])
#define I2C_SLAVE_REGISTER_WRITE_MASK(t, a)     (*(t *)&ubI2CRegisterWriteMask[(a)])
#define I2C_SLAVE_REGISTER_READ_MASK(t, a)      (*(t *)&ubI2CRegisterReadMask[(a)])
#define I2C_SLAVE_REGISTER_STATUS               0x00 // 8-bit
#define I2C_SLAVE_REGISTER_CONFIG               0x01 // 8-bit
#define I2C_SLAVE_REGISTER_PA1_VGG_RAW_VOLTAGE  0x10 // 32-bit
#define I2C_SLAVE_REGISTER_PA1_VGG_VOLTAGE      0x14 // 32-bit
#define I2C_SLAVE_REGISTER_PA1_VDD_VOLTAGE      0x18 // 32-bit
#define I2C_SLAVE_REGISTER_PA1_IDD_CURRENT      0x1C // 32-bit
#define I2C_SLAVE_REGISTER_PA1_TEMP_STATUS      0x20 // 8-bit
#define I2C_SLAVE_REGISTER_PA1_TEMP_CONFIG      0x21 // 8-bit
#define I2C_SLAVE_REGISTER_PA1_TEMP             0x24 // 32-bit
#define I2C_SLAVE_REGISTER_PA1_TEMP_HIGH        0x28 // 32-bit
#define I2C_SLAVE_REGISTER_PA1_TEMP_LOW         0x2C // 32-bit
#define I2C_SLAVE_REGISTER_PA2_VGG_RAW_VOLTAGE  0x30 // 32-bit
#define I2C_SLAVE_REGISTER_PA2_VGG_VOLTAGE      0x34 // 32-bit
#define I2C_SLAVE_REGISTER_PA2_VDD_VOLTAGE      0x38 // 32-bit
#define I2C_SLAVE_REGISTER_PA2_IDD_CURRENT      0x3C // 32-bit
#define I2C_SLAVE_REGISTER_PA2_TEMP_STATUS      0x40 // 8-bit
#define I2C_SLAVE_REGISTER_PA2_TEMP_CONFIG      0x41 // 8-bit
#define I2C_SLAVE_REGISTER_PA2_TEMP             0x44 // 32-bit
#define I2C_SLAVE_REGISTER_PA2_TEMP_HIGH        0x48 // 32-bit
#define I2C_SLAVE_REGISTER_PA2_TEMP_LOW         0x4C // 32-bit
#define I2C_SLAVE_REGISTER_TEC1_VOLTAGE         0x60 // 32-bit
#define I2C_SLAVE_REGISTER_TEC2_VOLTAGE         0x64 // 32-bit
#define I2C_SLAVE_REGISTER_TEC3_VOLTAGE         0x68 // 32-bit
#define I2C_SLAVE_REGISTER_TEC4_VOLTAGE         0x6C // 32-bit
#define I2C_SLAVE_REGISTER_VIN_VOLTAGE          0xB0 // 32-bit
#define I2C_SLAVE_REGISTER_5V0_VOLTAGE          0xB4 // 32-bit
#define I2C_SLAVE_REGISTER_AVDD_VOLTAGE         0xC0 // 32-bit
#define I2C_SLAVE_REGISTER_DVDD_VOLTAGE         0xC4 // 32-bit
#define I2C_SLAVE_REGISTER_IOVDD_VOLTAGE        0xC8 // 32-bit
#define I2C_SLAVE_REGISTER_CORE_VOLTAGE         0xCC // 32-bit
#define I2C_SLAVE_REGISTER_EMU_TEMP             0xD0 // 32-bit
#define I2C_SLAVE_REGISTER_ADC_TEMP             0xD4 // 32-bit
#define I2C_SLAVE_REGISTER_AFE_TEMP             0xD8 // 32-bit
#define I2C_SLAVE_REGISTER_UPTIME               0xE0 // 64-bit
#define I2C_SLAVE_REGISTER_RESET_DATA           0xE8 // 8-bit
#define I2C_SLAVE_REGISTER_SW_VERSION           0xF4 // 16-bit
#define I2C_SLAVE_REGISTER_DEV_UIDL             0xF8 // 32-bit
#define I2C_SLAVE_REGISTER_DEV_UIDH             0xFC // 32-bit

#define PA1_INDEX   0
#define PA2_INDEX   1

#define TEC1_INDEX  0
#define TEC2_INDEX  1
#define TEC3_INDEX  2
#define TEC4_INDEX  3

// Forward declarations
static void reset() __attribute__((noreturn));
static void sleep();

static uint32_t get_free_ram();

static void get_device_core_name(char *pszDeviceCoreName, uint32_t ulDeviceCoreNameSize);
static void get_device_name(char *pszDeviceName, uint32_t ulDeviceNameSize);
static uint16_t get_device_revision();

static void wdog_warning_isr();

static void i2c_slave_register_init();
static uint8_t i2c_slave_addr_isr(uint8_t ubRnW);
static uint8_t i2c_slave_tx_data_isr();
static uint8_t i2c_slave_rx_data_isr(uint8_t ubData);

static void afe_init();
static void afe_pa_set_raw_vgg(uint8_t ubPAIndex, float fVoltage);
static float afe_pa_get_raw_vgg(uint8_t ubPAIndex);
static float afe_pa_get_vgg(uint8_t ubPAIndex);
static float afe_pa_get_vdd(uint8_t ubPAIndex);
static float afe_pa_get_idd(uint8_t ubPAIndex);
static float afe_pa_get_temperature(uint8_t ubPAIndex);

static void tec_init();
static void tec_set_channel_voltage(uint8_t ubChannel, float fVoltage);
static float tec_get_channel_voltage(uint8_t ubChannel);

// Variables
volatile uint8_t ubI2CRegister[I2C_SLAVE_REGISTER_COUNT];
volatile uint8_t ubI2CRegisterWriteMask[I2C_SLAVE_REGISTER_COUNT];
volatile uint8_t ubI2CRegisterReadMask[I2C_SLAVE_REGISTER_COUNT];
volatile uint8_t ubI2CBuffer[I2C_SLAVE_REGISTER_COUNT];
volatile uint8_t ubI2CRegisterPointer = 0x00;
volatile uint8_t ubI2CByteCount = 0;
volatile uint8_t ubI2CReadSize = 0;
volatile uint8_t ubI2CChecksum = 0;
volatile uint8_t ubI2CChecksumOK = 0;
volatile uint8_t ubPAGateVoltageChanged = 0;
volatile uint8_t ubTECVoltageChanged = 0;
uint8_t ubTECDACInitialized = 0;

// ISRs

// Functions
void reset()
{
    SCB->AIRCR = 0x05FA0000 | _VAL2FLD(SCB_AIRCR_SYSRESETREQ, 1);

    while(1);
}
void sleep()
{
    rtcc_set_alarm(rtcc_get_time() + 5);

    SCB->SCR |= SCB_SCR_SLEEPDEEP_Msk; // Configure Deep Sleep (EM2/3)

    ATOMIC_BLOCK(ATOMIC_RESTORESTATE)
    {
        IRQ_CLEAR(RTCC_IRQn);

        __DMB(); // Wait for all memory transactions to finish before memory access
        __DSB(); // Wait for all memory transactions to finish before executing instructions
        __ISB(); // Wait for all memory transactions to finish before fetching instructions
        __SEV(); // Set the event flag to ensure the next WFE will be a NOP
        __WFE(); // NOP and clear the event flag
        __WFE(); // Wait for event
        __NOP(); // Prevent debugger crashes

        cmu_init();
        cmu_update_clocks();
    }
}

uint32_t get_free_ram()
{
    ATOMIC_BLOCK(ATOMIC_RESTORESTATE)
    {
        extern void *_sbrk(int);

        void *pCurrentHeap = _sbrk(1);

        if(!pCurrentHeap)
            return 0;

        uint32_t ulFreeRAM = (uint32_t)__get_MSP() - (uint32_t)pCurrentHeap;

        _sbrk(-1);

        return ulFreeRAM;
    }
}

void get_device_core_name(char *pszDeviceCoreName, uint32_t ulDeviceCoreNameSize)
{
    uint8_t ubImplementer = (SCB->CPUID & SCB_CPUID_IMPLEMENTER_Msk) >> SCB_CPUID_IMPLEMENTER_Pos;
    const char* szImplementer = "?";

    switch(ubImplementer)
    {
        case 0x41: szImplementer = "ARM"; break;
    }

    uint16_t usPartNo = (SCB->CPUID & SCB_CPUID_PARTNO_Msk) >> SCB_CPUID_PARTNO_Pos;
    const char* szPartNo = "?";

    switch(usPartNo)
    {
        case 0xC20: szPartNo = "Cortex-M0"; break;
        case 0xC60: szPartNo = "Cortex-M0+"; break;
        case 0xC21: szPartNo = "Cortex-M1"; break;
        case 0xD20: szPartNo = "Cortex-M23"; break;
        case 0xC23: szPartNo = "Cortex-M3"; break;
        case 0xD21: szPartNo = "Cortex-M33"; break;
        case 0xC24: szPartNo = "Cortex-M4"; break;
        case 0xC27: szPartNo = "Cortex-M7"; break;
    }

    uint8_t ubVariant = (SCB->CPUID & SCB_CPUID_VARIANT_Msk) >> SCB_CPUID_VARIANT_Pos;
    uint8_t ubRevision = (SCB->CPUID & SCB_CPUID_REVISION_Msk) >> SCB_CPUID_REVISION_Pos;

    snprintf(pszDeviceCoreName, ulDeviceCoreNameSize, "%s %s r%hhup%hhu", szImplementer, szPartNo, ubVariant, ubRevision);
}
void get_device_name(char *pszDeviceName, uint32_t ulDeviceNameSize)
{
    uint8_t ubFamily = (DEVINFO->PART & _DEVINFO_PART_DEVICE_FAMILY_MASK) >> _DEVINFO_PART_DEVICE_FAMILY_SHIFT;
    const char* szFamily = "?";

    switch(ubFamily)
    {
        case 0x10: szFamily = "EFR32MG1P";  break;
        case 0x11: szFamily = "EFR32MG1B";  break;
        case 0x12: szFamily = "EFR32MG1V";  break;
        case 0x13: szFamily = "EFR32BG1P";  break;
        case 0x14: szFamily = "EFR32BG1B";  break;
        case 0x15: szFamily = "EFR32BG1V";  break;
        case 0x19: szFamily = "EFR32FG1P";  break;
        case 0x1A: szFamily = "EFR32FG1B";  break;
        case 0x1B: szFamily = "EFR32FG1V";  break;
        case 0x1C: szFamily = "EFR32MG12P"; break;
        case 0x1D: szFamily = "EFR32MG12B"; break;
        case 0x1E: szFamily = "EFR32MG12V"; break;
        case 0x1F: szFamily = "EFR32BG12P"; break;
        case 0x20: szFamily = "EFR32BG12B"; break;
        case 0x21: szFamily = "EFR32BG12V"; break;
        case 0x25: szFamily = "EFR32FG12P"; break;
        case 0x26: szFamily = "EFR32FG12B"; break;
        case 0x27: szFamily = "EFR32FG12V"; break;
        case 0x28: szFamily = "EFR32MG13P"; break;
        case 0x29: szFamily = "EFR32MG13B"; break;
        case 0x2A: szFamily = "EFR32MG13V"; break;
        case 0x2B: szFamily = "EFR32BG13P"; break;
        case 0x2C: szFamily = "EFR32BG13B"; break;
        case 0x2D: szFamily = "EFR32BG13V"; break;
        case 0x2E: szFamily = "EFR32ZG13P"; break;
        case 0x31: szFamily = "EFR32FG13P"; break;
        case 0x32: szFamily = "EFR32FG13B"; break;
        case 0x33: szFamily = "EFR32FG13V"; break;
        case 0x34: szFamily = "EFR32MG14P"; break;
        case 0x35: szFamily = "EFR32MG14B"; break;
        case 0x36: szFamily = "EFR32MG14V"; break;
        case 0x37: szFamily = "EFR32BG14P"; break;
        case 0x38: szFamily = "EFR32BG14B"; break;
        case 0x39: szFamily = "EFR32BG14V"; break;
        case 0x3A: szFamily = "EFR32ZG14P"; break;
        case 0x3D: szFamily = "EFR32FG14P"; break;
        case 0x3E: szFamily = "EFR32FG14B"; break;
        case 0x3F: szFamily = "EFR32FG14V"; break;
        case 0x47: szFamily = "EFM32G";     break;
        case 0x48: szFamily = "EFM32GG";    break;
        case 0x49: szFamily = "EFM32TG";    break;
        case 0x4A: szFamily = "EFM32LG";    break;
        case 0x4B: szFamily = "EFM32WG";    break;
        case 0x4C: szFamily = "EFM32ZG";    break;
        case 0x4D: szFamily = "EFM32HG";    break;
        case 0x51: szFamily = "EFM32PG1B";  break;
        case 0x53: szFamily = "EFM32JG1B";  break;
        case 0x55: szFamily = "EFM32PG12B"; break;
        case 0x57: szFamily = "EFM32JG12B"; break;
        case 0x64: szFamily = "EFM32GG11B"; break;
        case 0x67: szFamily = "EFM32TG11B"; break;
        case 0x6A: szFamily = "EFM32GG12B"; break;
        case 0x78: szFamily = "EZR32LG";    break;
        case 0x79: szFamily = "EZR32WG";    break;
        case 0x7A: szFamily = "EZR32HG";    break;
    }

    uint8_t ubPackage = (DEVINFO->MEMINFO & _DEVINFO_MEMINFO_PKGTYPE_MASK) >> _DEVINFO_MEMINFO_PKGTYPE_SHIFT;
    char cPackage = '?';

    if(ubPackage == 74)
        cPackage = '?';
    else if(ubPackage == 76)
        cPackage = 'L';
    else if(ubPackage == 77)
        cPackage = 'M';
    else if(ubPackage == 81)
        cPackage = 'Q';

    uint8_t ubTempGrade = (DEVINFO->MEMINFO & _DEVINFO_MEMINFO_TEMPGRADE_MASK) >> _DEVINFO_MEMINFO_TEMPGRADE_SHIFT;
    char cTempGrade = '?';

    if(ubTempGrade == 0)
        cTempGrade = 'G';
    else if(ubTempGrade == 1)
        cTempGrade = 'I';
    else if(ubTempGrade == 2)
        cTempGrade = '?';
    else if(ubTempGrade == 3)
        cTempGrade = '?';

    uint16_t usPartNumber = (DEVINFO->PART & _DEVINFO_PART_DEVICE_NUMBER_MASK) >> _DEVINFO_PART_DEVICE_NUMBER_SHIFT;
    uint8_t ubPinCount = (DEVINFO->MEMINFO & _DEVINFO_MEMINFO_PINCOUNT_MASK) >> _DEVINFO_MEMINFO_PINCOUNT_SHIFT;

    snprintf(pszDeviceName, ulDeviceNameSize, "%s%huF%hu%c%c%hhu", szFamily, usPartNumber, FLASH_SIZE >> 10, cTempGrade, cPackage, ubPinCount);
}
uint16_t get_device_revision()
{
    uint16_t usRevision;

    /* CHIP MAJOR bit [3:0]. */
    usRevision = ((ROMTABLE->PID0 & _ROMTABLE_PID0_REVMAJOR_MASK) >> _ROMTABLE_PID0_REVMAJOR_SHIFT) << 8;
    /* CHIP MINOR bit [7:4]. */
    usRevision |= ((ROMTABLE->PID2 & _ROMTABLE_PID2_REVMINORMSB_MASK) >> _ROMTABLE_PID2_REVMINORMSB_SHIFT) << 4;
    /* CHIP MINOR bit [3:0]. */
    usRevision |= (ROMTABLE->PID3 & _ROMTABLE_PID3_REVMINORLSB_MASK) >> _ROMTABLE_PID3_REVMINORLSB_SHIFT;

    return usRevision;
}

void wdog_warning_isr()
{
    DBGPRINTLN_CTX("Watchdog warning!");
}

void i2c_slave_register_init()
{
    ATOMIC_BLOCK(ATOMIC_RESTORESTATE)
    {
        I2C_SLAVE_REGISTER              (uint8_t,  I2C_SLAVE_REGISTER_STATUS)               = 0x00 | (ubTECDACInitialized ? BIT(2) : 0);
        I2C_SLAVE_REGISTER_WRITE_MASK   (uint8_t,  I2C_SLAVE_REGISTER_STATUS)               = 0x00;
        I2C_SLAVE_REGISTER_READ_MASK    (uint8_t,  I2C_SLAVE_REGISTER_STATUS)               = 0xFF;
        I2C_SLAVE_REGISTER              (uint8_t,  I2C_SLAVE_REGISTER_CONFIG)               = 0x00;
        I2C_SLAVE_REGISTER_WRITE_MASK   (uint8_t,  I2C_SLAVE_REGISTER_CONFIG)               = 0xFF;
        I2C_SLAVE_REGISTER_READ_MASK    (uint8_t,  I2C_SLAVE_REGISTER_CONFIG)               = 0xFF;
        I2C_SLAVE_REGISTER              (float,    I2C_SLAVE_REGISTER_PA1_VGG_RAW_VOLTAGE)  = -1.f;
        I2C_SLAVE_REGISTER_WRITE_MASK   (uint32_t, I2C_SLAVE_REGISTER_PA1_VGG_RAW_VOLTAGE)  = 0xFFFFFFFF;
        I2C_SLAVE_REGISTER_READ_MASK    (uint32_t, I2C_SLAVE_REGISTER_PA1_VGG_RAW_VOLTAGE)  = 0xFFFFFFFF;
        I2C_SLAVE_REGISTER              (float,    I2C_SLAVE_REGISTER_PA1_VGG_VOLTAGE)      = -1.f;
        I2C_SLAVE_REGISTER_WRITE_MASK   (uint32_t, I2C_SLAVE_REGISTER_PA1_VGG_VOLTAGE)      = 0x00000000;
        I2C_SLAVE_REGISTER_READ_MASK    (uint32_t, I2C_SLAVE_REGISTER_PA1_VGG_VOLTAGE)      = 0xFFFFFFFF;
        I2C_SLAVE_REGISTER              (float,    I2C_SLAVE_REGISTER_PA1_VDD_VOLTAGE)      = -1.f;
        I2C_SLAVE_REGISTER_WRITE_MASK   (uint32_t, I2C_SLAVE_REGISTER_PA1_VDD_VOLTAGE)      = 0x00000000;
        I2C_SLAVE_REGISTER_READ_MASK    (uint32_t, I2C_SLAVE_REGISTER_PA1_VDD_VOLTAGE)      = 0xFFFFFFFF;
        I2C_SLAVE_REGISTER              (float,    I2C_SLAVE_REGISTER_PA1_IDD_CURRENT)      = -1.f;
        I2C_SLAVE_REGISTER_WRITE_MASK   (uint32_t, I2C_SLAVE_REGISTER_PA1_IDD_CURRENT)      = 0x00000000;
        I2C_SLAVE_REGISTER_READ_MASK    (uint32_t, I2C_SLAVE_REGISTER_PA1_IDD_CURRENT)      = 0xFFFFFFFF;
        I2C_SLAVE_REGISTER              (uint8_t,  I2C_SLAVE_REGISTER_PA1_TEMP_STATUS)      = 0x00;
        I2C_SLAVE_REGISTER_WRITE_MASK   (uint8_t,  I2C_SLAVE_REGISTER_PA1_TEMP_STATUS)      = 0x00;
        I2C_SLAVE_REGISTER_READ_MASK    (uint8_t,  I2C_SLAVE_REGISTER_PA1_TEMP_STATUS)      = 0xFF;
        I2C_SLAVE_REGISTER              (uint8_t,  I2C_SLAVE_REGISTER_PA1_TEMP_CONFIG)      = 0x00;
        I2C_SLAVE_REGISTER_WRITE_MASK   (uint8_t,  I2C_SLAVE_REGISTER_PA1_TEMP_CONFIG)      = 0xFF;
        I2C_SLAVE_REGISTER_READ_MASK    (uint8_t,  I2C_SLAVE_REGISTER_PA1_TEMP_CONFIG)      = 0xFF;
        I2C_SLAVE_REGISTER              (float,    I2C_SLAVE_REGISTER_PA1_TEMP)             = -1.f;
        I2C_SLAVE_REGISTER_WRITE_MASK   (uint32_t, I2C_SLAVE_REGISTER_PA1_TEMP)             = 0x00000000;
        I2C_SLAVE_REGISTER_READ_MASK    (uint32_t, I2C_SLAVE_REGISTER_PA1_TEMP)             = 0xFFFFFFFF;
        I2C_SLAVE_REGISTER              (float,    I2C_SLAVE_REGISTER_PA1_TEMP_HIGH)        = -1.f;
        I2C_SLAVE_REGISTER_WRITE_MASK   (uint32_t, I2C_SLAVE_REGISTER_PA1_TEMP_HIGH)        = 0xFFFFFFFF;
        I2C_SLAVE_REGISTER_READ_MASK    (uint32_t, I2C_SLAVE_REGISTER_PA1_TEMP_HIGH)        = 0xFFFFFFFF;
        I2C_SLAVE_REGISTER              (float,    I2C_SLAVE_REGISTER_PA1_TEMP_LOW)         = -1.f;
        I2C_SLAVE_REGISTER_WRITE_MASK   (uint32_t, I2C_SLAVE_REGISTER_PA1_TEMP_LOW)         = 0xFFFFFFFF;
        I2C_SLAVE_REGISTER_READ_MASK    (uint32_t, I2C_SLAVE_REGISTER_PA1_TEMP_LOW)         = 0xFFFFFFFF;
        I2C_SLAVE_REGISTER              (float,    I2C_SLAVE_REGISTER_PA2_VGG_RAW_VOLTAGE)  = -1.f;
        I2C_SLAVE_REGISTER_WRITE_MASK   (uint32_t, I2C_SLAVE_REGISTER_PA2_VGG_RAW_VOLTAGE)  = 0xFFFFFFFF;
        I2C_SLAVE_REGISTER_READ_MASK    (uint32_t, I2C_SLAVE_REGISTER_PA2_VGG_RAW_VOLTAGE)  = 0xFFFFFFFF;
        I2C_SLAVE_REGISTER              (float,    I2C_SLAVE_REGISTER_PA2_VGG_VOLTAGE)      = -1.f;
        I2C_SLAVE_REGISTER_WRITE_MASK   (uint32_t, I2C_SLAVE_REGISTER_PA2_VGG_VOLTAGE)      = 0x00000000;
        I2C_SLAVE_REGISTER_READ_MASK    (uint32_t, I2C_SLAVE_REGISTER_PA2_VGG_VOLTAGE)      = 0xFFFFFFFF;
        I2C_SLAVE_REGISTER              (float,    I2C_SLAVE_REGISTER_PA2_VDD_VOLTAGE)      = -1.f;
        I2C_SLAVE_REGISTER_WRITE_MASK   (uint32_t, I2C_SLAVE_REGISTER_PA2_VDD_VOLTAGE)      = 0x00000000;
        I2C_SLAVE_REGISTER_READ_MASK    (uint32_t, I2C_SLAVE_REGISTER_PA2_VDD_VOLTAGE)      = 0xFFFFFFFF;
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
        I2C_SLAVE_REGISTER_READ_MASK    (uint32_t, I2C_SLAVE_REGISTER_DVDD_VOLTAGE)         = 0xFFFFFFFF;
        I2C_SLAVE_REGISTER              (float,    I2C_SLAVE_REGISTER_IOVDD_VOLTAGE)        = -1.f;
        I2C_SLAVE_REGISTER_WRITE_MASK   (uint32_t, I2C_SLAVE_REGISTER_IOVDD_VOLTAGE)        = 0x00000000;
        I2C_SLAVE_REGISTER_READ_MASK    (uint32_t, I2C_SLAVE_REGISTER_IOVDD_VOLTAGE)        = 0xFFFFFFFF;
        I2C_SLAVE_REGISTER              (float,    I2C_SLAVE_REGISTER_CORE_VOLTAGE)         = -1.f;
        I2C_SLAVE_REGISTER_WRITE_MASK   (uint32_t, I2C_SLAVE_REGISTER_CORE_VOLTAGE)         = 0x00000000;
        I2C_SLAVE_REGISTER_READ_MASK    (uint32_t, I2C_SLAVE_REGISTER_CORE_VOLTAGE)         = 0xFFFFFFFF;
        I2C_SLAVE_REGISTER              (float,    I2C_SLAVE_REGISTER_EMU_TEMP)             = -1.f;
        I2C_SLAVE_REGISTER_WRITE_MASK   (uint32_t, I2C_SLAVE_REGISTER_EMU_TEMP)             = 0x00000000;
        I2C_SLAVE_REGISTER_READ_MASK    (uint32_t, I2C_SLAVE_REGISTER_EMU_TEMP)             = 0xFFFFFFFF;
        I2C_SLAVE_REGISTER              (float,    I2C_SLAVE_REGISTER_ADC_TEMP)             = -1.f;
        I2C_SLAVE_REGISTER_WRITE_MASK   (uint32_t, I2C_SLAVE_REGISTER_ADC_TEMP)             = 0x00000000;
        I2C_SLAVE_REGISTER_READ_MASK    (uint32_t, I2C_SLAVE_REGISTER_ADC_TEMP)             = 0xFFFFFFFF;
        I2C_SLAVE_REGISTER              (float,    I2C_SLAVE_REGISTER_AFE_TEMP)             = -1.f;
        I2C_SLAVE_REGISTER_WRITE_MASK   (uint32_t, I2C_SLAVE_REGISTER_AFE_TEMP)             = 0x00000000;
        I2C_SLAVE_REGISTER_READ_MASK    (uint32_t, I2C_SLAVE_REGISTER_AFE_TEMP)             = 0xFFFFFFFF;
        I2C_SLAVE_REGISTER              (uint64_t, I2C_SLAVE_REGISTER_UPTIME)               = g_ullSystemTick / 1000;
        I2C_SLAVE_REGISTER_WRITE_MASK   (uint64_t, I2C_SLAVE_REGISTER_UPTIME)               = 0x0000000000000000;
        I2C_SLAVE_REGISTER_READ_MASK    (uint64_t, I2C_SLAVE_REGISTER_UPTIME)               = 0xFFFFFFFFFFFFFFFF;
      //I2C_SLAVE_REGISTER              (uint8_t,  I2C_SLAVE_REGISTER_RESET_DATA)           = 0x00;
        I2C_SLAVE_REGISTER_WRITE_MASK   (uint8_t,  I2C_SLAVE_REGISTER_RESET_DATA)           = 0x00;
        I2C_SLAVE_REGISTER_READ_MASK    (uint8_t,  I2C_SLAVE_REGISTER_RESET_DATA)           = 0xFF;
        I2C_SLAVE_REGISTER              (uint16_t, I2C_SLAVE_REGISTER_SW_VERSION)           = BUILD_VERSION;
        I2C_SLAVE_REGISTER_WRITE_MASK   (uint16_t, I2C_SLAVE_REGISTER_SW_VERSION)           = 0x0000;
        I2C_SLAVE_REGISTER_READ_MASK    (uint16_t, I2C_SLAVE_REGISTER_SW_VERSION)           = 0xFFFF;
        I2C_SLAVE_REGISTER              (uint32_t, I2C_SLAVE_REGISTER_DEV_UIDL)             = DEVINFO->UNIQUEL;
        I2C_SLAVE_REGISTER_WRITE_MASK   (uint32_t, I2C_SLAVE_REGISTER_DEV_UIDL)             = 0x00000000;
        I2C_SLAVE_REGISTER_READ_MASK    (uint32_t, I2C_SLAVE_REGISTER_DEV_UIDL)             = 0xFFFFFFFF;
        I2C_SLAVE_REGISTER              (uint32_t, I2C_SLAVE_REGISTER_DEV_UIDH)             = DEVINFO->UNIQUEH;
        I2C_SLAVE_REGISTER_WRITE_MASK   (uint32_t, I2C_SLAVE_REGISTER_DEV_UIDH)             = 0x00000000;
        I2C_SLAVE_REGISTER_READ_MASK    (uint32_t, I2C_SLAVE_REGISTER_DEV_UIDH)             = 0xFFFFFFFF;
    }
}
uint8_t i2c_slave_addr_isr(uint8_t ubAddress)
{
    ubI2CByteCount = 0;
    ubI2CChecksum = I2C_SLAVE_ADDRESS;

    // Hardware address comparator already verifies if the address matches
    // This is only called if address is valid
    // All we need to do is ACK

    return 1; // ACK
}
uint8_t i2c_slave_tx_data_isr()
{
    if(!ubI2CChecksumOK)
        return 0xFF;

    if(ubI2CByteCount > ubI2CReadSize + 1)
        return 0xFF;

    ubI2CByteCount++;

    if(ubI2CByteCount == ubI2CReadSize + 1)
    {
        ubI2CChecksumOK = 0;
        ubI2CReadSize = 0;

        return (0xFF - ubI2CChecksum) + 1;
    }

    uint8_t ubData = ubI2CRegister[ubI2CRegisterPointer] & ubI2CRegisterReadMask[ubI2CRegisterPointer];
    ubI2CRegisterPointer++;

    ubI2CChecksum += ubData;

    switch(ubI2CRegisterPointer)
    {
        case I2C_SLAVE_REGISTER_PA1_TEMP_STATUS + sizeof(uint8_t):
        {
            if(ubI2CByteCount < sizeof(uint8_t))
                break;

            I2C_SLAVE_REGISTER(uint8_t, I2C_SLAVE_REGISTER_PA1_TEMP_STATUS) &= ~0xF0; // Clear on read
        }
        break;
        case I2C_SLAVE_REGISTER_PA2_TEMP_STATUS + sizeof(uint8_t):
        {
            if(ubI2CByteCount < sizeof(uint8_t))
                break;

            I2C_SLAVE_REGISTER(uint8_t, I2C_SLAVE_REGISTER_PA2_TEMP_STATUS) &= ~0xF0; // Clear on read
        }
        break;
    }

    return ubData;
}
uint8_t i2c_slave_rx_data_isr(uint8_t ubData)
{
    ubI2CBuffer[ubI2CByteCount++] = ubData;
    ubI2CChecksum += ubData;

    if(ubI2CByteCount < 2)
        return 1; // ACK

    uint8_t ubExpectedLength = 3;

    if(ubI2CBuffer[1] > I2C_SLAVE_REGISTER_COUNT - 3)
        ubExpectedLength++;
    else
        ubExpectedLength += ubI2CBuffer[1];

    if(ubI2CByteCount < ubExpectedLength)
        return 1; // ACK

    ubI2CChecksum -= ubData;
    ubI2CChecksum = (0xFF - ubI2CChecksum) + 1;

    if(ubI2CChecksum != ubI2CBuffer[ubI2CByteCount - 1])
    {
        ubI2CByteCount = 0;
        ubI2CChecksum = I2C_SLAVE_ADDRESS;

        return 0; // NAK
    }

    ubI2CByteCount = 0;
    ubI2CChecksum = I2C_SLAVE_ADDRESS;
    ubI2CRegisterPointer = ubI2CBuffer[0];

    if(ubI2CBuffer[1] > I2C_SLAVE_REGISTER_COUNT - 3)
    {
        ubI2CChecksumOK = 1;
        ubI2CReadSize = ubI2CBuffer[2];

        return 1; // ACK
    }

    for(uint8_t i = 0; i < ubI2CBuffer[1]; i++)
    {
        ubI2CRegister[ubI2CRegisterPointer] = (ubI2CRegister[ubI2CRegisterPointer] & ~ubI2CRegisterWriteMask[ubI2CRegisterPointer]) | (ubI2CBuffer[2 + i] & ubI2CRegisterWriteMask[ubI2CRegisterPointer]);
        ubI2CRegisterPointer++;

        switch(ubI2CRegisterPointer)
        {
            case I2C_SLAVE_REGISTER_PA1_VGG_RAW_VOLTAGE + sizeof(float):
            {
                if(ubI2CBuffer[1] < sizeof(float))
                    break;

                ubPAGateVoltageChanged |= BIT(PA1_INDEX);
            }
            break;
            case I2C_SLAVE_REGISTER_PA2_VGG_RAW_VOLTAGE + sizeof(float):
            {
                if(ubI2CBuffer[1] < sizeof(float))
                    break;

                ubPAGateVoltageChanged |= BIT(PA2_INDEX);
            }
            break;
            case I2C_SLAVE_REGISTER_TEC1_VOLTAGE + sizeof(float):
            {
                if(ubI2CBuffer[1] < sizeof(float))
                    break;

                ubTECVoltageChanged |= BIT(TEC1_INDEX);
            }
            break;
            case I2C_SLAVE_REGISTER_TEC2_VOLTAGE + sizeof(float):
            {
                if(ubI2CBuffer[1] < sizeof(float))
                    break;

                ubTECVoltageChanged |= BIT(TEC2_INDEX);
            }
            break;
            case I2C_SLAVE_REGISTER_TEC3_VOLTAGE + sizeof(float):
            {
                if(ubI2CBuffer[1] < sizeof(float))
                    break;

                ubTECVoltageChanged |= BIT(TEC3_INDEX);
            }
            break;
            case I2C_SLAVE_REGISTER_TEC4_VOLTAGE + sizeof(float):
            {
                if(ubI2CBuffer[1] < sizeof(float))
                    break;

                ubTECVoltageChanged |= BIT(TEC4_INDEX);
            }
            break;
        }
    }

    return 1; // ACK
}

void afe_init()
{
    // Config
    max11300_config(MAX11300_REG_DEVICE_CTRL_RS_CANCEL | MAX11300_REG_DEVICE_CTRL_TMPPER_EXTENDED | MAX11300_REG_DEVICE_CTRL_THSHDN | MAX11300_REG_DEVICE_CTRL_DACREF_INTERNAL | MAX11300_REG_DEVICE_CTRL_ADCCONV_200KSPS | MAX11300_REG_DEVICE_CTRL_DACCTL_IMMEDIATE | MAX11300_REG_DEVICE_CTRL_ADCCTL_CONTINUOUS);

    // Temperatures
    max11300_int_temp_config(1, MAX11300_REG_TEMP_MON_CONFIG_TMPINTMONCFG_32_SAMPLES, 0, 80);
    max11300_ext1_temp_config(1, MAX11300_REG_TEMP_MON_CONFIG_TMPINTMONCFG_32_SAMPLES, 0, 60);
    max11300_ext2_temp_config(1, MAX11300_REG_TEMP_MON_CONFIG_TMPINTMONCFG_32_SAMPLES, 0, 60);

    // Ports
    //// PORT0 - PA1_VG_EN
    max11300_port_config(0, MAX11300_REG_PORTn_CONFIG_FUNCID_DIG_IN_PROG_LEVEL);
    max11300_port_dac_set_data(0, 2000.f / MAX11300_DAC_INTERNAL_REF * 4096); // 2 V logic threshold
    //// PORT1 - PA2_VG_EN
    max11300_port_config(1, MAX11300_REG_PORTn_CONFIG_FUNCID_DIG_IN_PROG_LEVEL);
    max11300_port_dac_set_data(1, 2000.f / MAX11300_DAC_INTERNAL_REF * 4096); // 2 V logic threshold
    //// PORT4 - PA1_VG_RAW
    max11300_port_config(4, MAX11300_REG_PORTn_CONFIG_FUNCID_ANA_OUT_MON | MAX11300_REG_PORTn_CONFIG_FUNCPRM_AVR_EXTERNAL | MAX11300_REG_PORTn_CONFIG_FUNCPRM_RANGE_ADC_0_P2p5_DAC_0_P10 | MAX11300_REG_PORTn_CONFIG_FUNCPRM_NSAMPLES_128);
    max11300_port_dac_set_data(4, 0.f / 10000.f * 4096);
    //// PORT5 - PA1_VG_FLT
    max11300_port_config(5, MAX11300_REG_PORTn_CONFIG_FUNCID_GPI_CONTROLLED_SWITCH | 0);
    //// PORT6 - PA1_VG_SW
    max11300_port_config(6, MAX11300_REG_PORTn_CONFIG_FUNCID_SINGLE_ANA_IN_POS | MAX11300_REG_PORTn_CONFIG_FUNCPRM_AVR_EXTERNAL | MAX11300_REG_PORTn_CONFIG_FUNCPRM_RANGE_ADC_0_P2p5_DAC_0_P10 | MAX11300_REG_PORTn_CONFIG_FUNCPRM_NSAMPLES_128);
    //// PORT8 - PA2_VG_RAW
    max11300_port_config(8, MAX11300_REG_PORTn_CONFIG_FUNCID_ANA_OUT_MON | MAX11300_REG_PORTn_CONFIG_FUNCPRM_AVR_EXTERNAL | MAX11300_REG_PORTn_CONFIG_FUNCPRM_RANGE_ADC_0_P2p5_DAC_0_P10 | MAX11300_REG_PORTn_CONFIG_FUNCPRM_NSAMPLES_128);
    max11300_port_dac_set_data(8, 0.f / 10000.f * 4096);
    //// PORT9 - PA2_VG_FLT
    max11300_port_config(9, MAX11300_REG_PORTn_CONFIG_FUNCID_GPI_CONTROLLED_SWITCH | 1);
    //// PORT10 - PA2_VG_SW
    max11300_port_config(10, MAX11300_REG_PORTn_CONFIG_FUNCID_SINGLE_ANA_IN_POS | MAX11300_REG_PORTn_CONFIG_FUNCPRM_AVR_EXTERNAL | MAX11300_REG_PORTn_CONFIG_FUNCPRM_RANGE_ADC_0_P2p5_DAC_0_P10 | MAX11300_REG_PORTn_CONFIG_FUNCPRM_NSAMPLES_128);
    //// PORT14 - VPA1_VD_SENSE
    max11300_port_config(14, MAX11300_REG_PORTn_CONFIG_FUNCID_SINGLE_ANA_IN_POS | MAX11300_REG_PORTn_CONFIG_FUNCPRM_AVR_EXTERNAL | MAX11300_REG_PORTn_CONFIG_FUNCPRM_RANGE_ADC_0_P2p5_DAC_0_P10 | MAX11300_REG_PORTn_CONFIG_FUNCPRM_NSAMPLES_128);
    //// PORT15 - VPA2_VD_SENSE
    max11300_port_config(15, MAX11300_REG_PORTn_CONFIG_FUNCID_SINGLE_ANA_IN_POS | MAX11300_REG_PORTn_CONFIG_FUNCPRM_AVR_EXTERNAL | MAX11300_REG_PORTn_CONFIG_FUNCPRM_RANGE_ADC_0_P2p5_DAC_0_P10 | MAX11300_REG_PORTn_CONFIG_FUNCPRM_NSAMPLES_128);
    //// PORT18 - VPA1_ID_SENSE
    max11300_port_config(18, MAX11300_REG_PORTn_CONFIG_FUNCID_SINGLE_ANA_IN_POS | MAX11300_REG_PORTn_CONFIG_FUNCPRM_AVR_EXTERNAL | MAX11300_REG_PORTn_CONFIG_FUNCPRM_RANGE_ADC_0_P2p5_DAC_0_P10 | MAX11300_REG_PORTn_CONFIG_FUNCPRM_NSAMPLES_128);
    //// PORT19 - VPA2_ID_SENSE
    max11300_port_config(19, MAX11300_REG_PORTn_CONFIG_FUNCID_SINGLE_ANA_IN_POS | MAX11300_REG_PORTn_CONFIG_FUNCPRM_AVR_EXTERNAL | MAX11300_REG_PORTn_CONFIG_FUNCPRM_RANGE_ADC_0_P2p5_DAC_0_P10 | MAX11300_REG_PORTn_CONFIG_FUNCPRM_NSAMPLES_128);
}
void afe_pa_set_raw_vgg(uint8_t ubPAIndex, float fVoltage)
{
    if(fVoltage < 0.f)
        return;
    if(fVoltage > 2800.f)
        return;

    switch(ubPAIndex)
    {
        case PA1_INDEX:
            max11300_port_dac_set_data(4, fVoltage / 10000.f * 4096);
        break;
        case PA2_INDEX:
            max11300_port_dac_set_data(8, fVoltage / 10000.f * 4096);
        break;
    }
}
float afe_pa_get_raw_vgg(uint8_t ubPAIndex)
{
    switch(ubPAIndex)
    {
        case PA1_INDEX:
            return max11300_port_adc_get_data(4) * (MAX11300_ADC_EXTERNAL_REF / 4096.f);
        break;
        case PA2_INDEX:
            return max11300_port_adc_get_data(8) * (MAX11300_ADC_EXTERNAL_REF / 4096.f);
        break;
    }

    return 0.f;
}
float afe_pa_get_vgg(uint8_t ubPAIndex)
{
    switch(ubPAIndex)
    {
        case PA1_INDEX:
            return max11300_port_adc_get_data(6) * (MAX11300_ADC_EXTERNAL_REF / 4096.f);
        break;
        case PA2_INDEX:
            return max11300_port_adc_get_data(10) * (MAX11300_ADC_EXTERNAL_REF / 4096.f);
        break;
    }

    return 0.f;
}
float afe_pa_get_vdd(uint8_t ubPAIndex)
{
    switch(ubPAIndex)
    {
        case PA1_INDEX:
            return (max11300_port_adc_get_data(14) * (MAX11300_ADC_EXTERNAL_REF / 4096.f) * 16 - 175.78125f) * 1.013f;
        break;
        case PA2_INDEX:
            return (max11300_port_adc_get_data(15) * (MAX11300_ADC_EXTERNAL_REF / 4096.f) * 16 - 175.78125f) * 1.013f;
        break;
    }

    return 0.f;
}
float afe_pa_get_idd(uint8_t ubPAIndex)
{
    switch(ubPAIndex)
    {
        case PA1_INDEX:
            return (max11300_port_adc_get_data(18) * (MAX11300_ADC_EXTERNAL_REF / 4096.f) / 20 / 0.1f - 4.577f) * 1.102f;
        break;
        case PA2_INDEX:
            return (max11300_port_adc_get_data(19) * (MAX11300_ADC_EXTERNAL_REF / 4096.f) / 20 / (0.012f / 3) - 99.182f) * 1.135f;
        break;
    }

    return 0.f;
}
float afe_pa_get_temperature(uint8_t ubPAIndex)
{
    // Very dirty workaround for transients in temperature sensor readings
    // Computes the average discarding obvious outliers and applies a moving median filter
    enum
    {
        AVG_SAMPLES = 20,
        MOV_MED_SAMPLES = 21, // Should be odd to facilitate median calculation
    };

    uint32_t ulSkipped = 0;
    uint32_t ulValid = 0;
    float fSum = 0.f;

    for(uint32_t i = 0; i < AVG_SAMPLES; i++)
    {
        float fSample;

        switch(ubPAIndex)
        {
            case PA1_INDEX:
                fSample = max11300_ext1_temp_read(1);
            break;
            case PA2_INDEX:
                fSample = max11300_ext2_temp_read(1);
            break;
        }

        if(i == 0)
        {
            if(fSample > 0.f && fSample < 120.f)
            {
                ulValid++;
                fSum = fSample;
            }
            else
            {
                ulSkipped++;
                i--;
            }
        }
        else
        {
            if(fabsf(fSample - fSum) <= 2.f)
            {
                fSum += fSample;
                ulValid++;
            }
            else
            {
                if(ulSkipped < AVG_SAMPLES)
                    i--;

                ulSkipped++;
            }
        }
    }

    fSum /= ulValid; // Average

    static float fMovMedian[MOV_MED_SAMPLES];
    static uint8_t ubMovMedianInit = 0;

    if(!ubMovMedianInit)
    {
        // Init the moving median filter
        ubMovMedianInit = 1;

        for(uint32_t i = 0; i < MOV_MED_SAMPLES; i++)
            fMovMedian[i] = fSum;
    }
    else
    {
        uint32_t ulInsertIndex = 0;

        // Get the index where to insert the new sample so the list remains sorted
        for(uint32_t i = 0; i < MOV_MED_SAMPLES; i++)
            if(fSum > fMovMedian[i])
                ulInsertIndex = i;

        fMovMedian[ulInsertIndex] = fSum;
    }

    // Median is the center element
    return fMovMedian[MOV_MED_SAMPLES / 2];
}

void tec_init()
{
    TEC1_DISABLE();
    TEC2_DISABLE();
    TEC3_DISABLE();
    TEC4_DISABLE();

    mcp4728_channel_write(0, MCP4728_CHAN_VREF_INTERNAL | MCP4728_CHAN_PD_NORMAL | MCP4728_CHAN_GAIN_X1 | 0x0FFF);
    mcp4728_channel_write(1, MCP4728_CHAN_VREF_INTERNAL | MCP4728_CHAN_PD_NORMAL | MCP4728_CHAN_GAIN_X1 | 0x0FFF);
    mcp4728_channel_write(2, MCP4728_CHAN_VREF_INTERNAL | MCP4728_CHAN_PD_NORMAL | MCP4728_CHAN_GAIN_X1 | 0x0FFF);
    mcp4728_channel_write(3, MCP4728_CHAN_VREF_INTERNAL | MCP4728_CHAN_PD_NORMAL | MCP4728_CHAN_GAIN_X1 | 0x0FFF);
}
void tec_set_channel_voltage(uint8_t ubChannel, float fVoltage)
{
    if(ubChannel > 3)
        return;

    float fDACVoltage = -0.1f * fVoltage + 2525.646f;

    if(fDACVoltage < 0.f || fDACVoltage >= MCP4728_INTERNAL_REF)
        return;

    uint16_t usCode = fDACVoltage / MCP4728_INTERNAL_REF * 4096.f;

    if(usCode > 4095)
        usCode = 4095;

    mcp4728_channel_write(ubChannel, MCP4728_CHAN_VREF_INTERNAL | MCP4728_CHAN_PD_NORMAL | MCP4728_CHAN_GAIN_X1 | (usCode & 0x0FFF));
}
float tec_get_channel_voltage(uint8_t ubChannel)
{
    if(ubChannel > 3)
        return 0.f;

    uint16_t usCode = mcp4728_channel_read(ubChannel);
    float fDACVoltage = 0.f;

    if(usCode & MCP4728_CHAN_VREF_INTERNAL)
        fDACVoltage = (usCode & 0x0FFF) * (MCP4728_INTERNAL_REF / 4096.f);
    else
        fDACVoltage = (usCode & 0x0FFF) * (MCP4728_EXTERNAL_REF / 4096.f);

    if(usCode & MCP4728_CHAN_GAIN_X2)
        fDACVoltage *= 2.f;

    float fVoltage = -10.f * fDACVoltage + 25256.46f;

    return fVoltage;
}

int init()
{
    rmu_init(RMU_CTRL_PINRMODE_FULL, RMU_CTRL_SYSRMODE_EXTENDED, RMU_CTRL_LOCKUPRMODE_EXTENDED, RMU_CTRL_WDOGRMODE_EXTENDED); // Init RMU and set reset modes

    emu_init(1); // Init EMU, ignore DCDC and switch digital power immediatly to DVDD

    cmu_init(); // Init Clocks

    msc_init(); // Init Flash, RAM and caches

    systick_init(); // Init system tick

    wdog_init((8 <<_WDOG_CTRL_PERSEL_SHIFT) | (3 << _WDOG_CTRL_WARNSEL_SHIFT)); // Init the watchdog timer, 2049 ms timeout, 75% warning
    wdog_set_warning_isr(wdog_warning_isr);

    gpio_init(); // Init GPIOs
    ldma_init(); // Init LDMA
    rtcc_init(); // Init RTCC
    crc_init(); // Init CRC calculation unit
    adc_init(); // Init ADCs

    float fAVDDHighThresh, fAVDDLowThresh;
    float fDVDDHighThresh, fDVDDLowThresh;
    float fIOVDDHighThresh, fIOVDDLowThresh;

    emu_vmon_avdd_config(1, 3.1f, &fAVDDLowThresh, 3.22f, &fAVDDHighThresh); // Enable AVDD monitor
    emu_vmon_dvdd_config(1, 3.1f, &fDVDDLowThresh); // Enable DVDD monitor
    emu_vmon_iovdd_config(1, 3.15f, &fIOVDDLowThresh); // Enable IOVDD monitor

    fDVDDHighThresh = fDVDDLowThresh + 0.026f; // Hysteresis from datasheet
    fIOVDDHighThresh = fIOVDDLowThresh + 0.026f; // Hysteresis from datasheet

    usart0_init(12000000, 0, USART_SPI_MSB_FIRST, 0, 0, 0);
    usart1_init(1000000, USART_FRAME_STOPBITS_ONE | USART_FRAME_PARITY_NONE | USART_FRAME_DATABITS_EIGHT, -1, 5, -1, -1);

    i2c0_init(I2C_SLAVE_ADDRESS, 0, 0);
    i2c0_set_slave_addr_isr(i2c_slave_addr_isr);
    i2c0_set_slave_tx_data_isr(i2c_slave_tx_data_isr);
    i2c0_set_slave_rx_data_isr(i2c_slave_rx_data_isr);
    i2c1_init(I2C_FAST, 3, 3);

    char szDeviceCoreName[32];
    char szDeviceName[32];

    get_device_core_name(szDeviceCoreName, 32);
    get_device_name(szDeviceName, 32);

    printf("\x1B[2J"); // Clear the screen
    printf("\x1B[H"); // Move cursor to top left corner

    DBGPRINTLN_CTX("IcyRadio PA Bias Controller v%lu (%s %s)!", BUILD_VERSION, __DATE__, __TIME__);
    DBGPRINTLN_CTX("Core: %s", szDeviceCoreName);
    DBGPRINTLN_CTX("Device: %s", szDeviceName);
    DBGPRINTLN_CTX("Device Revision: 0x%04X", get_device_revision());
    DBGPRINTLN_CTX("Calibration temperature: %hhu C", (DEVINFO->CAL & _DEVINFO_CAL_TEMP_MASK) >> _DEVINFO_CAL_TEMP_SHIFT);
    DBGPRINTLN_CTX("Flash Size: %hu kB", FLASH_SIZE >> 10);
    DBGPRINTLN_CTX("RAM Size: %hu kB", SRAM_SIZE >> 10);
    DBGPRINTLN_CTX("Free RAM: %lu B", get_free_ram());
    DBGPRINTLN_CTX("Unique ID: %08X-%08X", DEVINFO->UNIQUEH, DEVINFO->UNIQUEL);

    DBGPRINTLN_CTX("RMU - Reset cause: %hhu", rmu_get_reset_reason());
    DBGPRINTLN_CTX("RMU - Reset state: %hhu", rmu_get_reset_state());

    I2C_SLAVE_REGISTER(uint8_t, I2C_SLAVE_REGISTER_RESET_DATA) = ((rmu_get_reset_state() << 6) & 0xC0) | (rmu_get_reset_reason() & 0x3F);

    rmu_clear_reset_reason();

    DBGPRINTLN_CTX("EMU - AVDD Fall Threshold: %.2f mV!", fAVDDLowThresh * 1000);
    DBGPRINTLN_CTX("EMU - AVDD Rise Threshold: %.2f mV!", fAVDDHighThresh * 1000);
    DBGPRINTLN_CTX("EMU - AVDD Voltage: %.2f mV", adc_get_avdd());
    DBGPRINTLN_CTX("EMU - AVDD Status: %s", g_ubAVDDLow ? "LOW" : "OK");
    DBGPRINTLN_CTX("EMU - DVDD Fall Threshold: %.2f mV!", fDVDDLowThresh * 1000);
    DBGPRINTLN_CTX("EMU - DVDD Rise Threshold: %.2f mV!", fDVDDHighThresh * 1000);
    DBGPRINTLN_CTX("EMU - DVDD Voltage: %.2f mV", adc_get_dvdd());
    DBGPRINTLN_CTX("EMU - DVDD Status: %s", g_ubDVDDLow ? "LOW" : "OK");
    DBGPRINTLN_CTX("EMU - IOVDD Fall Threshold: %.2f mV!", fIOVDDLowThresh * 1000);
    DBGPRINTLN_CTX("EMU - IOVDD Rise Threshold: %.2f mV!", fIOVDDHighThresh * 1000);
    DBGPRINTLN_CTX("EMU - IOVDD Voltage: %.2f mV", adc_get_iovdd());
    DBGPRINTLN_CTX("EMU - IOVDD Status: %s", g_ubIOVDDLow ? "LOW" : "OK");
    DBGPRINTLN_CTX("EMU - Core Voltage: %.2f mV", adc_get_corevdd());
    DBGPRINTLN_CTX("EMU - VIN Voltage: %.2f mV", adc_get_vin());
    DBGPRINTLN_CTX("EMU - 5V0 Voltage: %.2f mV", adc_get_5v0());

    DBGPRINTLN_CTX("CMU - HFXO Oscillator: %.3f MHz", (float)HFXO_OSC_FREQ / 1000000);
    DBGPRINTLN_CTX("CMU - HFRCO Oscillator: %.3f MHz", (float)HFRCO_OSC_FREQ / 1000000);
    DBGPRINTLN_CTX("CMU - AUXHFRCO Oscillator: %.3f MHz", (float)AUXHFRCO_OSC_FREQ / 1000000);
    DBGPRINTLN_CTX("CMU - LFXO Oscillator: %.3f kHz", (float)LFXO_OSC_FREQ / 1000);
    DBGPRINTLN_CTX("CMU - LFRCO Oscillator: %.3f kHz", (float)LFRCO_OSC_FREQ / 1000);
    DBGPRINTLN_CTX("CMU - ULFRCO Oscillator: %.3f kHz", (float)ULFRCO_OSC_FREQ / 1000);
    DBGPRINTLN_CTX("CMU - HFSRC Clock: %.3f MHz", (float)HFSRC_CLOCK_FREQ / 1000000);
    DBGPRINTLN_CTX("CMU - HF Clock: %.3f MHz", (float)HF_CLOCK_FREQ / 1000000);
    DBGPRINTLN_CTX("CMU - HFBUS Clock: %.3f MHz", (float)HFBUS_CLOCK_FREQ / 1000000);
    DBGPRINTLN_CTX("CMU - HFCORE Clock: %.3f MHz", (float)HFCORE_CLOCK_FREQ / 1000000);
    DBGPRINTLN_CTX("CMU - HFEXP Clock: %.3f MHz", (float)HFEXP_CLOCK_FREQ / 1000000);
    DBGPRINTLN_CTX("CMU - HFPER Clock: %.3f MHz", (float)HFPER_CLOCK_FREQ / 1000000);
    DBGPRINTLN_CTX("CMU - HFPERB Clock: %.3f MHz", (float)HFPERB_CLOCK_FREQ / 1000000);
    DBGPRINTLN_CTX("CMU - HFPERC Clock: %.3f MHz", (float)HFPERC_CLOCK_FREQ / 1000000);
    DBGPRINTLN_CTX("CMU - HFLE Clock: %.3f MHz", (float)HFLE_CLOCK_FREQ / 1000000);
    DBGPRINTLN_CTX("CMU - ADC0 Clock: %.3f MHz", (float)ADC0_CLOCK_FREQ / 1000000);
    DBGPRINTLN_CTX("CMU - DBG Clock: %.3f MHz", (float)DBG_CLOCK_FREQ / 1000000);
    DBGPRINTLN_CTX("CMU - AUX Clock: %.3f MHz", (float)AUX_CLOCK_FREQ / 1000000);
    DBGPRINTLN_CTX("CMU - LFA Clock: %.3f kHz", (float)LFA_CLOCK_FREQ / 1000);
    DBGPRINTLN_CTX("CMU - LESENSE Clock: %.3f kHz", (float)LESENSE_CLOCK_FREQ / 1000);
    DBGPRINTLN_CTX("CMU - LETIMER0 Clock: %.3f kHz", (float)LETIMER0_CLOCK_FREQ / 1000);
    DBGPRINTLN_CTX("CMU - LFB Clock: %.3f kHz", (float)LFB_CLOCK_FREQ / 1000);
    DBGPRINTLN_CTX("CMU - LEUART0 Clock: %.3f kHz", (float)LEUART0_CLOCK_FREQ / 1000);
    DBGPRINTLN_CTX("CMU - SYSTICK Clock: %.3f kHz", (float)SYSTICK_CLOCK_FREQ / 1000);
    DBGPRINTLN_CTX("CMU - CSEN Clock: %.3f kHz", (float)CSEN_CLOCK_FREQ / 1000);
    DBGPRINTLN_CTX("CMU - LFE Clock: %.3f kHz", (float)LFE_CLOCK_FREQ / 1000);
    DBGPRINTLN_CTX("CMU - RTCC Clock: %.3f kHz", (float)RTCC_CLOCK_FREQ / 1000);

    DBGPRINTLN_CTX("WDOG - Timeout period: %.3f ms", wdog_get_timeout_period());
    DBGPRINTLN_CTX("WDOG - Warning period: %.3f ms", wdog_get_warning_period());

    DBGPRINTLN_CTX("Scanning I2C bus 1...");

    for(uint8_t a = 0x08; a < 0x78; a++)
        if(i2c1_write(a, NULL, 0, I2C_STOP))
            DBGPRINTLN_CTX("  Address 0x%02X ACKed!", a);

    if(max11300_init())
        DBGPRINTLN_CTX("MAX11300 init OK!");
    else
        DBGPRINTLN_CTX("MAX11300 init NOK!");

    if(mcp4728_init())
    {
        ubTECDACInitialized = 1;
        DBGPRINTLN_CTX("MCP4728 init OK!");
    }
    else
    {
        DBGPRINTLN_CTX("MCP4728 init NOK!");
    }

    return 0;
}
int main()
{
    // I2C Slave Register block
    i2c_slave_register_init();

    // Analog frontent
    afe_init();

    // TEC
    tec_init();

    //afe_pa_set_raw_vgg(PA1_INDEX, 2280.f);
    //PA1_ENABLE();
    //afe_pa_set_raw_vgg(PA2_INDEX, 2250.f);
    //PA2_ENABLE();

    //tec_set_channel_voltage(TEC1_INDEX, 24000.f);
    //TEC1_ENABLE();
    //tec_set_channel_voltage(TEC2_INDEX, 24000.f);
    //TEC2_ENABLE();
    //tec_set_channel_voltage(TEC3_INDEX, 24000.f);
    //TEC3_ENABLE();
    //tec_set_channel_voltage(TEC4_INDEX, 24000.f);
    //TEC4_ENABLE();

    while(1)
    {
        wdog_feed();

        if(I2C_SLAVE_REGISTER(uint8_t, I2C_SLAVE_REGISTER_CONFIG) & BIT(7))
        {
            delay_ms(20);

            reset();
        }

        if(I2C_SLAVE_REGISTER(uint64_t, I2C_SLAVE_REGISTER_UPTIME) != g_ullSystemTick / 1000)
        {
            ATOMIC_BLOCK(ATOMIC_RESTORESTATE)
            {
                I2C_SLAVE_REGISTER(uint64_t, I2C_SLAVE_REGISTER_UPTIME) = g_ullSystemTick / 1000;
            }
        }

        volatile uint8_t ubStatus = 0x00;
        volatile uint8_t ubConfig = 0x00;

        ATOMIC_BLOCK(ATOMIC_RESTORESTATE)
            ubConfig = I2C_SLAVE_REGISTER(uint8_t, I2C_SLAVE_REGISTER_CONFIG);

        if(ubConfig & BIT(0))
            PA1_ENABLE();
        else
            PA1_DISABLE();
        if(ubConfig & BIT(1))
            PA2_ENABLE();
        else
            PA2_DISABLE();

        // Prevent TEC enable signals when voltage config DAC is not initialized
        if(ubTECDACInitialized)
        {
            if(ubConfig & BIT(3))
                TEC1_ENABLE();
            else
                TEC1_DISABLE();
            if(ubConfig & BIT(4))
                TEC2_ENABLE();
            else
                TEC2_DISABLE();
            if(ubConfig & BIT(5))
                TEC3_ENABLE();
            else
                TEC3_DISABLE();
            if(ubConfig & BIT(6))
                TEC4_ENABLE();
            else
                TEC4_DISABLE();
        }
        else
        {
            TEC1_DISABLE();
            TEC2_DISABLE();
            TEC3_DISABLE();
            TEC4_DISABLE();
        }

        if(PA1_STATUS())
            ubStatus |= BIT(0);
        if(PA2_STATUS())
            ubStatus |= BIT(1);
        if(ubTECDACInitialized)
            ubStatus |= BIT(2);
        if(TEC1_STATUS())
            ubStatus |= BIT(3);
        if(TEC2_STATUS())
            ubStatus |= BIT(4);
        if(TEC3_STATUS())
            ubStatus |= BIT(5);
        if(TEC4_STATUS())
            ubStatus |= BIT(6);

        ATOMIC_BLOCK(ATOMIC_RESTORESTATE)
            I2C_SLAVE_REGISTER(uint8_t, I2C_SLAVE_REGISTER_STATUS) = ubStatus;

        if(ubPAGateVoltageChanged)
        {
            for(uint8_t i = 0; i < 2; i++)
            {
                ATOMIC_BLOCK(ATOMIC_RESTORESTATE)
                {
                    if(!(ubPAGateVoltageChanged & BIT(i)))
                        continue;

                    afe_pa_set_raw_vgg(i, I2C_SLAVE_REGISTER(float, I2C_SLAVE_REGISTER_PA1_VGG_RAW_VOLTAGE + i * 0x20));
                    I2C_SLAVE_REGISTER(float, I2C_SLAVE_REGISTER_PA1_VGG_RAW_VOLTAGE + i * 0x20) = afe_pa_get_raw_vgg(i);
                    I2C_SLAVE_REGISTER(float, I2C_SLAVE_REGISTER_PA1_VGG_VOLTAGE + i * 0x20) = afe_pa_get_vgg(i);

                    ubPAGateVoltageChanged &= ~BIT(i);
                }
            }
        }

        if(ubTECVoltageChanged)
        {
            for(uint8_t i = 0; i < 4; i++)
            {
                ATOMIC_BLOCK(ATOMIC_RESTORESTATE)
                {
                    if(!(ubTECVoltageChanged & BIT(i)))
                        continue;

                    tec_set_channel_voltage(i, I2C_SLAVE_REGISTER(float, I2C_SLAVE_REGISTER_TEC1_VOLTAGE + i * sizeof(float)));
                    I2C_SLAVE_REGISTER(float, I2C_SLAVE_REGISTER_TEC1_VOLTAGE + i * sizeof(float)) = tec_get_channel_voltage(i);

                    ubTECVoltageChanged &= ~BIT(i);
                }
            }
        }

        static uint64_t ullLastHeartBeat = 0;
        static uint64_t ullLastTelemetryUpdate = 0;
        static uint64_t ullLastTemperatureCheck = 0;

        if((g_ullSystemTick > 0 && ullLastHeartBeat == 0) || g_ullSystemTick - ullLastHeartBeat > 2000)
        {
            ullLastHeartBeat = g_ullSystemTick;

            LED_TOGGLE();

            if(LED_STATUS())
                ullLastHeartBeat -= 1900;
        }

        if((g_ullSystemTick > 0 && ullLastTelemetryUpdate == 0) || g_ullSystemTick - ullLastTelemetryUpdate > 5000)
        {
            ullLastTelemetryUpdate = g_ullSystemTick;

            // System Temperatures
            float fADCTemp = adc_get_temperature();
            float fEMUTemp = emu_get_temperature();
            float fAFETemp = max11300_int_temp_read(0);

            ATOMIC_BLOCK(ATOMIC_RESTORESTATE)
            {
                I2C_SLAVE_REGISTER(float, I2C_SLAVE_REGISTER_ADC_TEMP) = fADCTemp;
                I2C_SLAVE_REGISTER(float, I2C_SLAVE_REGISTER_EMU_TEMP) = fEMUTemp;
                I2C_SLAVE_REGISTER(float, I2C_SLAVE_REGISTER_AFE_TEMP) = fAFETemp;
            }

            DBGPRINTLN_CTX("----------------------------------");
            DBGPRINTLN_CTX("ADC Temperature: %.2f C", fADCTemp);
            DBGPRINTLN_CTX("EMU Temperature: %.2f C", fEMUTemp);
            DBGPRINTLN_CTX("AFE Temperature: %.2f C", fAFETemp);

            // System Voltages/Currents
            float fVIN = adc_get_vin();
            float f5V0 = adc_get_5v0();
            float fAVDD = adc_get_avdd();
            float fDVDD = adc_get_dvdd();
            float fIOVDD = adc_get_iovdd();
            float fCoreVDD = adc_get_corevdd();

            ATOMIC_BLOCK(ATOMIC_RESTORESTATE)
            {
                I2C_SLAVE_REGISTER(float, I2C_SLAVE_REGISTER_VIN_VOLTAGE) = fVIN;
                I2C_SLAVE_REGISTER(float, I2C_SLAVE_REGISTER_5V0_VOLTAGE) = f5V0;
                I2C_SLAVE_REGISTER(float, I2C_SLAVE_REGISTER_AVDD_VOLTAGE) = fAVDD;
                I2C_SLAVE_REGISTER(float, I2C_SLAVE_REGISTER_DVDD_VOLTAGE) = fDVDD;
                I2C_SLAVE_REGISTER(float, I2C_SLAVE_REGISTER_IOVDD_VOLTAGE) = fIOVDD;
                I2C_SLAVE_REGISTER(float, I2C_SLAVE_REGISTER_CORE_VOLTAGE) = fCoreVDD;
            }

            DBGPRINTLN_CTX("----------------------------------");
            DBGPRINTLN_CTX("AVDD Voltage: %.2f mV", fAVDD);
            DBGPRINTLN_CTX("DVDD Voltage: %.2f mV", fDVDD);
            DBGPRINTLN_CTX("IOVDD Voltage: %.2f mV", fIOVDD);
            DBGPRINTLN_CTX("Core Voltage: %.2f mV", fCoreVDD);
            DBGPRINTLN_CTX("VIN Voltage: %.2f mV", fVIN);
            DBGPRINTLN_CTX("5V0 Voltage: %.2f mV", f5V0);

            // PA1
            float fPA1VGGRaw = afe_pa_get_raw_vgg(PA1_INDEX);
            float fPA1VGG = afe_pa_get_vgg(PA1_INDEX);
            float fPA1VDD = afe_pa_get_vdd(PA1_INDEX);
            float fPA1IDD = afe_pa_get_idd(PA1_INDEX);
            float fPA1Temp = afe_pa_get_temperature(PA1_INDEX);

            ATOMIC_BLOCK(ATOMIC_RESTORESTATE)
            {
                I2C_SLAVE_REGISTER(float, I2C_SLAVE_REGISTER_PA1_VGG_RAW_VOLTAGE) = fPA1VGGRaw;
                I2C_SLAVE_REGISTER(float, I2C_SLAVE_REGISTER_PA1_VGG_VOLTAGE) = fPA1VGG;
                I2C_SLAVE_REGISTER(float, I2C_SLAVE_REGISTER_PA1_VDD_VOLTAGE) = fPA1VDD;
                I2C_SLAVE_REGISTER(float, I2C_SLAVE_REGISTER_PA1_IDD_CURRENT) = fPA1IDD;
                I2C_SLAVE_REGISTER(float, I2C_SLAVE_REGISTER_PA1_TEMP) = fPA1Temp;
            }

            DBGPRINTLN_CTX("----------------------------------");
            DBGPRINTLN_CTX("PA #1 Temperature: %.2f C", fPA1Temp);
            DBGPRINTLN_CTX("PA #1 High Temperature: %.2f C", I2C_SLAVE_REGISTER(float, I2C_SLAVE_REGISTER_PA1_TEMP_HIGH));
            DBGPRINTLN_CTX("PA #1 Low Temperature: %.2f C", I2C_SLAVE_REGISTER(float, I2C_SLAVE_REGISTER_PA1_TEMP_LOW));
            DBGPRINTLN_CTX("PA #1 Temperature Status: %s", (I2C_SLAVE_REGISTER(uint8_t, I2C_SLAVE_REGISTER_PA1_TEMP_STATUS) & BIT(0)) ? "LOW" : ((I2C_SLAVE_REGISTER(uint8_t, I2C_SLAVE_REGISTER_PA1_TEMP_STATUS) & BIT(1)) ? "HIGH" : "OK"));
            DBGPRINTLN_CTX("PA #1 Drain Voltage: %.2f mV", fPA1VDD);
            DBGPRINTLN_CTX("PA #1 Drain Current: %.2f mA", fPA1IDD);
            DBGPRINTLN_CTX("PA #1 Gate Raw Voltage: %.2f mV", fPA1VGGRaw);
            DBGPRINTLN_CTX("PA #1 Gate Voltage: %.2f mV", fPA1VGG);

            // PA2
            float fPA2VGGRaw = afe_pa_get_raw_vgg(PA2_INDEX);
            float fPA2VGG = afe_pa_get_vgg(PA2_INDEX);
            float fPA2VDD = afe_pa_get_vdd(PA2_INDEX);
            float fPA2IDD = afe_pa_get_idd(PA2_INDEX);
            float fPA2Temp = afe_pa_get_temperature(PA2_INDEX);

            ATOMIC_BLOCK(ATOMIC_RESTORESTATE)
            {
                I2C_SLAVE_REGISTER(float, I2C_SLAVE_REGISTER_PA2_VGG_RAW_VOLTAGE) = fPA2VGGRaw;
                I2C_SLAVE_REGISTER(float, I2C_SLAVE_REGISTER_PA2_VGG_VOLTAGE) = fPA2VGG;
                I2C_SLAVE_REGISTER(float, I2C_SLAVE_REGISTER_PA2_VDD_VOLTAGE) = fPA2VDD;
                I2C_SLAVE_REGISTER(float, I2C_SLAVE_REGISTER_PA2_IDD_CURRENT) = fPA2IDD;
                I2C_SLAVE_REGISTER(float, I2C_SLAVE_REGISTER_PA2_TEMP) = fPA2Temp;
            }

            DBGPRINTLN_CTX("----------------------------------");
            DBGPRINTLN_CTX("PA #2 Temperature: %.2f C", fPA2Temp);
            DBGPRINTLN_CTX("PA #2 High Temperature: %.2f C", I2C_SLAVE_REGISTER(float, I2C_SLAVE_REGISTER_PA2_TEMP_HIGH));
            DBGPRINTLN_CTX("PA #2 Low Temperature: %.2f C", I2C_SLAVE_REGISTER(float, I2C_SLAVE_REGISTER_PA2_TEMP_LOW));
            DBGPRINTLN_CTX("PA #2 Temperature Status: %s", (I2C_SLAVE_REGISTER(uint8_t, I2C_SLAVE_REGISTER_PA2_TEMP_STATUS) & BIT(0)) ? "LOW" : ((I2C_SLAVE_REGISTER(uint8_t, I2C_SLAVE_REGISTER_PA2_TEMP_STATUS) & BIT(1)) ? "HIGH" : "OK"));
            DBGPRINTLN_CTX("PA #2 Drain Voltage: %.2f mV", fPA2VDD);
            DBGPRINTLN_CTX("PA #2 Drain Current: %.2f mA", fPA2IDD);
            DBGPRINTLN_CTX("PA #2 Gate Raw Voltage: %.2f mV", fPA2VGGRaw);
            DBGPRINTLN_CTX("PA #2 Gate Voltage: %.2f mV", fPA2VGG);

            // TECs
            float fTEC1Voltage = tec_get_channel_voltage(TEC1_INDEX);
            float fTEC2Voltage = tec_get_channel_voltage(TEC2_INDEX);
            float fTEC3Voltage = tec_get_channel_voltage(TEC3_INDEX);
            float fTEC4Voltage = tec_get_channel_voltage(TEC4_INDEX);

            // Only update at first to initialize registers, otherwise race conditions can occur
            static uint8_t ubTECVoltageInitialized = 0;

            if(!ubTECVoltageInitialized)
            {
                ATOMIC_BLOCK(ATOMIC_RESTORESTATE)
                {
                    I2C_SLAVE_REGISTER(float, I2C_SLAVE_REGISTER_TEC1_VOLTAGE) = fTEC1Voltage;
                    I2C_SLAVE_REGISTER(float, I2C_SLAVE_REGISTER_TEC2_VOLTAGE) = fTEC2Voltage;
                    I2C_SLAVE_REGISTER(float, I2C_SLAVE_REGISTER_TEC3_VOLTAGE) = fTEC3Voltage;
                    I2C_SLAVE_REGISTER(float, I2C_SLAVE_REGISTER_TEC4_VOLTAGE) = fTEC4Voltage;
                }

                ubTECVoltageInitialized = 1;
            }

            DBGPRINTLN_CTX("----------------------------------");
            DBGPRINTLN_CTX("TEC #1 Voltage: %.2f mV", fTEC1Voltage);
            DBGPRINTLN_CTX("TEC #2 Voltage: %.2f mV", fTEC2Voltage);
            DBGPRINTLN_CTX("TEC #3 Voltage: %.2f mV", fTEC3Voltage);
            DBGPRINTLN_CTX("TEC #4 Voltage: %.2f mV", fTEC4Voltage);
        }

        if((g_ullSystemTick > 0 && ullLastTemperatureCheck == 0) || g_ullSystemTick - ullLastTemperatureCheck > 1000)
        {
            ullLastTemperatureCheck = g_ullSystemTick;

            ATOMIC_BLOCK(ATOMIC_RESTORESTATE)
            {
                uint8_t ubTempStatus = I2C_SLAVE_REGISTER(uint8_t, I2C_SLAVE_REGISTER_PA1_TEMP_STATUS) & 0xF0;
                uint8_t ubTempConfig = I2C_SLAVE_REGISTER(uint8_t, I2C_SLAVE_REGISTER_PA1_TEMP_CONFIG);

                float ubTemp = I2C_SLAVE_REGISTER(float, I2C_SLAVE_REGISTER_PA1_TEMP);
                float ubTempHigh = I2C_SLAVE_REGISTER(float, I2C_SLAVE_REGISTER_PA1_TEMP_HIGH);
                float ubTempLow = I2C_SLAVE_REGISTER(float, I2C_SLAVE_REGISTER_PA1_TEMP_LOW);

                if((ubTempConfig & BIT(0)) && ubTemp < ubTempLow)
                {
                    ubTempStatus |= BIT(0);
                    ubTempStatus |= BIT(2);
                }

                if((ubTempConfig & BIT(1)) && ubTemp > ubTempHigh)
                {
                    ubTempStatus |= BIT(1);
                    ubTempStatus |= BIT(3);
                }

                if(ubTempStatus & (BIT(0) | BIT(1)))
                {
                    I2C_SLAVE_REGISTER(uint8_t, I2C_SLAVE_REGISTER_CONFIG) &= ~BIT(0);

                    PA1_DISABLE();

                    // Disable TECs, if requested
                    if(ubTempConfig & BIT(4))
                    {
                        I2C_SLAVE_REGISTER(uint8_t, I2C_SLAVE_REGISTER_CONFIG) &= ~BIT(3);

                        TEC1_DISABLE();
                    }
                    if(ubTempConfig & BIT(5))
                    {
                        I2C_SLAVE_REGISTER(uint8_t, I2C_SLAVE_REGISTER_CONFIG) &= ~BIT(4);

                        TEC2_DISABLE();
                    }
                    if(ubTempConfig & BIT(6))
                    {
                        I2C_SLAVE_REGISTER(uint8_t, I2C_SLAVE_REGISTER_CONFIG) &= ~BIT(5);

                        TEC3_DISABLE();
                    }
                    if(ubTempConfig & BIT(7))
                    {
                        I2C_SLAVE_REGISTER(uint8_t, I2C_SLAVE_REGISTER_CONFIG) &= ~BIT(6);

                        TEC4_DISABLE();
                    }
                }

                I2C_SLAVE_REGISTER(uint8_t, I2C_SLAVE_REGISTER_PA1_TEMP_STATUS) = ubTempStatus;
            }

            ATOMIC_BLOCK(ATOMIC_RESTORESTATE)
            {
                uint8_t ubTempStatus = I2C_SLAVE_REGISTER(uint8_t, I2C_SLAVE_REGISTER_PA2_TEMP_STATUS) & 0xF0;
                uint8_t ubTempConfig = I2C_SLAVE_REGISTER(uint8_t, I2C_SLAVE_REGISTER_PA2_TEMP_CONFIG);

                float ubTemp = I2C_SLAVE_REGISTER(float, I2C_SLAVE_REGISTER_PA2_TEMP);
                float ubTempHigh = I2C_SLAVE_REGISTER(float, I2C_SLAVE_REGISTER_PA2_TEMP_HIGH);
                float ubTempLow = I2C_SLAVE_REGISTER(float, I2C_SLAVE_REGISTER_PA2_TEMP_LOW);

                if((ubTempConfig & BIT(0)) && ubTemp < ubTempLow)
                {
                    ubTempStatus |= BIT(0);
                    ubTempStatus |= BIT(2);
                }

                if((ubTempConfig & BIT(1)) && ubTemp > ubTempHigh)
                {
                    ubTempStatus |= BIT(1);
                    ubTempStatus |= BIT(3);
                }

                if(ubTempStatus & (BIT(0) | BIT(1)))
                {
                    I2C_SLAVE_REGISTER(uint8_t, I2C_SLAVE_REGISTER_CONFIG) &= ~BIT(1);

                    PA2_DISABLE();

                    // Disable TECs, if requested
                    if(ubTempConfig & BIT(4))
                    {
                        I2C_SLAVE_REGISTER(uint8_t, I2C_SLAVE_REGISTER_CONFIG) &= ~BIT(3);

                        TEC1_DISABLE();
                    }
                    if(ubTempConfig & BIT(5))
                    {
                        I2C_SLAVE_REGISTER(uint8_t, I2C_SLAVE_REGISTER_CONFIG) &= ~BIT(4);

                        TEC2_DISABLE();
                    }
                    if(ubTempConfig & BIT(6))
                    {
                        I2C_SLAVE_REGISTER(uint8_t, I2C_SLAVE_REGISTER_CONFIG) &= ~BIT(5);

                        TEC3_DISABLE();
                    }
                    if(ubTempConfig & BIT(7))
                    {
                        I2C_SLAVE_REGISTER(uint8_t, I2C_SLAVE_REGISTER_CONFIG) &= ~BIT(6);

                        TEC4_DISABLE();
                    }
                }

                I2C_SLAVE_REGISTER(uint8_t, I2C_SLAVE_REGISTER_PA2_TEMP_STATUS) = ubTempStatus;
            }
        }
    }

    return 0;
}
