vankxr/qo-100-tools/software/gpsdo/src/gpio.c

#include "gpio.h"

static void gpio_isr(uint32_t ulFlags)
{
    extern void ad9544_isr();
    extern void gps_timepulse_isr();

    if(ulFlags & BIT(8))
        ad9544_isr();

    if(ulFlags & BIT(13))
        gps_timepulse_isr();
}
void _gpio_even_isr()
{
    uint32_t ulFlags = GPIO->IF;

    gpio_isr(ulFlags & 0x55555555);

    GPIO->IFC = 0x55555555; // Clear all even flags
}
void _gpio_odd_isr()
{
    uint32_t ulFlags = GPIO->IF;

    gpio_isr(ulFlags & 0xAAAAAAAA);

    GPIO->IFC = 0xAAAAAAAA; // Clear all odd flags
}

void gpio_init()
{
    cmu_hfbus_clock_gate(CMU_HFBUSCLKEN0_GPIO, 1);

    // NC - Not Connected (not available in mcu package)
    // NR - Not routed (no routing to pin on pcb, floating)
    // NU - Not used (not currently in use)

    // Port A
    GPIO->P[0].CTRL   = GPIO_P_CTRL_DRIVESTRENGTHALT_STRONG | (5 << _GPIO_P_CTRL_SLEWRATEALT_SHIFT)
                      | GPIO_P_CTRL_DRIVESTRENGTH_STRONG | (5 << _GPIO_P_CTRL_SLEWRATE_SHIFT);
    GPIO->P[0].MODEL  = GPIO_P_MODEL_MODE0_PUSHPULL                 // GPS_RXD - USART3 - Location 0
                      | GPIO_P_MODEL_MODE1_INPUTPULL                // GPS_TXD - USART3 - Location 0 / GPS_TXREADY
                      | GPIO_P_MODEL_MODE2_PUSHPULL                 // nGPS_RESET
                      | GPIO_P_MODEL_MODE3_DISABLED                 // NR
                      | GPIO_P_MODEL_MODE4_DISABLED                 // NR
                      | GPIO_P_MODEL_MODE5_DISABLED                 // NR
                      | GPIO_P_MODEL_MODE6_WIREDANDPULLUPFILTER     // 3V3_PGOOD
                      | GPIO_P_MODEL_MODE7_DISABLED;                // NR
    GPIO->P[0].MODEH  = GPIO_P_MODEH_MODE8_DISABLED                 // NR
                      | GPIO_P_MODEH_MODE9_DISABLED                 // NR
                      | GPIO_P_MODEH_MODE10_DISABLED                // NR
                      | GPIO_P_MODEH_MODE11_DISABLED                // NR
                      | GPIO_P_MODEH_MODE12_DISABLED                // NR
                      | GPIO_P_MODEH_MODE13_DISABLED                // NR
                      | GPIO_P_MODEH_MODE14_DISABLED                // NR
                      | GPIO_P_MODEH_MODE15_DISABLED;               // NR
    GPIO->P[0].DOUT   = BIT(0) | BIT(1) | BIT(2) | BIT(6);
    GPIO->P[0].OVTDIS = 0;

    // Port B
    GPIO->P[1].CTRL   = GPIO_P_CTRL_DRIVESTRENGTHALT_STRONG | (5 << _GPIO_P_CTRL_SLEWRATEALT_SHIFT)
                      | GPIO_P_CTRL_DRIVESTRENGTH_STRONG | (5 << _GPIO_P_CTRL_SLEWRATE_SHIFT);
    GPIO->P[1].MODEL  = GPIO_P_MODEL_MODE0_DISABLED                 // NR
                      | GPIO_P_MODEL_MODE1_DISABLED                 // NR
                      | GPIO_P_MODEL_MODE2_DISABLED                 // NR
                      | GPIO_P_MODEL_MODE3_DISABLED                 // NR
                      | GPIO_P_MODEL_MODE4_DISABLED                 // NR
                      | GPIO_P_MODEL_MODE5_DISABLED                 // NR
                      | GPIO_P_MODEL_MODE6_DISABLED                 // NR
                      | GPIO_P_MODEL_MODE7_DISABLED;                // NR
    GPIO->P[1].MODEH  = GPIO_P_MODEH_MODE8_DISABLED                 // NR
                      | GPIO_P_MODEH_MODE9_DISABLED                 // NR
                      | GPIO_P_MODEH_MODE10_DISABLED                // NR
                      | GPIO_P_MODEH_MODE11_WIREDANDALTPULLUPFILTER // I2C1_SDA - I2C1 - Location 1
                      | GPIO_P_MODEH_MODE12_WIREDANDALTPULLUPFILTER // I2C1_SCL - I2C1 - Location 1
                      | GPIO_P_MODEH_MODE13_PUSHPULL                // MCU_LED
                      | GPIO_P_MODEH_MODE14_DISABLED                // NR
                      | GPIO_P_MODEH_MODE15_DISABLED;               // NR
    GPIO->P[1].DOUT   = 0;
    GPIO->P[1].OVTDIS = BIT(11);

    // Port C
    GPIO->P[2].CTRL   = GPIO_P_CTRL_DRIVESTRENGTHALT_STRONG | (5 << _GPIO_P_CTRL_SLEWRATEALT_SHIFT)
                      | GPIO_P_CTRL_DRIVESTRENGTH_STRONG | (5 << _GPIO_P_CTRL_SLEWRATE_SHIFT);
    GPIO->P[2].MODEL  = GPIO_P_MODEL_MODE0_DISABLED                 // NR
                      | GPIO_P_MODEL_MODE1_DISABLED                 // NR
                      | GPIO_P_MODEL_MODE2_DISABLED                 // NR
                      | GPIO_P_MODEL_MODE3_DISABLED                 // NR
                      | GPIO_P_MODEL_MODE4_DISABLED                 // NR
                      | GPIO_P_MODEL_MODE5_DISABLED                 // NR
                      | GPIO_P_MODEL_MODE6_DISABLED                 // NR
                      | GPIO_P_MODEL_MODE7_DISABLED;                // NR
    GPIO->P[2].MODEH  = GPIO_P_MODEH_MODE8_DISABLED                 // NR
                      | GPIO_P_MODEH_MODE9_DISABLED                 // NR
                      | GPIO_P_MODEH_MODE10_DISABLED                // NR
                      | GPIO_P_MODEH_MODE11_DISABLED                // NR
                      | GPIO_P_MODEH_MODE12_DISABLED                // NC
                      | GPIO_P_MODEH_MODE13_DISABLED                // NC
                      | GPIO_P_MODEH_MODE14_DISABLED                // NC
                      | GPIO_P_MODEH_MODE15_DISABLED;               // NC
    GPIO->P[2].DOUT   = 0;
    GPIO->P[2].OVTDIS = 0;

    // Port D
    GPIO->P[3].CTRL   = GPIO_P_CTRL_DRIVESTRENGTHALT_STRONG | (5 << _GPIO_P_CTRL_SLEWRATEALT_SHIFT)
                      | GPIO_P_CTRL_DRIVESTRENGTH_STRONG | (5 << _GPIO_P_CTRL_SLEWRATE_SHIFT);
    GPIO->P[3].MODEL  = GPIO_P_MODEL_MODE0_DISABLED                 // NR
                      | GPIO_P_MODEL_MODE1_DISABLED                 // NR
                      | GPIO_P_MODEL_MODE2_DISABLED                 // NR
                      | GPIO_P_MODEL_MODE3_DISABLED                 // NR
                      | GPIO_P_MODEL_MODE4_DISABLED                 // VIN_VSENSE
                      | GPIO_P_MODEL_MODE5_DISABLED                 // NR
                      | GPIO_P_MODEL_MODE6_DISABLED                 // 5V0_VSENSE
                      | GPIO_P_MODEL_MODE7_DISABLED;                // NR
    GPIO->P[3].MODEH  = GPIO_P_MODEH_MODE8_DISABLED                 // NR
                      | GPIO_P_MODEH_MODE9_DISABLED                 // NR
                      | GPIO_P_MODEH_MODE10_INPUTPULL               // nPLL_IRQ
                      | GPIO_P_MODEH_MODE11_DISABLED                // NR
                      | GPIO_P_MODEH_MODE12_DISABLED                // NR
                      | GPIO_P_MODEH_MODE13_DISABLED                // NR
                      | GPIO_P_MODEH_MODE14_DISABLED                // NR
                      | GPIO_P_MODEH_MODE15_DISABLED;               // NR
    GPIO->P[3].DOUT   = BIT(10);
    GPIO->P[3].OVTDIS = BIT(4) | BIT(6);

    // Port E
    GPIO->P[4].CTRL   = GPIO_P_CTRL_DRIVESTRENGTHALT_STRONG | (5 << _GPIO_P_CTRL_SLEWRATEALT_SHIFT)
                      | GPIO_P_CTRL_DRIVESTRENGTH_STRONG | (5 << _GPIO_P_CTRL_SLEWRATE_SHIFT);
    GPIO->P[4].MODEL  = GPIO_P_MODEL_MODE0_DISABLED                 // NR
                      | GPIO_P_MODEL_MODE1_DISABLED                 // NR
                      | GPIO_P_MODEL_MODE2_DISABLED                 // NR
                      | GPIO_P_MODEL_MODE3_DISABLED                 // NR
                      | GPIO_P_MODEL_MODE4_DISABLED                 // NR
                      | GPIO_P_MODEL_MODE5_DISABLED                 // NR
                      | GPIO_P_MODEL_MODE6_DISABLED                 // NR
                      | GPIO_P_MODEL_MODE7_DISABLED;                // NR
    GPIO->P[4].MODEH  = GPIO_P_MODEH_MODE8_WIREDANDALTPULLUPFILTER  // I2C2_SDA - I2C2 - Location 0
                      | GPIO_P_MODEH_MODE9_DISABLED                 // NR
                      | GPIO_P_MODEH_MODE10_PUSHPULL                // DAC_DIN - USART0 - Location 0
                      | GPIO_P_MODEH_MODE11_PUSHPULL                // OCXO_EN
                      | GPIO_P_MODEH_MODE12_PUSHPULL                // DAC_SCLK - USART0 - Location 0
                      | GPIO_P_MODEH_MODE13_PUSHPULL                // nDAC_CS - USART0 - Location 0
                      | GPIO_P_MODEH_MODE14_DISABLED                // NR
                      | GPIO_P_MODEH_MODE15_INPUTPULL;              // GPS_TIMEPULSE_BUF
    GPIO->P[4].DOUT   = BIT(13);
    GPIO->P[4].OVTDIS = 0;

    // Port F
    GPIO->P[5].CTRL   = GPIO_P_CTRL_DRIVESTRENGTHALT_STRONG | (5 << _GPIO_P_CTRL_SLEWRATEALT_SHIFT)
                      | GPIO_P_CTRL_DRIVESTRENGTH_STRONG | (5 << _GPIO_P_CTRL_SLEWRATE_SHIFT);
    GPIO->P[5].MODEL  = GPIO_P_MODEL_MODE0_PUSHPULL                 // DBG_SWCLK - Location 0
                      | GPIO_P_MODEL_MODE1_PUSHPULL                 // DBG_SWDIO - Location 0
                      | GPIO_P_MODEL_MODE2_PUSHPULL                 // DBG_SWO - Location 0
                      | GPIO_P_MODEL_MODE3_DISABLED                 // NC
                      | GPIO_P_MODEL_MODE4_DISABLED                 // NC
                      | GPIO_P_MODEL_MODE5_WIREDANDALTPULLUPFILTER  // I2C2_SCL - I2C2 - Location 0
                      | GPIO_P_MODEL_MODE6_DISABLED                 // NR
                      | GPIO_P_MODEL_MODE7_PUSHPULL;                // nPLL_RESET
    GPIO->P[5].MODEH  = GPIO_P_MODEH_MODE8_DISABLED                 // NR
                      | GPIO_P_MODEH_MODE9_DISABLED                 // NR
                      | GPIO_P_MODEH_MODE10_DISABLED                // NR
                      | GPIO_P_MODEH_MODE11_DISABLED                // NR
                      | GPIO_P_MODEH_MODE12_INPUTPULL               // OCXO_CLK_BUF
                      | GPIO_P_MODEH_MODE13_DISABLED                // NC
                      | GPIO_P_MODEH_MODE14_DISABLED                // NC
                      | GPIO_P_MODEH_MODE15_DISABLED;               // NC
    GPIO->P[5].DOUT   = BIT(7);
    GPIO->P[5].OVTDIS = 0;

    // Debugger Route
    GPIO->ROUTEPEN &= ~(GPIO_ROUTEPEN_TDIPEN | GPIO_ROUTEPEN_TDOPEN);   // Disable JTAG
    GPIO->ROUTEPEN |= GPIO_ROUTEPEN_SWVPEN;                             // Enable SWO
    GPIO->ROUTELOC0 = GPIO_ROUTELOC0_SWVLOC_LOC0;                       // SWO on PF2

    // External interrupts
    GPIO->EXTIPSELL = GPIO_EXTIPSELL_EXTIPSEL0_PORTA            // NU
                    | GPIO_EXTIPSELL_EXTIPSEL1_PORTA            // NU
                    | GPIO_EXTIPSELL_EXTIPSEL2_PORTA            // NU
                    | GPIO_EXTIPSELL_EXTIPSEL3_PORTA            // NU
                    | GPIO_EXTIPSELL_EXTIPSEL4_PORTA            // NU
                    | GPIO_EXTIPSELL_EXTIPSEL5_PORTA            // NU
                    | GPIO_EXTIPSELL_EXTIPSEL6_PORTA            // NU
                    | GPIO_EXTIPSELL_EXTIPSEL7_PORTA;           // NU
    GPIO->EXTIPSELH = GPIO_EXTIPSELH_EXTIPSEL8_PORTD            // nPLL_IRQ
                    | GPIO_EXTIPSELH_EXTIPSEL9_PORTA            // NU
                    | GPIO_EXTIPSELH_EXTIPSEL10_PORTA           // NU
                    | GPIO_EXTIPSELH_EXTIPSEL11_PORTA           // NU
                    | GPIO_EXTIPSELH_EXTIPSEL12_PORTF           // OCXO_CLK_BUF
                    | GPIO_EXTIPSELH_EXTIPSEL13_PORTE           // GPS_TIMEPULSE_BUF
                    | GPIO_EXTIPSELH_EXTIPSEL14_PORTA           // NU
                    | GPIO_EXTIPSELH_EXTIPSEL15_PORTA;          // NU

    GPIO->EXTIPINSELL = GPIO_EXTIPINSELL_EXTIPINSEL0_PIN0       // NU
                      | GPIO_EXTIPINSELL_EXTIPINSEL1_PIN0       // NU
                      | GPIO_EXTIPINSELL_EXTIPINSEL2_PIN0       // NU
                      | GPIO_EXTIPINSELL_EXTIPINSEL3_PIN0       // NU
                      | GPIO_EXTIPINSELL_EXTIPINSEL4_PIN4       // NU
                      | GPIO_EXTIPINSELL_EXTIPINSEL5_PIN4       // NU
                      | GPIO_EXTIPINSELL_EXTIPINSEL6_PIN4       // NU
                      | GPIO_EXTIPINSELL_EXTIPINSEL7_PIN4;      // NU
    GPIO->EXTIPINSELH = GPIO_EXTIPINSELH_EXTIPINSEL8_PIN10      // nPLL_IRQ
                      | GPIO_EXTIPINSELH_EXTIPINSEL9_PIN8       // NU
                      | GPIO_EXTIPINSELH_EXTIPINSEL10_PIN8      // NU
                      | GPIO_EXTIPINSELH_EXTIPINSEL11_PIN8      // NU
                      | GPIO_EXTIPINSELH_EXTIPINSEL12_PIN12     // OCXO_CLK_BUF
                      | GPIO_EXTIPINSELH_EXTIPINSEL13_PIN15     // GPS_TIMEPULSE_BUF
                      | GPIO_EXTIPINSELH_EXTIPINSEL14_PIN12     // NU
                      | GPIO_EXTIPINSELH_EXTIPINSEL15_PIN12;    // NU

    GPIO->EXTIRISE = BIT(13); // GPS_TIMEPULSE_BUF
    GPIO->EXTIFALL = BIT(8) | BIT(13); // nPLL_IRQ, GPS_TIMEPULSE_BUF

    GPIO->IFC = _GPIO_IFC_MASK; // Clear pending IRQs
    IRQ_CLEAR(GPIO_EVEN_IRQn); // Clear pending vector
    IRQ_CLEAR(GPIO_ODD_IRQn); // Clear pending vector
    IRQ_SET_PRIO(GPIO_EVEN_IRQn, 0, 0); // Set priority 0,0 (max)
    IRQ_SET_PRIO(GPIO_ODD_IRQn, 0, 0); // Set priority 0,0 (max)
    IRQ_ENABLE(GPIO_EVEN_IRQn); // Enable vector
    IRQ_ENABLE(GPIO_ODD_IRQn); // Enable vector
    GPIO->IEN = BIT(8) | BIT(13); // Enable interrupts
}
