vankxr/qo-100-tools/software/opi-rf-manager/index.js

const FileSystem = require("fs");
const Util = require("util");
const ReadLine = require('readline');
const Crypto = require("crypto");
const SSH2 = require("ssh2");
const ShellQuote = require("shell-quote");
const Geolib = require("geolib");
const MQTT = require("async-mqtt");
const GPIO = require("./lib/gpio");
const { I2C, I2CDevice } = require("./lib/i2c");
const { OneWire, OneWireDevice } = require("./lib/onewire");
const { IPMA, IPMAStation, IPMALocation } = require("./lib/ipma");
const WBSpectrumMonitor = require("./lib/wb_spectrum_monitor");
const OAQ = require("./lib/oaq");
const HPPSU = require("./lib/hppsu");
const DS2484 = require("./lib/ds2484");
const BME280 = require("./lib/bme280");
const ZMOD4510 = require("./lib/zmod4510");
const SI1133 = require("./lib/si1133");
const MCP3221 = require("./lib/mcp3221");
const MCP3421 = require("./lib/mcp3421");
const MCP23008 = require("./lib/mcp23008");
const MCP23017 = require("./lib/mcp23017");
const F2915 = require("./lib/f2915");
const LTC5597 = require("./lib/ltc5597");
const LTC4151 = require("./lib/ltc4151");
const DS18B20 = require("./lib/ds18b20");
const I2CBuffer = require("./lib/i2c_buffer");
const RelayController = require("./lib/relay_controller");
const PABiasController = require("./lib/pa_bias_controller");
const LNBController = require("./lib/lnb_controller");
const Upconverter = require("./lib/upconverter");
const LogFileManager = require("./util/log_file_manager");
const Printer = require("./util/printer");
const delay = require("./util/delay");
const { isDataView } = require("util/types");

const gs_location = JSON.parse(FileSystem.readFileSync("/root/gs_location.json")); // TODO: Get real location via GPS
const mqtt_credentials = JSON.parse(FileSystem.readFileSync("/root/mqtt_credentials.json"));
let cl;
let ipma_station;
let ipma_location;
let wb_spectrum_monitor;
let wb_signals = {};
const gpios = {};
const buses = {};
const devices = {};
const ssh_allowed_users = [];
const ssh_commands = {};
let ssh_server;
const mqtt_topic_prefix = "devices/opi-rf-manager/";
const mqtt_data_qos = 1;
let mqtt_client;

function log_init()
{
    const console_file = new LogFileManager(LogFileManager.DAILY, __dirname + "/log", "console_", ".log");

    console_file.start();

    const console_file_printer = new Printer(console_file, false);
    const console_stdout_printer = new Printer(process.stdout, true);

    console_stdout_printer.chain(console_file_printer);

    cl = console_stdout_printer;
}

async function mqtt_init()
{
    mqtt_client = MQTT.connect(
        {
            protocol: mqtt_credentials.ssl ? "mqtts" : "mqtt",
            host: mqtt_credentials.host,
            port: mqtt_credentials.port,
            keepalive: 60,
            reschedulePings: true,
            clientId: "opi-rf-manager-" + Crypto.randomBytes(8).toString("hex"),
            protocolId: "MQTT",
            protocolVersion: 4,
            clean: true,
            reconnectPeriod: 1000,
            connectTimeout: 30 * 1000,
            username: mqtt_credentials.username,
            password: mqtt_credentials.password,
            queueQoSZero: true,
            will: {
                topic: mqtt_topic_prefix + "status",
                payload: "offline",
                qos: 1,
                retain: true
            },
            resubscribe: false,
            rejectUnauthorized: !mqtt_credentials.ssl_self_signed
        }
    );

    mqtt_client.on("connect", mqtt_connect_handler);
    mqtt_client.on("reconnect", mqtt_reconnect_handler);
    mqtt_client.on("message", mqtt_message_handler);
    mqtt_client.on("error", mqtt_error_handler);
    mqtt_client.on("close", mqtt_close_handler);

    mqtt_update_telemery(true); // Trigger telemetry loop
}
async function mqtt_connect_handler()
{
    cl.tprintln("green", "MQTT", "MQTT (re)connected!");

    try
    {
        await mqtt_client.publish(mqtt_topic_prefix + "/status", "online", { qos: 1, retain: true });

        await mqtt_client.subscribe(mqtt_topic_prefix + "/config/#");
    }
    catch(e)
    {
        cl.tprintln("red", "MQTT", "Error: " + e);
    }

    mqtt_update_telemery(false); // Do not trigger loop, as it can be already running on reconnection
}
function mqtt_reconnect_handler()
{
    cl.tprintln("yellow", "MQTT", "MQTT reconnecting...");
}
async function mqtt_message_handler(topic, payload)
{
    let path = topic.split("/");

    if(path[0] !== "devices" || path[1] !== "opi-rf-manager")
        return;

    console.log("MQTT msg:", topic, payload);
}
function mqtt_error_handler(e)
{
    cl.tprintln("red", "MQTT", "Error: " + e);
}
function mqtt_close_handler()
{
    cl.tprintln("yellow", "MQTT", "MQTT connection closed!");
}
async function mqtt_update_telemery(loop)
{
    if(!mqtt_client || !mqtt_client.connected)
    {
        if(loop)
            setTimeout(mqtt_update_telemery, 60000, true); // Update every minute

        return;
    }

    for(let device_name in devices)
    {
        let device = devices[device_name];

        try
        {
            if(device instanceof HPPSU)
            {
                await mqtt_client.publish(mqtt_topic_prefix + "data/status/" + device_name + "_input_present", (await device.is_input_present()) ? "1" : "0", { qos: mqtt_data_qos });
                await mqtt_client.publish(mqtt_topic_prefix + "data/status/" + device_name + "_output_enabled", (await device.is_main_output_enabled()) ? "1" : "0", { qos: mqtt_data_qos });

                await mqtt_client.publish(mqtt_topic_prefix + "data/voltage/" + device_name + "_input", ((await device.get_input_voltage()) * 1000).toFixed(2).toString(), { qos: mqtt_data_qos });
                await mqtt_client.publish(mqtt_topic_prefix + "data/voltage/" + device_name + "_input_nominal", ((await device.get_nominal_input_voltage()) * 1000).toFixed(2).toString(), { qos: mqtt_data_qos });
                await mqtt_client.publish(mqtt_topic_prefix + "data/voltage/" + device_name + "_input_uv_thresh", ((await device.get_input_undervoltage_threshold()) * 1000).toFixed(2).toString(), { qos: mqtt_data_qos });
                await mqtt_client.publish(mqtt_topic_prefix + "data/voltage/" + device_name + "_input_ov_thresh", ((await device.get_input_overvoltage_threshold()) * 1000).toFixed(2).toString(), { qos: mqtt_data_qos });
                await mqtt_client.publish(mqtt_topic_prefix + "data/voltage/" + device_name + "_output", ((await device.get_output_voltage()) * 1000).toFixed(2).toString(), { qos: mqtt_data_qos });
                await mqtt_client.publish(mqtt_topic_prefix + "data/voltage/" + device_name + "_output_uv_thresh", ((await device.get_output_undervoltage_threshold()) * 1000).toFixed(2).toString(), { qos: mqtt_data_qos });
                await mqtt_client.publish(mqtt_topic_prefix + "data/voltage/" + device_name + "_output_ov_thresh", ((await device.get_output_overvoltage_threshold()) * 1000).toFixed(2).toString(), { qos: mqtt_data_qos });

                await mqtt_client.publish(mqtt_topic_prefix + "data/current/" + device_name + "_input", ((await device.get_input_current()) * 1000).toFixed(2).toString(), { qos: mqtt_data_qos });
                await mqtt_client.publish(mqtt_topic_prefix + "data/current/" + device_name + "_output", ((await device.get_output_current()) * 1000).toFixed(2).toString(), { qos: mqtt_data_qos });

                await mqtt_client.publish(mqtt_topic_prefix + "data/power/" + device_name + "_input", (await device.get_input_power()).toFixed(2).toString(), { qos: mqtt_data_qos });
                await mqtt_client.publish(mqtt_topic_prefix + "data/power/" + device_name + "_output", (await device.get_output_power()).toFixed(2).toString(), { qos: mqtt_data_qos });

                await mqtt_client.publish(mqtt_topic_prefix + "data/energy/" + device_name + "_input", (await device.get_input_energy()).toFixed(2).toString(), { qos: mqtt_data_qos });

                await mqtt_client.publish(mqtt_topic_prefix + "data/efficiency/" + device_name, (await device.get_efficiency()).toFixed(2).toString(), { qos: mqtt_data_qos });

                await mqtt_client.publish(mqtt_topic_prefix + "data/temperature/" + device_name + "_intake", (await device.get_intake_temperature()).toFixed(2).toString(), { qos: mqtt_data_qos });
                await mqtt_client.publish(mqtt_topic_prefix + "data/temperature/" + device_name + "_internal", (await device.get_internal_temperature()).toFixed(2).toString(), { qos: mqtt_data_qos });

                await mqtt_client.publish(mqtt_topic_prefix + "data/fan_speed/" + device_name, (await device.get_fan_speed()).toFixed(2).toString(), { qos: mqtt_data_qos });
                await mqtt_client.publish(mqtt_topic_prefix + "data/fan_speed/" + device_name + "_target", (await device.get_fan_target_speed()).toFixed(2).toString(), { qos: mqtt_data_qos });

                await mqtt_client.publish(mqtt_topic_prefix + "data/on_time/" + device_name, (await device.get_on_time()).toFixed(2).toString(), { qos: mqtt_data_qos });
                await mqtt_client.publish(mqtt_topic_prefix + "data/on_time/" + device_name + "_total", (await device.get_on_time()).toFixed(2).toString(), { qos: mqtt_data_qos });
            }
            else if(device instanceof RelayController)
            {
                let chip_voltages = await device.get_chip_voltages();
                let system_voltages = await device.get_system_voltages();
                await mqtt_client.publish(mqtt_topic_prefix + "data/voltage/" + device_name + "_avdd", chip_voltages.avdd.toFixed(2).toString(), { qos: mqtt_data_qos });
                await mqtt_client.publish(mqtt_topic_prefix + "data/voltage/" + device_name + "_dvdd", chip_voltages.dvdd.toFixed(2).toString(), { qos: mqtt_data_qos });
                await mqtt_client.publish(mqtt_topic_prefix + "data/voltage/" + device_name + "_iovdd", chip_voltages.iovdd.toFixed(2).toString(), { qos: mqtt_data_qos });
                await mqtt_client.publish(mqtt_topic_prefix + "data/voltage/" + device_name + "_core", chip_voltages.core.toFixed(2).toString(), { qos: mqtt_data_qos });
                await mqtt_client.publish(mqtt_topic_prefix + "data/voltage/" + device_name + "_vin", system_voltages.vin.toFixed(2).toString(), { qos: mqtt_data_qos });
                await mqtt_client.publish(mqtt_topic_prefix + "data/voltage/" + device_name + "_vin_uv_thresh", (await device.get_relay_undervoltage_point()).toFixed(2).toString(), { qos: mqtt_data_qos });

                let chip_temperatures = await device.get_chip_temperatures();
                await mqtt_client.publish(mqtt_topic_prefix + "data/temperature/" + device_name + "_adc", chip_temperatures.adc.toFixed(2).toString(), { qos: mqtt_data_qos });
                await mqtt_client.publish(mqtt_topic_prefix + "data/temperature/" + device_name + "_emu", chip_temperatures.emu.toFixed(2).toString(), { qos: mqtt_data_qos });

                let rstatus = await device.get_relay_status();

                for(let i = 0; i < 12; i++)
                {
                    await mqtt_client.publish(mqtt_topic_prefix + "data/status/" + device_name + "_relay" + i + "_status", (rstatus & (1 << i)) ? "1" : "0", { qos: mqtt_data_qos });
                    await mqtt_client.publish(mqtt_topic_prefix + "data/voltage/" + device_name + "_relay" + i, (await device.get_relay_voltage(i)).toFixed(2).toString(), { qos: mqtt_data_qos });
                    await mqtt_client.publish(mqtt_topic_prefix + "data/duty_cycle/" + device_name + "_relay" + i, (await device.get_relay_duty_cycle(i)).toFixed(2).toString(), { qos: mqtt_data_qos });
                }
            }
            else if(device instanceof Upconverter)
            {
                let chip_voltages = await device.get_chip_voltages();
                let system_voltages = await device.get_system_voltages();
                await mqtt_client.publish(mqtt_topic_prefix + "data/voltage/" + device_name + "_avdd", chip_voltages.avdd.toFixed(2).toString(), { qos: mqtt_data_qos });
                await mqtt_client.publish(mqtt_topic_prefix + "data/voltage/" + device_name + "_dvdd", chip_voltages.dvdd.toFixed(2).toString(), { qos: mqtt_data_qos });
                await mqtt_client.publish(mqtt_topic_prefix + "data/voltage/" + device_name + "_iovdd", chip_voltages.iovdd.toFixed(2).toString(), { qos: mqtt_data_qos });
                await mqtt_client.publish(mqtt_topic_prefix + "data/voltage/" + device_name + "_core", chip_voltages.core.toFixed(2).toString(), { qos: mqtt_data_qos });
                await mqtt_client.publish(mqtt_topic_prefix + "data/voltage/" + device_name + "_vin", system_voltages.vin.toFixed(2).toString(), { qos: mqtt_data_qos });
                await mqtt_client.publish(mqtt_topic_prefix + "data/voltage/" + device_name + "_v5v0", system_voltages.v5v0.toFixed(2).toString(), { qos: mqtt_data_qos });

                let system_currents = await device.get_system_currents();
                await mqtt_client.publish(mqtt_topic_prefix + "data/current/" + device_name + "_i5v0", system_currents.i5v0.toFixed(2).toString(), { qos: mqtt_data_qos });

                let chip_temperatures = await device.get_chip_temperatures();
                await mqtt_client.publish(mqtt_topic_prefix + "data/temperature/" + device_name + "_adc", chip_temperatures.adc.toFixed(2).toString(), { qos: mqtt_data_qos });
                await mqtt_client.publish(mqtt_topic_prefix + "data/temperature/" + device_name + "_emu", chip_temperatures.emu.toFixed(2).toString(), { qos: mqtt_data_qos });

                await mqtt_client.publish(mqtt_topic_prefix + "data/rf_power/" + device_name + "_out", (await device.get_rf_power()).toFixed(2).toString(), { qos: mqtt_data_qos });
                await mqtt_client.publish(mqtt_topic_prefix + "data/rf_power_modulation/" + device_name + "_out", Upconverter.get_modulation_name(await device.get_rf_power_modulation()), { qos: mqtt_data_qos });

                await mqtt_client.publish(mqtt_topic_prefix + "data/rf_power/" + device_name + "_out_low_thresh", (await device.get_low_rf_power_threshold()).toFixed(2).toString(), { qos: mqtt_data_qos });

                await mqtt_client.publish(mqtt_topic_prefix + "data/rf_attenuation/" + device_name + "_if", (await device.get_if_attenuation()).toFixed(2).toString(), { qos: mqtt_data_qos });
                await mqtt_client.publish(mqtt_topic_prefix + "data/rf_attenuation/" + device_name + "_rf1", (await device.get_rf1_attenuation()).toFixed(2).toString(), { qos: mqtt_data_qos });
                await mqtt_client.publish(mqtt_topic_prefix + "data/rf_attenuation/" + device_name + "_rf2", (await device.get_rf2_attenuation()).toFixed(2).toString(), { qos: mqtt_data_qos });

                await mqtt_client.publish(mqtt_topic_prefix + "data/frequency/" + device_name + "_lo", (await device.get_lo_frequency()).toString(), { qos: mqtt_data_qos });
                await mqtt_client.publish(mqtt_topic_prefix + "data/frequency/" + device_name + "_lo_ref", (await device.get_lo_ref_frequency()).toString(), { qos: mqtt_data_qos });
                await mqtt_client.publish(mqtt_topic_prefix + "data/frequency/" + device_name + "_lo_pfd", (await device.get_lo_pfd_frequency()).toString(), { qos: mqtt_data_qos });

                await mqtt_client.publish(mqtt_topic_prefix + "data/status/" + device_name + "_lo_locked", (await device.is_lo_pll_locked()) ? "1" : "0", { qos: mqtt_data_qos });
                await mqtt_client.publish(mqtt_topic_prefix + "data/status/" + device_name + "_lo_muted", (await device.is_lo_pll_muted()) ? "1" : "0", { qos: mqtt_data_qos });
                await mqtt_client.publish(mqtt_topic_prefix + "data/status/" + device_name + "_mixer_enabled", (await device.get_mixer_status()) ? "1" : "0", { qos: mqtt_data_qos });
                await mqtt_client.publish(mqtt_topic_prefix + "data/status/" + device_name + "_pre_amp_enabled", (await device.get_pa_stg1_2_status()) ? "1" : "0", { qos: mqtt_data_qos });
                await mqtt_client.publish(mqtt_topic_prefix + "data/status/" + device_name + "_final_amp_enabled", (await device.get_pa_stg3_status()) ? "1" : "0", { qos: mqtt_data_qos });
            }
            else if(device instanceof PABiasController)
            {
                let chip_voltages = await device.get_chip_voltages();
                let system_voltages = await device.get_system_voltages();
                await mqtt_client.publish(mqtt_topic_prefix + "data/voltage/" + device_name + "_avdd", chip_voltages.avdd.toFixed(2).toString(), { qos: mqtt_data_qos });
                await mqtt_client.publish(mqtt_topic_prefix + "data/voltage/" + device_name + "_dvdd", chip_voltages.dvdd.toFixed(2).toString(), { qos: mqtt_data_qos });
                await mqtt_client.publish(mqtt_topic_prefix + "data/voltage/" + device_name + "_iovdd", chip_voltages.iovdd.toFixed(2).toString(), { qos: mqtt_data_qos });
                await mqtt_client.publish(mqtt_topic_prefix + "data/voltage/" + device_name + "_core", chip_voltages.core.toFixed(2).toString(), { qos: mqtt_data_qos });
                await mqtt_client.publish(mqtt_topic_prefix + "data/voltage/" + device_name + "_vin", system_voltages.vin.toFixed(2).toString(), { qos: mqtt_data_qos });
                await mqtt_client.publish(mqtt_topic_prefix + "data/voltage/" + device_name + "_v5v0", system_voltages.v5v0.toFixed(2).toString(), { qos: mqtt_data_qos });

                let chip_temperatures = await device.get_chip_temperatures();
                let system_temperatures = await device.get_system_temperatures();
                await mqtt_client.publish(mqtt_topic_prefix + "data/temperature/" + device_name + "_adc", chip_temperatures.adc.toFixed(2).toString(), { qos: mqtt_data_qos });
                await mqtt_client.publish(mqtt_topic_prefix + "data/temperature/" + device_name + "_emu", chip_temperatures.emu.toFixed(2).toString(), { qos: mqtt_data_qos });
                await mqtt_client.publish(mqtt_topic_prefix + "data/temperature/" + device_name + "_afe", system_temperatures.afe.toFixed(2).toString(), { qos: mqtt_data_qos });

                let tec_dac_init = await device.get_tec_dac_status();
                await mqtt_client.publish(mqtt_topic_prefix + "data/status/" + device_name + "_tec_dac_init", tec_dac_init ? "1" : "0", { qos: mqtt_data_qos });

                if(tec_dac_init)
                {
                    for(let i = 0; i < 4; i++)
                    {
                        await mqtt_client.publish(mqtt_topic_prefix + "data/status/" + device_name + "_tec" + i, (await device.get_tec_status(i)) ? "1" : "0", { qos: mqtt_data_qos });
                        await mqtt_client.publish(mqtt_topic_prefix + "data/voltage/" + device_name + "_tec" + i, (await device.get_tec_voltage(i)).toFixed(2).toString(), { qos: mqtt_data_qos });
                    }
                }

                for(let i = 0; i < 2; i++)
                {
                    let data = await device.get_pa_telemetry(i);

                    await mqtt_client.publish(mqtt_topic_prefix + "data/status/" + device_name + "_pa" + i, (await device.get_pa_status(i)) ? "1" : "0", { qos: mqtt_data_qos });
                    await mqtt_client.publish(mqtt_topic_prefix + "data/voltage/" + device_name + "_pa" + i + "_vgg_raw", data.vgg_raw.toFixed(2).toString(), { qos: mqtt_data_qos });
                    await mqtt_client.publish(mqtt_topic_prefix + "data/voltage/" + device_name + "_pa" + i + "_vgg", data.vgg.toFixed(2).toString(), { qos: mqtt_data_qos });
                    await mqtt_client.publish(mqtt_topic_prefix + "data/voltage/" + device_name + "_pa" + i + "_vdd", data.vdd.toFixed(2).toString(), { qos: mqtt_data_qos });
                    await mqtt_client.publish(mqtt_topic_prefix + "data/current/" + device_name + "_pa" + i + "_idd", data.idd.toFixed(2).toString(), { qos: mqtt_data_qos });
                    await mqtt_client.publish(mqtt_topic_prefix + "data/temperature/" + device_name + "_pa" + i, data.temperature.toFixed(2).toString(), { qos: mqtt_data_qos });
                    await mqtt_client.publish(mqtt_topic_prefix + "data/temperature/" + device_name + "_pa" + i + "_high_thresh", data.temperature_high.toFixed(2).toString(), { qos: mqtt_data_qos });
                    await mqtt_client.publish(mqtt_topic_prefix + "data/temperature/" + device_name + "_pa" + i + "_low_thresh", data.temperature_low.toFixed(2).toString(), { qos: mqtt_data_qos });
                }
            }
            else if(device instanceof LNBController)
            {
                let chip_voltages = await device.get_chip_voltages();
                let system_voltages = await device.get_system_voltages();
                await mqtt_client.publish(mqtt_topic_prefix + "data/voltage/" + device_name + "_avdd", chip_voltages.avdd.toFixed(2).toString(), { qos: mqtt_data_qos });
                await mqtt_client.publish(mqtt_topic_prefix + "data/voltage/" + device_name + "_dvdd", chip_voltages.dvdd.toFixed(2).toString(), { qos: mqtt_data_qos });
                await mqtt_client.publish(mqtt_topic_prefix + "data/voltage/" + device_name + "_iovdd", chip_voltages.iovdd.toFixed(2).toString(), { qos: mqtt_data_qos });
                await mqtt_client.publish(mqtt_topic_prefix + "data/voltage/" + device_name + "_core", chip_voltages.core.toFixed(2).toString(), { qos: mqtt_data_qos });
                await mqtt_client.publish(mqtt_topic_prefix + "data/voltage/" + device_name + "_vin", system_voltages.vin.toFixed(2).toString(), { qos: mqtt_data_qos });
                await mqtt_client.publish(mqtt_topic_prefix + "data/voltage/" + device_name + "_v5v0", system_voltages.v5v0.toFixed(2).toString(), { qos: mqtt_data_qos });

                let chip_temperatures = await device.get_chip_temperatures();
                let system_temperatures = await device.get_system_temperatures();
                await mqtt_client.publish(mqtt_topic_prefix + "data/temperature/" + device_name + "_adc", chip_temperatures.adc.toFixed(2).toString(), { qos: mqtt_data_qos });
                await mqtt_client.publish(mqtt_topic_prefix + "data/temperature/" + device_name + "_emu", chip_temperatures.emu.toFixed(2).toString(), { qos: mqtt_data_qos });
                await mqtt_client.publish(mqtt_topic_prefix + "data/temperature/" + device_name + "_bias_reg", system_temperatures.bias_reg.toFixed(2).toString(), { qos: mqtt_data_qos });

                await mqtt_client.publish(mqtt_topic_prefix + "data/status/" + device_name + "_global_ref_enabled", (await device.get_lnb_global_reference_status()) ? "1" : "0", { qos: mqtt_data_qos });

                for(let i = 0; i < 2; i++)
                {
                    await mqtt_client.publish(mqtt_topic_prefix + "data/status/" + device_name + "_lnb" + i + "_bias", (await device.get_lnb_bias_status(i)) ? "1" : "0", { qos: mqtt_data_qos });
                    await mqtt_client.publish(mqtt_topic_prefix + "data/status/" + device_name + "_lnb" + i + "_bias_pgood", (await device.is_lnb_bias_power_good(i)) ? "1" : "0", { qos: mqtt_data_qos });
                    await mqtt_client.publish(mqtt_topic_prefix + "data/status/" + device_name + "_lnb" + i + "_ref", (await device.get_lnb_reference_status(i)) ? "1" : "0", { qos: mqtt_data_qos });
                    await mqtt_client.publish(mqtt_topic_prefix + "data/voltage/" + device_name + "_lnb" + i + "_bias_set", (await device.get_lnb_bias_voltage_set(i)).toFixed(2).toString(), { qos: mqtt_data_qos });
                    await mqtt_client.publish(mqtt_topic_prefix + "data/voltage/" + device_name + "_lnb" + i + "_bias", (await device.get_lnb_bias_voltage(i)).toFixed(2).toString(), { qos: mqtt_data_qos });
                    await mqtt_client.publish(mqtt_topic_prefix + "data/frequency/" + device_name + "_lnb" + i + "_ref", (await device.get_lnb_reference_frequency(i)).toFixed(2).toString(), { qos: mqtt_data_qos });
                }
            }
            else if(device instanceof DS18B20)
            {
                await device.measure();

                await mqtt_client.publish(mqtt_topic_prefix + "data/temperature/" + device_name, (await device.get_temperature()).toFixed(2).toString(), { qos: mqtt_data_qos });
            }
            else if(device instanceof BME280)
            {
                await mqtt_client.publish(mqtt_topic_prefix + "data/temperature/" + device_name, (await device.get_temperature()).toFixed(2).toString(), { qos: mqtt_data_qos });
                await mqtt_client.publish(mqtt_topic_prefix + "data/temperature/" + device_name + "_dew_point", (await device.get_dew_point()).toFixed(2).toString(), { qos: mqtt_data_qos });
                await mqtt_client.publish(mqtt_topic_prefix + "data/temperature/" + device_name + "_heat_index", (await device.get_heat_index()).toFixed(2).toString(), { qos: mqtt_data_qos });
                await mqtt_client.publish(mqtt_topic_prefix + "data/humidity/" + device_name, (await device.get_humidity()).toFixed(2).toString(), { qos: mqtt_data_qos });
                await mqtt_client.publish(mqtt_topic_prefix + "data/pressure/" + device_name, (await device.get_pressure()).toFixed(2).toString(), { qos: mqtt_data_qos });
                await mqtt_client.publish(mqtt_topic_prefix + "data/altitude/" + device_name, (await device.get_altitude()).toFixed(2).toString(), { qos: mqtt_data_qos });
            }
            else if(device instanceof OAQ)
            {
                let stable = await device.is_stable();

                if(!stable)
                    continue;

                await mqtt_client.publish(mqtt_topic_prefix + "data/air_quality/" + device_name + "_no2_conc", (await device.get_no2_concentration()).toFixed(2).toString(), { qos: mqtt_data_qos });
                await mqtt_client.publish(mqtt_topic_prefix + "data/air_quality/" + device_name + "_o3_conc", (await device.get_o3_concentration()).toFixed(2).toString(), { qos: mqtt_data_qos });
                await mqtt_client.publish(mqtt_topic_prefix + "data/air_quality/" + device_name + "_aqi", (await device.get_aqi()).toFixed(2).toString(), { qos: mqtt_data_qos });
            }
            else if(device instanceof SI1133)
            {
                await device.measure();

                await mqtt_client.publish(mqtt_topic_prefix + "data/light/" + device_name + "_visible", (await device.get_lux()).toFixed(2).toString(), { qos: mqtt_data_qos });
                await mqtt_client.publish(mqtt_topic_prefix + "data/light/" + device_name + "_uv_index", (await device.get_uv()).toFixed(2).toString(), { qos: mqtt_data_qos });
            }
            else if(device instanceof MCP3221)
            {
                await mqtt_client.publish(mqtt_topic_prefix + "data/voltage/" + device_name, (await device.get_voltage(1)).toFixed(2).toString(), { qos: mqtt_data_qos });
            }
            else if(device instanceof LTC5597)
            {
                await mqtt_client.publish(mqtt_topic_prefix + "data/rf_power/" + device_name, (await device.get_power_level(1, 1)).toFixed(2).toString(), { qos: mqtt_data_qos });
            }
            else if(device instanceof LTC4151)
            {
                // FIXME: It is possible for these to fail if the power rail is off, and it is not really an error...
                await mqtt_client.publish(mqtt_topic_prefix + "data/voltage/" + device_name + "_vin", (await device.get_vin_voltage(1)).toFixed(2).toString(), { qos: mqtt_data_qos });
                await mqtt_client.publish(mqtt_topic_prefix + "data/voltage/" + device_name + "_load", (await device.get_adin_voltage(1)).toFixed(2).toString(), { qos: mqtt_data_qos });
                await mqtt_client.publish(mqtt_topic_prefix + "data/current/" + device_name, (await device.get_current(1)).toFixed(2).toString(), { qos: mqtt_data_qos });
                await mqtt_client.publish(mqtt_topic_prefix + "data/power/" + device_name, (await device.get_power(1)).toFixed(2).toString(), { qos: mqtt_data_qos });
            }
            else if(device instanceof F2915)
            {
                await mqtt_client.publish(mqtt_topic_prefix + "data/status/" + device_name + "_powered", (await device.is_powered()) ? "1" : "0", { qos: mqtt_data_qos });
                await mqtt_client.publish(mqtt_topic_prefix + "data/status/" + device_name + "_selected_path", (await device.get_rf_path()).toString(), { qos: mqtt_data_qos });
            }
        }
        catch(e)
        {
            cl.tprintln("red", "MQTT", "Error publishing telemetry data for device \"" + device_name + "\": " + e);
        }
    }

    if(loop)
        setTimeout(mqtt_update_telemery, 60000, true); // Update every minute
}

async function ssh_server_init()
{
    ssh_server = new SSH2.Server(
        {
            hostKeys: [
                await FileSystem.promises.readFile(__dirname + "/keys/ssh_host_ecdsa_key"),
                await FileSystem.promises.readFile(__dirname + "/keys/ssh_host_ed25519_key"),
                await FileSystem.promises.readFile(__dirname + "/keys/ssh_host_rsa_key")
            ]
        },
        ssh_server_connection_handler
    );

    // Users
    ssh_server_add_user("joao", null, (await FileSystem.promises.readFile(__dirname + "/keys/users/joao.pub")).toString().split("\n"));
    ssh_server_add_user("root", null, (await FileSystem.promises.readFile(__dirname + "/keys/users/joao.pub")).toString().split("\n")); // Alias

    // Commands
    ssh_server_add_command(
        "help",
        "Prints this help information",
        async function (argv)
        {
            for(const cmd of Object.keys(ssh_commands))
                this.println(null, null, cmd + " - " + ssh_commands[cmd].description);

            return true;
        }
    );
    ssh_server_add_command(
        "me",
        "Prints your IP address",
        async function (argv)
        {
            this.println(null, null, "Your IP: " + this.stream.session.client.ip);
            this.println(null, null, "Your username: " + this.stream.session.client.auth.username);
            this.println(null, null, "Your auth method: " + this.stream.session.client.auth.method);

            return true;
        }
    );
    ssh_server_add_command(
        "echo",
        "Prints the first argument",
        async function (argv)
        {
            this.println(null, null, (argv.length > 1 ? argv[1] : ""));

            return true;
        }
    );
    ssh_server_add_command(
        "clear",
        "Clears the screen",
        async function (argv)
        {
            if(!this.stream.session.shell)
                throw new Error("Invalid shell");

            this.stream.session.shell.write(
                null,
                {
                    ctrl: true,
                    name: "l"
                }
            );

            return true;
        }
    );
    ssh_server_add_command(
        "rdev",
        "Read data from device specified in the first argument",
        async function (argv)
        {
            let device_param_name = argv[1];

            if(typeof(device_param_name) != "string")
                throw new Error("Invalid device parameter name");

            device_param_name = device_param_name.toLowerCase();

            let param_name_start = device_param_name.indexOf(".");

            if(param_name_start === 0)
                throw new Error("Invalid device parameter name");

            if(param_name_start == -1)
                param_name_start = device_param_name.length;

            let device_name = device_param_name.slice(0, param_name_start);
            let device = devices[device_name];

            if(!device)
                throw new Error("Device not found");

            let param_name = device_param_name.slice(param_name_start + 1);

            if(device instanceof HPPSU)
            {
                switch(param_name)
                {
                    case "":
                    {
                        this.tprintln(null, "HPPSU", "ID: 0x%s", (await device.get_id()).toString(16));
                        this.tprintln(null, "HPPSU", "SPN: %s", await device.get_spn());
                        this.tprintln(null, "HPPSU", "Date: %s", await device.get_date());
                        this.tprintln(null, "HPPSU", "Name: %s", await device.get_name());
                        this.tprintln(null, "HPPSU", "CT: %s", await device.get_ct());
                        this.tprintln(null, "HPPSU", "Input Present: %s", await device.is_input_present());
                        this.tprintln(null, "HPPSU", "Input Voltage: %d V (%d V nom.)", await device.get_input_voltage(), await device.get_nominal_input_voltage());
                        this.tprintln(null, "HPPSU", "Input Undervoltage threshold: %d V", await device.get_input_undervoltage_threshold());
                        this.tprintln(null, "HPPSU", "Input Overvoltage threshold: %d V", await device.get_input_overvoltage_threshold());
                        this.tprintln(null, "HPPSU", "Input Current: %d A (max. %d A)", await device.get_input_current(), await device.get_peak_input_current());
                        this.tprintln(null, "HPPSU", "Input Power: %d W (max. %d W)", await device.get_input_power(), await device.get_peak_input_power());
                        this.tprintln(null, "HPPSU", "Input Energy: %d Wh", await device.get_input_energy());
                        this.tprintln(null, "HPPSU", "Output Enabled: %s", await device.is_main_output_enabled());
                        this.tprintln(null, "HPPSU", "Output Voltage: %d V", await device.get_output_voltage());
                        this.tprintln(null, "HPPSU", "Output Undervoltage threshold: %d V", await device.get_output_undervoltage_threshold());
                        this.tprintln(null, "HPPSU", "Output Overvoltage threshold: %d V", await device.get_output_overvoltage_threshold());
                        this.tprintln(null, "HPPSU", "Output Current: %d A (max. %d A)", await device.get_output_current(), await device.get_peak_output_current());
                        this.tprintln(null, "HPPSU", "Output Power: %d W", await device.get_output_power());
                        this.tprintln(null, "HPPSU", "Efficiency: %d %%", (await device.get_efficiency() * 100));
                        this.tprintln(null, "HPPSU", "Intake Temperature: %d C", await device.get_intake_temperature());
                        this.tprintln(null, "HPPSU", "Internal Temperature: %d C", await device.get_internal_temperature());
                        this.tprintln(null, "HPPSU", "Fan speed: %d RPM", await device.get_fan_speed());
                        this.tprintln(null, "HPPSU", "Fan target speed: %d RPM", await device.get_fan_target_speed());
                        this.tprintln(null, "HPPSU", "On time: %d s", await device.get_on_time());
                        this.tprintln(null, "HPPSU", "Total on time: %d days", await device.get_total_on_time() / 60 / 24);
                        this.tprintln(null, "HPPSU", "Status flags: 0x%s", (await device.get_status_flags()).toString(16));
                    }
                    break;
                    case "info":
                    {
                        this.tprintln(null, "HPPSU", "ID: 0x%s", (await device.get_id()).toString(16));
                        this.tprintln(null, "HPPSU", "SPN: %s", await device.get_spn());
                        this.tprintln(null, "HPPSU", "Date: %s", await device.get_date());
                        this.tprintln(null, "HPPSU", "Name: %s", await device.get_name());
                        this.tprintln(null, "HPPSU", "CT: %s", await device.get_ct());
                    }
                    break;
                    case "status":
                    {
                        this.tprintln(null, "HPPSU", "Status flags: 0x%s", (await device.get_status_flags()).toString(16));
                        this.tprintln(null, "HPPSU", "Input Present: %s", await device.is_input_present());
                        this.tprintln(null, "HPPSU", "Output Enabled: %s", await device.is_main_output_enabled());
                    }
                    break;
                    case "input":
                    {
                        this.tprintln(null, "HPPSU", "Input Present: %s", await device.is_input_present());
                        this.tprintln(null, "HPPSU", "Input Voltage: %d V (%d V nom.)", await device.get_input_voltage(), await device.get_nominal_input_voltage());
                        this.tprintln(null, "HPPSU", "Input Undervoltage threshold: %d V", await device.get_input_undervoltage_threshold());
                        this.tprintln(null, "HPPSU", "Input Overvoltage threshold: %d V", await device.get_input_overvoltage_threshold());
                        this.tprintln(null, "HPPSU", "Input Current: %d A (max. %d A)", await device.get_input_current(), await device.get_peak_input_current());
                        this.tprintln(null, "HPPSU", "Input Power: %d W (max. %d W)", await device.get_input_power(), await device.get_peak_input_power());
                        this.tprintln(null, "HPPSU", "Input Energy: %d Wh", await device.get_input_energy());
                    }
                    break;
                    case "output":
                    {
                        this.tprintln(null, "HPPSU", "Output Enabled: %s", await device.is_main_output_enabled());
                        this.tprintln(null, "HPPSU", "Output Voltage: %d V", await device.get_output_voltage());
                        this.tprintln(null, "HPPSU", "Output Undervoltage threshold: %d V", await device.get_output_undervoltage_threshold());
                        this.tprintln(null, "HPPSU", "Output Overvoltage threshold: %d V", await device.get_output_overvoltage_threshold());
                        this.tprintln(null, "HPPSU", "Output Current: %d A (max. %d A)", await device.get_output_current(), await device.get_peak_output_current());
                        this.tprintln(null, "HPPSU", "Output Power: %d W", await device.get_output_power());
                        this.tprintln(null, "HPPSU", "Efficiency: %d %%", (await device.get_efficiency() * 100));
                    }
                    break;
                    case "temperature":
                    {
                        this.tprintln(null, "HPPSU", "Intake Temperature: %d C", await device.get_intake_temperature());
                        this.tprintln(null, "HPPSU", "Internal Temperature: %d C", await device.get_internal_temperature());
                    }
                    break;
                    case "fan_speed":
                    {
                        this.tprintln(null, "HPPSU", "Fan speed: %d RPM", await device.get_fan_speed());
                        this.tprintln(null, "HPPSU", "Fan target speed: %d RPM", await device.get_fan_target_speed());
                    }
                    break;
                    case "on_time":
                    {
                        this.tprintln(null, "HPPSU", "On time: %d s", await device.get_on_time());
                        this.tprintln(null, "HPPSU", "Total on time: %d days", await device.get_total_on_time() / 60 / 24);
                    }
                    break;
                    default:
                    {
                        throw new Error("PSU parameter not supported");
                    }
                    break;
                }
            }
            else if(device instanceof RelayController)
            {
                switch(param_name)
                {
                    case "":
                    {
                        this.tprintln(null, "Relay Controller", "Unique ID: %s", await device.get_unique_id());
                        this.tprintln(null, "Relay Controller", "Software Version: v%d", await device.get_software_version());
                        this.tprintln(null, "Relay Controller", "Uptime: %d s", await device.get_uptime());
                        this.tprintln(null, "Relay Controller", "Reset reason: %s", await device.get_reset_reason_str());

                        let chip_voltages = await device.get_chip_voltages();
                        this.tprintln(null, "Relay Controller", "AVDD Voltage: %d mV", chip_voltages.avdd);
                        this.tprintln(null, "Relay Controller", "DVDD Voltage: %d mV", chip_voltages.dvdd);
                        this.tprintln(null, "Relay Controller", "IOVDD Voltage: %d mV", chip_voltages.iovdd);
                        this.tprintln(null, "Relay Controller", "Core Voltage: %d mV", chip_voltages.core);

                        let system_voltages = await device.get_system_voltages();
                        this.tprintln(null, "Relay Controller", "VIN Voltage: %d mV", system_voltages.vin);

                        this.tprintln(null, "Relay Controller", "VIN Undervoltage monitor status: %s", (await device.get_relay_undervoltage_status()) ? "ON" : "OFF");
                        this.tprintln(null, "Relay Controller", "VIN Undervoltage threshold: %d mV", await device.get_relay_undervoltage_point());
                        this.tprintln(null, "Relay Controller", "VIN Undervoltage triggered: %s", (await device.was_relay_undervoltage_triggered()) ? "YES" : "NO");
                        this.tprintln(null, "Relay Controller", "VIN Undervoltage status: %s", (await device.is_relay_undervoltage()) ? "LOW" : "OK");

                        let chip_temperatures = await device.get_chip_temperatures();
                        this.tprintln(null, "Relay Controller", "ADC Temperature: %d C", chip_temperatures.adc);
                        this.tprintln(null, "Relay Controller", "EMU Temperature: %d C", chip_temperatures.emu);
                    }
                    break;
                    case "relay_status":
                    {
                        let i = parseInt(argv[2]);

                        if(isNaN(i) || i < 0 || i > 11)
                        {
                            this.tprintln(null, "Relay Controller", "Relays:");

                            let rstatus = await device.get_relay_status();

                            for(i = 0; i < 12; i++)
                            {
                                this.tprintln(null, "Relay Controller", "  Relay #%d status: %s", i, (rstatus & (1 << i)) ? "ON" : "OFF");
                                this.tprintln(null, "Relay Controller", "  Relay #%d duty cycle: %d %%", i, await device.get_relay_duty_cycle(i) * 100);
                                this.tprintln(null, "Relay Controller", "  Relay #%d voltage: %d mV", i, await device.get_relay_voltage(i));
                            }
                        }
                        else
                        {
                            this.tprintln(null, "Relay Controller", "Relay #%d status: %s", i, (await device.get_relay_status(i)) ? "ON" : "OFF");
                            this.tprintln(null, "Relay Controller", "Relay #%d duty cycle: %d %%", i, await device.get_relay_duty_cycle(i) * 100);
                            this.tprintln(null, "Relay Controller", "Relay #%d voltage: %d mV", i, await device.get_relay_voltage(i));
                        }
                    }
                    break;
                    default:
                    {
                        throw new Error("Relay Controller parameter not supported");
                    }
                    break;
                }
            }
            else if(device instanceof I2CBuffer)
            {
                switch(param_name)
                {
                    case "":
                    {
                        this.tprintln(null, "I2C Buffer", "Unique ID: %s", await device.get_unique_id());
                        this.tprintln(null, "I2C Buffer", "Software Version: v%d", await device.get_software_version());
                        this.tprintln(null, "I2C Buffer", "Uptime: %d s", await device.get_uptime());
                        this.tprintln(null, "I2C Buffer", "Reset reason: %s", await device.get_reset_reason_str());

                        let chip_voltages = await device.get_chip_voltages();
                        this.tprintln(null, "I2C Buffer", "AVDD Voltage: %d mV", chip_voltages.avdd);
                        this.tprintln(null, "I2C Buffer", "DVDD Voltage: %d mV", chip_voltages.dvdd);
                        this.tprintln(null, "I2C Buffer", "IOVDD Voltage: %d mV", chip_voltages.iovdd);
                        this.tprintln(null, "I2C Buffer", "Core Voltage: %d mV", chip_voltages.core);

                        let chip_temperatures = await device.get_chip_temperatures();
                        this.tprintln(null, "Relay Buffer", "ADC Temperature: %d C", chip_temperatures.adc);
                        this.tprintln(null, "Relay Buffer", "EMU Temperature: %d C", chip_temperatures.emu);
                    }
                    break;
                    case "bus_status":
                    {
                        let i = parseInt(argv[2]);

                        if(isNaN(i) || i < 0 || i > 11)
                        {
                            this.tprintln(null, "I2C Buffer", "Buses:");

                            let bstatus = await device.get_bus_status();

                            for(i = 0; i < 4; i++)
                            {
                                this.tprintln(null, "I2C Buffer", "  Bus #%d status: %s", i, (bstatus & (1 << i)) ? "ON" : "OFF");
                                this.tprintln(null, "I2C Buffer", "  Bus #%d bias status: %s", i, (bstatus & (1 << (i + 4))) ? "ON" : "OFF");
                                this.tprintln(null, "I2C Buffer", "  Bus #%d bias voltage: %d mV", i, await device.get_bus_bias_voltage(i));
                            }
                        }
                        else
                        {
                            this.tprintln(null, "I2C Buffer", "Bus #%d status: %s", i, (await device.get_bus_status(i)) ? "ON" : "OFF");
                            this.tprintln(null, "I2C Buffer", "Bus #%d bias status: %s", i, (await device.get_bus_bias_status(i)) ? "ON" : "OFF");
                            this.tprintln(null, "I2C Buffer", "Bus #%d bias voltage: %d mV", i, await device.get_bus_bias_voltage(i));
                        }
                    }
                    break;
                    default:
                    {
                        throw new Error("I2C Buffer parameter not supported");
                    }
                    break;
                }
            }
            else if(device instanceof Upconverter)
            {
                switch(param_name)
                {
                    case "":
                    {
                        this.tprintln(null, "Upconverter", "Unique ID: %s", await device.get_unique_id());
                        this.tprintln(null, "Upconverter", "Software Version: v%d", await device.get_software_version());
                        //this.tprintln(null, "Upconverter", "Uptime: %d s", await device.get_uptime());
                        //this.tprintln(null, "Upconverter", "Reset reason: %s", await device.get_reset_reason_str());

                        let chip_voltages = await device.get_chip_voltages();
                        this.tprintln(null, "Upconverter", "AVDD Voltage: %d mV", chip_voltages.avdd);
                        this.tprintln(null, "Upconverter", "DVDD Voltage: %d mV", chip_voltages.dvdd);
                        this.tprintln(null, "Upconverter", "IOVDD Voltage: %d mV", chip_voltages.iovdd);
                        this.tprintln(null, "Upconverter", "Core Voltage: %d mV", chip_voltages.core);

                        let system_voltages = await device.get_system_voltages();
                        this.tprintln(null, "Upconverter", "VIN Voltage: %d mV", system_voltages.vin);
                        this.tprintln(null, "Upconverter", "5V0 Voltage: %d mV", system_voltages.v5v0);

                        let system_currents = await device.get_system_currents();
                        this.tprintln(null, "Upconverter", "5V0 Current: %d mA", system_currents.i5v0);

                        let chip_temperatures = await device.get_chip_temperatures();
                        this.tprintln(null, "Upconverter", "ADC Temperature: %d C", chip_temperatures.adc);
                        this.tprintln(null, "Upconverter", "EMU Temperature: %d C", chip_temperatures.emu);

                        this.tprintln(null, "Upconverter", "RF power: %d dBm", await device.get_rf_power());
                        this.tprintln(null, "Upconverter", "RF power modulation: %s", Upconverter.get_modulation_name(await device.get_rf_power_modulation()));

                        this.tprintln(null, "Upconverter", "RF Low power monitor status: %s", (await device.get_low_rf_power_status()) ? "ON" : "OFF");
                        this.tprintln(null, "Upconverter", "RF Low power threshold: %d dBm", await device.get_low_rf_power_threshold());
                        this.tprintln(null, "Upconverter", "RF Low power triggered: %s", (await device.was_low_rf_power_triggered()) ? "YES" : "NO");
                        this.tprintln(null, "Upconverter", "RF Low power status: %s", (await device.is_low_rf_power()) ? "LOW" : "OK");

                        this.tprintln(null, "Upconverter", "IF Attenuation: %d dB", await device.get_if_attenuation());
                        this.tprintln(null, "Upconverter", "RF1 Attenuation: %d dB", await device.get_rf1_attenuation());
                        this.tprintln(null, "Upconverter", "RF2 Attenuation: %d dB", await device.get_rf2_attenuation());

                        this.tprintln(null, "Upconverter", "LO Frequency: %d MHz", Number((await device.get_lo_frequency()) / 1000000n));
                        this.tprintln(null, "Upconverter", "LO Reference Frequency: %d MHz", (await device.get_lo_ref_frequency()) / 1000000);
                        this.tprintln(null, "Upconverter", "LO PFD Frequency: %d MHz", (await device.get_lo_pfd_frequency()) / 1000000);
                        this.tprintln(null, "Upconverter", "LO Locked: %s", (await device.is_lo_pll_locked()) ? "YES" : "NO");
                        this.tprintln(null, "Upconverter", "LO Muted: %s", (await device.is_lo_pll_muted()) ? "YES" : "NO");

                        this.tprintln(null, "Upconverter", "Mixer Enabled: %s", (await device.get_mixer_status()) ? "YES" : "NO");
                        this.tprintln(null, "Upconverter", "Pre-Amplifiers Enabled: %s", (await device.get_pa_stg1_2_status()) ? "YES" : "NO");
                        this.tprintln(null, "Upconverter", "Final Amplifier Enabled: %s", (await device.get_pa_stg3_status()) ? "YES" : "NO");
                    }
                    break;
                    case "rf_power":
                    {
                        this.tprintln(null, "Upconverter", "RF power: %d dBm", await device.get_rf_power());
                        this.tprintln(null, "Upconverter", "RF power modulation: %s", Upconverter.get_modulation_name(await device.get_rf_power_modulation()));

                        this.tprintln(null, "Upconverter", "RF Low power monitor status: %s", (await device.get_low_rf_power_status()) ? "ON" : "OFF");
                        this.tprintln(null, "Upconverter", "RF Low power threshold: %d dBm", await device.get_low_rf_power_threshold());
                        this.tprintln(null, "Upconverter", "RF Low power triggered: %s", (await device.was_low_rf_power_triggered()) ? "YES" : "NO");
                        this.tprintln(null, "Upconverter", "RF Low power status: %s", (await device.is_low_rf_power()) ? "LOW" : "OK");
                    }
                    break;
                    case "attenuators":
                    {
                        this.tprintln(null, "Upconverter", "IF Attenuation: %d dB", await device.get_if_attenuation());
                        this.tprintln(null, "Upconverter", "RF1 Attenuation: %d dB", await device.get_rf1_attenuation());
                        this.tprintln(null, "Upconverter", "RF2 Attenuation: %d dB", await device.get_rf2_attenuation());
                    }
                    break;
                    case "lo":
                    {
                        this.tprintln(null, "Upconverter", "LO Frequency: %d MHz", Number((await device.get_lo_frequency()) / 1000000n));
                        this.tprintln(null, "Upconverter", "LO Reference Frequency: %d MHz", (await device.get_lo_ref_frequency()) / 1000000);
                        this.tprintln(null, "Upconverter", "LO PFD Frequency: %d MHz", (await device.get_lo_pfd_frequency()) / 1000000);
                        this.tprintln(null, "Upconverter", "LO Locked: %s", (await device.is_lo_pll_locked()) ? "YES" : "NO");
                        this.tprintln(null, "Upconverter", "LO Muted: %s", (await device.is_lo_pll_muted()) ? "YES" : "NO");
                    }
                    break;
                    case "mixer":
                    {
                        this.tprintln(null, "Upconverter", "Mixer Enabled: %s", (await device.get_mixer_status()) ? "YES" : "NO");
                    }
                    break;
                    case "amplifiers":
                    {
                        this.tprintln(null, "Upconverter", "Pre-Amplifiers Enabled: %s", (await device.get_pa_stg1_2_status()) ? "YES" : "NO");
                        this.tprintln(null, "Upconverter", "Final Amplifier Enabled: %s", (await device.get_pa_stg3_status()) ? "YES" : "NO");
                    }
                    break;
                    default:
                    {
                        throw new Error("Upconverter parameter not supported");
                    }
                    break;
                }
            }
            else if(device instanceof PABiasController)
            {
                switch(param_name)
                {
                    case "":
                    {
                        this.tprintln(null, "PA Bias Controller", "Unique ID: %s", await device.get_unique_id());
                        this.tprintln(null, "PA Bias Controller", "Software Version: v%d", await device.get_software_version());
                        this.tprintln(null, "PA Bias Controller", "Uptime: %d s", await device.get_uptime());
                        this.tprintln(null, "PA Bias Controller", "Reset reason: %s", await device.get_reset_reason_str());

                        let chip_voltages = await device.get_chip_voltages();
                        this.tprintln(null, "PA Bias Controller", "AVDD Voltage: %d mV", chip_voltages.avdd);
                        this.tprintln(null, "PA Bias Controller", "DVDD Voltage: %d mV", chip_voltages.dvdd);
                        this.tprintln(null, "PA Bias Controller", "IOVDD Voltage: %d mV", chip_voltages.iovdd);
                        this.tprintln(null, "PA Bias Controller", "Core Voltage: %d mV", chip_voltages.core);

                        let system_voltages = await device.get_system_voltages();
                        this.tprintln(null, "PA Bias Controller", "VIN Voltage: %d mV", system_voltages.vin);
                        this.tprintln(null, "PA Bias Controller", "5V0 Voltage: %d mV", system_voltages.v5v0);

                        let chip_temperatures = await device.get_chip_temperatures();
                        this.tprintln(null, "PA Bias Controller", "ADC Temperature: %d C", chip_temperatures.adc);
                        this.tprintln(null, "PA Bias Controller", "EMU Temperature: %d C", chip_temperatures.emu);

                        let system_temperatures = await device.get_system_temperatures();
                        this.tprintln(null, "PA Bias Controller", "AFE Temperature: %d C", system_temperatures.afe);

                        let tec_dac_init = await device.get_tec_dac_status();

                        this.tprintln(tec_dac_init ? null : "yellow", "PA Bias Controller", "TEC DAC init status: %s", tec_dac_init ? "OK" : "FAULTY");
                    }
                    break;
                    case "tec_status":
                    {
                        let i = parseInt(argv[2]);

                        if(isNaN(i) || i < 0 || i > 3)
                        {
                            this.tprintln(null, "PA Bias Controller", "TECs:");

                            for(i = 0; i < 4; i++)
                            {
                                this.tprintln(null, "PA Bias Controller", "  TEC #%d status: %s", i, (await device.get_tec_status(i)) ? "ON" : "OFF");
                                this.tprintln(null, "PA Bias Controller", "  TEC #%d voltage: %d mV", i, await device.get_tec_voltage(i));
                            }
                        }
                        else
                        {
                            this.tprintln(null, "PA Bias Controller", "TEC #%d status: %s", i, (await device.get_tec_status(i)) ? "ON" : "OFF");
                            this.tprintln(null, "PA Bias Controller", "TEC #%d voltage: %d mV", i, await device.get_tec_voltage(i));
                        }
                    }
                    break;
                    case "pa_status":
                    {
                        let i = parseInt(argv[2]);

                        if(isNaN(i) || i < 0 || i > 1)
                        {
                            this.tprintln(null, "PA Bias Controller", "PAs:");

                            for(i = 0; i < 2; i++)
                            {
                                let data = await device.get_pa_telemetry(i);

                                this.tprintln(null, "PA Bias Controller", "  PA #%d status: %s", i, (await device.get_pa_status(i)) ? "ON" : "OFF");
                                this.tprintln(null, "PA Bias Controller", "  PA #%d VGG Raw Voltage: %d mV", i, data.vgg_raw);
                                this.tprintln(null, "PA Bias Controller", "  PA #%d VGG Voltage: %d mV", i, data.vgg);
                                this.tprintln(null, "PA Bias Controller", "  PA #%d VDD Voltage: %d mV", i, data.vdd);
                                this.tprintln(null, "PA Bias Controller", "  PA #%d VDD Current: %d mA", i, data.idd);
                                this.tprintln(null, "PA Bias Controller", "  PA #%d Temperature: %d C", i, data.temperature);
                                this.tprintln(null, "PA Bias Controller", "  PA #%d High Temperature: %d C", i, data.temperature_high);
                                this.tprintln(null, "PA Bias Controller", "  PA #%d High Temperature triggered: %s", i, (await device.was_pa_high_temperature_triggered(i)) ? "YES" : "NO");
                                this.tprintln(null, "PA Bias Controller", "  PA #%d High Temperature status: %s", i, (await device.is_pa_high_temperature(i)) ? "HIGH" : "OK");
                                this.tprintln(null, "PA Bias Controller", "  PA #%d Low Temperature: %d C", i, data.temperature_low);
                                this.tprintln(null, "PA Bias Controller", "  PA #%d Low Temperature triggered: %s", i, (await device.was_pa_low_temperature_triggered(i)) ? "YES" : "NO");
                                this.tprintln(null, "PA Bias Controller", "  PA #%d Low Temperature status: %s", i, (await device.is_pa_low_temperature(i)) ? "LOW" : "OK");
                            }
                        }
                        else
                        {
                            let data = await device.get_pa_telemetry(i);

                            this.tprintln(null, "PA Bias Controller", "PA #%d status: %s", i, (await device.get_pa_status(i)) ? "ON" : "OFF");
                            this.tprintln(null, "PA Bias Controller", "PA #%d VGG Raw Voltage: %d mV", i, data.vgg_raw);
                            this.tprintln(null, "PA Bias Controller", "PA #%d VGG Voltage: %d mV", i, data.vgg);
                            this.tprintln(null, "PA Bias Controller", "PA #%d VDD Voltage: %d mV", i, data.vdd);
                            this.tprintln(null, "PA Bias Controller", "PA #%d VDD Current: %d mA", i, data.idd);
                            this.tprintln(null, "PA Bias Controller", "PA #%d Temperature: %d C", i, data.temperature);
                            this.tprintln(null, "PA Bias Controller", "PA #%d High Temperature: %d C", i, data.temperature_high);
                            this.tprintln(null, "PA Bias Controller", "PA #%d High Temperature triggered: %s", i, (await device.was_pa_high_temperature_triggered(i)) ? "YES" : "NO");
                            this.tprintln(null, "PA Bias Controller", "PA #%d High Temperature status: %s", i, (await device.is_pa_high_temperature(i)) ? "HIGH" : "OK");
                            this.tprintln(null, "PA Bias Controller", "PA #%d Low Temperature: %d C", i, data.temperature_low);
                            this.tprintln(null, "PA Bias Controller", "PA #%d Low Temperature triggered: %s", i, (await device.was_pa_low_temperature_triggered(i)) ? "YES" : "NO");
                            this.tprintln(null, "PA Bias Controller", "PA #%d Low Temperature status: %s", i, (await device.is_pa_low_temperature(i)) ? "LOW" : "OK");
                        }
                    }
                    break;
                    default:
                    {
                        throw new Error("PA Bias Controller parameter not supported");
                    }
                    break;
                }
            }
            else if(device instanceof LNBController)
            {
                switch(param_name)
                {
                    case "":
                    {
                        this.tprintln(null, "LNB Controller", "Unique ID: %s", await device.get_unique_id());
                        this.tprintln(null, "LNB Controller", "Software Version: v%d", await device.get_software_version());
                        this.tprintln(null, "LNB Controller", "Uptime: %d s", await device.get_uptime());
                        this.tprintln(null, "LNB Controller", "Reset reason: %s", await device.get_reset_reason_str());

                        let chip_voltages = await device.get_chip_voltages();
                        this.tprintln(null, "LNB Controller", "AVDD Voltage: %d mV", chip_voltages.avdd);
                        this.tprintln(null, "LNB Controller", "DVDD Voltage: %d mV", chip_voltages.dvdd);
                        this.tprintln(null, "LNB Controller", "IOVDD Voltage: %d mV", chip_voltages.iovdd);
                        this.tprintln(null, "LNB Controller", "Core Voltage: %d mV", chip_voltages.core);

                        let system_voltages = await device.get_system_voltages();
                        this.tprintln(null, "LNB Controller", "VIN Voltage: %d mV", system_voltages.vin);
                        this.tprintln(null, "LNB Controller", "5V0 Voltage: %d mV", system_voltages.v5v0);

                        let chip_temperatures = await device.get_chip_temperatures();
                        this.tprintln(null, "LNB Controller", "ADC Temperature: %d C", chip_temperatures.adc);
                        this.tprintln(null, "LNB Controller", "EMU Temperature: %d C", chip_temperatures.emu);

                        let system_temperatures = await device.get_system_temperatures();
                        this.tprintln(null, "LNB Controller", "Bias Regulator Temperature: %d C", system_temperatures.bias_reg);

                        this.tprintln(null, "LNB Controller", "Global reference enable: %s", (await device.get_lnb_global_reference_status()) ? "ON" : "OFF");
                    }
                    break;
                    case "lnb_status":
                    {
                        let i = parseInt(argv[2]);

                        if(isNaN(i) || i < 0 || i > 1)
                        {
                            this.tprintln(null, "LNB Controller", "LNBs:");

                            for(i = 0; i < 2; i++)
                            {
                                this.tprintln(null, "LNB Controller", "  LNB #%d Bias enable: %s", i, (await device.get_lnb_bias_status(i)) ? "ON" : "OFF");
                                this.tprintln(null, "LNB Controller", "  LNB #%d Bias status: %s", i, (await device.is_lnb_bias_power_good(i)) ? "POWER GOOD" : "POWER NOT GOOD");
                                this.tprintln(null, "LNB Controller", "  LNB #%d Set Bias Voltage: %d mV", i, await device.get_lnb_bias_voltage_set(i));
                                this.tprintln(null, "LNB Controller", "  LNB #%d Bias Voltage: %d mV", i, await device.get_lnb_bias_voltage(i));
                                this.tprintln(null, "LNB Controller", "  LNB #%d Reference enable: %s", i, (await device.get_lnb_reference_status(i)) ? "ON" : "OFF");
                                this.tprintln(null, "LNB Controller", "  LNB #%d Reference Frequency: %d Hz", i, await device.get_lnb_reference_frequency(i));
                            }
                        }
                        else
                        {
                            this.tprintln(null, "LNB Controller", "LNB #%d Bias enable: %s", i, (await device.get_lnb_bias_status(i)) ? "ON" : "OFF");
                            this.tprintln(null, "LNB Controller", "LNB #%d Bias status: %s", i, (await device.is_lnb_bias_power_good(i)) ? "POWER GOOD" : "POWER NOT GOOD");
                            this.tprintln(null, "LNB Controller", "LNB #%d Set Bias Voltage: %d mV", i, await device.get_lnb_bias_voltage_set(i));
                            this.tprintln(null, "LNB Controller", "LNB #%d Bias Voltage: %d mV", i, await device.get_lnb_bias_voltage(i));
                            this.tprintln(null, "LNB Controller", "LNB #%d Reference enable: %s", i, (await device.get_lnb_reference_status(i)) ? "ON" : "OFF");
                            this.tprintln(null, "LNB Controller", "LNB #%d Reference Frequency: %d Hz", i, await device.get_lnb_reference_frequency(i));
                        }
                    }
                    break;
                    default:
                    {
                        throw new Error("LNB Controller parameter not supported");
                    }
                    break;
                }
            }
            else if(device instanceof DS18B20)
            {
                await device.measure();

                switch(param_name)
                {
                    case "":
                    {
                        this.tprintln(null, "DS18B20", "Temperature: %d C", await device.get_temperature());
                        this.tprintln(null, "DS18B20", "High Alarm Temperature: %d C", (await device.get_alarm()).high);
                        this.tprintln(null, "DS18B20", "Low Alarm Temperature: %d C", (await device.get_alarm()).low);
                        this.tprintln(null, "DS18B20", "Parasidic powered: %s", await device.is_parasidic_power());
                    }
                    break;
                    default:
                    {
                        throw new Error("DS18B20 parameter not supported");
                    }
                    break;
                }
            }
            else if(device instanceof BME280)
            {
                switch(param_name)
                {
                    case "":
                    {
                        this.tprintln(null, "BME280", "Temperature: %d C", await device.get_temperature());
                        this.tprintln(null, "BME280", "Humidity: %d %%RH", await device.get_humidity());
                        this.tprintln(null, "BME280", "Pressure: %d hPa", await device.get_pressure());
                        this.tprintln(null, "BME280", "Dew point: %d C", await device.get_dew_point());
                        this.tprintln(null, "BME280", "Heat index: %d C", await device.get_heat_index());
                        this.tprintln(null, "BME280", "Altitude: %d m", await device.get_altitude());
                    }
                    break;
                    default:
                    {
                        throw new Error("BME280 parameter not supported");
                    }
                    break;
                }
            }
            else if(device instanceof OAQ)
            {
                switch(param_name)
                {
                    case "":
                    {
                        let stable = await device.is_stable();

                        if(!stable)
                        {
                            this.tprintln("yellow", "OAQ (ZMOD4510)", "Sensor not yet stable!");
                        }
                        else
                        {
                            this.tprintln(null, "OAQ (ZMOD4510)", "NO2 concentration: %d", await device.get_no2_concentration());
                            this.tprintln(null, "OAQ (ZMOD4510)", "O3 concentration: %d", await device.get_o3_concentration());
                            this.tprintln(null, "OAQ (ZMOD4510)", "Air Quality Index: %d (%s)", await device.get_aqi(), await device.get_loc());
                        }
                    }
                    break;
                    default:
                    {
                        throw new Error("OAQ parameter not supported");
                    }
                    break;
                }
            }
            else if(device instanceof SI1133)
            {
                switch(param_name)
                {
                    case "":
                    {
                        await device.measure();

                        this.tprintln(null, "SI1133", "Visible light: %d Lux", await device.get_lux());
                        this.tprintln(null, "SI1133", "UV Index: %d", await device.get_uv());
                    }
                    break;
                    default:
                    {
                        throw new Error("SI1133 parameter not supported");
                    }
                    break;
                }
            }
            else if(device instanceof MCP3221)
            {
                switch(param_name)
                {
                    case "":
                    {
                        let samples = argv[2] || 1;

                        this.tprintln(null, "MCP3221", "Voltage: %d mV", await device.get_voltage(samples));
                    }
                    break;
                    default:
                    {
                        throw new Error("MCP3221 parameter not supported");
                    }
                    break;
                }
            }
            else if(device instanceof LTC5597)
            {
                switch(param_name)
                {
                    case "":
                    {
                        let samples = argv[2] || 1;
                        let gain = argv[3] || 1;

                        this.tprintln(null, "LTC5597", "Power: %d dBm", await device.get_power_level(gain, samples));
                    }
                    break;
                    default:
                    {
                        throw new Error("LTC5597 parameter not supported");
                    }
                    break;
                }
            }
            else if(device instanceof LTC4151)
            {
                switch(param_name)
                {
                    case "":
                    {
                        let samples = argv[2] || 1;

                        this.tprintln(null, "LTC4151", "VIN Voltage: %d mV", await device.get_vin_voltage(samples));
                        this.tprintln(null, "LTC4151", "Load Voltage: %d mV", await device.get_adin_voltage(samples));
                        this.tprintln(null, "LTC4151", "Load Current: %d mA", await device.get_current(samples));
                    }
                    break;
                    default:
                    {
                        throw new Error("LTC4151 parameter not supported");
                    }
                    break;
                }
            }
            else if(device instanceof F2915)
            {
                switch(param_name)
                {
                    case "":
                    {
                        this.tprintln(null, "F2915", "Powered: %s", await device.is_powered());
                        this.tprintln(null, "F2915", "Selected RF path: %d", await device.get_rf_path());
                    }
                    break;
                    default:
                    {
                        throw new Error("F2915 parameter not supported");
                    }
                    break;
                }
            }
            else
            {
                throw new Error("Device not supported");
            }

            return true;
        },
        function (line)
        {
            const param_names = [];

            for(const device_name in devices)
            {
                const device = devices[device_name];

                param_names.push(device_name);

                let device_param_names = [];

                if(device instanceof HPPSU)
                    device_param_names = ["info", "status", "input", "output", "temperature", "fan_speed", "on_time"];
                else if(device instanceof RelayController)
                    device_param_names = ["relay_status"];
                else if(device instanceof I2CBuffer)
                    device_param_names = ["bus_status"];
                else if(device instanceof Upconverter)
                    device_param_names = ["rf_power", "attenuators", "lo", "mixer", "amplifiers"];
                else if(device instanceof PABiasController)
                    device_param_names = ["tec_status", "pa_status"];
                else if(device instanceof LNBController)
                    device_param_names = ["lnb_status"];
                else if(device instanceof DS18B20)
                    device_param_names = [];
                else if(device instanceof BME280)
                    device_param_names = [];
                else if(device instanceof OAQ)
                    device_param_names = [];
                else if(device instanceof SI1133)
                    device_param_names = [];
                else if(device instanceof MCP3221)
                    device_param_names = [];
                else if(device instanceof LTC5597)
                    device_param_names = [];
                else if(device instanceof LTC4151)
                    device_param_names = [];
                else if(device instanceof F2915)
                    device_param_names = [];

                for(const param of device_param_names)
                    param_names.push(device_name + "." + param);
            }

            const hits = param_names.filter(
                function (c)
                {
                    return c.startsWith(line);
                }
            );

            return hits.length ? hits : param_names;
        }
    );
    ssh_server_add_command(
        "wdev",
        "Modify parameters of the device specified in the first argument",
        async function (argv)
        {
            let device_param_name = argv[1];

            if(typeof(device_param_name) != "string")
                throw new Error("Invalid device parameter name");

            device_param_name = device_param_name.toLowerCase();

            let param_name_start = device_param_name.indexOf(".");

            if(param_name_start === 0)
                throw new Error("Invalid device parameter name");

            if(param_name_start == -1)
                param_name_start = device_param_name.length;

            let device_name = device_param_name.slice(0, param_name_start);
            let device = devices[device_name];

            if(!device)
                throw new Error("Device not found");

            let param_name = device_param_name.slice(param_name_start + 1);

            if(device instanceof HPPSU)
            {
                switch(param_name)
                {
                    case "clear_peak_input_current":
                    {
                        await device.clear_peak_input_current();

                        this.tprintln(null, "HPPSU", "Peak Input Current: %d A", await device.get_peak_input_current());
                    }
                    break;
                    case "clear_peak_input_power":
                    {
                        await device.clear_peak_input_power();

                        this.tprintln(null, "HPPSU", "Peak Input Power: %d W", await device.get_peak_input_power());
                    }
                    break;
                    case "clear_peak_output_current":
                    {
                        await device.clear_peak_output_current();

                        this.tprintln(null, "HPPSU", "Peak Output Current: %d A", await device.get_peak_output_current());
                    }
                    break;
                    case "fan_speed":
                    {
                        let speed = parseInt(argv[2]);

                        await device.set_fan_target_speed(speed);

                        this.tprintln(null, "HPPSU", "Fan speed: %d RPM", await device.get_fan_speed());
                        this.tprintln(null, "HPPSU", "Fan target speed: %d RPM", await device.get_fan_target_speed());
                    }
                    break;
                    case "clear_on_time_and_energy":
                    {
                        await device.clear_on_time_and_energy();

                        this.tprintln(null, "HPPSU", "On time: %d s", await device.get_on_time());
                    }
                    break;
                    case "turn_on":
                    {
                        await device.set_enable(true);
                        await delay(100);

                        this.tprintln(null, "HPPSU", "Output Enabled: %s", await device.is_main_output_enabled());
                    }
                    break;
                    case "turn_off":
                    {
                        await device.set_enable(false);
                        await delay(100);

                        this.tprintln(null, "HPPSU", "Output Enabled: %s", await device.is_main_output_enabled());
                    }
                    break;
                    default:
                    {
                        throw new Error("PSU parameter not supported");
                    }
                    break;
                }
            }
            else if(device instanceof RelayController)
            {
                switch(param_name)
                {
                    case "turn_relay_on":
                    {
                        let i = parseInt(argv[2]);

                        if(isNaN(i) || i < 0 || i > 11)
                            throw new Error("Invalid relay index");

                        await device.set_relay_status(i, true);

                        await delay(50);

                        this.tprintln(null, "Relay Controller", "Relay #%d status: %s", i, (await device.get_relay_status(i)) ? "ON" : "OFF");
                        this.tprintln(null, "Relay Controller", "Relay #%d duty cycle: %d %%", i, await device.get_relay_duty_cycle(i) * 100);
                        this.tprintln(null, "Relay Controller", "Relay #%d voltage: %d mV", i, await device.get_relay_voltage(i));
                    }
                    break;
                    case "turn_relay_off":
                    {
                        let i = parseInt(argv[2]);

                        if(isNaN(i) || i < 0 || i > 11)
                            throw new Error("Invalid relay index");

                        await device.set_relay_status(i, false);

                        await delay(50);

                        this.tprintln(null, "Relay Controller", "Relay #%d status: %s", i, (await device.get_relay_status(i)) ? "ON" : "OFF");
                        this.tprintln(null, "Relay Controller", "Relay #%d duty cycle: %d %%", i, await device.get_relay_duty_cycle(i) * 100);
                        this.tprintln(null, "Relay Controller", "Relay #%d voltage: %d mV", i, await device.get_relay_voltage(i));
                    }
                    break;
                    case "set_relay_voltage":
                    {
                        let i = parseInt(argv[2]);

                        if(isNaN(i) || i < 0 || i > 11)
                            throw new Error("Invalid relay index");

                        let voltage = parseInt(argv[3]);

                        if(isNaN(voltage))
                            throw new Error("Invalid voltage");

                        await device.set_relay_voltage(i, voltage);

                        await delay(50);

                        this.tprintln(null, "Relay Controller", "Relay #%d status: %s", i, (await device.get_relay_status(i)) ? "ON" : "OFF");
                        this.tprintln(null, "Relay Controller", "Relay #%d duty cycle: %d %%", i, await device.get_relay_duty_cycle(i) * 100);
                        this.tprintln(null, "Relay Controller", "Relay #%d voltage: %d mV", i, await device.get_relay_voltage(i));
                    }
                    break;
                    default:
                    {
                        throw new Error("Relay Controller parameter not supported");
                    }
                    break;
                }
            }
            else if(device instanceof I2CBuffer)
            {
                switch(param_name)
                {
                    case "turn_bus_on":
                    {
                        let i = parseInt(argv[2]);

                        if(isNaN(i) || i < 0 || i > 3)
                            throw new Error("Invalid bus index");

                        await device.set_bus_status(i, true);

                        await delay(50);

                        this.tprintln(null, "I2C Buffer", "Bus #%d status: %s", i, (await device.get_bus_status(i)) ? "ON" : "OFF");
                        this.tprintln(null, "I2C Buffer", "Bus #%d bias status: %s", i, (await device.get_bus_bias_status(i)) ? "ON" : "OFF");
                        this.tprintln(null, "I2C Buffer", "Bus #%d bias voltage: %d mV", i, await device.get_bus_bias_voltage(i));
                    }
                    break;
                    case "turn_bus_off":
                    {
                        let i = parseInt(argv[2]);

                        if(isNaN(i) || i < 0 || i > 3)
                            throw new Error("Invalid bus index");

                        await device.set_bus_status(i, false);

                        await delay(50);

                        this.tprintln(null, "I2C Buffer", "Bus #%d status: %s", i, (await device.get_bus_status(i)) ? "ON" : "OFF");
                        this.tprintln(null, "I2C Buffer", "Bus #%d bias status: %s", i, (await device.get_bus_bias_status(i)) ? "ON" : "OFF");
                        this.tprintln(null, "I2C Buffer", "Bus #%d bias voltage: %d mV", i, await device.get_bus_bias_voltage(i));
                    }
                    break;
                    default:
                    {
                        throw new Error("I2C Buffer parameter not supported");
                    }
                    break;
                }
            }
            else if(device instanceof Upconverter)
            {
                switch(param_name)
                {
                    case "set_attenuation":
                    {
                        let att_name = argv[2];

                        if(typeof(att_name) != "string")
                            throw new Error("Invalid attenuator");

                        let att = parseInt(argv[3]);

                        if(isNaN(att))
                            throw new Error("Invalid attenuation");

                        att_name = att_name.toLowerCase();

                        if(att_name == "if")
                            await device.set_if_attenuation(att);
                        else if(att_name == "rf1")
                            await device.set_rf1_attenuation(att);
                        else if(att_name == "rf2")
                            await device.set_rf2_attenuation(att);
                        else
                            throw new Error("Invalid attenuator");

                        await delay(500);

                        this.tprintln(null, "Upconverter", "IF Attenuation: %d dB", await device.get_if_attenuation());
                        this.tprintln(null, "Upconverter", "RF1 Attenuation: %d dB", await device.get_rf1_attenuation());
                        this.tprintln(null, "Upconverter", "RF2 Attenuation: %d dB", await device.get_rf2_attenuation());
                    }
                    break;
                    case "mute_lo":
                    {
                        await device.set_lo_pll_muted(true);

                        await delay(50);

                        this.tprintln(null, "Upconverter", "LO Frequency: %d MHz", Number((await device.get_lo_frequency()) / 1000000n));
                        this.tprintln(null, "Upconverter", "LO Reference Frequency: %d MHz", (await device.get_lo_ref_frequency()) / 1000000);
                        this.tprintln(null, "Upconverter", "LO PFD Frequency: %d MHz", (await device.get_lo_pfd_frequency()) / 1000000);
                        this.tprintln(null, "Upconverter", "LO Locked: %s", (await device.is_lo_pll_locked()) ? "YES" : "NO");
                        this.tprintln(null, "Upconverter", "LO Muted: %s", (await device.is_lo_pll_muted()) ? "YES" : "NO");
                    }
                    break;
                    case "unmute_lo":
                    {
                        await device.set_lo_pll_muted(false);

                        await delay(50);

                        this.tprintln(null, "Upconverter", "LO Frequency: %d MHz", Number((await device.get_lo_frequency()) / 1000000n));
                        this.tprintln(null, "Upconverter", "LO Reference Frequency: %d MHz", (await device.get_lo_ref_frequency()) / 1000000);
                        this.tprintln(null, "Upconverter", "LO PFD Frequency: %d MHz", (await device.get_lo_pfd_frequency()) / 1000000);
                        this.tprintln(null, "Upconverter", "LO Locked: %s", (await device.is_lo_pll_locked()) ? "YES" : "NO");
                        this.tprintln(null, "Upconverter", "LO Muted: %s", (await device.is_lo_pll_muted()) ? "YES" : "NO");
                    }
                    break;
                    case "set_lo_freq":
                    {
                        let freq = BigInt(argv[2]);

                        if(isNaN(Number(freq)))
                            throw new Error("Invalid frequency");

                        await device.set_lo_frequency(freq);

                        await delay(500);

                        this.tprintln(null, "Upconverter", "LO Frequency: %d MHz", Number((await device.get_lo_frequency()) / 1000000n));
                        this.tprintln(null, "Upconverter", "LO Reference Frequency: %d MHz", (await device.get_lo_ref_frequency()) / 1000000);
                        this.tprintln(null, "Upconverter", "LO PFD Frequency: %d MHz", (await device.get_lo_pfd_frequency()) / 1000000);
                        this.tprintln(null, "Upconverter", "LO Locked: %s", (await device.is_lo_pll_locked()) ? "YES" : "NO");
                        this.tprintln(null, "Upconverter", "LO Muted: %s", (await device.is_lo_pll_muted()) ? "YES" : "NO");
                    }
                    break;
                    case "turn_mixer_on":
                    {
                        await device.set_mixer_status(true);

                        await delay(50);

                        this.tprintln(null, "Upconverter", "Mixer Enabled: %s", (await device.get_mixer_status()) ? "YES" : "NO");
                    }
                    break;
                    case "turn_mixer_off":
                    {
                        await device.set_mixer_status(false);

                        await delay(50);

                        this.tprintln(null, "Upconverter", "Mixer Enabled: %s", (await device.get_mixer_status()) ? "YES" : "NO");
                    }
                    break;
                    case "turn_preamps_on":
                    {
                        await device.set_pa_stg1_2_status(true);

                        await delay(50);

                        this.tprintln(null, "Upconverter", "Pre-Amplifiers Enabled: %s", (await device.get_pa_stg1_2_status()) ? "YES" : "NO");
                    }
                    break;
                    case "turn_preamps_off":
                    {
                        await device.set_pa_stg1_2_status(false);

                        await delay(50);

                        this.tprintln(null, "Upconverter", "Pre-Amplifiers Enabled: %s", (await device.get_pa_stg1_2_status()) ? "YES" : "NO");
                    }
                    break;
                    case "turn_pa_on":
                    {
                        await device.set_pa_stg3_status(true);

                        await delay(50);

                        this.tprintln(null, "Upconverter", "Final Amplifier Enabled: %s", (await device.get_pa_stg3_status()) ? "YES" : "NO");
                    }
                    break;
                    case "turn_pa_off":
                    {
                        await device.set_pa_stg3_status(false);

                        await delay(50);

                        this.tprintln(null, "Upconverter", "Final Amplifier Enabled: %s", (await device.get_pa_stg3_status()) ? "YES" : "NO");
                    }
                    break;
                    default:
                    {
                        throw new Error("Upconverter parameter not supported");
                    }
                    break;
                }
            }
            else if(device instanceof PABiasController)
            {
                switch(param_name)
                {
                    case "turn_tec_on":
                    {
                        let i = parseInt(argv[2]);

                        if(isNaN(i) || i < 0 || i > 3)
                            throw new Error("Invalid TEC index");

                        await device.set_tec_status(i, true);

                        await delay(500);

                        this.tprintln(null, "PA Bias Controller", "TEC #%d status: %s", i, (await device.get_tec_status(i)) ? "ON" : "OFF");
                        this.tprintln(null, "PA Bias Controller", "TEC #%d voltage: %d mV", i, await device.get_tec_voltage(i));
                    }
                    break;
                    case "turn_tec_off":
                    {
                        let i = parseInt(argv[2]);

                        if(isNaN(i) || i < 0 || i > 3)
                            throw new Error("Invalid TEC index");

                        await device.set_tec_status(i, false);

                        await delay(500);

                        this.tprintln(null, "PA Bias Controller", "TEC #%d status: %s", i, (await device.get_tec_status(i)) ? "ON" : "OFF");
                        this.tprintln(null, "PA Bias Controller", "TEC #%d voltage: %d mV", i, await device.get_tec_voltage(i));
                    }
                    break;
                    case "set_tec_voltage":
                    {
                        let i = parseInt(argv[2]);

                        if(isNaN(i) || i < 0 || i > 3)
                            throw new Error("Invalid TEC index");

                        let voltage = parseInt(argv[3]);

                        if(isNaN(voltage))
                            throw new Error("Invalid voltage");

                        await device.set_tec_voltage(i, voltage);

                        await delay(500);

                        this.tprintln(null, "PA Bias Controller", "TEC #%d status: %s", i, (await device.get_tec_status(i)) ? "ON" : "OFF");
                        this.tprintln(null, "PA Bias Controller", "TEC #%d voltage: %d mV", i, await device.get_tec_voltage(i));
                    }
                    break;
                    case "turn_pa_on":
                    {
                        let i = parseInt(argv[2]);

                        if(isNaN(i) || i < 0 || i > 1)
                            throw new Error("Invalid PA index");

                        await device.set_pa_status(i, true);

                        await delay(50);

                        let data = await device.get_pa_telemetry(i);

                        this.tprintln(null, "PA Bias Controller", "PA #%d status: %s", i, (await device.get_pa_status(i)) ? "ON" : "OFF");
                        this.tprintln(null, "PA Bias Controller", "PA #%d VGG Raw Voltage: %d mV", i, data.vgg_raw);
                        this.tprintln(null, "PA Bias Controller", "PA #%d VGG Voltage: %d mV", i, data.vgg);
                        this.tprintln(null, "PA Bias Controller", "PA #%d VDD Voltage: %d mV", i, data.vdd);
                        this.tprintln(null, "PA Bias Controller", "PA #%d VDD Current: %d mA", i, data.idd);
                        this.tprintln(null, "PA Bias Controller", "PA #%d Temperature: %d C", i, data.temperature);
                    }
                    break;
                    case "turn_pa_off":
                    {
                        let i = parseInt(argv[2]);

                        if(isNaN(i) || i < 0 || i > 1)
                            throw new Error("Invalid PA index");

                        await device.set_pa_status(i, false);

                        await delay(50);

                        let data = await device.get_pa_telemetry(i);

                        this.tprintln(null, "PA Bias Controller", "PA #%d status: %s", i, (await device.get_pa_status(i)) ? "ON" : "OFF");
                        this.tprintln(null, "PA Bias Controller", "PA #%d VGG Raw Voltage: %d mV", i, data.vgg_raw);
                        this.tprintln(null, "PA Bias Controller", "PA #%d VGG Voltage: %d mV", i, data.vgg);
                        this.tprintln(null, "PA Bias Controller", "PA #%d VDD Voltage: %d mV", i, data.vdd);
                        this.tprintln(null, "PA Bias Controller", "PA #%d VDD Current: %d mA", i, data.idd);
                        this.tprintln(null, "PA Bias Controller", "PA #%d Temperature: %d C", i, data.temperature);
                    }
                    break;
                    case "set_pa_vgg_raw":
                    {
                        let i = parseInt(argv[2]);

                        if(isNaN(i) || i < 0 || i > 1)
                            throw new Error("Invalid PA index");

                        let voltage = parseInt(argv[3]);

                        if(isNaN(voltage))
                            throw new Error("Invalid voltage");

                        await device.set_pa_vgg_raw(i, voltage);

                        await delay(500);

                        let data = await device.get_pa_telemetry(i);

                        this.tprintln(null, "PA Bias Controller", "PA #%d status: %s", i, (await device.get_pa_status(i)) ? "ON" : "OFF");
                        this.tprintln(null, "PA Bias Controller", "PA #%d VGG Raw Voltage: %d mV", i, data.vgg_raw);
                        this.tprintln(null, "PA Bias Controller", "PA #%d VGG Voltage: %d mV", i, data.vgg);
                        this.tprintln(null, "PA Bias Controller", "PA #%d VDD Voltage: %d mV", i, data.vdd);
                        this.tprintln(null, "PA Bias Controller", "PA #%d VDD Current: %d mA", i, data.idd);
                        this.tprintln(null, "PA Bias Controller", "PA #%d Temperature: %d C", i, data.temperature);
                    }
                    break;
                    default:
                    {
                        throw new Error("PA Bias Controller parameter not supported");
                    }
                    break;
                }
            }
            else if(device instanceof LNBController)
            {
                switch(param_name)
                {
                    case "turn_global_ref_on":
                    {
                        await device.set_lnb_global_reference_status(true);

                        await delay(50);

                        this.tprintln(null, "LNB Controller", "Global reference enable: %s", (await device.get_lnb_global_reference_status()) ? "ON" : "OFF");
                    }
                    break;
                    case "turn_global_ref_off":
                    {
                        await device.set_lnb_global_reference_status(false);

                        await delay(50);

                        this.tprintln(null, "LNB Controller", "Global reference enable: %s", (await device.get_lnb_global_reference_status()) ? "ON" : "OFF");
                    }
                    break;
                    case "turn_lnb_on":
                    {
                        let i = parseInt(argv[2]);

                        if(isNaN(i) || i < 0 || i > 1)
                            throw new Error("Invalid LNB index");

                        let ref_on = !!parseInt(argv[3]);

                        await device.set_lnb_reference_status(i, ref_on);
                        await device.set_lnb_bias_status(i, true);

                        await delay(500);

                        this.tprintln(null, "LNB Controller", "LNB #%d Bias enable: %s", i, (await device.get_lnb_bias_status(i)) ? "ON" : "OFF");
                        this.tprintln(null, "LNB Controller", "LNB #%d Bias status: %s", i, (await device.is_lnb_bias_power_good(i)) ? "POWER GOOD" : "POWER NOT GOOD");
                        this.tprintln(null, "LNB Controller", "LNB #%d Set Bias Voltage: %d mV", i, await device.get_lnb_bias_voltage_set(i));
                        this.tprintln(null, "LNB Controller", "LNB #%d Bias Voltage: %d mV", i, await device.get_lnb_bias_voltage(i));
                        this.tprintln(null, "LNB Controller", "LNB #%d Reference enable: %s", i, (await device.get_lnb_reference_status(i)) ? "ON" : "OFF");
                        this.tprintln(null, "LNB Controller", "LNB #%d Reference Frequency: %d Hz", i, await device.get_lnb_reference_frequency(i));
                    }
                    break;
                    case "turn_lnb_off":
                    {
                        let i = parseInt(argv[2]);

                        if(isNaN(i) || i < 0 || i > 1)
                            throw new Error("Invalid LNB index");

                        await device.set_lnb_reference_status(i, false);
                        await device.set_lnb_bias_status(i, false);

                        await delay(500);

                        this.tprintln(null, "LNB Controller", "LNB #%d Bias enable: %s", i, (await device.get_lnb_bias_status(i)) ? "ON" : "OFF");
                        this.tprintln(null, "LNB Controller", "LNB #%d Bias status: %s", i, (await device.is_lnb_bias_power_good(i)) ? "POWER GOOD" : "POWER NOT GOOD");
                        this.tprintln(null, "LNB Controller", "LNB #%d Set Bias Voltage: %d mV", i, await device.get_lnb_bias_voltage_set(i));
                        this.tprintln(null, "LNB Controller", "LNB #%d Bias Voltage: %d mV", i, await device.get_lnb_bias_voltage(i));
                        this.tprintln(null, "LNB Controller", "LNB #%d Reference enable: %s", i, (await device.get_lnb_reference_status(i)) ? "ON" : "OFF");
                        this.tprintln(null, "LNB Controller", "LNB #%d Reference Frequency: %d Hz", i, await device.get_lnb_reference_frequency(i));
                    }
                    break;
                    case "set_lnb_voltage":
                    {
                        let i = parseInt(argv[2]);

                        if(isNaN(i) || i < 0 || i > 1)
                            throw new Error("Invalid LNB index");

                        let voltage = parseInt(argv[3]);

                        if(isNaN(voltage))
                            throw new Error("Invalid voltage");

                        await device.set_lnb_bias_voltage(i, voltage);

                        await delay(500);

                        this.tprintln(null, "LNB Controller", "LNB #%d Bias enable: %s", i, (await device.get_lnb_bias_status(i)) ? "ON" : "OFF");
                        this.tprintln(null, "LNB Controller", "LNB #%d Bias status: %s", i, (await device.is_lnb_bias_power_good(i)) ? "POWER GOOD" : "POWER NOT GOOD");
                        this.tprintln(null, "LNB Controller", "LNB #%d Set Bias Voltage: %d mV", i, await device.get_lnb_bias_voltage_set(i));
                        this.tprintln(null, "LNB Controller", "LNB #%d Bias Voltage: %d mV", i, await device.get_lnb_bias_voltage(i));
                    }
                    break;
                    case "set_lnb_ref_frequency":
                    {
                        let i = parseInt(argv[2]);

                        if(isNaN(i) || i < 0 || i > 1)
                            throw new Error("Invalid LNB index");

                        let freq = parseInt(argv[3]);

                        if(isNaN(freq))
                            throw new Error("Invalid frequency");

                        await device.set_lnb_reference_frequency(i, freq);

                        await delay(500);

                        this.tprintln(null, "LNB Controller", "LNB #%d Reference enable: %s", i, (await device.get_lnb_reference_status(i)) ? "ON" : "OFF");
                        this.tprintln(null, "LNB Controller", "LNB #%d Reference Frequency: %d Hz", i, await device.get_lnb_reference_frequency(i));
                    }
                    break;
                    default:
                    {
                        throw new Error("LNB Controller parameter not supported");
                    }
                    break;
                }
            }
            else if(device instanceof DS18B20)
            {
                switch(param_name)
                {
                    default:
                    {
                        throw new Error("DS18B20 parameter not supported");
                    }
                    break;
                }
            }
            else if(device instanceof BME280)
            {
                switch(param_name)
                {
                    default:
                    {
                        throw new Error("BME280 parameter not supported");
                    }
                    break;
                }
            }
            else if(device instanceof OAQ)
            {
                switch(param_name)
                {
                    default:
                    {
                        throw new Error("OAQ parameter not supported");
                    }
                    break;
                }
            }
            else if(device instanceof SI1133)
            {
                switch(param_name)
                {
                    default:
                    {
                        throw new Error("SI1133 parameter not supported");
                    }
                    break;
                }
            }
            else if(device instanceof MCP3221)
            {
                switch(param_name)
                {
                    default:
                    {
                        throw new Error("MCP3221 parameter not supported");
                    }
                    break;
                }
            }
            else if(device instanceof LTC5597)
            {
                switch(param_name)
                {
                    default:
                    {
                        throw new Error("LTC5597 parameter not supported");
                    }
                    break;
                }
            }
            else if(device instanceof LTC4151)
            {
                switch(param_name)
                {
                    default:
                    {
                        throw new Error("LTC4151 parameter not supported");
                    }
                    break;
                }
            }
            else if(device instanceof F2915)
            {
                switch(param_name)
                {
                    case "rf_path":
                    {
                        let path = parseInt(argv[2]);

                        await device.set_rf_path(path);

                        this.tprintln(null, "F2915", "Selected RF path: %d", await device.get_rf_path());
                    }
                    break;
                    default:
                    {
                        throw new Error("F2915 parameter not supported");
                    }
                    break;
                }
            }
            else
            {
                throw new Error("Device not supported");
            }

            return true;
        },
        function (line)
        {
            const param_names = [];

            for(const device_name in devices)
            {
                const device = devices[device_name];

                let device_param_names = [];

                if(device instanceof HPPSU)
                    device_param_names = ["clear_peak_input_current", "clear_peak_input_power", "clear_peak_output_current", "fan_speed", "clear_on_time_and_energy", "turn_on", "turn_off"];
                else if(device instanceof RelayController)
                    device_param_names = ["turn_relay_on", "turn_relay_off", "set_relay_voltage"];
                else if(device instanceof I2CBuffer)
                    device_param_names = ["turn_bus_on", "turn_bus_off"];
                else if(device instanceof Upconverter)
                    device_param_names = ["set_attenuation", "mute_lo", "unmute_lo", "set_lo_freq", "turn_mixer_on", "turn_mixer_off", "turn_preamps_on", "turn_preamps_off", "turn_pa_on", "turn_pa_off"];
                else if(device instanceof PABiasController)
                    device_param_names = ["turn_tec_on", "turn_tec_off", "set_tec_voltage", "turn_pa_on", "turn_pa_off", "set_pa_vgg_raw"];
                else if(device instanceof LNBController)
                    device_param_names = ["turn_global_ref_on", "turn_global_ref_off", "turn_lnb_on", "turn_lnb_off", "set_lnb_voltage", "set_lnb_ref_frequency"];
                else if(device instanceof DS18B20)
                    device_param_names = [];
                else if(device instanceof BME280)
                    device_param_names = [];
                else if(device instanceof OAQ)
                    device_param_names = [];
                else if(device instanceof SI1133)
                    device_param_names = [];
                else if(device instanceof MCP3221)
                    device_param_names = [];
                else if(device instanceof LTC5597)
                    device_param_names = [];
                else if(device instanceof LTC4151)
                    device_param_names = [];
                else if(device instanceof F2915)
                    device_param_names = ["rf_path"];

                for(const param of device_param_names)
                    param_names.push(device_name + "." + param);
            }

            const hits = param_names.filter(
                function (c)
                {
                    return c.startsWith(line);
                }
            );

            return hits.length ? hits : param_names;
        }
    );
    ssh_server_add_command(
        "lswbsig",
        "Prints the latest signals detected on the Wideband Transponder",
        async function (argv)
        {
            if(wb_signals.noise_power !== undefined)
                this.tprintln("grey", null, "Noise floor: %d dB", wb_signals.noise_power.toFixed(2));

            if(wb_signals.beacon)
            {
                const signal = wb_signals.beacon;

                this.tprintln("magenta", null, "Beacon:");
                this.tprintln("magenta", null, "  Center frequency: %d MHz", signal.full_center_freq.toFixed(3));
                this.tprintln("magenta", null, "  Full bandwidth: %d MHz", signal.full_bandwidth.toFixed(3));
                this.tprintln("magenta", null, "  Full power: %d dB", signal.full_power.toFixed(2));
                this.tprintln("magenta", null, "  Used bandwidth: %d MHz", signal.used_bandwidth.toFixed(3));
                this.tprintln("magenta", null, "  Used power: %d dB", signal.used_power.toFixed(2));
                this.tprintln("magenta", null, "  Symbol rate: %d ksps", signal.symbolrate.toFixed(0));
                this.tprintln("magenta", null, "  SNR: %d dB", signal.snr.toFixed(2));
            }
            else
            {
                this.tprintln("red", null, "No beacon found!");

                return false;
            }

            if(!wb_signals.signals.length)
                this.tprintln(null, null, "No signals found!");

            for(const signal of wb_signals.signals)
            {
                let color = "brightGreen";

                if(signal.out_of_band)
                    color = "yellow";
                if(signal.over_powered)
                    color = "red";

                this.tprintln(color, null, "Signal:");
                this.tprintln(color, null, "  Center frequency: %d MHz", signal.full_center_freq.toFixed(3));
                this.tprintln(color, null, "  Full bandwidth: %d MHz", signal.full_bandwidth.toFixed(3));
                this.tprintln(color, null, "  Full power: %d dB", signal.full_power.toFixed(2));
                this.tprintln(color, null, "  Used bandwidth: %d MHz", signal.used_bandwidth.toFixed(3));
                this.tprintln(color, null, "  Used power: %d dB", signal.used_power.toFixed(2));
                this.tprintln(color, null, "  Symbol rate: %d ksps", signal.symbolrate.toFixed(0));
                this.tprintln(color, null, "  SNR: %d dB", signal.snr.toFixed(2));
                this.tprintln(color, null, "  SBR: %d dB", signal.sbr.toFixed(2));
            }

            return true;
        }
    );

    // Listen
    return new Promise(
        function (resolve, reject)
        {
            ssh_server.listen(
                2222,
                "0.0.0.0",
                function (e)
                {
                    if(e)
                        return reject(e);

                    cl.tprintln("grey", "SSH", "Listening on port %d!", this.address().port);

                    return resolve();
                }
            );
        }
    );
}
function ssh_server_add_user(username, password, keys)
{
    if(typeof(username) != "string" || !username.length)
        throw new Error("Invalid username");

    if(keys !== undefined && !Array.isArray(keys))
        keys = [keys];

    let user = {
        username: Buffer.from(username),
    };

    if(typeof(password) == "string" && password.length)
        user.password = Buffer.from(password);

    if(Array.isArray(keys))
    {
        user.keys = [];

        for(const key of keys)
        {
            if(!key.length)
                continue;

            let parsed_key = SSH2.utils.parseKey(Buffer.isBuffer(key) ? key : Buffer.from(key));

            if(parsed_key instanceof Error)
                throw parsed_key;

            user.keys.push(parsed_key);
        }
    }

    ssh_allowed_users.push(user);
}
function ssh_server_add_command(cmd, description, handler, completer)
{
    if(typeof(cmd) != "string" || !cmd.length)
        throw new Error("Invalid command string");

    if(description && typeof(description) != "string")
        throw new Error("Invalid description string");

    if(typeof(handler) != "function")
        throw new Error("Invalid command handler");

    for(let i = 0; i < cmd.length; i++)
    {
        let c = cmd.charCodeAt(i);

        if(!(c >= 0x30 && c <= 0x39) && !(c >= 0x41 && c <= 0x5A) && !(c >= 0x61 && c <= 0x7A) && c != 0x5F)
            throw new Error("Invalid command string");
    }

    if(typeof(ssh_commands[cmd]) == "object")
        throw new Error("Command already exists");

    ssh_commands[cmd] = {
        description: description || "No description available",
        handler: handler,
        completer: undefined
    };

    if(typeof(completer) == "function")
        ssh_commands[cmd].completer = completer;
}
function ssh_server_complete_command(line)
{
    const tokens = line.split(" ");
    const command_names = Object.keys(ssh_commands);
    let hits = [];

    if(tokens.length > 1)
    {
        let cmd_name = tokens[0];
        let cmd = ssh_commands[cmd_name];

        if(cmd && typeof(cmd.completer) == "function")
            hits = cmd.completer(tokens.slice(1).join(" "));

        let checkpos = line.length - cmd_name.length - 1;
        let char = "";
        let equal = true;

        for(let i = 0; i < hits.length; i++)
        {
            if(!char)
                char = hits[i][checkpos];

            if(hits[i][checkpos] !== char)
            {
                equal = false;

                break;
            }
        }

        if(equal)
        {
            for(let i = 0; i < hits.length; i++)
                hits[i] = cmd_name + " " + hits[i];
        }
    }
    else
    {
        hits = command_names.filter(
            function (c)
            {
                return c.startsWith(line);
            }
        );
    }

    if(hits.length == 1 && line == hits[0])
        hits[0] += " ";

    return [hits.length ? hits : command_names, line];
}
async function ssh_server_process_command_string(str)
{
    if(typeof(str) != "string")
        return;

    cl.tprintln("blue", "SSH", "Processing command string '%s' from client at %s...", str, this.stream.session.client.ip);

    let argv = ShellQuote.parse(str);
    let current_argv = [];

    for(const arg of argv)
    {
        switch(typeof(arg))
        {
            case "string":
            {
                current_argv.push(arg);
            }
            break;
            case "object":
            {
                if(typeof(arg.op) != "string")
                    return;

                switch(arg.op)
                {
                    case ";": // Process the next regardless if the current succeeds
                    {
                        await ssh_server_process_command.bind(this)(current_argv);
                        current_argv = [];
                    }
                    break;
                    case "&&": // Process the next only if the current succeeds
                    {
                        if(!(await ssh_server_process_command.bind(this)(current_argv)))
                            return;

                        current_argv = [];
                    }
                    break;
                    case "||": // Process the next only if the current does not succeed
                    {
                        if(await ssh_server_process_command.bind(this)(current_argv))
                            return;

                        current_argv = [];
                    }
                    break;
                    default:
                    {
                        this.println("red", null, "Operator '%s' not supported!", arg.op);
                        cl.tprintln("red", "SSH", "Error processing operator '%s' from client at %s: Operator '%s' not supported!", arg.op, this.stream.session.client.ip, arg.op);

                        return;
                    }
                    break;
                }
            }
            break;
            default:
            {
                this.println("red", null, "Invalid argument!");
                cl.tprintln("red", "SSH", "Error processing operator '%s' from client at %s: Invalid argument!", arg.op, this.stream.session.client.ip);

                return;
            }
            break;
        }
    }

    await ssh_server_process_command.bind(this)(current_argv);
}
async function ssh_server_process_command(argv)
{
    if(!Array.isArray(argv))
        return false;

    if(!argv)
        return false;

    if(!argv.length)
        return true;

    cl.tprintln("blue", "SSH", "Processing command '%s' from client at %s...", ShellQuote.quote(argv), this.stream.session.client.ip);

    let cmd_name = argv[0];
    let cmd_handler = ssh_commands[cmd_name] ? ssh_commands[cmd_name].handler : null;

    if(typeof(cmd_handler) != "function")
    {
        this.println("red", null, "Command '%s' not found!", cmd_name);
        cl.tprintln("red", "SSH", "Error processing command '%s' from client at %s: Command '%s' not found!", ShellQuote.quote(argv), this.stream.session.client.ip, cmd_name);

        return false;
    }

    cmd_handler = cmd_handler.bind(this);

    let success = false;

    try
    {
        success = await cmd_handler(argv);

        cl.tprintln("green", "SSH", "Processed command '%s' from client at %s!", ShellQuote.quote(argv), this.stream.session.client.ip);
    }
    catch(e)
    {
        success = false;

        this.println("red", null, e);
        cl.tprintln("red", "SSH", "Error processing command '%s' from client at %s: " + e, ShellQuote.quote(argv), this.stream.session.client.ip);
    }

    return success;
}
function ssh_server_connection_handler(client, info)
{
    client.ip = info.ip;

    cl.tprintln("magenta", "SSH", "New client connected! IP: %s (%s)!", client.ip, info.header.identRaw);

    client.on("authentication", ssh_server_client_auth_handler);
    client.on("ready", ssh_server_client_ready_handler);

    client.on(
        "end",
        function()
        {
            cl.tprintln("magenta", "SSH", "Client at %s disconnected!", this.ip);
        }
    );
}
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
